eez-open/modular-psu/DIB/EEZ DIB v1.2 pin mappings.pdf

EEZ DIB (DIY Instrumentation Bus) pin mappings v1.2 (28.12.2020)

A B
1 | GND | | 2 | GND
3 | UART_RX | I | 4 | UART_TX | O
5 | +VAUX | I/O | 6 | NRESET | O
7 | +3V3 | O | 8 | NFAULT | I
9 | SPI3_IRQ | I #3 IRQ | 10 | SYNC | O
11 | SPI3_CSA | O | 12 | SSCL | O
13 | SPI3_CSB | O | 14 | SSDA | I/O
15 | GND | | 16 | GND
17 | SPI3_SCLK | O #3 SPI CLK | 18 | SPI3_MISO | I #3 MISO
19 | SPI2_IRQ | I #2 IRQ | 20 | SPI3_MOSI | O #3 MOSI
21 | SPI2_CSB | O | 22 | SPI2_CSA | O
23 | SPI2_SCLK | O #2 SPI CLK | 24 | SPI2_MISO | I #2 MISO
25 | SPI1_IRQ | I #1 IRQ | 26 | SPI2_MOSI | O #2 MOSI
27 | SPI1_CSB | O | 28 | SPI1_CSA | O
29 | GND | | 30 | SPI2_CSC | O
31 | SPI1_MISO | I #1 MISO | 32 | SPI1_SCLK | O #1 SPI CLK
33 | SPI1_MOSI | O #1 MOSI | 34 | SPI3_CSC | O
35 | +5V | I | 36 | +5V | I
37 | +12V | I | 38 | +12V | I
39 | GND | | 40 | GND

A B
1 | +3V3 | I | 2 | +VAUX | I
3 | NFAULT | I/O | 4 | NRESET | I
5 | SSCL | I | 6 | SYNC | I
7 | GND | | 8 | SSDA | I/O
9 | CSA | I | 10 | IRQ | O Module IRQ
11 | GND | | 12 | CSB | I
13 | SCLK | I Module SPI CLK | 14 | MISO | O Module MISO
15 | MOSI | I Module MOSI | 16 | GND
17 | A0 | I | 18 | A2 | I
19 | A1 | I | 20 | GND
21 | +12V | I | 22 | +12V | I
23 | +5V | I | 24 | +5V | I
25 | GND | | 26 | BOOT | I
27 | UART_RX** | O | 28 | UART_TX** | I

A B
1 | PE | | 2 | N.C. | O N.C.
3 | +12V | O | 4 | +12V | O
5 | +5V | O | 6 | +5V | O
7 | GND | | 8 | GND
9 | GND | | 10 | +VAUX | I/O
11 | PWR_SSTART | I | 12 | PWR_DIRECT | I
13 | SSCL | I | 14 | SSDA | I/O
15 | NFAULT | I/O | 16 | +3V3 | I

A B
1 | IN+ | I | 2 | IN+ | I
3 | IN+ | I | 4 | IN+ | I
5 | IN+ | I | 6 | OUT+ | O
7 | OUT+ | O | 8 | OUT+ | O
9 | OUT+ | O | 10 | OUT+ | O
11 | OUT- | O | 12 | OUT- | O
13 | OUT- | O | 14 | OUT- | O
15 | OUT- | O | 16 | IN- | I
17 | IN- | I | 18 | IN- | I
19 | IN- | I | 20 | IN- | I
MCU module (2 x 20-pin) | Status: Mandatory
Dir | Dir
Shared UART RX | Shared UART TX
Backup DC power | Master reset (active low)
DC power | Fault (active low)
| Sync output
#3 Chip select A | Shared I²C SCL

#3 Chip select B (#5 IRQ) | Shared I²C SDA

#2 Chip select B (#4 IRQ) | #2 Chip select A

#1 Chip select B | #1 Chip select A

| #2 Chip select C
| #3 Chip select C
DC power | DC power
DC power | DC power
Peripheral modules (2 x 14-pin) | Status: Mandatory
Dir | Dir
DC power | Backup DC power
Fault (active low) | Module reset (active low)
Shared I²C SCL | Sync input
| Shared I²C SDA
Module Chip select A
| Module Chip select B

I

2C Address 0 | I 2C Address 2
I

2C Address 1
DC power | DC power
DC power | DC power
| Module bootloader select
| Status: Optional*
Shared UART RX | Shared UART TX
AUX PS module (2 x 8-pin) | Status: Recommended
Dir | Dir
DC power | DC power
DC power | DC power
| Backup DC power
AC soft-start | AC power on
Shared I²C SCL | Shared I²C SDA
Fault (active low) | DC power
Power source module (2 x 10-pin) | Status: Optional
Dir | Dir
Power positive input | Power positive input
Power positive input | Power positive input
Power positive input | Power positive output
Power positive output | Power positive output
Power positive output | Power positive output
Power negative output | Power negative output
Power negative output | Power negative output
Power negative output | Power negative input
Power negative input | Power negative input
Power negative input | Power negative input

*) The first 26-pin of peripheral module connector is mandatory and last two pin are optional. New versions of DIB specification could introduce even more features but that will require also introduction of larger MCU connector or additional connector for the MCU
**) Connect module UART_RX to master MCU UART_TX and module UART_TX to master MCU UART_RX

EEZ DIB (DIY Instrumentation Bus) pin mappings v1.2 (28.12.2020)

A B
1 | | I | 2 | | I
3 | AIN- | O | 4 | AIN+ | O
5 | | I | 6 | | I
7 | ID0 | O ADIB module ID0 | 8 | ID2 | O ADIB module ID2
9 | ID1 | O ADIB module ID1 | 10 | | I

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
| ADIB (2 x 5-pin) | | Status: Optional
Dir | Dir
Guard- | AIN- guard | Guard+ | Power positive input
| Analog input- | | Analog Input+
Guard- | AIN- guard | Guard+ | Power positive output
| | ID_Gnd | Master ADIB Gnd
| ADIB module ID assignment
Module name
EEZ DIB SMX46 (https://www.envox.hr/eez/eez-bench-box-3/eez-dib-smx46-switch-matrix-module.html) | Switch matrix module
EEZ MUX14D (https://www.envox.hr/eez/eez-bench-box-3/dib-mux14d-multiplexer-module.html) | 2-wire dual 7:1 (14:1) Multiplexer
n/a
n/a
n/a
n/a
n/a
n/a
