eez-open/modular-psu/dcp405/Front panel/DCP405 front panel.pdf

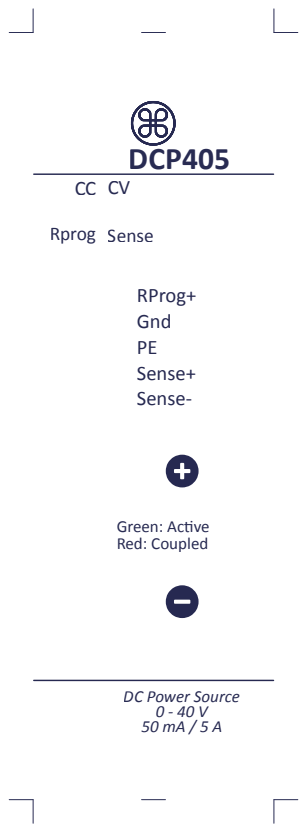
[picture p124: page 1]
RProg+ Gnd PE Sense+ Sense-; Rprog Sense; DC Power Source 0 - 40 V 50 mA / 5 A; DCP405

Green: Acve
Red: Coupled
