eez-open/modular-psu/dcp405/Front panel/DCP405B front panel.pdf

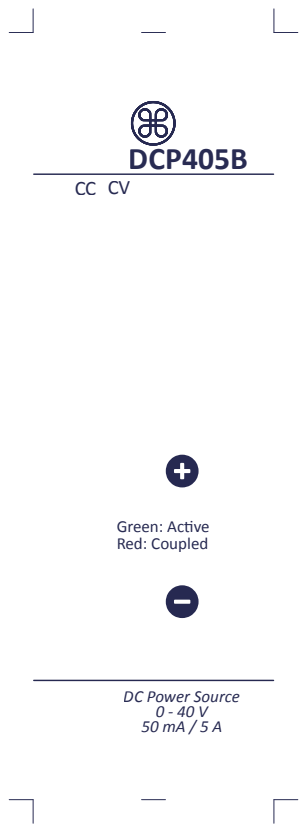
[picture p125: page 1]
DC Power Source 0 - 40 V 50 mA / 5 A; DCP405B

Green: Acve Red: Coupled
