eez-open/modular-psu/aux-ps/Images/AUX PS r3B7 3D preview.png

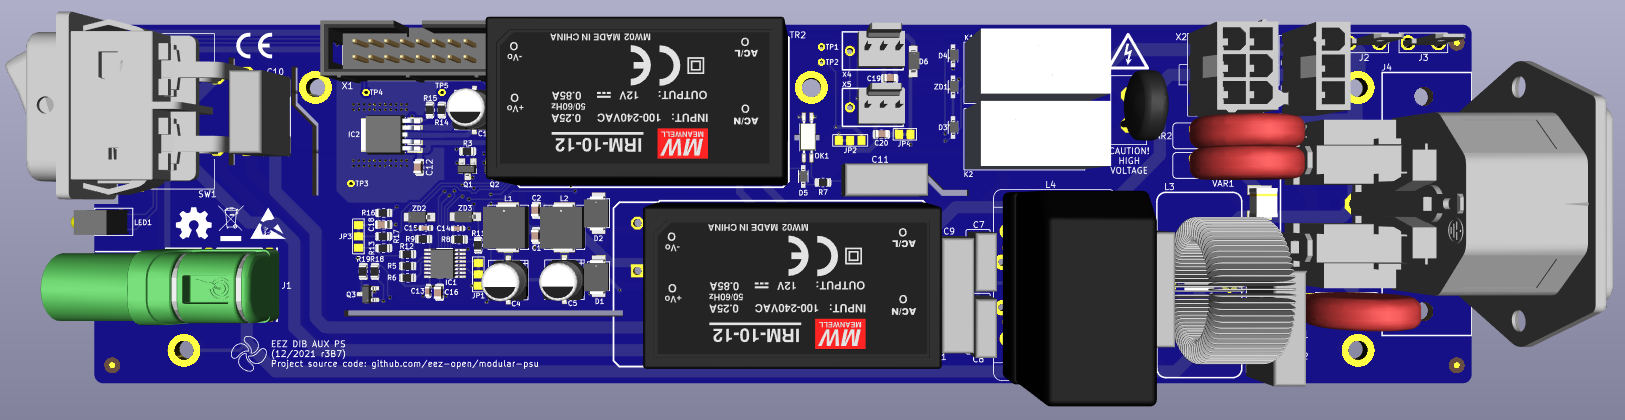
aux-ps/Images/AUX PS r3B7 3D preview.png
