eez-open/modular-psu/bp3c/EEZ DIB BP3C r2B3 Sheet2of2.png

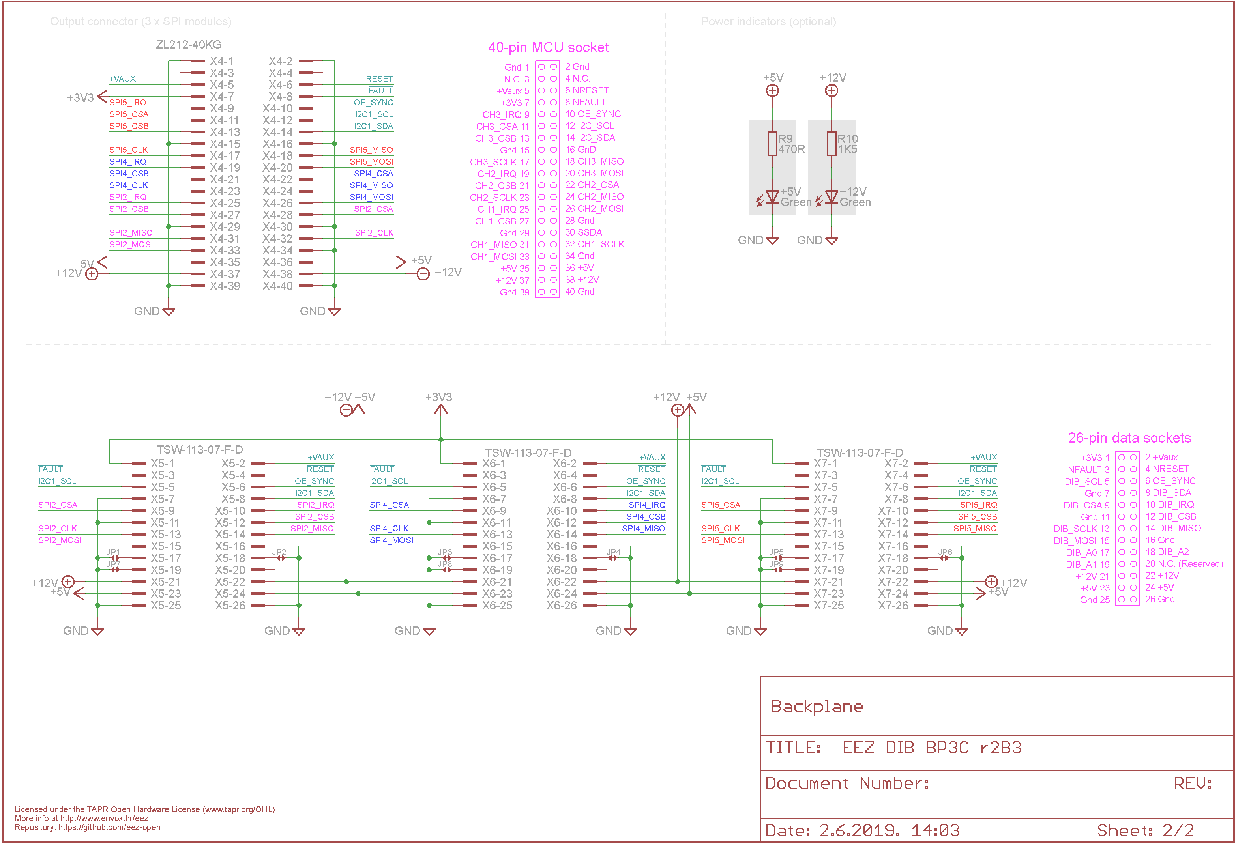
bp3c/EEZ DIB BP3C r2B3 Sheet2of2.png
