eez-open/modular-psu/bp3c/Images/BP3C r3B3 3D preview.png

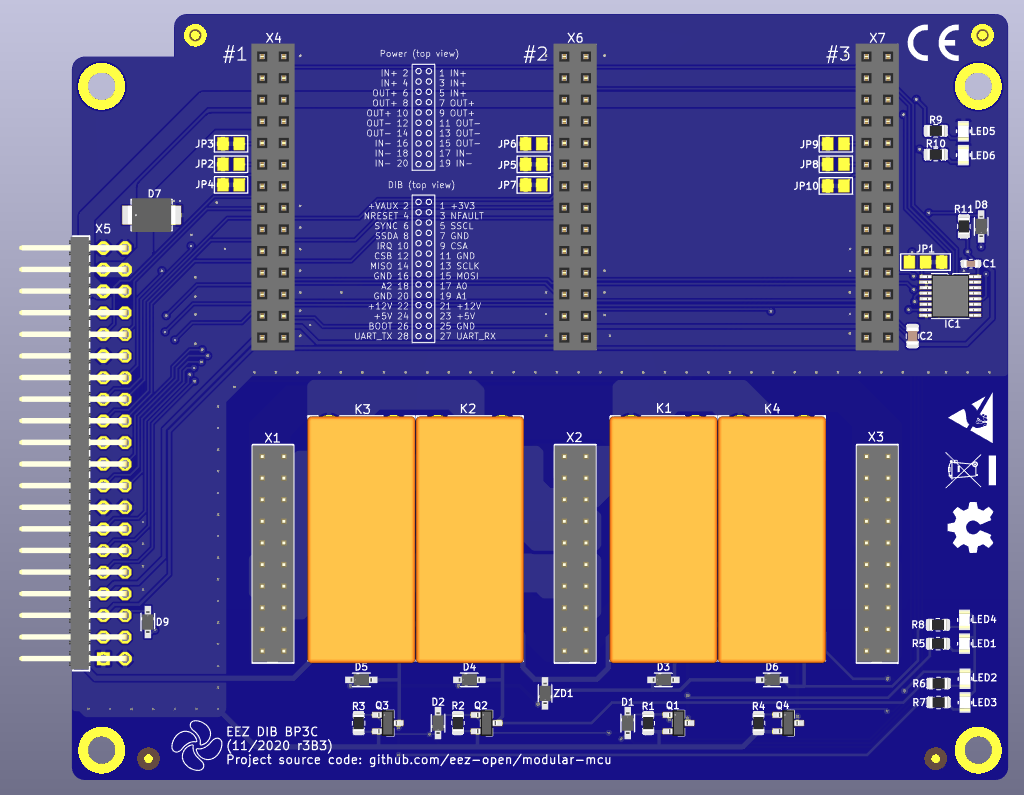
bp3c/Images/BP3C r3B3 3D preview.png
