eez-open/modular-psu/dcm220/Images/EEZ_DIB_DCM220_PCB_bottom.png

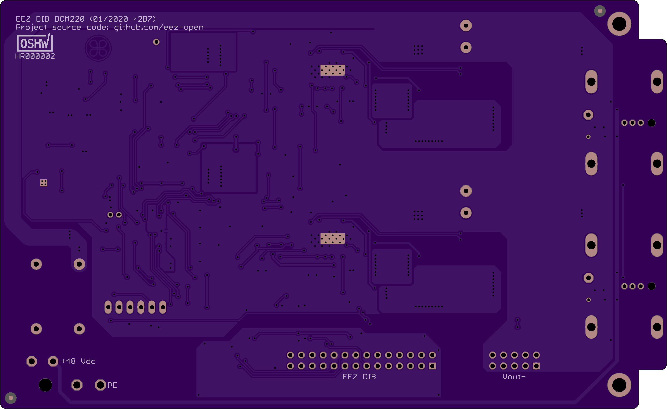
dcm220/Images/EEZ_DIB_DCM220_PCB_bottom.png
