eez-open/modular-psu/dcp405/EEZ DIB DCP405 r3B3 Sheet4of6.png

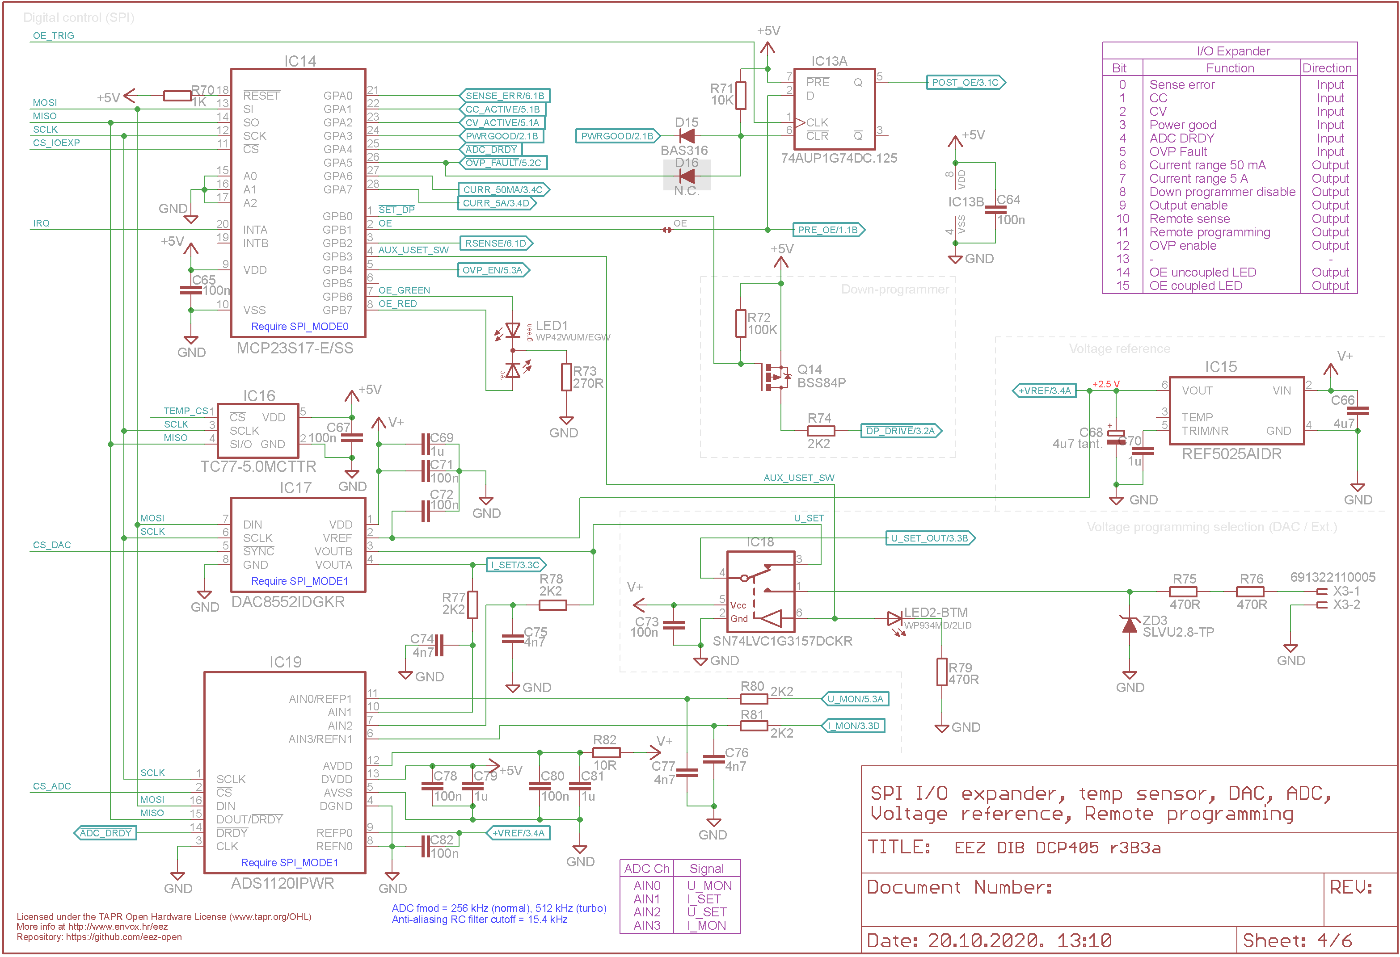
dcp405/EEZ DIB DCP405 r3B3 Sheet4of6.png
