eez-open/modular-psu/dcp405/Front panel/DCP405B front panel.png

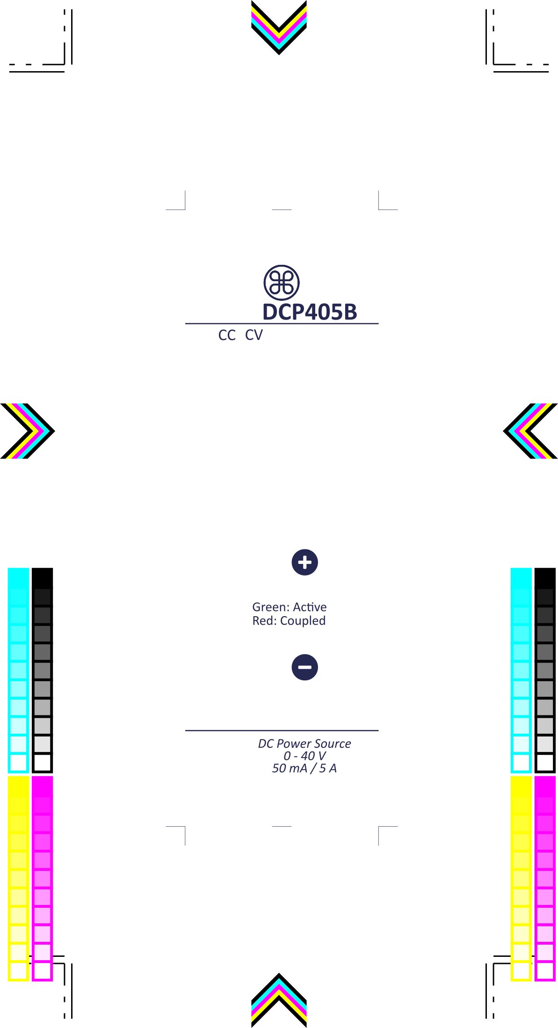
dcp405/Front panel/DCP405B front panel.png
