eez-open/modular-psu/dcp405/Images/EEZ_DIB_DCP405_PCB_bottom.png

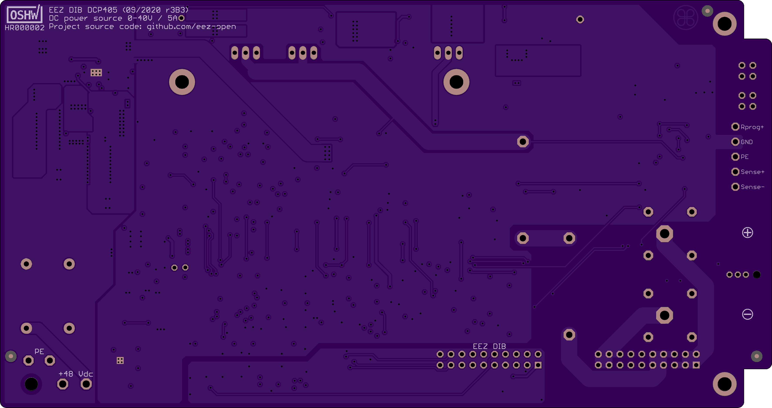
dcp405/Images/EEZ_DIB_DCP405_PCB_bottom.png
