eez-open/modular-psu/dcp405/Images/EEZ_DIB_DCP405_PCB_top.png

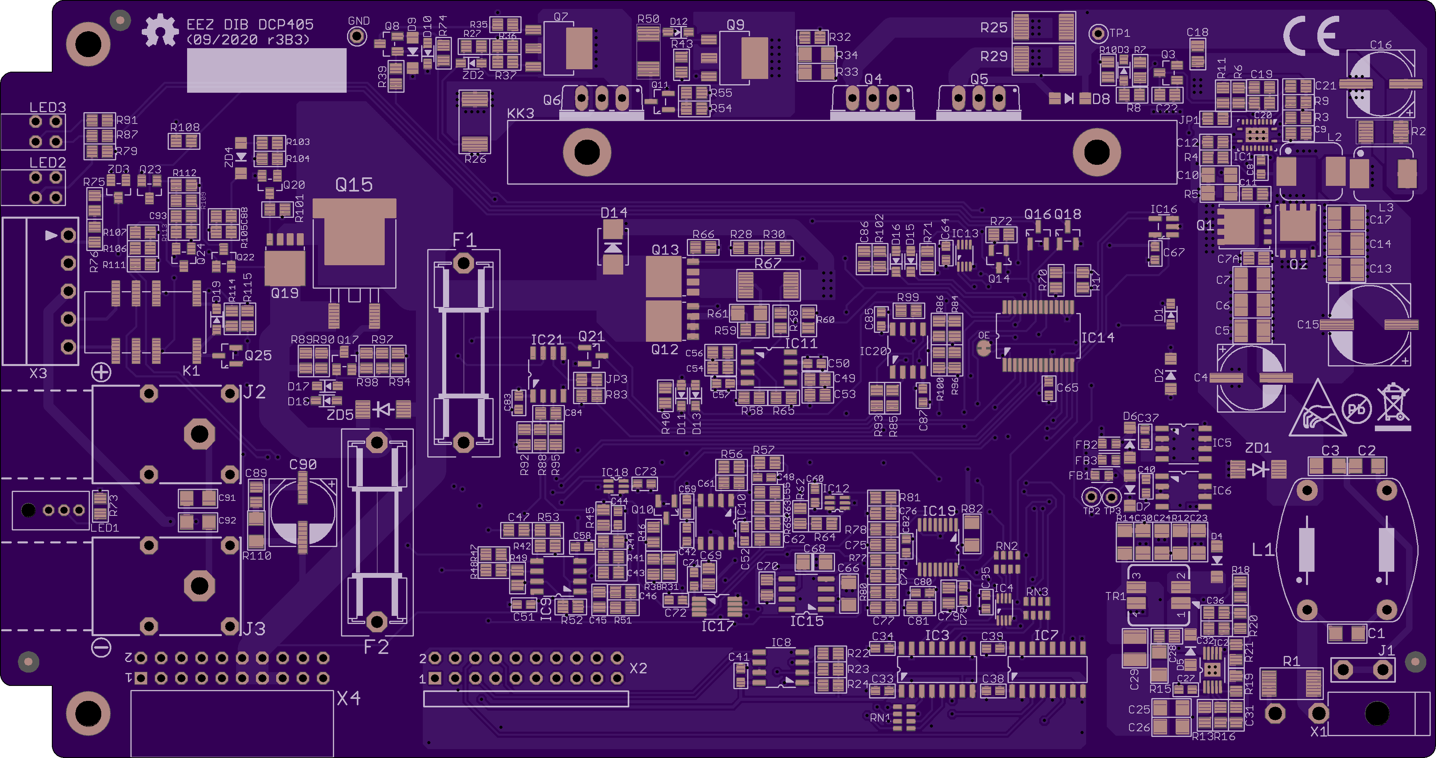
dcp405/Images/EEZ_DIB_DCP405_PCB_top.png
