eez-open/modular-psu/dcp405/Spice/EEZ DIB DCP405 r2B6.png

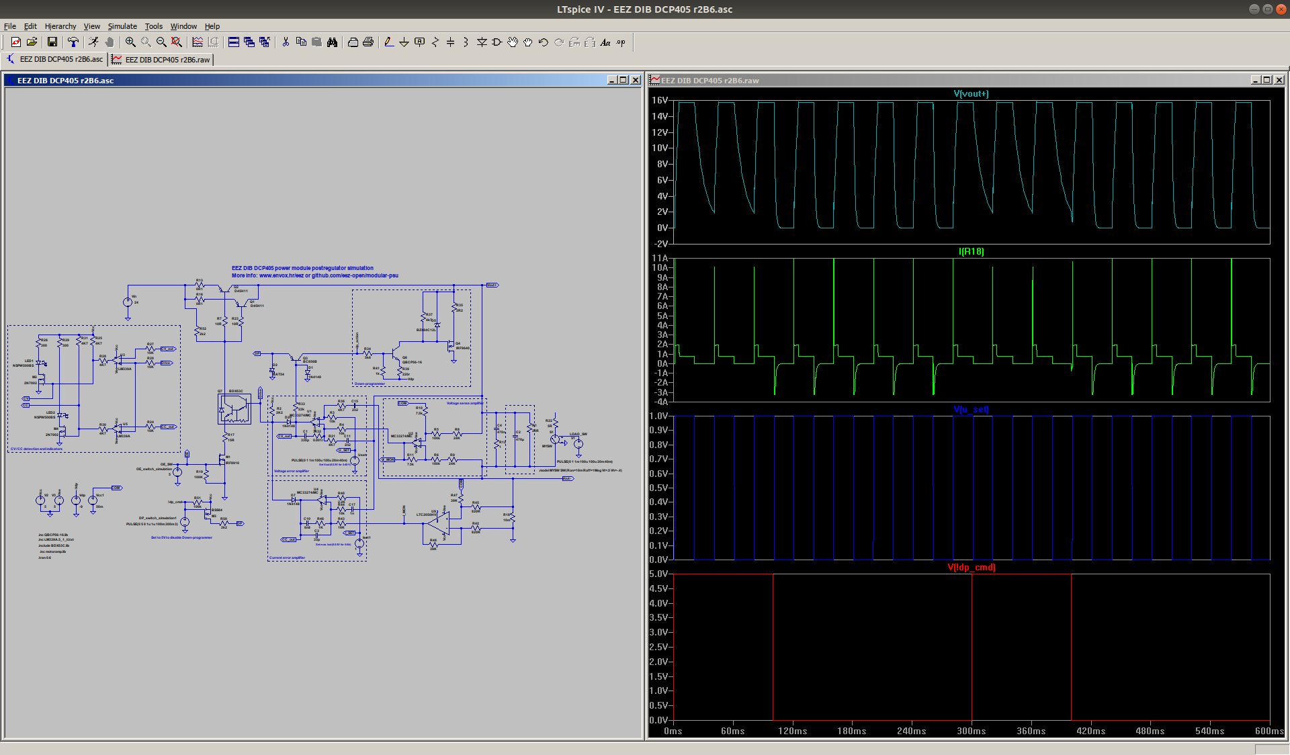
dcp405/Spice/EEZ DIB DCP405 r2B6.png
