eez-open/modular-psu/dcp505/EEZ DIB DCP505 r1B3 Sheet5of6.png

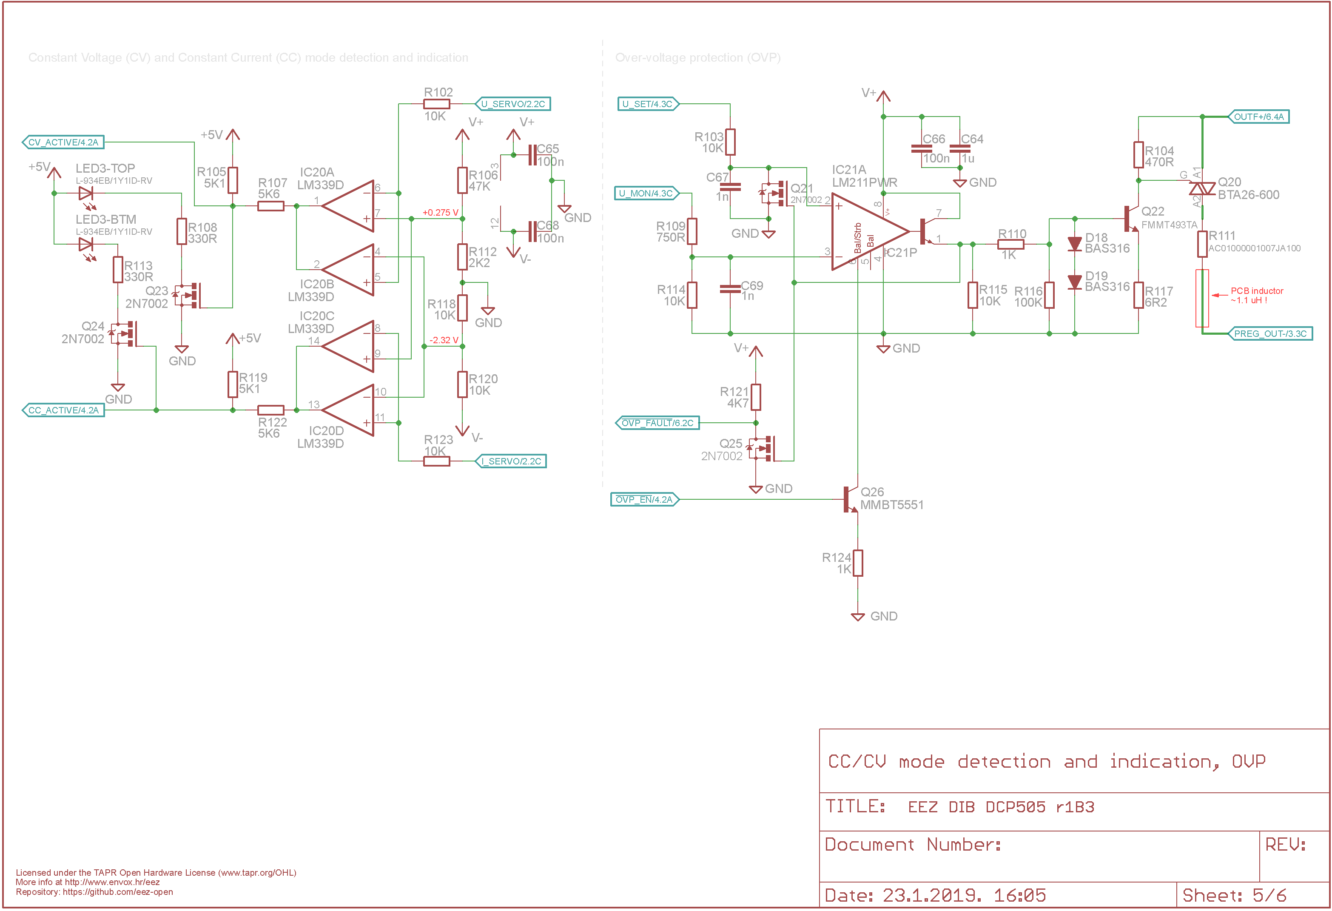
dcp505/EEZ DIB DCP505 r1B3 Sheet5of6.png
