eez-open/modular-psu/dcp505/Images/PCB inductor calculation.png

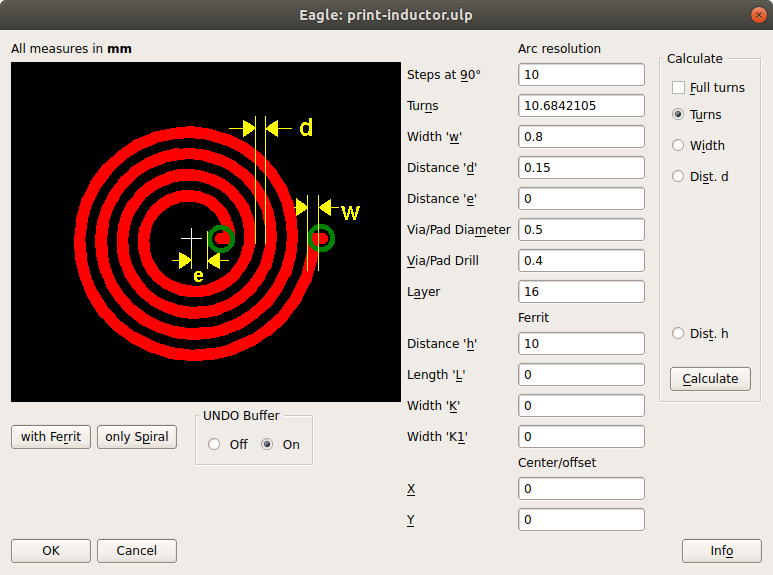
dcp505/Images/PCB inductor calculation.png
