eez-open/modular-psu/dcp505/Spice/OVP/OVP max current simulation.png

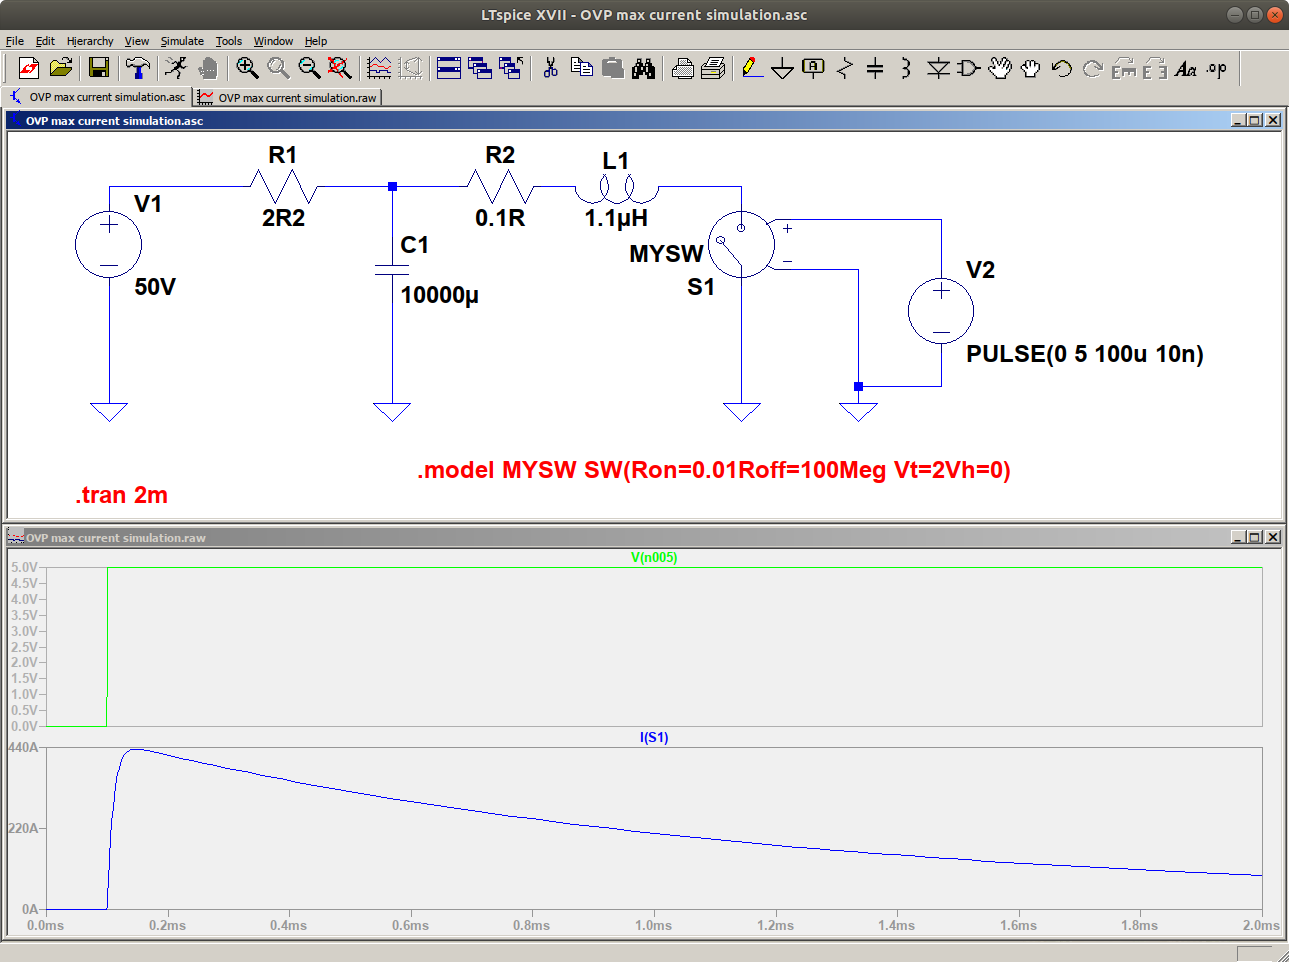
dcp505/Spice/OVP/OVP max current simulation.png
