eez-open/modular-psu/DIB/EEZ DIB v1.0 backplane dimensions.png

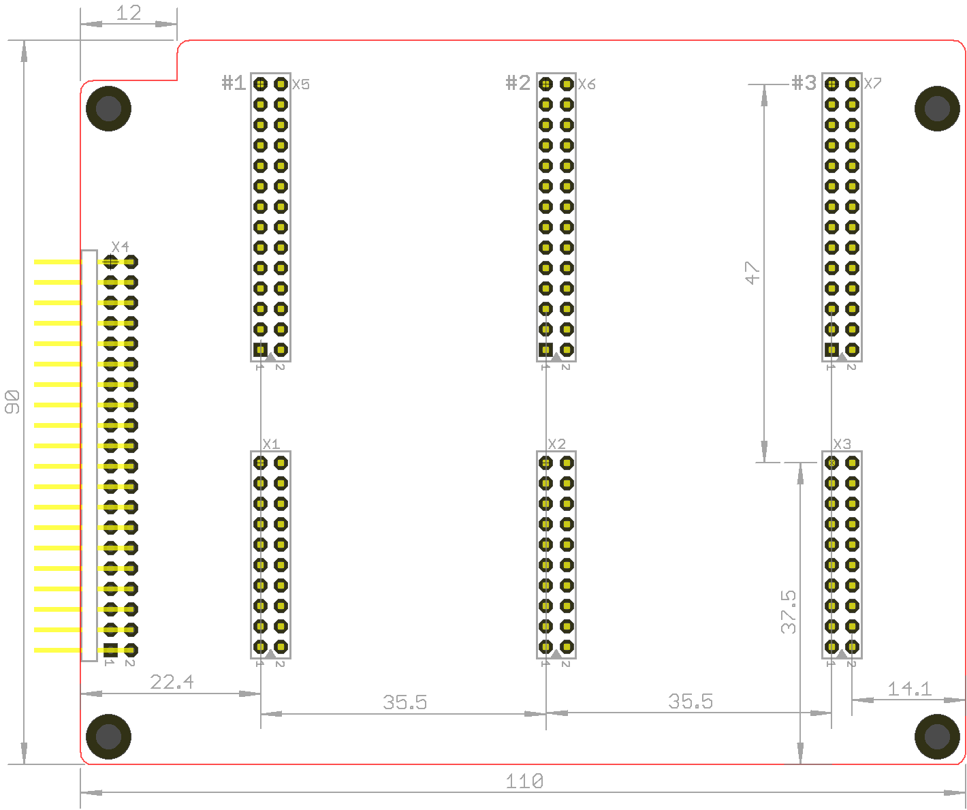
DIB/EEZ DIB v1.0 backplane dimensions.png
