eez-open/modular-psu/enclosure/BB3 chassis Mean Well support 2.0.png

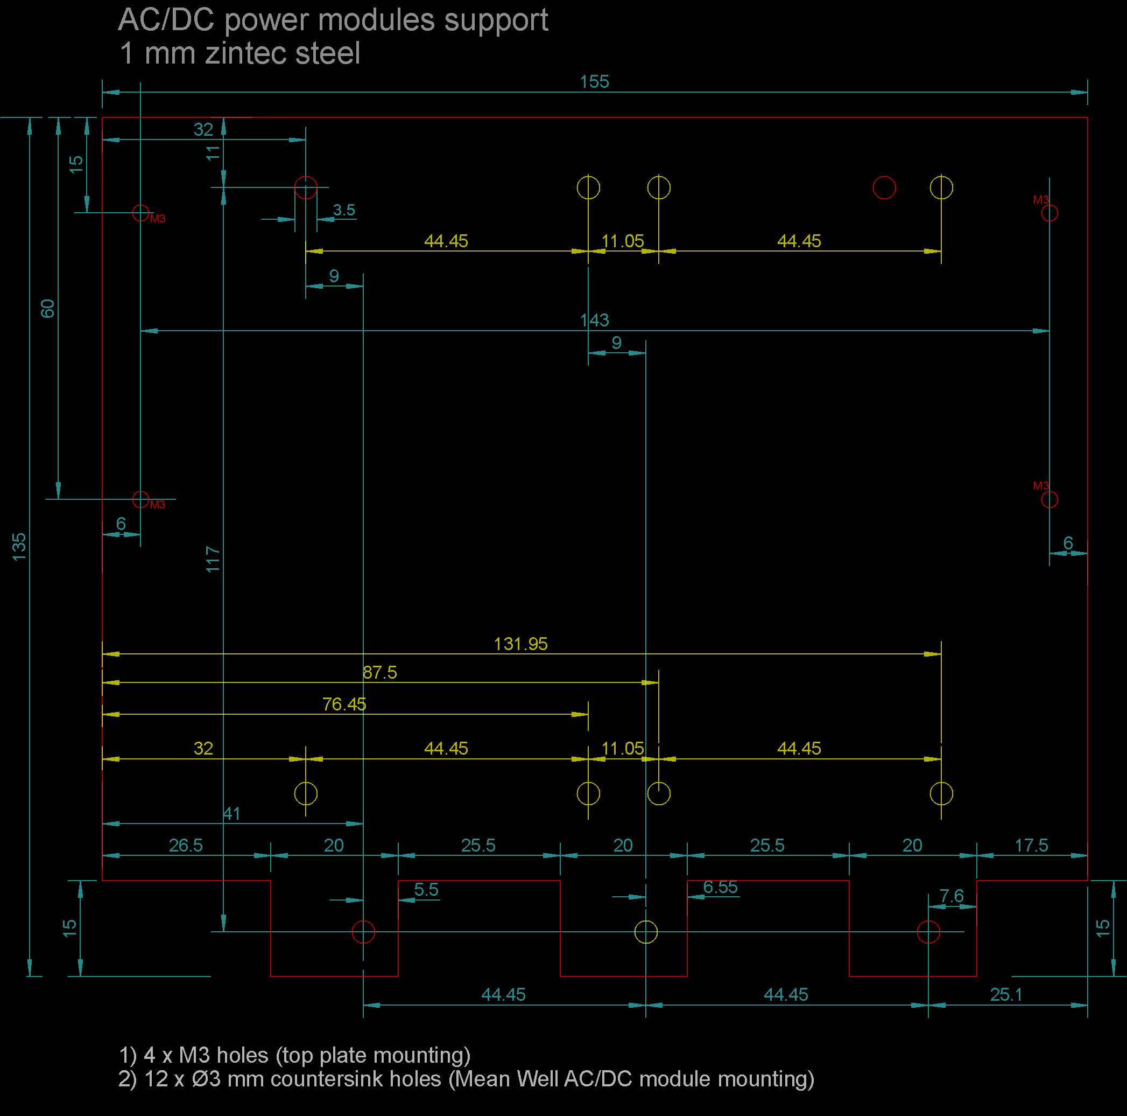
enclosure/BB3 chassis Mean Well support 2.0.png
