eez-open/modular-psu/enclosure/EEZ BB3 chassis bottom plate r2B1.png

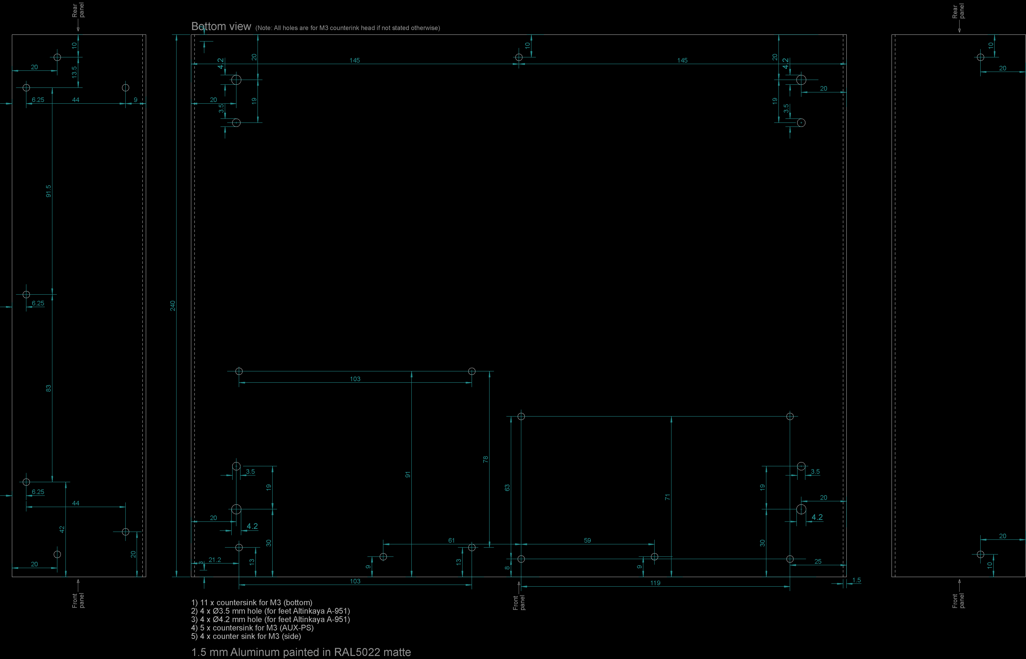
enclosure/EEZ BB3 chassis bottom plate r2B1.png
