eez-open/modular-psu/enclosure/EEZ BB3 chassis display support r2B1.png

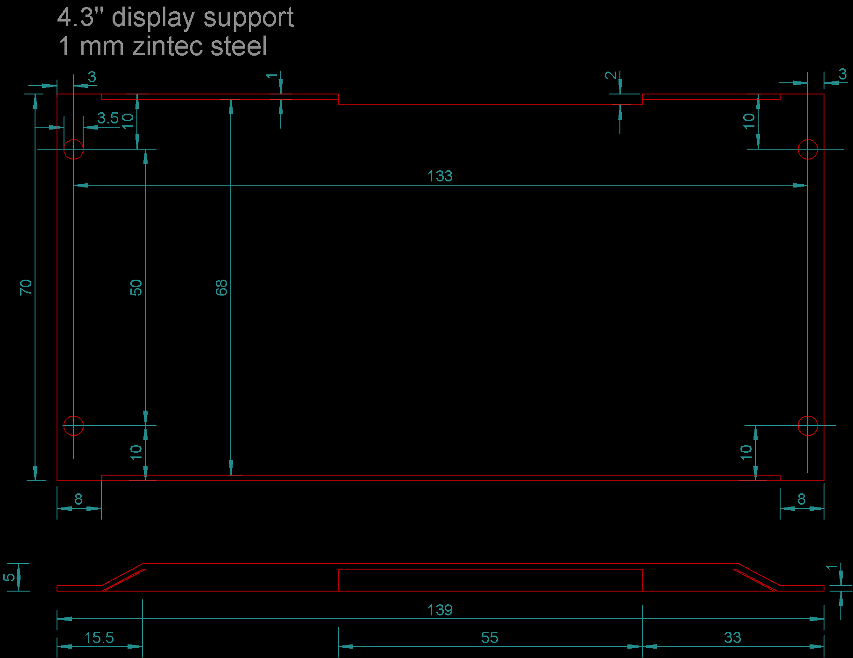
enclosure/EEZ BB3 chassis display support r2B1.png
