eez-open/modular-psu/enclosure/EEZ BB3 chassis front panel r2B1.png

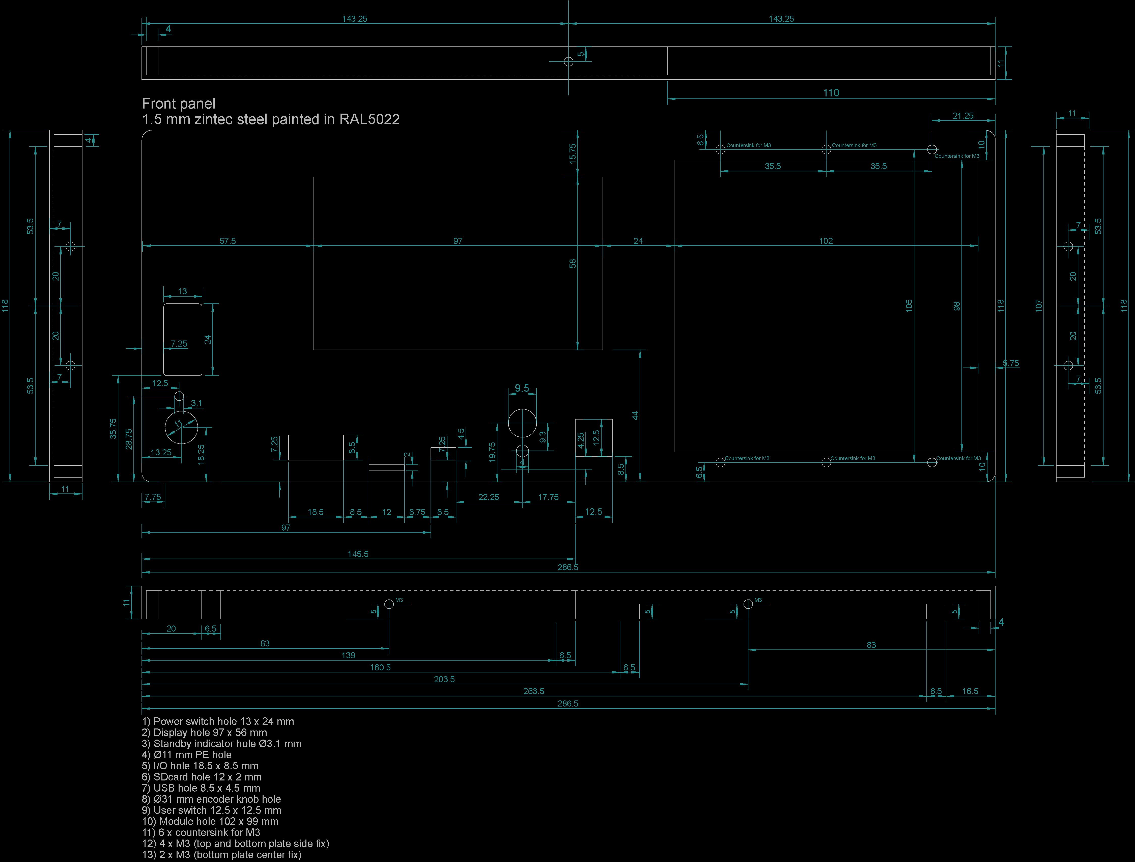
enclosure/EEZ BB3 chassis front panel r2B1.png
