eez-open/modular-psu/enclosure/EEZ BB3 chassis module panels.png

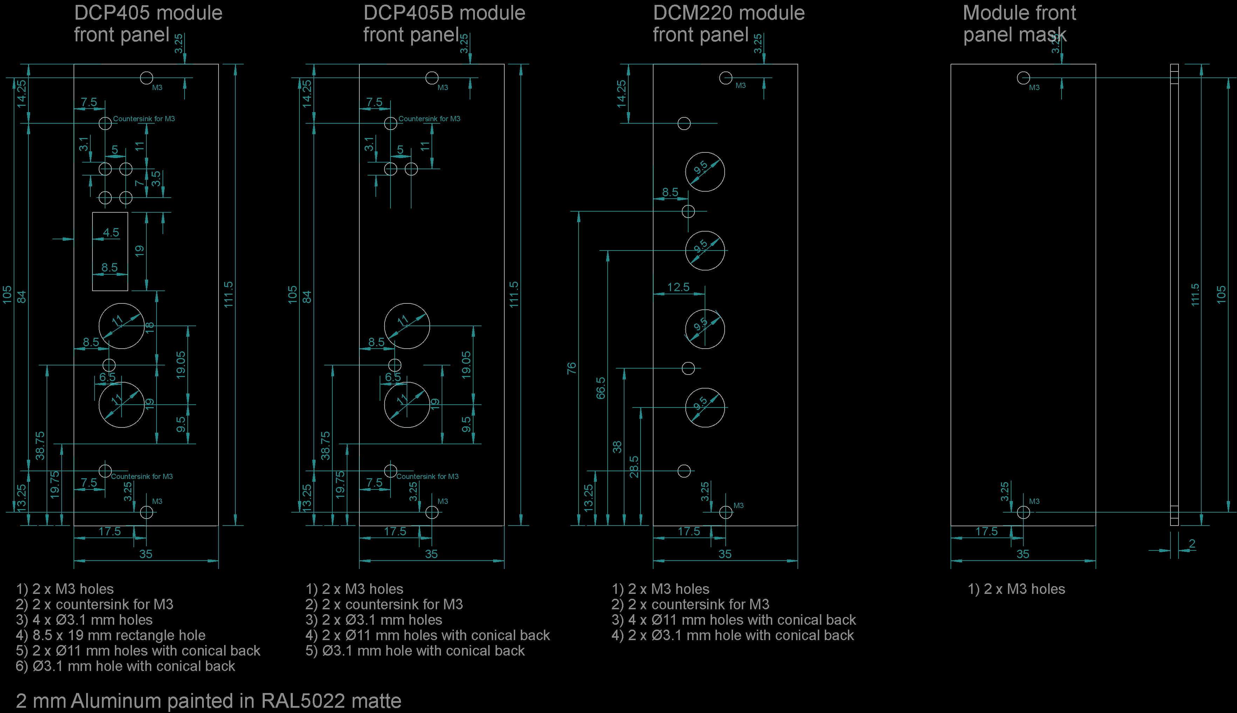
enclosure/EEZ BB3 chassis module panels.png
