eez-open/modular-psu/enclosure/EEZ BB3 module front panel template.png

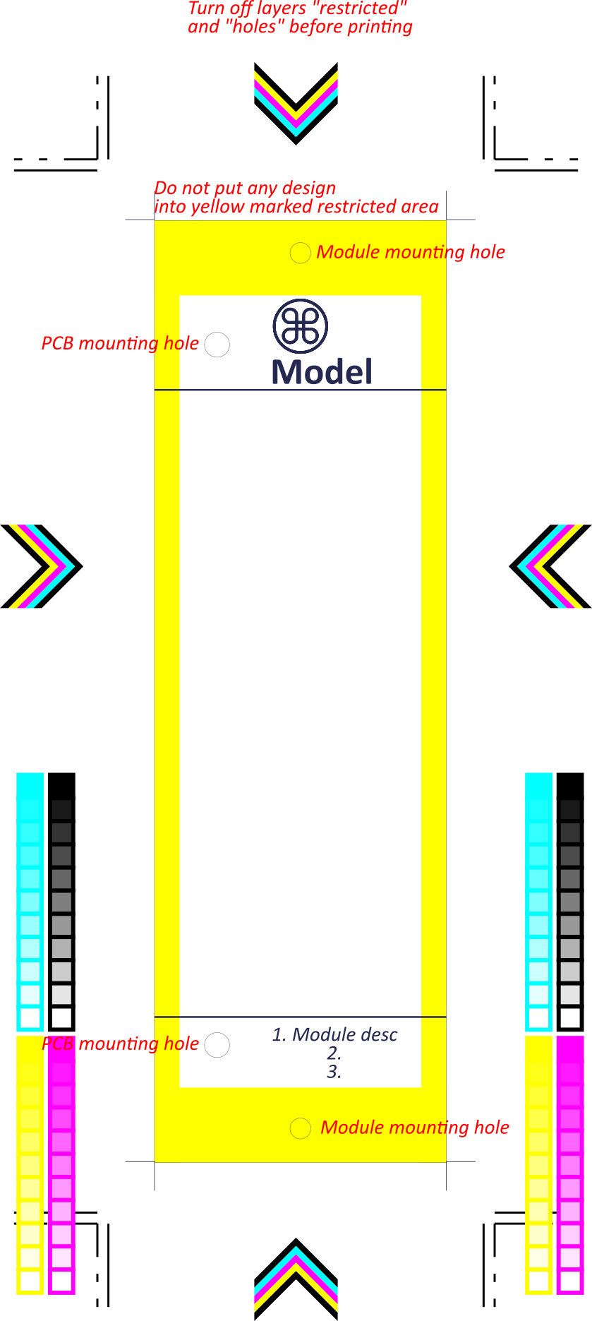
enclosure/EEZ BB3 module front panel template.png
