eez-open/modular-psu/mcu/EEZ DIB MCU r3B4 Sheet1of5.png

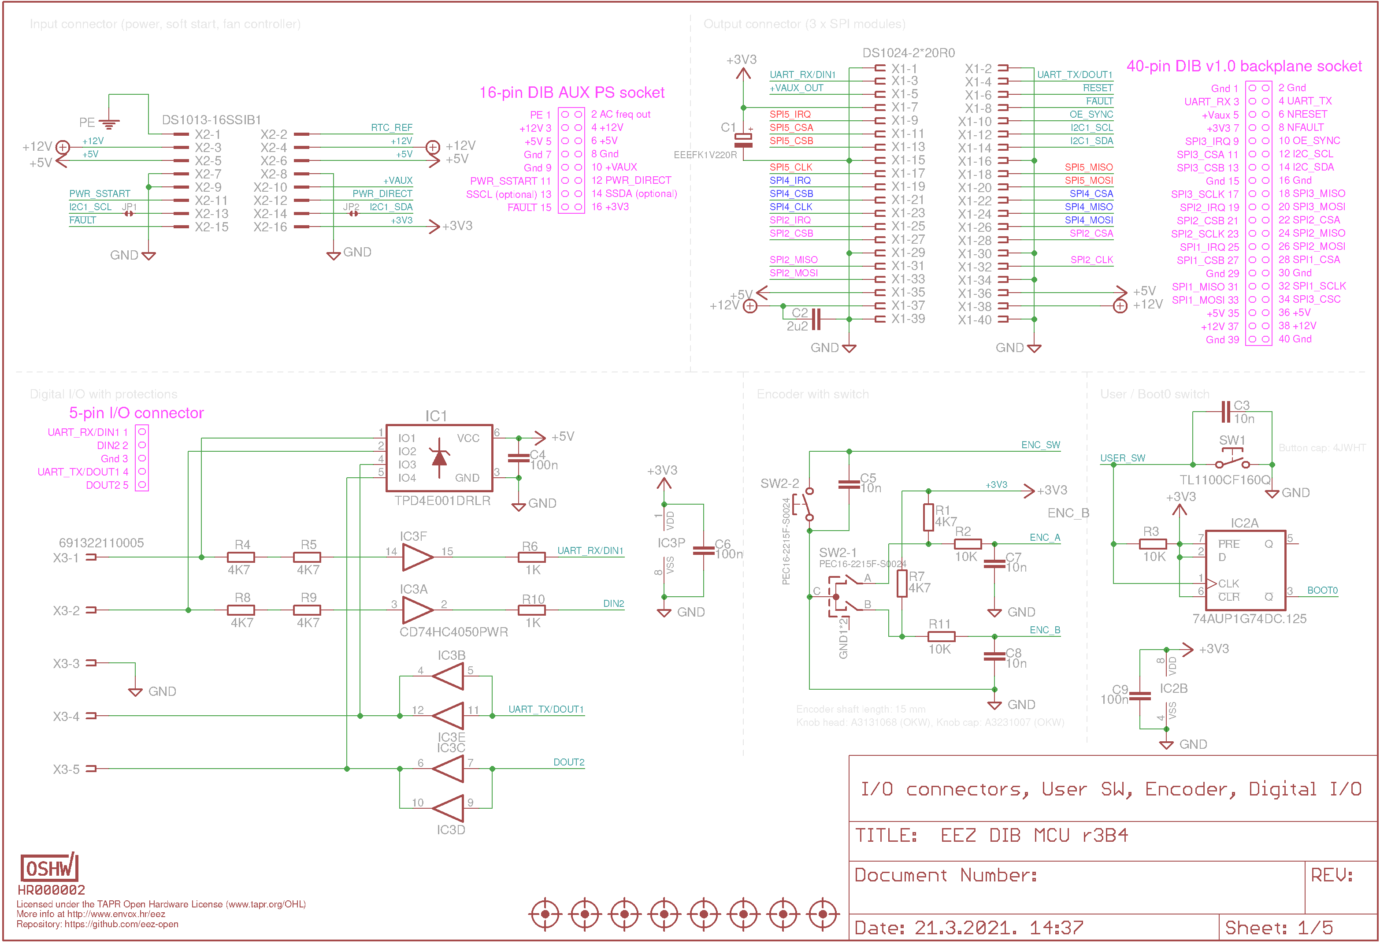
mcu/EEZ DIB MCU r3B4 Sheet1of5.png
