eez-open/modular-psu/mcu/EEZ DIB MCU r3B4 Sheet3of5.png

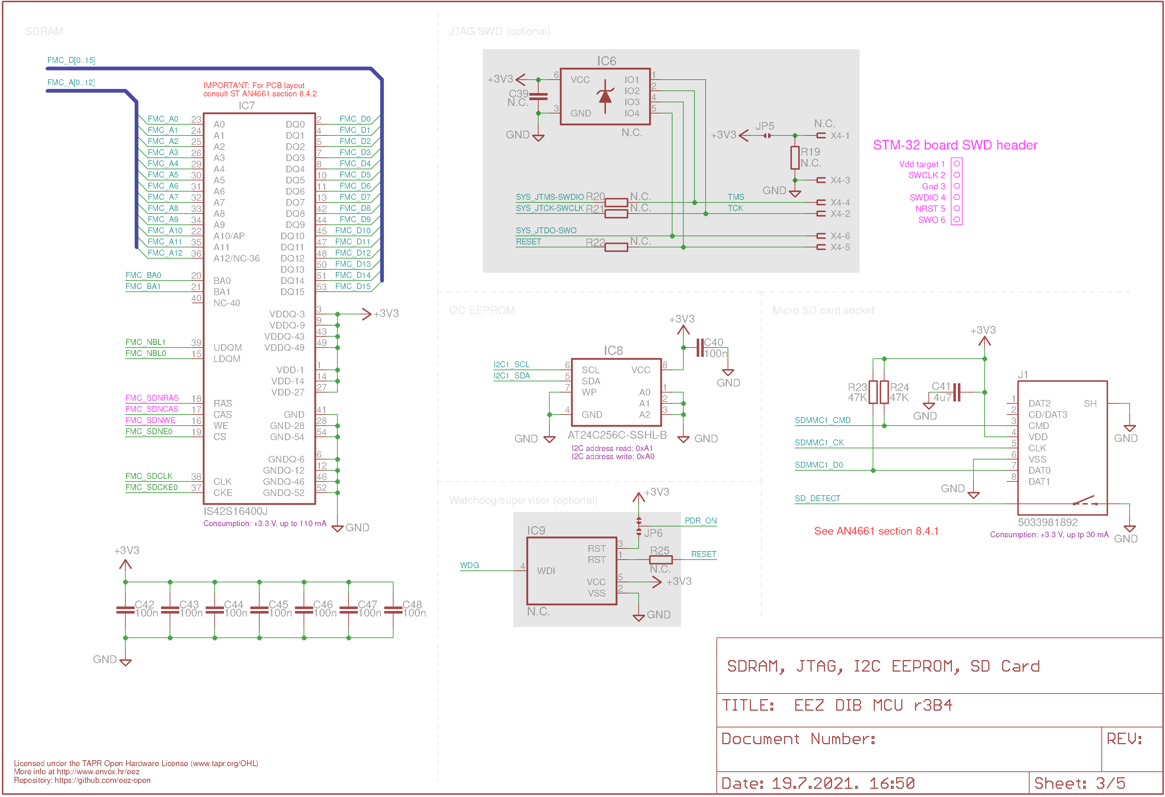
mcu/EEZ DIB MCU r3B4 Sheet3of5.png
