eez-open/modular-psu/mcu/Images/EEZ_DIB_MCU_PCB_bottom.png

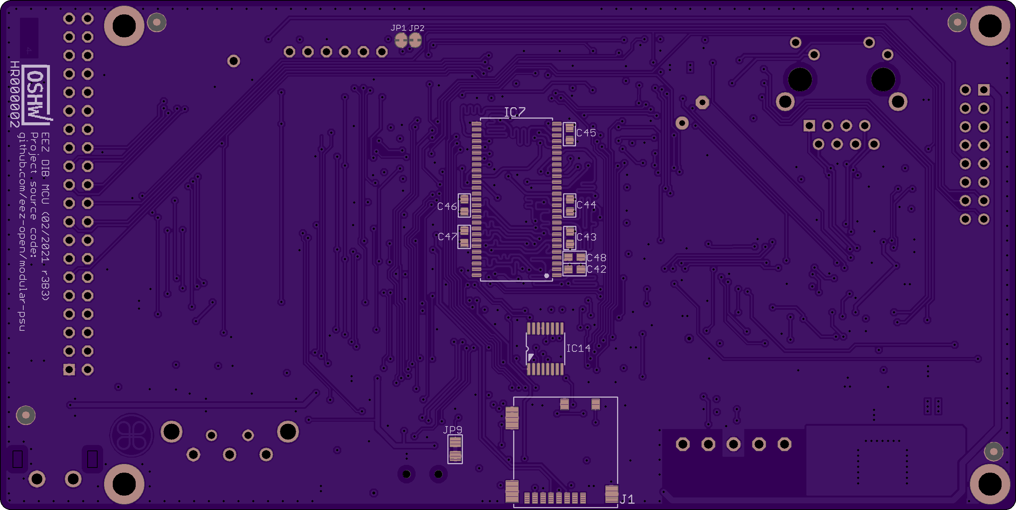
mcu/Images/EEZ_DIB_MCU_PCB_bottom.png
