eez-open/modular-psu/mcu/Images/EEZ_DIB_MCU_PCB_top.png

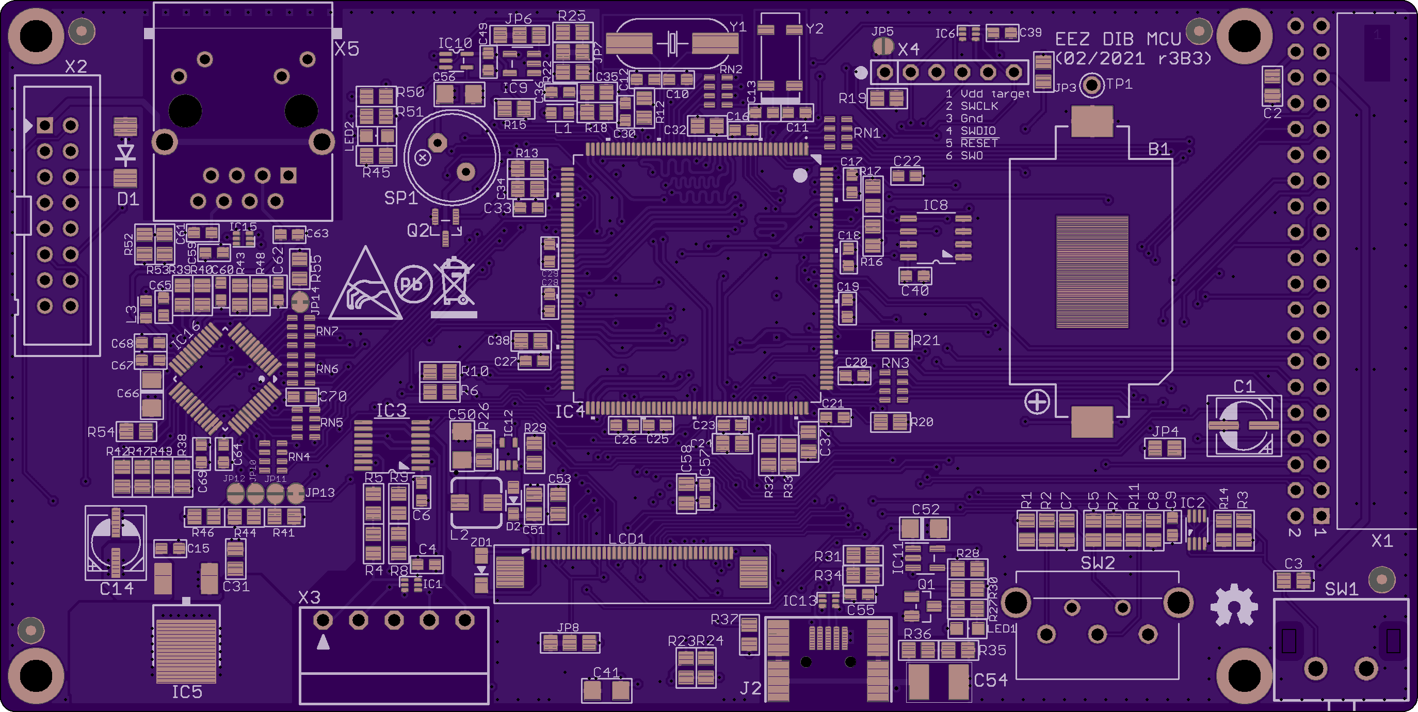
mcu/Images/EEZ_DIB_MCU_PCB_top.png
