eez-open/modular-psu/PRELIMINARY/DCP405 r4 (with MCU)/EEZ DIB DCP405 r4B2 Sheet1of6.png

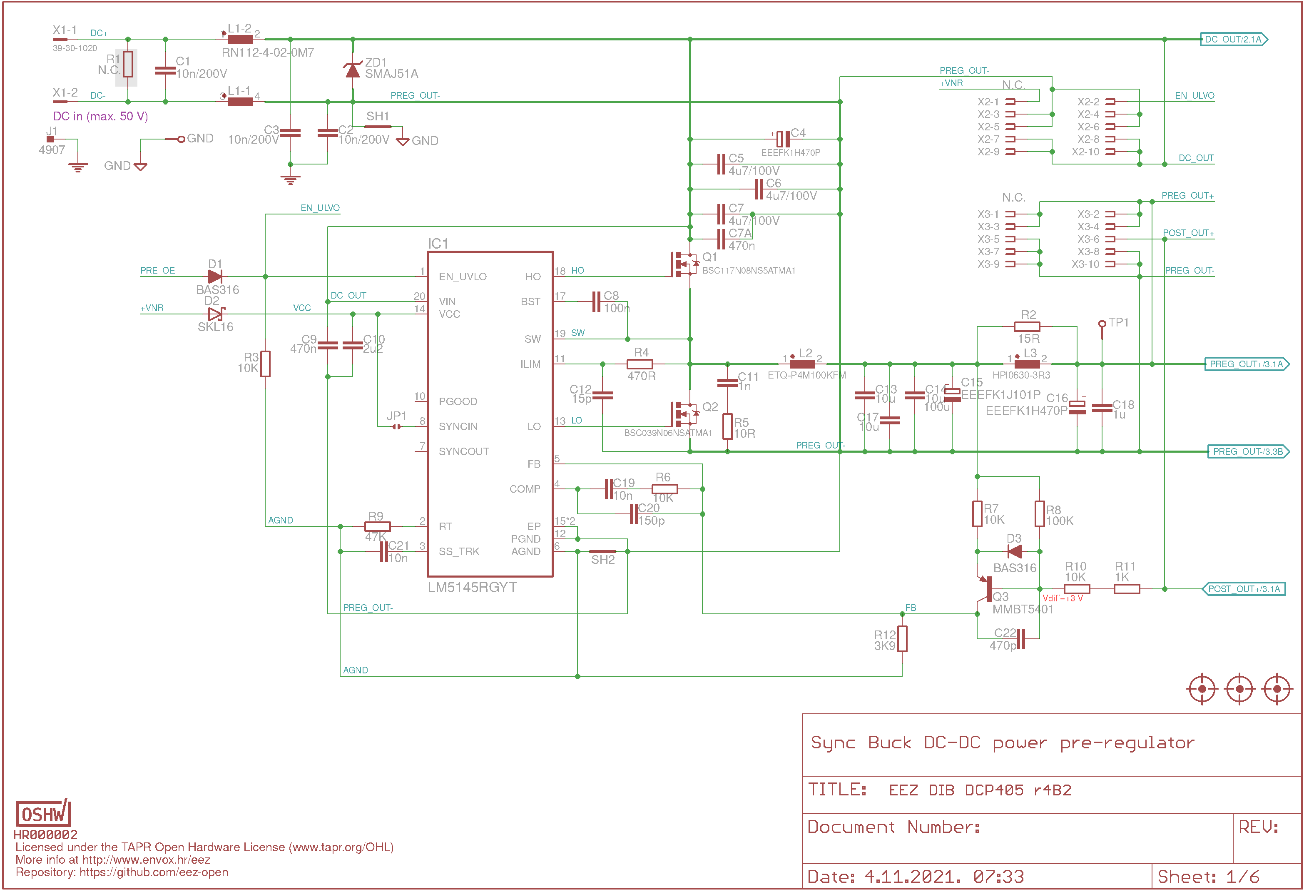
PRELIMINARY/DCP405 r4 (with MCU)/EEZ DIB DCP405 r4B2 Sheet1of6.png
