eez-open/modular-psu/PRELIMINARY/DCP405 r4 (with MCU)/Images/EEZ_DIB_DCP_bottom_layer.png

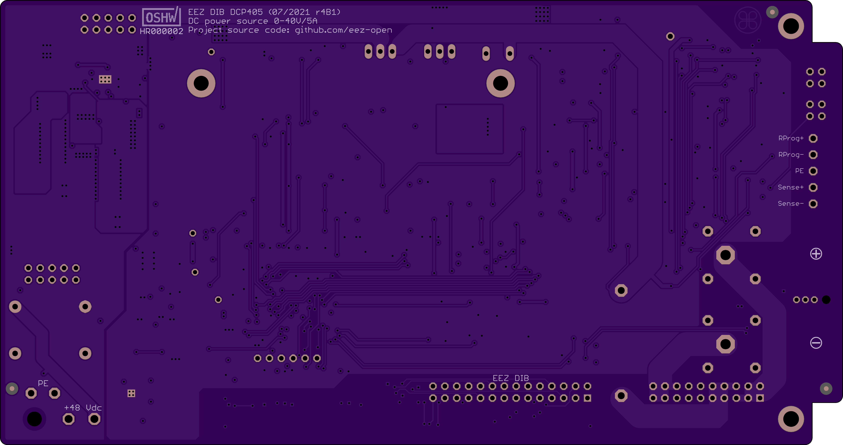
PRELIMINARY/DCP405 r4 (with MCU)/Images/EEZ_DIB_DCP_bottom_layer.png
