eez-open/modular-psu/mcu/BOM/EEZ DIB MCU r3B4 BOM.pdf

EEZ DIB MCU BOM (r3B4, 2021-09-25) Project source code at https://github.com/eez-open/modular-psu

| Farnell / Element14 | | Digi-Key | | Mouser
Qty | Part name | Package

Reference designator
Code | Part Number | MOQ | Part Number | MOQ | Part Number | MOQ
1 | 1 | DS1092-10-W6L | CR2032 cell battery holder | B1 | - | 732-12325-1-ND | 1,690 | 1 | 710-79527141 | 1,680 | 1
2 | 2 | EEEFK1V220R | Ø5 x 5.8 mm | C1, C14
3 | 2 | 18p | 0603, C0G | C10, C12 | 2896373 | 0,016 | 10 | 1276-1089-1-ND | 0,048 | 10 | 0,023 | 10
4 | 2 | 4p7 | 0603, C0G | 2627469 | 0,329 | 10 | 311-1740-1-ND | 0,054 | 10 | 0,072 | 10
5 | 6 | 2u2 | 0805 | C2, C31, C32, C37, C38, C53 1828829 | 0,198 | 5 | 1276-2954-1-ND | 0,085 | 10 | 0,078 | 10
6 | 5 | 1u | C24, C34, C35, C51, C58 | 2495193 | 885012207078 | 0,139 | 5 | 1276-1066-1-ND | 0,070 | 10 | 0,050 | 10
7 | 4 | 10n | 0805 | C3, C5, C7, C8 | 2896555 | 0,065 | 10 | 490-7194-1-ND | 0,017 | 10 | 0,036 | 10
8 | 41 | 100n | 0603 | 2522597 | 0,073 | 10 | 490-4774-1-ND | 0,090 | 100 | 0,085 | 100
9 | 3 | 4u7 | 1206 | C41, C50, C56 | 1907356 | 0,282 | 5 | 1276-2970-1-ND | 0,199 | 10 | 0,129 | 10
10 | 1 | 4u7/6.3V | 1206, Tant. | C52 | 2321209 | T491A475K006AT | 0,421 | 5 | 399-9717-1-ND | 0,259 | 10 | 0,184 | 10
11 | 1 | 4n7/1kV | 1812 | C54 | 2812609 | 885342211001 | 1,120 | 1 | 732-12143-1-ND | 0,660 | 10 | 0,497 | 1
12 | 1 | 10u | 1206, Tant. | C66 | 1457412 | T491A106K006AT | 0,259 | 5 | 399-3683-1-ND | 0,238 | 10 | 0,173 | 10
13 | 1 | SMBJ5.0A-TR | DO-214AA | D1 | 2353654 | SMBJ5.0ATR | 0,232 | 5 | 497-3144-1-ND | 0,263 | 10 | 511-SMBJ5.0A | 0,306 | 1
14 | 1 | RB751V40T1G | | D2 | 1459171 | RB751V40T1G | 0,143 | 5 | | 0,192 | 10 | | 0,146 | 10
15 | 2 | TPD4E001DRLR | SOT-5X3 (SOT-563) | IC1, IC13 | 1611469 | TPD4E001DRLR | 0,453 | 5 | 296-21887-1-ND | 0,590 | 1 | 0,536 | 1
16 | 1 | TPS2051BDBVR | SOT-23-5 | IC11 | 2296067 | TPS2051BDBVR | 1,080 | 1 | 296-21265-1-ND | 1,280 | 1 | 1,220 | 1
17 | 1 | TPS61169DCKR | SC-70-5 | IC12 | 2542731 | TPS61169DCKR | 0,661 | 1 | 296-40821-1-ND | 0,790 | 1 | 0,770 | 1
18 | 1 | TSC2007IPW | TSSOP-16 | IC14 | 2769429 | TSC2007IPWR | 1,700 | 1 | 296-27124-1-ND | 2,110 | 1 | 2,040 | 1
19 | 1 | DP83848CVV/NOPB | LQFP-48 | IC16 | 1685784 | 4,850 | 1 | 4,280 | 1 | 4,260 | 1

Unit price
€

Unit price
€

Unit price
€

VJ0603A180JXAC
W1BC
| 80-C0603C180J5G7 867
C11, C13 MC0603N4R7C500 CT | | 710-885012006049
| | 80-C0805C225M4R ECLR
0805, C48 must be 25 V or more | | 963-TMK212B7105K G-T
| | 710-885012207122
C4, C6, C9, C15, C16, C17, C0603C104K4RAC C18, C19, C20, C21, C22, 7081 C23, C25, C26, C27, C28, C29, C30, C33, C36, C40, C42, C43, C44, C45, C46, C47, C48, C55, C57, C60, C61, C62, C63, C64, C65, C67, C68, C69, C70, C71 | | 80-C0603C104M4R
| | 963-EMK316B7475M L-T
| | 80-T491A475K006A T
| | 791-1812B472K102C T
| | 80-T491A106K0067 280

GRM21BR71C225
KA12L

VJ0805Y103JXXP
W1BC

C3216X7R1E475K
160AC
SOD-323, low capacitance switching diode | RB751V40T1GO SCT-ND | 863-RB751V40T1G
| | 595-TPD4E001DRLR
| | 595-TPS2051BDBVR
| | 595-TPS61169DCKR
| | 595-TSC2007IPWR

DP83848CVV/
NOPB

DP83848CVV/
NOPB-ND

926-
DP83848CVV/
NOPB

# Qty Part name | RS Components | TME | Price calculation for 1 set

Unit price Code Part Number MOQ € | Unit price Code / Part Number MOQ € | THT SMD | | Line Cost €
1 | 1 | DS1092-10-W6L
2 | 2 | EEEFK1V220R
3 | 2 | 18p
4 | 2 | 4p7
5 | 6 | 2u2
6 | 5 | 1u
7 | 4 | 10n
8 | 41 | 100n
9 | 3 | 4u7
10 | 1 | 4u7/6.3V
11 | 1 | 4n7/1kV
12 | 1 | 10u
13 | 1 | SMBJ5.0A-TR
14 | 1 | RB751V40T1G
15 | 2 | TPD4E001DRLR
16 | 1 | TPS2051BDBVR
17 | 1 | TPS61169DCKR
18 | 1 | TSC2007IPW
19 | 1 | DP83848CVV/NOPB
184-2347 | 79527141 | 1,800 | 5 | DS1092-10-W6L | 0,296 | 10 | 1 | TME | 0,296 € | 1 | 0,296
| | | | EEEFK1V220R | 0,156 | 5 | 2 | TME | 0,156 € | 2 | 0,311
147-415 | 0,032 | 50 | CL10C180JB8NNNC | 0,015 100 | 2 | TME | 0,015 € | 2 | 0,030
298-9315 | 0,024 | 25 | CL10C4R7CB8NNNC | 0,024 100 | 2 | RS | 0,024 € | 2 | 0,048
766-1031 | 0,069 100 | CL21B225KOFNNNG | 0,071 100 | 6 | RS | 0,069 € | 6 | 0,414
378-665 | 0,038 | 25 | 0,014 100 | 5 | TME | 0,014 € | 5 | 0,072
464-6672 | 0,026 | 50 | CC0805KRX7R9103 | 0,027 100 | 4 | Digikey | 0,017 € | 4 | 0,068
264-4630 | 0,035 | 25 | CL10B104KA8NNNC | 0,098 100 | 41 | RS | 0,035 € | 41 | 1,435
691-1221 | 0,232 | 25 | 0,381 | 10 | 3 | Mouser | 0,129 € | 3 | 0,387
538-2335 | 0,337 | 10 | T491A475K006AT | 0,094 | 10 | 1 | TME | 0,094 € | 1 | 0,094
135-5684 | 0,706 | 20 | 1812B472K202CT | 0,237 | 10 | 1 | TME | 0,237 € | 1 | 0,237
136-2614 | F930J106MA | 0,182 | 25 | T491A106K006AT | 0,069 | 25 | 1 | TME | 0,069 € | 1 | 0,069
714-7210 | SMBJ5.0A-TR | 0,268 | 25 | SMBJ5.0A-TR | 0,114 | 5 | 1 | TME | 0,114 € | 1 | 0,114
690-0022 | RB751V40T1G | 0,137 | 25 | RB751V40T1G | 0,036 | 25 | 1 | TME | 0,036 € | 1 | 0,036
709-9066 | 0,552 | 5 | - | 2 | Farnell | 0,453 € | 3 | 1,359
662-2384 | TPS2051BDBVT | 1,284 | 5 | - | 1 | Farnell | 1,080 € | 1 | 1,080
- | - | 1 | Farnell | 0,661 € | 1 | 0,661
661-3545 | TSC2007IPW | 2,340 | 1 | - | 1 | 1 | Farnell | 1,700 € | 1 | 1,700
651-5738 | 4,310 | 1 | DP83848CVV/NOPB | 3,000 | 1 | 1 | TME | 3,000 € | 1 | 3,000

Best
Supplier

Lowest
unit price
€

Order
Qty

C0603C180J5G
ACTU

C0603C479C5G
ACTU

CL21B225KAFN
NNF

08052R104K8B
B

VJ0805Y105KXXTW1
BC

08055C103KAT
2A

C0603C104K4R ACTU

| GCM31CR71E475KA5 5L

T491A475K006A T

C1206C475K3R
ACTU

1812GC472KAT
2A

TPD4E001DRLR

DP83848CVV/
NOPB

# Reference designator Code Part Number MOQ Qty Part name Package € | Part Number Unit price MOQ € | Part Number Unit price MOQ Unit price €

74AUP1G74DC,12 5 | | 771-AUP1GDC125
| | 595-CD74HC4050PW R
| | 511-STM32F769IIT6
| | 511-LD1117ADT33-TR
| IS42S16400J-7TLI | 870-IS42S16400J-7TL
| AT24C256C-SSHL-B-ND | 556-AT24C256C-SSHL-B
| WM11190CT-ND | 538-503398-1892
20 | 1 | 74AUP1G74DC.125 | VSSOP-8 | IC2 | 2445023 | 0,369 | 1 | 1727-6029-1-ND | 0,430 | 1 | 0,419 | 1
21 | 1 | CD74HC4050PWR | TSSOP-16 | IC3 | 1753505 | CD74HC4050PW | 0,436 | 5 | 296-9215-1-ND | 0,400 | 1 | 0,376 | 1
22 | 1 | STM32F769IIT6 | LQFP-176 | IC4 | 2849930 | STM32F769IIT6 | 15,100 | 1 | 497-16649-ND | 14,800 | 1 | 14,510 | 1
23 | 1 | LD1117ADT33TR | TO-252 (DPAK) | IC5 | 2849768 | LD1117ADT33TR | 0,419 | 1 | 497-3455-1-ND | 0,420 | 1 | 0,408 | 1
24 | 1 | IS42S16400J | TSOP-II | IC7 | 2901167 | IS42S16400J-6TLI | 2,710 | 1 | 2,050 | 1 | 1,410 | 1
25 | 1 | AT24C256C-SSHL-B | SOIC-8 | IC8 | 1972001 | 0,685 | 1 | 0,540 | 1 | 0,541 | 1
26 | 1 | 503398-1892 | Micro SD, push-push, 8-pin | J1 | 2358234 | 503398-1892 | 1,980 | 1 | | 2,160 | 1 | | 1,960 | 1
27 | 1 | 67803-8020 | USB mini AB, OTG, 5-pin | J2 | 1355761 | 67803-8020 | 1,470 | 1 | WM17148CT-ND | 1,790 | 1 | 538-67803-8020 | 1,790 | 1
28 | 2 | BLM18AG102SH1D | | | 1669708 | MMZ1608Y102B | 0,072 | 10 | 490-7809-1-ND | 0,052 | 50 | | 0,063 | 10
29 | 1 | DLG-0403-4R7 | 0403 power inductor | L2 | 1827980 | SDR0403-4R7ML | 0,406 | 5 | 0,424 | 10 | 0,272 | 10
30 | 1 | 505110-4091 | LCD1 | 2500025 | 505110-4091 | - | WM11292CT-ND | 1,250 | 1 | 1,150 | 1
31 | 1 | 2N27002 | SOT-23 | Q2 | 1713823 | 2N7002-7-F | 0,118 | 5 | 0,150 | 1 | 0,128 | 1
32 | 9 | 4K7 | 0805 | 2861530 | CRGCQ0805F4K7 | 0,009 | 10 | 0,090 | 1 | 0,026 | 10
33 | 3 | 1K5 | 0805 | R16, R17, R38 | 2861908 | CRGCQ0805J1K5 | 0,007 | 10 | 541-4161-1-ND | 0,041 | 10 | 0,085 | 10
34 | 1 | 47R | 0805 | R18 | 2861899 | CRGCQ0805J47R | 0,007 | 10 | P47.0CCT-ND | 0,069 | 10 | 0,028 | 10
35 | 7 | 10K | 0805 | 9237755 | 0,022 | 10 | 0,039 | 10 | 0,014 | 10
36 | 2 | 47K | 0805 | R23, R24 | 2447664 | 0,010 | 10 | RHM47KKCT-ND | 0,074 | 10 | 0,026 | 10
37 | 2 | 10R | 0805 | 2447556 | 0,007 | 10 | 0,064 | 10 | 0,047 | 10
38 | 2 | 22R | 0805 | R32, R33 | 2447609 | 0,008 | 10 | 0,036 | 10 | 0,053 | 10
39 | 2 | 470K | 0805 | R35, R36 | 2447661 | 0,007 | 10 | A126370CT-ND | 0,008 | 10 | 0,053 | 10
40 | 4 | 49R9 | 0805 | R39, R40, R43, R48 | 2447669 | 0,009 | 10 | 0,039 | 10 | 0,026 | 10

AT24C256C-SSHL-B

0603 ferrite bead; 60R; L1, L3 100MHz | | 81-BLM18AG102SH 1D
| SDR0403-4R7MLCT-ND | 652-SDR0403-4R7ML
SMD; FFC/FPC 40-pin lower side entry | | 538-505110-4091
| 2N7002LT1GOS CT-ND | 863-2N7002LT1G
R1, R4, R5, R7, R8, R9, R12, R15, R31 | 311-4.70KCRCT-ND | 603-RC0805FR-074K7L
| | 279-CRGCQ0805F1K 5
| | 279-CRGCQ0805F47 R
| ND | 603-RC0805FR-0710KL
MCWR08X4702FT L | | 603-RC0805FR-0747KL
| 311-10.0CRCT-ND | 71-CRCW080510R0 FKEAC
MCWR08X22R0FT L | 311-22.0CRCT-ND | 71-CRCW080522R0 FKEAC
| | 71-CRCW0805470K FKEA
MCWR08X49R9FT L | 311-49.9CRCT-ND | 603-RC0805FR-0749R9L

R2, R3, R11, R13, R28, R34, R37

RC0805FR-0710KL | 311-10.0KCRCT-
R26, R29 | MCWR08X10R0FT
| L

MCWR08X4703FT
L

# Qty Part name

20 | 1 | 74AUP1G74DC.125
21 | 1 | CD74HC4050PWR
22 | 1 | STM32F769IIT6
23 | 1 | LD1117ADT33TR
24 | 1 | IS42S16400J
25 | 1 | AT24C256C-SSHL-B
26 | 1 | 503398-1892
27 | 1 | 67803-8020
28 | 2 | BLM18AG102SH1D
29 | 1 | DLG-0403-4R7
30 | 1 | 505110-4091
31 | 1 | 2N27002
32 | 9 | 4K7
33 | 3 | 1K5
34 | 1 | 47R
35 | 7 | 10K
36 | 2 | 47K
37 | 2 | 10R
38 | 2 | 22R
39 | 2 | 470K
40 | 4 | 49R9
Code Part Number MOQ € | Code / Part Number Unit price MOQ € | THT SMD | Line Cost € Unit price
| 74AUP1G74DC, 125

Best
Supplier

Lowest
unit price
€

Order
Qty
813-9254 | 0,408 | 20 | 74AUP1G74DC.125 | 0,323 | 3 | 1 | TME | 0,323 € | 1 | 0,323
662-7131 | 0,309 | 10 | - | 1 | RS | 0,309 € | 1 | 0,309
- | STM32F769IIT6 | 13,010 400 | 1 | TME | 13,010 € | 1 | 13,010
686-9123 | 0,499 | 10 | LD1117ADT33 | 0,521 | 3 | 1 | Mouser | 0,408 € | 1 | 0,408
811-5125 | 2,565 | 2 | IS42S16400J-7TL | 2,050 | 1 | 1 | Mouser | 1,410 € | 1 | 1,410
738-0041 | 0,488 | 5 | AT24C256C-SSHL-B | 0,470 | 3 | 1 | TME | 0,470 € | 1 | 0,470
880-1277 | 503398-1892 | 2,600 | 1 | MX-503398-1892 | 0,860 | 2 | 1 | TME | 0,860 € | 1 | 0,860
720-6618 | 67803-8020 | 1,540 | 5 | MX-67803-8020 | 0,590 | 1 | 1 | TME | 0,590 € | 1 | 0,590
839-0803 | 0,043 100 | BLM18AG102SH1D | 0,016 | 50 | 2 | TME | 0,016 € | 2 | 0,031
- | DLG-0403-4R7 | 0,129 | 10 | 1 | TME | 0,129 € | 1 | 0,129
- | - | 1 | Mouser | 1,150 € | 1 | 1,150
545-0012 | 2N7002LT1G | 0,126 | 50 | 2N7002LT1G | 0,025 | 25 | 1 | TME | 0,025 € | 1 | 0,025
223-0528 | CRG0805F4K7 | 0,010 | 50 | SMD0805-4K7-1% | 0,022 100 | 9 | Farnell | 0,009 € | 9 | 0,077
223-0449 | CRG0805F1K5 | 0,036 | 50 | SMD0805-1K5-1% | 0,022 100 | 3 | Farnell | 0,007 € | 3 | 0,020
223-0253 | CRG0805F47R | 0,016 | 50 | SMD0805-47R-1% | 0,022 100 | 1 | Farnell | 0,007 € | 1 | 0,007
125-1189 | CRG0805F10K | 0,002 100 | RC0805FR-0710K | 0,022 100 | 7 | RS | 0,002 € | 2 | 0,004
679-1434 | 0,046 | 50 | SMD0805-47K-1% | 0,022 100 | 2 | Farnell | 0,010 € | 2 | 0,019
223-0152 | CRG0805F10R | 0,019 | 50 | 0805S8F100JT5E | 0,015 100 | 2 | Farnell | 0,007 € | 2 | 0,013
223-0203 | CRG0805F22R | 0,006 | 50 | 0805S8F220JT5E | 0,016 100 | 2 | RS | 0,006 € | 2 | 0,012
223-0786 | CRG0805F470K | 0,026 | 50 | 0805S8J0474T5E | 0,012 100 | 2 | Farnell | 0,007 € | 2 | 0,014
679-1462 | 0,036 | 50 | RC0805FR-0749R9 | 0,035 100 | 4 | Farnell | 0,009 € | 2 | 0,019

CD74HC4050P
WR

LD1117ADT33T
R

IS42S16400J-7TLI

AT24C256C-SSHL-B

BLM18AG102S
H1D

CRCW080547K
0FKEA

CRCW080549R
9FKEA

# Reference designator Code Part Number MOQ Qty Part name Package € | Part Number Unit price MOQ € | Part Number Unit price MOQ Unit price €

| ND | 603-RC0805FR-072K2L
R50, R51 | RMCF0805FT22 0RCT-ND | 603-RC0805FR-13220RL
| 311-4.87KCRCT-ND | 652-CR0805FX-4871ELF
| RC0805FR-071KL | 603-RC0805FR-071KL
| CAY16-330J4LFCT-ND | 652-CAY16-330J4LF
THT; buzzer Ø9 or Ø12 mm | | 539-PB09N23P-03Q
41 | 6 | 2K2 | 0805 | 9237534 | 0,037 | 10 | 0,039 | 10 | 0,026 | 10
42 | 2 | 220R | 0805 | 1099795 | WCR0805-220RFI | 0,019 | 10 | 0,020 | 10 | 0,020 | 10
43 | 1 | 4K87 | 0805 | R54 | 1469925 | 0,016 | 10 | 0,039 | 10 | 0,037 | 10
44 | 2 | 1K | 0805 | R6, R10 | 1099800 | WCR0805-1K0FI | 0,019 | 10 | 0,039 | 10 | 0,015 | 10
45 | 7 | DR1206-33R-4/8 | 1206; resistor array | 1770128 | CAY16-330J4LF | 0,069 | 10 | 0,090 | 1 | 0,085 | 1
46 | 1 | LD-BZEN 0903 | SP1 | - | 458-1370-ND | 2,110 | 1 | 1,820 | 1
47 | 1 | TL1100CF160Q | SW1 | 2830627 | TL1100CF160Q | 0,474 | 1 | EG1822-ND | 0,380 | 1 | 612-TL1100C | 0,442 | 1
48 | 1 | PEC16-2215F-S0024 | SW2 | - | 1,340 | 1 | 1,220 | 1
49 | 1 | DS1024-2*20R0 | X1 | 1805895 | 4,920 | 1 | SAM11958-ND | 3,060 | 1 | 3,050 | 1
50 | 1 | DS1013-16SSIB1 | X2 | 2843530 | 0,220 | 1 | ED10523-ND | 0,350 | 1 | 0,540 | 1
51 | 1 | 691322110005 | X3 | 2493680 | CTB932HD/5 | 0,373 | 10 | 732-2772-ND | 1,010 | 1 | 1,000 | 1
52 | 1 | X5 | - | -
53 | 1 | 25 MHz | SMD; HC-49/US; XTAL | Y1 | 2832034 | LFXTAL033342 | 0,227 | 1 | 1923-1536-1-ND | 0,360 | 1 | 0,298 | 1
54 | 1 | XTAL016178-85SMX | SMD; 8.7mm x 3.7mm; XTAL | Y2 | 1652572 | 0,440 | 1 | 1923-1021-1-ND | 0,520 | 1 | 0,393 | 1
55 | 1 | BZX384-B24.115 | SOD-323 | ZD1 | 2844814 | MM3Z24VST1G | 0,130 | 5 | 1727-3645-1-ND | 0,210 | 10 | 0,141 | 10

Not installed / optional

1 | N.C. | 0805 | C1

2 N.C. 0603 C40, C59

| | TPD4E001DRLR
1 MMBT5551 SOT-23 Q1 1459109 MMBT5551LT1G 0,154 5 | 0,180 1 MMBT5551LT1G OSCT-ND | 0,170 1 863-MMBT5551LT1G
| ND | 603-RC0805FR-0710KL
2 22R 0805 R20, R21 1099795 WCR0805-220RFI 0,019 10 | RMCF0805FT22 0,020 10 R0CT-ND | RC0805FR-0,026 10 07220RL
2 | TPD4E001DRLR | SOT-6 | 1611469 | TPD4E001DRLR | 0,453 | 5 | 296-21887-1-ND | 0,590 | 1 | 0,536 | 1
2 | 10K | 0805 | R14, R19 | 9237755 | 0,022 | 10 | 0,039 | 10 | 0,014 | 10
1 | 330R | 0805 | R25
1 | 47K | 0805 | R28 | 2447664 | 0,010 | 10 | RHM47KKCT-ND | 0,074 | 10 | 0,026 | 10
3 | 2K2 | 0805 | R37, R40, R41 | 9237534 | 0,037 | 10 | 0,039 | 10 | 0,026 | 10

R42, R47, R49, R52, R53,
R55
RC0805FR-072K2L | 311-2.20KCRCT-

CRCW08054K87F
KEA

RN1, RN2, RN3, RN4, RN5,
RN6, RN7

THT; tactile switch, without
cap
THT; encoder with switch | PEC16-2215F-S0024-ND | 652-PEC16-2215FS0024
| | 200-SSW12002TDRA
THT; 16-pin IDC socket; male MC-254-16-00-ST-DIP | | 710-61201621621
| | 710-691322110005
LMJTAB881243M-L or THT; RJ45 socket with LMJ30288115CNL magnetics and LEDs; shielded | | Non-Stocked, Call for Quote
| | 815-ABLS-25.0M-F-T
XTAL016178-85SMX | | 449-LFXTAL016178R EEL

THT; 40-pin socket; female; angled 90°

SSW-120-02-T-D-RA

THT; Pluggable Terminal
Blocks; 3.5mm; 5-pin

771-BZX384-
B24115
IC6, IC13 | 595-
RC0805FR-0710KL | 311-10.0KCRCT-

MCWR08X4702FT
L

603-RC0805FR-0747KL

RC0805FR-072K2L | 311-2.20KCRCT-
| ND

603-RC0805FR-072K2L

# Qty Part name

41 | 6 | 2K2
42 | 2 | 220R
43 | 1 | 4K87
44 | 2 | 1K
45 | 7 | DR1206-33R-4/8
46 | 1 | LD-BZEN 0903
47 | 1 | TL1100CF160Q
48 | 1 | PEC16-2215F-S0024
49 | 1 | DS1024-2*20R0
50 | 1 | DS1013-16SSIB1
51 | 1 | 691322110005

52 1

53 | 1 | 25 MHz
54 | 1 | XTAL016178-85SMX
55 | 1 | BZX384-B24.115

Not installed / optional

1 | N.C.
2 | N.C.
2 | TPD4E001DRLR
1 | MMBT5551
2 | 10K
2 | 22R
1 | 330R
1 | 47K
3 | 2K2

LMJTAB881243M-L or
LMJ30288115CNL
Code Part Number MOQ € | Code / Part Number Unit price MOQ € | THT SMD | Line Cost € Unit price

Best
Supplier

Lowest
unit price
€

Order
Qty
679-1207 | 0,039 | 50 | SMD0805-2K2-1% | 0,022 100 | 6 | TME | 0,022 € | 2 | 0,045
223-0332 | CRG0805F220R | 0,018 | 50 | 0805S8F2200T5E | 0,022 100 | 2 | RS | 0,018 € | 2 | 0,036
- | RC0805FR-074K87 | 0,035 100 | 1 | Farnell | 0,016 € | 1 | 0,016
223-0427 | CRG0805F1K0 | 0,017 | 50 | SMD0805-1K-1% | 0,022 100 | 2 | Mouser | 0,015 € | 2 | 0,030
522-5670 | CAY16-330J4LF | 0,004 | 50 | DR1206-33R-4/8 | 0,009 100 | 7 | RS | 0,004 € | 7 | 0,028
- | LD-BZEN-0903 | 0,498 | 1 | 1 | TME | 0,498 € | 1 | 0,498
- | - | 1 | Digikey | 0,380 € | 1 | 0,380
- | - | 1 | Mouser | 1,220 € | 1 | 1,220
154-8342 | 4,320 | 1 | DS1024-2*20R0 | 0,680 | 1 | 1 | TME | 0,680 € | 1 | 0,680
771-8357 | 61201621621 | 0,540 | 1 | DS1013-16SSIB1 | 0,130 | 5 | 1 | TME | 0,130 € | 1 | 0,130
824-6642 | 691322110005 | 0,960 | 1 | - | 1 | Farnell | 0,373 € | 1 | 0,373
- | LMJTAB881243M-L | 1,890 | 1 | 1 | TME | 1,890 € | 1 | 1,890
478-9628 | LFXTAL010595 | 0,764 | 1 | 25.00M-SMDHC49R | 0,443 | 2 | 1 | Farnell | 0,227 € | 1 | 0,227
148-4350 | LFXTAL016178 | 0,252 | 20 | 32.768K-85SMXR | 0,569 | 2 | 1 | RS | 0,252 € | 1 | 0,252
822-2217 | BZT52C24S-7-F | 0,067 | 50 | BZX384-B24.115 | 0,035 | 20 | 1 | TME | 0,035 € | 1 | 0,035
7 | 143 | 36,15 €
| | | | 1 | Farnell | 0,000 € | 1 | 0,000
| | | | 2 | Farnell | 0,000 € | 2 | 0,000
709-9066 | 0,552 | 5 | - | 2 | Farnell | 0,453 € | 3 | 1,359
545-0400 | 0,146 | 10 | MMBT5551 | 0,024 | 25 | 1 | TME | 0,024 € | 1 | 0,024
125-1189 | CRG0805F10K | 0,002 100 | RC0805FR-0710K | 0,022 100 | 2 | RS | 0,002 € | 2 | 0,004
223-0332 | CRG0805F220R | 0,024 | 50 | SMD0805-220R-1% | 0,022 100 | 2 | Farnell | 0,019 € | 2 | 0,038
| | | | | 1 | Farnell | 0,000 € | 3 | 0,000
679-1434 | 0,046 | 50 | SMD0805-47K-1% | 0,022 100 | 1 | Farnell | 0,010 € | 1 | 0,010
679-1207 | 0,039 | 50 | SMD0805-2K2-1% | 0,022 100 | 3 | TME | 0,022 € | 2 | 0,045

CRCW08052K2
0FKEA

SSW-120-02-F-D-RA

TPD4E001DRLR

MMBT5551LT1
G

CRCW080547K
0FKEA

CRCW08052K2
0FKEA

# Reference designator Code Part Number MOQ Qty Part name Package € | Part Number Unit price MOQ € | Part Number Unit price MOQ Unit price €

1 220R 0805 R41 1099795 WCR0805-220RFI 0,019 10 | RMCF0805FT22 0,020 10 0RCT-ND | 603-RC0805FR-0,020 10 13220RL
| | 859-LTST-C170YKT
1 LTST-C170GKT 0805 LED; Green VBUS 2322081 150080VS75000 0,171 5 | 160-1179-1-ND 0,201 10 | 859-LTST-0,136 10 C170GKT
1 | LTST-C170YKT | 0805 LED; Yellow | SPEED | 2062217 | 0,180 | 5 | 160-1175-1-ND | 0,229 | 10 | 0,153 | 10
1 | N.C. | X4

Related parts and accessories

1 | 4JWHT | SW2 button cap; red | - | - | 612-4J-WH | 0,126 | 1
1 | A1031648 | | - | - | -
1 | A1101007 | SW1 knob pointer; grey | - | - | -

1

1 | 1792972 | FMC 1,5/ 5-ST-3,5 | 3,360 | 1 | 277-6248-ND | 5,060 | 1 | 651-1952296 | 4,900 | 1
1 | Micro SD card | 4 GB or 8 GB without adapter | - | 8,560 | 1 | 619-32328 | 6,980 | 1
1 | CR2032 | - | - | -

Custom made components

1 | ALLPCB.com (Qty of 5) | -

All prices are net prices (without VAT)

All resistors are 1% 0805 and all capacitors are X7R 0805 if not otherwise specified.

SML-LX0805YC-TR

SW1 knob with pointer;
Ø31x16mm; grey

ER-TFT043-8-3023,
resistive touchscreen

Buydisplay.com:
https://www.buydisplay.com/default/low-cost-4-3-inch-480x272-tft-lcd-display-w-optl-capacitive-touch-screen

15EDGKN-3.5-05P-14-
1000AH

Pluggable terminal block;
3.5mm; push-in, 5-pin

SQF-MSDM1-
4G-21C-ND

Battery; lithium; 3V;
Ø20x3.2mm

PCB 4-layer 139 x 70
mm

Please note that BOM does not contain ordering number for parts on reels or that which includes re-reeling fee (e.g. Farnell). Take also into account that total cost is higher because min. quantity (MOQ) for many parts is larger then what is needed for single unit.

# Qty Part name

1 | LTST-C170YKT
1 LTST-C170GKT | 692-0900 LTST-C170GKT 0,211 50 | LTST-C170GKT 0,055 10 | 1 | 0,055
| | | 1 | 0,000

Related parts and accessories

1 | N.C.
1 | 4JWHT
1 | A1031648
1 | A1101007

1 ER-TFT043-8-3023, resistive touchscreen

| 15EDGKN-3.5-05P-14-1000AH

1 Micro SD card

1

1 CR2032

Custom made components

1

15EDGKN-3.5-05P-14-
1000AH

PCB 4-layer 139 x 70
mm
Code Part Number MOQ € | Code / Part Number Unit price MOQ € | THT SMD | RS TME Farnell | 0,018 € 0,055 € 0,000 € | 2 1 1 | Line Cost € Unit price
1 220R | 223-0332 CRG0805F220R 0,018 50 | SMD0805-220R-1% 0,022 100 | 1 | | 0,036

Best
Supplier

Lowest
unit price
€

Order
Qty
692-0925 | LTST-C170YKT | 0,206 | 50 | LTST-C170YKT | 0,055 | 10 | 1 | TME | 0,055 € | 1 | 0,055
- | - | | | Mouser | 0,126 € | 1 | 0,126
- | A1031648 | 1,963 | 1 | TME | 1,963 € | 1 | 1,963
- | A1101007 | 0,520 | 1 | TME | 0,520 € | 1 | 0,520
| | | | | 13,700 € | 1 | 13,700
176-1456 | 1952296 | 5,056 | 1 | 1,245 | 1 | TME | 1,245 € | 1 | 1,245
124-1042 | MS-C6-8G | 12,350 | 1 | M400-0080R11 | 3,810 | 1 | TME | 3,810 € | 1 | 3,810
186-3376 | 97384022 | 0,680 | 1 | BAT-CR2032/EG-B1 | 0,680 | 1 | RS | 0,680 € | 1 | 0,680

22,04 €

ALLPCB | 12,800 € | 1 | 12,800
| | | 12,80 €
Total | 70,99 €

Buydispla
y.com
