eez-open/modular-psu/dcp405/BOM/EEZ DIB DCP405 r3B3 BOM.pdf

EEZ DIB DCP405 BOM (r3B3, 2021-04-11) Project source code at https://github.com/eez-open/modular-psu
Farnell / Element14 Unit price Qty Part name Package Reference designator Code Part Number MOQ € | Digi-Key Part Number MOQ € | Mouser Part Number MOQ € | RS Components Code Part Number MOQ €
| | 603-C1206KRX7RAB B103 | CC1206KRX7R ABB103
| | 80-C1206C225M5R ECLR | UMK316B7225K LHT
| | 710-885012007040 | GRM2195C1H1 02JA01D
MC0805N150J101 CT | | 710-885012007077 | C0805C150J5G ACTU
| | 810-C3216X7R1HK1 60AC | UMK316BBJ106 KL-T
| | 667-EEE-FK1J101P
| | 603-CC805MKX7R7B B105 | C0805C105K4R ACTU
C19, C21, C31, C36, C49, VJ0805Y103JXXP C54, C88, C93 W1BC | | 710-885012207122 | 08055C103KAT 2A
| | 710-885012007058 | C0805C151J5G ACTU
MC0805N471J500 CT | | 710-885012007038 | 0805CG471J9B B
| | 963-EMK316B7475M L-T | C1206C475K3R ACTU
C0805C331J5GAC TU | | 80-C0805C331J5G | 0805N331J500C T
| | 603-CC121KKX7R8B B226 | CL32A226KAJN NNE
MC0805N330J500 CT | | C0805C330K5G ACTU | C0805C330J5G ACTU
| | 667-EEE-FK1H470P
C0805C101JAGAC TU | | 80-C0805C101K5G | CC0805JRNP09 BN101
| | 810-CGA6M3X7S2A4 75K
C55, C74, C75, C76, C77, GRM2165C1H472J C84, C86 A01D | | 810-C2012C0G1H47 2J-1 | C2012C0G1H47 2J060AA
| | 80-C0805C682K5R | GRM2195C1H6 82JA01D
| | 80-T491A475K006 | T491A475K006A T
| | 603-CC805KKX7R9B B474 | 0805CG471J9B B
C8, C27, C33, C34, C35, C0603C104K4RAC C37, C38, C39, C40, C41, 7081 C42, C44, C48, C50, C51, C52, C57, C58, C59, C60, C64, C65, C67, C71, C72, C73, C78, C80, C82, C83, C85, C87 | | 80-C0603C104M4R | VJ0603Y104KXJ AT
1 | 5 10n/200V | 1206 | C1, C2, C3, C91, C92 | 2812560 | 885342207005 | 0,078 | 5 | 311-4491-1-ND | 0,150 | 10 | 0,129 10 | 669-8647 | 0,128 25
2 | 3 2u2 | 1206, 50V | C10, C25, C26 | 1276-2723-1-ND | 0,132 | 10 | 0,106 10 | 184-3509 | 0,151 10
3 | 1 1n | 0805 | C11 | 2896470 | 0,044 10 | 732-7858-1-ND | 0,055 | 10 | 0,052 10 | 723-6408 | 0,031 100
4 | 1 15p | C0G, 0805 | C12 | 1759270 | 0,068 10 | 1276-1163-1-ND | 0,052 | 10 | 0,057 10 | 264-4242 | 0,014 25
5 | 3 10u | 1210, 50V | C13, C14, C17 | 2672214 | 0,684 | 5 | 1276-6736-1-ND | 0,184 | 10 | 0,597 10 | 103-4163 | 0,236 20
6 | 1 EEEFK1J101P | Ø10mm, low ESR | C15 | 9696040 | EEEFK1J101P | 1,020 | 1 | PCE3819CT-ND | 0,780 | 1 | 0,690 | 1 | 708-3623 EEEFK1J101P | 0,676 | 5
7 | 7 1u | 0805 | 2896566 | 0,084 | 5 | 587-1283-1-ND | 0,090 | 10 | 0,062 10 | 451-5770 | 0,028 25
8 | 8 10n | 0805 | 2896555 | 0,065 10 | 490-7194-1-ND | 0,017 | 10 | 0,036 10 | 464-6672 | 0,026 50
9 | 1 150p | C0G, 0805 | C20 | 2497017 | 0805N151J500CT | 0,038 10 | 1276-1828-1-ND | 0,049 | 10 | 0,051 10 | 147-780 | 0,047 10
10 | 1 470p | 0805 | C22 | 1759217 | 0,061 10 | 732-7837-1-ND | 0,059 | 10 | 0,056 10 | 378-700 | 0,040 25
11 | 4 4u7 | 1206 | C23, C24, C30, C66 | 1907356 | 0,240 | 5 | 1276-2970-1-ND | 0,199 | 10 | 0,129 10 | 691-1221 | 0,232 25
12 | 1 330p | C0G, 0805 | C28 | 1414686 | 0,054 10 | 1276-1189-1-ND | 0,049 | 10 | 0,036 10 | 176-3198 | 0,037 200
13 | 1 22u | 1210, 25V | C29 | 2320935 | 1,490 | 1 | 1276-3373-1-ND | 0,369 | 10 | 0,777 10 | 766-1182 | 0,343 10
14 | 3 33p | C0G, 0805 | C32, C45, C61 | 1759197 | 0,042 10 | 1276-1105-1-ND | 0,048 | 10 | 0,036 10 | 264-4264 | 0,069 25
15 | 2 EEEFK1H470P | Ø8mm, low ESR | C4, C16 | 9695931 | EEEFK1H470P | 0,419 | 1 | PCE3815CT-ND | 0,590 | 1 | 0,524 | 1 | 537-0590 EEEFK1H470P | 0,510 | 5
16 | 2 100p | C0G, 0805 | C43, C47 | 2896861 | 0,023 10 | 399-15000-1-ND | 0,019 | 10 | 0,032 10 | 461-3997 | 0,030 50
17 | 3 4u7/100V | 1210 | C5, C6, C7 | 2211140 | 0,967 50 | 587-5034-1-ND | 0,813 | 10 | 0,629 100 | -
18 | 7 4n7 | C0G, 0805 | 1828942 | 0,184 10 | 732-12255-1-ND | 0,162 | 10 | 0,072 10 | 741-4529 | 0,056 100
19 | 1 6n8 | 0805 | C62 | 1759244 | 0,033 10 | 1276-1799-1-ND | 0,052 | 10 | 0,029 10 | 624-2531 | 0,196 50
20 | 1 4u7 tant. | 1206 | C68 | 2321209 | T491A475K006AT | 0,372 | 1 | 399-9717-1-ND | 0,270 | 10 | 0,265 10 | 538-2335 | 0,290 10
21 | 3 470n | 0805 | 2627486 | 0,187 10 | 1276-6482-1-ND | 0,082 | 10 | 0,107 10 | 378-700 | 0,040 25
22 | 32 100n | 0603 | 2522597 | 0,011 10 | 490-4774-1-ND | 0,029 100 | 0,007 100 | 393-6952 | 0,069 25

VJ0805A102JXAC
W1BC

GRT31CR61H106
KE01L

C18, C53, C56, C69, C70,
C79, C81

VJ0805Y105KXXT
W1BC

C3216X7R1E475K
160AC

MC1210X226K250
CT

CGA6M3X7S2A47
5K200AB

MC0805B682K500
CT
C7A, C9, C89 | MC0805F474Z500 CT

Qty Part name | TME | | Price calculation for 1 set
Code / Part Number MOQ € | THT SMD | Lowest Best Order unit price Supplier Qty € | Line Cost €

1 5 10n/200V

2 3 2u2

3 1 1n

4 1 15p

5 3 10u

6 1 EEEFK1J101P

7 7 1u

8 8 10n

9 1 150p

10 1 470p

11 4 4u7

12 1 330p

13 1 22u

14 3 33p

15 2 EEEFK1H470P

16 2 100p

17 3 4u7/100V

18 7 4n7

19 1 6n8

20 1 4u7 tant.

21 3 470n

22 32 100n

0,019 100 | 5 | TME | 0,019 € | 5 | 0,095
CL31B225KBHNNNE | 0,029 50 | 3 | TME | 0,029 € | 3 | 0,086
CL21C102JBCNNNC | 0,026 100 | 1 | TME | 0,026 € | 1 | 0,026
CL21C150JBANNNC | 0,021 100 | 1 | RS | 0,014 € | 1 | 0,014
CL31A106KBHNNNE | 0,546 10 | 3 | Digikey | 0,184 € | 3 | 0,552
EEEFK1J101P | 0,321 | 5 | 1 | TME | 0,321 € | 1 | 0,321
CL21B105KOFNNNE | 0,010 100 | 7 | TME | 0,010 € | 7 | 0,073
CC0805KRX7R9103 | 0,027 100 | 8 | Digikey | 0,017 € | 8 | 0,136
0,025 100 | 1 | TME | 0,025 € | 1 | 0,025
0,024 100 | 1 | TME | 0,024 € | 1 | 0,024
0,381 10 | 4 | Mouser | 0,129 € | 4 | 0,516
CL21C331JBANNNC | 0,029 100 | 1 | TME | 0,029 € | 1 | 0,029
CL32A226KAJNNNE | 0,158 10 | 1 | TME | 0,158 € | 1 | 0,158
CL21C330JBANNNC | 0,015 100 | 3 | TME | 0,015 € | 3 | 0,045
EEEFK1H470P | 0,183 | 5 | 2 | TME | 0,183 € | 2 | 0,366
CL21C101JBANNNC | 0,026 100 | 2 | Digikey | 0,019 € | 2 | 0,038
- | | | 3 | Mouser | 0,629 € | 3 | 1,887
0,021 100 | 7 | TME | 0,021 € | 7 | 0,147
CL21B682KBANNNC | 0,327 100 | 1 | Mouser | 0,029 € | 1 | 0,029
T491A475K006AT | 0,099 10 | 1 | TME | 0,099 € | 1 | 0,099
CL21B474KBFNNNE | 0,027 100 | 3 | TME | 0,027 € | 3 | 0,080
CL10B104KA8NNNC | 0,098 100 | 32 | Mouser | 0,007 € 32 | 0,224

VJ1206Y103KXCTW1
BC

CC0805JRNPO9BN15
1
CC0805JRNPO9BN47
1
GCM31CR71E475KA5
5L

GRM2165C1H472JA0
1D

Qty Part name Package Reference designator Code Part Number MOQ € | Part Number MOQ € | Part Number MOQ € | Code Part Number MOQ Unit price €
| | 661-HHXC630A330M HA0G

D1, D3, D10, D11, D12, D13, D15, D17, D18, D19

| SK56A-LTPMSCT-ND
| RB160MM-60CT-ND | 755-RB160MM-60TR
| | 841-PMEG4010EGW X | PMEG4010EGW X

THT; 20x5mm fuse holder
| | 81-BLM18AG102SH 1D | BLM18AG102S H1D
| | 595-LM5145RGYT
| LTC2050HVCS8 #PBF-ND | 584-LTC2050HVCS8 #PBF | LTC2050HVCS8 #PBF
SN74LVC1G3157D CKR | | 595-SN74LVC1G315 7DCK | SN74LVC1G315 7DCKR
| | 771-AUP1GDC125 | 74AUP1G74DC, 125
| MCP23S17-E/ SS-ND | 579-MCP23S17-E/SS | MCP23S17-E/ SS
| | 595-REF5025AIDR
| TC77-5.0MCTTRCT-ND | 579-TC77-5.0MCTTR | TC77-5.0MCTTR
| | 595-DAC8552IDGKR
| | 595-ADS1120IPWR
| | R
23 | 1 HHXC630A330MHA0 | Ø8mm, low ESR | C90 | - | | | | - | | | 0,891 | 1 | -
24 | 10 BAS316 | SOD-323 | 8734275 | BAS316,115 | 0,193 | 5 | 1727-7370-1-ND | 0,120 | 1 | 771-BAS316-T/R | 0,179 | 1 | 397-2914 BAS316,115 | 0,122 50
25 | 1 SK55 | SMB | D14 | 3127440 | SBRT5A50SA-13 | 0,355 | 1 | 0,420 | 1 | 833-SK56A-LTP | 0,489 | 1 | 743-5961 SK56B R4 | 0,443 10
26 | 3 SKL16 | SOD-123 | D2, D4, D5 | 2673070 | RB160MM-60TR | 0,282 | 5 | 0,264 | 10 | 0,233 10 | 124-6774 RB160MM-60TR | 0,230 40
27 | 3 SKL14 | SOD-123 | D6, D7, D9 | 2760412 | PMEG4010EGWX | 0,204 | 5 | 1727-7335-1-ND | 0,243 | 10 | 0,188 10 | 153-0632 | 0,078 100
28 | 2 ZH32 | F1, F2 | - | - | - | -
29 | 3 BLM18AG102SH1D | 0603 | FB1, FB2, FB3 | 1515671 | 0,053 10 | 490-7809-1-ND | 0,081 | 10 | 0,063 10 | 839-0803 | 0,043 100
30 | 1 LM5145RGYT | VQFN-20 | IC1 | 3008669 | LM5145RGYT | 6,410 | 1 | 296-47121-1-ND | 2,910 | 1 | 2,890 | 1 | -
31 | 1 LTC2050HVCS8#PBF | SOIC-8 | IC11 | - | | | | | 2,760 | 1 | 2,710 | 1 | 822-6746 | | 2,155 | 2
32 | 2 SN74LVC1G3157DCKR SC-70 | IC12, IC18 | 1470911 | 0,274 | 5 | 296-14909-1-ND | 0,330 | 1 | 0,323 | 1 | 628-2769 | 0,237 10
33 | 1 74AUP1G74DC.125 | VSSOP-8 | IC13 | 2445023 | 0,369 | 1 | 1727-6029-1-ND | 0,430 | 1 | 0,419 | 1 | 813-9254 | 0,408 20
34 | 1 MCP23S17-E/SS | SSOP-28 | IC14 | 1467675 | MCP23S17-E/SS | 1,160 | 1 | | 1,210 | 1 | 1,180 | 1 | 669-6452 | | 1,188 | 5
35 | 1 REF5025AIDR | SOIC-8 | IC15 | 1439622 | REF5025AIDG4 | 3,440 | 1 | 296-39165-1-ND | 2,660 | 1 | 2,540 | 1 | 404-304 | REF5025AID | 3,030 | 1
36 | 1 TC77-5.0MCTTR | SOT23-5 | IC16 | - | | | | | 0,890 | 1 | 0,882 | 1 | 768-1549 | | 0,514 | 5
37 | 1 DAC8552IDGKR | VSSOP-8 | IC17 | - | | | | 296-46082-1-ND | 6,430 | 1 | 6,150 | 1 | -
38 | 1 ADS1120IPWR | TSSOP-16 | IC19 | - | | | | 296-37280-1-ND | 6,030 | 1 | 5,760 | 1 | -
39 | 1 | MSOP-10 | IC2 | 1710820 | TPS54060DGQ . | 3,030 | 1 | 296-37148-1-ND | 2,630 | 1 | 2,570 | 1 | 698-9079 TPS54060DGQ | 2,680 | 1
40 | 1 LM293D | SOIC-8 | IC20 | 2382616 | LM293DT | 0,289 | 5 | 296-12848-1-ND | 0,340 | 1 | 511-LM293DT | 0,255 10 | 661-2592 LM293ADR | 0,273 10
41 | 1 MAX9141ESA | SOIC-8 | IC21 | 2515004 | MAX9141ESA+ | 1,230 | 1 | 1,090 | 1 | 0,934 | 1 | 799-8282 MAX9141ESA+ | 1,360 | 5
42 | 2 SI8641BB-B-IS1 | SOIC-16 | IC3, IC7 | 2423291 | SI8641BB-B-IS1 | 2,140 | 1 | 336-2566-ND | 2,230 | 1 | 2,060 | 1 | 823-2126 Si8641BB-B-IS1 | 2,190 | 5
43 | 1 SN74LVC1G139DCUR | VSSOP-8 | IC4 | 2147991 | | 0,561 | 1 | 296-18203-1-ND | 0,510 | 1 | 0,489 | 1 | -
44 | 1 MC78L05 | SOIC-8 | IC5 | 2534293 | MC78L05ABDR2G | 0,324 | 1 | 0,420 | 1 | 0,306 | 1 | 516-6149 MC78L05ACDG | 0,150 | 1
45 | 1 MC79L05 | SOIC-8 | IC6 | 2534292 | MC79L05ACDR2G | 0,310 | 1 | | 0,350 | 1 | 0,358 | 1 | 688-9313 | | 0,110 | 1
46 | 1 M24C32-WMN6P | SOIC-8 | IC8 | 1224413 | M24C32-WMN6P | 0,212 | 5 | 497-8644-1-ND | 0,210 | 1 | 0,210 | 1 | 686-2453 | 0,180 25
47 | 2 TL072D | SOIC-8 | IC9, IC10 | 1467663 | TL072CDT | 0,358 | 5 | 296-1282-1-ND | 0,420 | 1 | 595-TL072CDR | 0,369 | 1 | 714-1082 TL072CD | 0,071 20
48 | 1 4907 | J1 | - | 36-4907-ND | 0,260 | 1 | 534-4907 | 0,257 | 1 | -
49 | 1 | J2 | 1854508 | FCR7350R | 6,170 | 1 | - | - | 144-1450 | 4,640 | 1

BLM18AG102SN1
D

74AUP1G74DC,12
5
TPS54060DGQ | TPS54060ADGQ
MAX9141ESA+-ND | 700-MAX9141ESA
| | 634-SI8641BB-B-IS1
| | 595-SN74LVC1G139 DCUR
| MC78L05ACDR2 GOSCT-ND | 863-MC78L05ACDR2 G
| MC79L05ABDG OS-ND | 863-MC79L05ACDR2 G | MC79L05ACDR 2G
| | 511-M24C32-RMN6TP | M24C32-WMN6P

SN74LVC1G139D
CUR

THT, PCB terminal; 4.8mm
FCR7350R or BSM-420-
R
THT, binding post 4 mm; red | SWEB 8094 Au / RT

Qty Part name

23 1 HHXC630A330MHA0

24 10 BAS316

25 1 SK55

26 3 SKL16

27 3 SKL14

28 2 ZH32
29 3 BLM18AG102SH1D

30 1 LM5145RGYT

31 1 LTC2050HVCS8#PBF

32 2 SN74LVC1G3157DCKR

33 1 74AUP1G74DC.125

34 1 MCP23S17-E/SS

35 1 REF5025AIDR

36 1 TC77-5.0MCTTR

37 1 DAC8552IDGKR

38 1 ADS1120IPWR

39 1

40 1 LM293D
41 1 MAX9141ESA

42 2 SI8641BB-B-IS1

43 1 SN74LVC1G139DCUR

44 1 MC78L05

45 1 MC79L05

46 1 M24C32-WMN6P

47 2 TL072D
48 1 4907
49 1

TPS54060DGQ

FCR7350R or BSM-420-
R
Code / Part Number MOQ € | THT SMD | unit price Supplier Qty € | Line Cost € Unit price
- | | | 1 | Mouser | 0,891 € | 1 | 0,891
BAS316,115 | 0,026 25 | 10 | TME | 0,026 € 10 | 0,265
SK55-DIO | 0,119 | 5 | 1 | TME | 0,119 € | 1 | 0,119
SKL16-DIO | 0,105 | 5 | 3 | TME | 0,105 € | 3 | 0,315
SKL14-DIO | 0,053 10 | 3 | TME | 0,053 € | 3 | 0,158
ZH32 | 0,228 | 5 | 2 | TME | 0,228 € | 2 | 0,456
BLM18AG102SH1D | 0,016 50 | 3 | TME | 0,016 € | 3 | 0,047
- | | | 1 | Mouser | 2,890 € | 1 | 2,890
- | | | 1 | RS | 2,155 € | 1 | 2,155
| 0,107 | 5 | 2 | TME | 0,107 € | 2 | 0,213
74AUP1G74DC.125 | 0,323 | 3 | 1 | TME | 0,323 € | 1 | 0,323
MCP23S17-E/SS | 1,230 | 1 | 1 | Farnell | 1,160 € | 1 | 1,160
- | | | 1 | Mouser | 2,540 € | 1 | 2,540
TC77-5.0MCTTR | 0,970 | 1 | 1 | RS | 0,514 € | 1 | 0,514
- | | | 1 | Mouser | 6,150 € | 1 | 6,150
- | | | 1 | Mouser | 5,760 € | 1 | 5,760
- | | | 1 | Mouser | 2,570 € | 1 | 2,570
LM293D-ST | 0,143 | 5 | 1 | TME | 0,143 € | 1 | 0,143
- | | | 1 | Mouser | 0,934 € | 1 | 0,934
- | | | 2 | Mouser | 2,060 € | 2 | 4,120
- | | | 1 | Mouser | 0,489 € | 1 | 0,489
MC78L05ACDG | 0,228 | 3 | 1 | RS | 0,150 € | 1 | 0,150
MC79L05ACDG | 0,232 | 3 | 1 | RS | 0,110 € | 1 | 0,110
M24C32-WMN6P | 0,165 | 3 | 1 | TME | 0,165 € | 1 | 0,165
TL072CD-ST | 0,240 | 3 | 2 | RS | 0,071 € | 2 | 0,142
61-1537-11/0031 | 0,049 10 | 1 | TME | 0,049 € | 1 | 0,049
BSM-420-R | 1,426 | 1 | 1 | TME | 1,426 € | 1 | 1,426

SN74LVC1G3157DCK
R

Qty Part name Package Reference designator Code Part Number MOQ € | Part Number MOQ € | Part Number MOQ € | Code Part Number MOQ Unit price €
FCR7350B or BSM-420-THT, binding post 4 mm; black B | | | SWEB 8094 Au / SW
| | 817-FTR-C1GA005GB05
THT; RN112 | | 631-RN112-4-02-0M7
| | 667-ETQ-P4M100KFM
IHLP2020CZER3R 3M11 | 445-180834-1-ND | 810-VLS6045AF-3R3N
| | 604-WP42WUM/ EGW
THT, dual (red/red) 3 mm LED | | 604-WP934MD2LID
| | 604-WP934MDLYLID
BSC117N08NS5AT MA1 | BSC117N08NS5 ATMA1CT-ND | 726-BSC117N08NS5 ATMA
| T2N7002AKLMC T-ND | 757-T2N7002AKLM
BSS205NH6327XTSA1 BSS205NH6327XT SA1 | BSS205NH6327 XTSA1CT-ND | BSS205NH6327 XTSA1 | BSS205NH6327 XTSA1
| | 771-PSMN0R925YLC 115 | PSMN0R9-25YLC,115
BSS84PH6327XTS A2 | BSS84PH6433X TMA1CT-ND | 726-BSS84PH6327X TSA2
| | 771-BT139B-600E118
| FMMT493CT-ND
| | 771-PSMN013-60YLX
BSC039N06NSAT MA1 | BSC039N06NSA TMA1CT-ND | 726-BSC039N06NSA TMA1 | BSC039N06NSA TMA1
| OSCT-ND | 863-MMBT5551LT1G | MMBT5551LT1 G
| MMBT5401-FDICT-ND | 621-MMBT5401-F
50 | 1 | J3 | 1854507 | FCR7350B | 5,750 | 1 | - | - | 144-1451 | 4,640 | 1
51 | 1 FTR-C1GA005G-B05 | Miniature relay, non-latching | K1 | - | - | 2,440 | 1 | 195-8095 FTR-C1GA005G | 3,740 | 1
52 | 1 RN112-4-02-0M7 | | L1 | | | | | 817-2100-ND | 1,560 | 1 | 1,400 | 1 | -
53 | 1 ETQ-P4M100KFM | Power inductor | L2 | 2965285 | ETQP4M100KFM | 1,000 | 1 | P124167CT-ND | 1,070 | 1 | 1,010 | 1 | -
54 | 1 HPI0630-3R3 | Power inductor | L3 | 1741325 | | 1,940 | 5 | | 0,510 | 1 | 0,510 | 1 | -
55 | 1 WP42WUM/EGW | | LED1 | - | | | | 754-1718-ND | 0,930 | 1 | 0,926 | 1 | -
56 | 1 WP934MD/2LID | | LED2 | - | | | | 754-2000-ND | 0,920 | 1 | 1,030 | 1 | -
57 | 1 WP934MD/LYLID | | LED3 | - | | | | 754-2008-ND | 0,990 | 1 | 0,795 | 1 | -
58 | 1 BSC117N08NS5ATMA1 PG-TDSON-8 | Q1 | 2725815 | 1,130 | 1 | 1,040 | 1 | 1,150 | 1 | -
59 | 5 2N7002 | SOT-23 | Q10, Q16, Q18, Q21, Q25 | 1713825 | 2N7002K-7 | 0,148 | 5 | 0,126 | 10 | 0,113 10 | 671-0312 2N7002 | 1,250 20
60 | 1 | SOT-23 | Q11 | 2480648 | 0,257 | 5 | 0,274 | 10 | 0,236 10 | 892-2374 | 0,108 100
61 | 2 PSMN0R9-25YLC | SOT-669 | Q12, Q13 | 1895396 | | 1,300 | 5 | 1727-5292-1-ND | 1,270 | 1 | 1,320 | 1 | 798-2895 | | 1,537 | 3
62 | 1 BSS84P | SOT-23 | Q14 | 1056526 | 0,224 | 5 | 0,314 | 10 | 0,196 10 | -
63 | 1 BT139B-600E | D2PAK | Q15 | 2902357 | BT139B-600,118 | 1,040 | 1 | 1740-1053-1-ND | 0,820 | 1 | 0,855 | 1 | 509-522 | BT139B-600,118 | 0,908 | 1
64 | 1 FMMT493TA | SOT-23 | Q17 | 2061448 | FMMT493ATA | 0,348 | 5 | 0,420 | 1 | 522-FMMT493TA | 0,376 | 1 | 274-885 | FMMT493TA | 0,302 10
65 | 1 PSMN013-60YL | SOT-669 | Q19 | 2617064 | PSMN013-60YLX | 0,706 | 1 | 1727-2589-1-ND | 0,600 | 1 | 0,576 | 1 | -
66 | 1 BSC039N06NSATMA1 | PG-TDSON-8 | Q2 | 2480737 | 1,750 | 1 | 1,450 | 1 | 1,430 | 1 | 906-4292 | 1,326 10
67 | 3 MMBT5551 | SOT-23 | 1459109 | MMBT5551LT1G | 0,154 | 5 | 0,180 | 1 | 0,170 | 1 | 545-0400 | 0,146 10
68 | 3 MMBT5401 | SOT-23 | Q3, Q8, Q22 | 2533333 | MMBT5401LT3G | 0,181 | 5 | 0,154 | 10 | 0,135 10 | 739-0546 MMBT5401 | 0,157 10
69 | 2 D45H11FP | Q4, Q5 | - | 497-12486-5-ND | 1,110 | 1 | 511-D45H11FP | 1,090 | 1 | -
70 | 1 FQPF11P06 | Q6 | - | 0,920 | 1 | 512-FQPF11P06 | 0,873 | 1 | 807-5885 FQPF11P06 | 0,715 10
71 | 1 BCP56 | SOT-223 | Q7 | 2628083 | BCP56TX | 0,263 | 5 | 0,350 | 1 | 0,297 | 1 | 773-7633 BCP56-16T3G | 0,138 10
72 | 1 NZT605 | SOT-223 | Q9 | 2825127 | NZT605 | 0,334 | 5 | NZT605CT-ND | 0,380 | 1 | 512-NZT605 | 0,341 | 1 | 806-1268 NZT605 | 0,284 25
73 | 1 11K | 0805 | R10 | 2447559 | 0,008 10 | A126334CT-ND | 0,045 | 10 | 0,014 10 | 679-0831 | 0,038 50
74 | 2 750R | 0805 | 2447719 | 0,010 10 | A126385CT-ND | 0,046 | 10 | 0,052 10 | 215-2298 RN73C2A750RB | 0,666 | 5
75 | 1 3K3 | 0805 | R107 | 2447651 | 0,008 10 | A129755CT-ND | 0,048 | 10 | 0,014 10 | 223-0499 CRG0805F3K3 | 0,027 50
76 | 1 3K9 | 0805 | R11 | 2447654 | 0,008 10 | A126369CT-ND | 0,045 | 10 | 0,140 10 | 679-1377 | 0,004 50

THT, dual (green/red) 3 mm LED

THT, dual (yellow/red) 3 mm LED

PSMN0R9-
25YLC,115
Q20, Q23, Q24 | MMBT5551LT1G

THT, TO-220FP
THT, TO-220FP | FQPF11P06FS-ND
| BCP5616QTADI CT-ND | 621-BCP5616QTA

MCWR08X1102FT
L
| 652-CR0805FX-1102ELF | CRCW080511K 0FKEA
R106, R111 MCWR08X7500FT L | | 71-CRCW0805750R FKEB
| | 652-CR0805FX-3301ELF
MCWR08X3901FT L | | 279-CRGP0805F3K9 | CRCW08053K9 0FKEA

MCWR08X3301FT
L

Qty Part name

50 1

51 1 FTR-C1GA005G-B05

52 1 RN112-4-02-0M7

53 1 ETQ-P4M100KFM

54 1 HPI0630-3R3

55 1 WP42WUM/EGW

56 1 WP934MD/2LID

57 1 WP934MD/LYLID

58 1 BSC117N08NS5ATMA1

59 5 2N7002

60 1

61 2 PSMN0R9-25YLC

62 1 BSS84P

63 1 BT139B-600E

64 1 FMMT493TA
65 1 PSMN013-60YL

66 1 BSC039N06NSATMA1

67 3 MMBT5551

68 3 MMBT5401

69 2 D45H11FP
70 1 FQPF11P06

71 1 BCP56

72 1 NZT605
73 1 11K

74 2 750R

75 1 3K3

76 1 3K9

BSS205NH6327XTSA1

Code / Part Number MOQ € | THT SMD | unit price Supplier Qty € | Line Cost € Unit price

FCR7350B or BSM-420-B

BSM-420-B | 1,860 | 1 | 1 | TME | 1,860 € | 1 | 1,860
FTR-C1GA005G-B05 | 1,370 | 1 | 1 | TME | 1,370 € | 1 | 1,370
- | | | 1 | Mouser | 1,400 € | 1 | 1,400
| | | 1 | Farnell | 1,000 € | 1 | 1,000
HPI0630-3R3 | 0,335 | 1 | 1 | TME | 0,335 € | 1 | 0,335
L-42WUM/1EGWT | 0,501 | 1 | 1 | TME | 0,501 € | 1 | 0,501
- | | | 1 | Digikey | 0,920 € | 1 | 0,920
- | | | 1 | Mouser | 0,795 € | 1 | 0,795
| 0,728 | 5 | 1 | TME | 0,728 € | 1 | 0,728
2N7002LT1G | 0,019 25 | 5 | TME | 0,019 € | 5 | 0,096
0,097 10 | 1 | TME | 0,097 € | 1 | 0,097
PSMN0R9-25YLC.115 | 0,709 | 2 | 2 | TME | 0,709 € | 2 | 1,418
BSS84P | 0,060 10 | 1 | TME | 0,060 € | 1 | 0,060
BT139B-600E.118 | 0,700 | 1 | 1 | TME | 0,700 € | 1 | 0,700
FMMT493TA | 0,125 10 | 1 | TME | 0,125 € | 1 | 0,125
- | | | 1 | Mouser | 0,576 € | 1 | 0,576
BSC039N06NS | 0,740 | 5 | 1 | TME | 0,740 € | 1 | 0,740
MMBT5551 | 0,024 25 | 3 | TME | 0,024 € | 3 | 0,073
MMBT5401 | 0,024 25 | 3 | TME | 0,024 € | 3 | 0,071
- | | | 2 | Mouser | 1,090 € | 2 | 2,180
- | | | 1 | RS | 0,715 € | 1 | 0,715
BCP56-16T1G | 0,153 | 5 | 1 | RS | 0,138 € | 1 | 0,138
NZT605 | 0,222 | 5 | 1 | TME | 0,222 € | 1 | 0,222
0805S8F1102T5E | 0,015 100 | 1 | Farnell | 0,008 € | 1 | 0,008
0805S8F7500T5E | 0,015 100 | 2 | Farnell | 0,010 € | 2 | 0,019
0805S8F3301T5E | 0,015 100 | 1 | Farnell | 0,008 € | 1 | 0,008
SMD0805-3K9-1% | 0,015 100 | 1 | RS | 0,004 € | 1 | 0,004

BSC117N08NS5ATMA
1

BSS205NH6327XTSA
1

Qty Part name Package Reference designator Code Part Number MOQ € | Part Number MOQ € | Part Number MOQ € | Code Part Number MOQ Unit price €
| ND | 603-RC0805FR-072K2L | CRCW08052K2 0FKEA
| 311-86.6KCRCT-ND | 603-RT0805FRE0786 K6L
| | 652-CR0805FX-3303ELF | CRCW0805330 KFKEA
| | 603-RC2010FK-0715RL | RK73HW2HTTE 15R0F
| 311-8.20KCRCT-ND | 652-CR0805FX-8201ELF
MCLRP12JTWSR1 00 | | 71-RCWE2512R100 FKEA | CRA2512-FZ-R100ELF
| CRM2512-JW-2R2ELFCT-ND
R27, R28, R30, R35, R84, R86, R96, R100, R102 | 311-4.70KCRCT-ND | 603-RC0805FR-074K7L
| ND | 603-RC0805FR-0710KL
R36, R43, R69, R70, R89, R90, R94, R101 | RC0805FR-071KL | 603-RC0805FR-071KL
| RMCF0805FT22 0RCT-ND | 603-RC0805FR-13220RL
MCWR08X2202FT L | RMCF0805FT22 K0CT-ND | 71-CRCW080522K0 FKEAC | CRCW080522K 0FKEA
| 311-470CRCT-ND | 71-CRCW0805470R FKEB
MCTC0525B7501T 5E | | 279-CPF0805B7K5E1
| | 667-ERJ-PB6B1243V | CPF0805B124K E1
R5, R12, R14, R15, R33, RC1206FR-R34, R82 0710RL | 311-10.0CRCT-ND | 603-RC1206FR-0710RL | CR1206-FX-10R0ELF
| | 279-CPF0805B39KE1 | CPF-A-0805B39KE1
R59, R68 MCWF08R8200BT L | | 603-RT0805BRD0782 0RL | CPF-A-0805B820RE1
| RNCP1206FTD1 R00 | 756-GWCR1206-1R0FT5 | CRL1206-FW-1R00ELF
GMR100HTBFA10 L0 | | 755-GMR100HTBFA1 0L0
| RMCF0805FT27 0RCT-ND | 652-CR0805FX-2700ELF
MCWR08X1003FT L | RMCF0805FT10 0KCT-ND | 71-CRCW0805100K FKEAC
| | 652-CR0805FX-3300ELF
MCWR08X4702FT L | | 603-RC0805FR-0747KL | CRCW080547K 0FKEA
77 | 11 2K2 | 0805 | 9237534 | 0,037 10 | 0,039 | 10 | 0,026 10 | 679-1207 | 0,039 50
78 | 2 86K6 | 0805 | R18, R20 | 2303750RL ERJ6ENF8662V | 0,058 10 | 0,036 | 10 | 0,056 10 | -
79 | 1 330K | 0805 | R19 | 2447637 | 0,010 10 | A126361CT-ND | 0,046 | 10 | 0,013 10 | 679-1272 | 0,038 50
80 | 2 15R/0.75W | 2010 | R2, R50 | 2862025 | CRGCQ2010J15R | 0,076 10 | A129910CT-ND | 0,196 | 10 | 0,166 10 | 123-4428 | 0,061 50
81 | 2 8K2 | 0805 | R21, R63 | 2447732 | 0,008 10 | 0,040 | 10 | 0,014 10 | 223-0556 CRG0805F8K2 | 0,021 10
82 | 2 0R1/2-3W | 2512 | R25, R29 | 2828391 | 0,240 10 | 696-1680-1-ND | 0,465 | 10 | 0,418 10 | 693-4394 | 0,644 | 5
83 | 1 2R2/2-3W | 2512 | R26 | 1265193 | 35202R2JT | 0,143 10 | 0,342 | 10 | 279-35222R2JT | 0,296 10 | 871-1023 35222R2JT | 0,449 10
84 | 9 4K7 | 0805 | 2861530 | CRGCQ0805F4K7 | 0,012 10 | 0,040 | 10 | 0,027 10 | 223-0528 CRG0805F4K7 | 0,023 50
85 | 21 10K | 0805 | 9237755 | 0,022 10 | 0,039 | 10 | 0,014 10 | 125-1189 CRG0805F10K | 0,002 100
86 | 8 1K | 0805 | 1099800 | WCR0805-1K0FI | 0,019 10 | 0,039 | 10 | 0,015 10 | 223-0427 CRG0805F1K0 | 0,017 50
87 | 3 220R | 0805 | R37, R38, R54 | 1099795 | WCR0805-220RFI | 0,019 10 | 0,020 | 10 | 0,020 10 | 223-0332 CRG0805F220R | 0,018 50
88 | 5 22K | 0805 | R39, R46, R62, R103, R104 2447607 | 0,010 10 | 0,024 | 10 | 0,018 100 | 679-1109 | 0,034 50
89 | 6 470R | 0805 | 1099798 | WCR0805-470RFI | 0,019 10 | 0,039 | 10 | 0,041 10 | 223-0376 CRG0805F470R | 0,021 50
90 | 2 7K5 0.1% | 0805 | R42, R49 | 1575887 | 0,203 10 | YAG1974CT-ND | 0,265 | 10 | 0,249 10 | -
91 | 2 124K 0.1% | 0805 | R47, R48 | 2670132 | WF08U1243BTL | 0,025 10 | P124KDACT-ND | 0,269 | 10 | 0,160 10 | 123-1601 | 0,223 10
92 | 7 10R | 1206 | 9236643 | 0,050 10 | 0,071 | 10 | 0,034 10 | 740-9085 | 0,036 50
93 | 2 39K 0.1% | 0805 | R58, R65 | 2337828 | 0,276 10 | P20774CT-ND | 0,268 | 10 | 0,122 10 | 866-7418 | 0,343 10
94 | 2 820R 0.1% | 0805 | 2338010 | 0,276 10 | YAG1979CT-ND | 0,262 | 10 | 0,196 10 | 866-7484 | 0,265 10
95 | 2 1R | 1206 | R61, R110 | 2447479 | 0,017 10 | 0,093 | 10 | 0,022 25 | 794-4180 | 0,054 10
96 | 1 0R010 | 2512, low TCR | R67 | 2808330 | 1,130 | 5 | 511-1686-1-ND | 1,350 | 1 | 1,080 | 1 | -
97 | 1 270R | 0805 | R73 | 2073716 | MCMR08X271 JTL | 0,009 10 | 0,025 | 10 | 0,013 10 | 223-0348 CRG0805F270R | 0,025 50
98 | 5 100K | 0805 | R8, R55, R72, R97, R115 | 2447551 | 0,010 10 | 0,024 | 10 | 0,040 10 | 223-0691 CRG0805F100K | 0,028 50
99 | 5 330R | 0805 | R87, R88, R91, R105, R113 2695037 | MCWR08X331 JTL | 0,009 10 | A129743CT-ND | 0,045 | 10 | 0,013 10 | 223-0354 CRG0805F330R | 0,040 50
100 | 5 47K | 0805 | R9, R13, R60, R66, R112 | 2447664 | 0,009 10 | RHM47KKCT-ND | 0,036 | 10 | 0,014 10 | 679-1434 | 0,036 50
101 | 1 6R2 | 0805 | R98 | 2447714 | 0,012 10 | 0,070 | 10 | 0,020 10 | -

R16, R32, R40, R45, R56,
R57, R74, R77, R78, R80,
R81
RC0805FR-072K2L | 311-2.20KCRCT-

MCWR08X3303FT
L

MCWR08X8201FT
L

R3, R6, R7, R17, R22, R23, R24, R31, R41, R44, R52,
R53, R71, R83, R85, R92,
R93, R95, R99, R108, R109
RC0805FR-0710KL | 311-10.0KCRCT-

R4, R64, R75, R76, R79,
R114

MCWF08R3902BT
L

MCWR12W1R00F
TL

MCWR08W6R20F
TL

311-6.20CRCT-ND

603-RC0805FR-076R2L

Qty Part name

77 11 2K2

78 2 86K6

79 1 330K

80 2 15R/0.75W

81 2 8K2

82 2 0R1/2-3W

83 1 2R2/2-3W

84 9 4K7

85 21 10K

86 8 1K

87 3 220R

88 5 22K

89 6 470R

90 2 7K5 0.1%

91 2 124K 0.1%

92 7 10R

93 2 39K 0.1%

94 2 820R 0.1%

95 2 1R

96 1 0R010

97 1 270R

98 5 100K

99 5 330R

100 5 47K

101 1 6R2

Code / Part Number MOQ € | THT SMD | unit price Supplier Qty € | Line Cost € Unit price
0805S8F2201T5E | 0,022 100 | 11 | TME | 0,022 € 11 | 0,246
| 0,025 100 | 2 | TME | 0,025 € | 2 | 0,050
0805S8F3303T5E | 0,015 100 | 1 | Farnell | 0,010 € | 1 | 0,010
201007J0150T4E | 0,025 100 | 2 | TME | 0,025 € | 2 | 0,049
0805S8J0822T5E | 0,013 100 | 2 | Farnell | 0,008 € | 2 | 0,016
LRP12FTDRR100 | 0,155 10 | 2 | TME | 0,155 € | 2 | 0,310
WF25P2R2JTL | 0,043 50 | 1 | TME | 0,043 € | 1 | 0,043
0805S8F4701T5E | 0,023 100 | 9 | Farnell | 0,012 € | 9 | 0,105
RC0805FR-0710K | 0,022 100 | 21 | RS | 0,002 € 21 | 0,042
RC0805FR-071K | 0,022 100 | 8 | Mouser | 0,015 € | 8 | 0,120
0805S8F2200T5E | 0,022 100 | 3 | RS | 0,018 € | 3 | 0,054
0805S8J0223T5E | 0,013 100 | 5 | Farnell | 0,010 € | 5 | 0,049
RC0805FR-07470R | 0,022 100 | 6 | Farnell | 0,019 € | 6 | 0,113
AR05BTCW7501 | 0,105 10 | 2 | TME | 0,105 € | 2 | 0,210
ERA6AEB1243V | 0,090 10 | 2 | Farnell | 0,025 € | 2 | 0,050
1206S4J0100T5E | 0,012 100 | 7 | TME | 0,012 € | 7 | 0,087
AR05BTCW3902 | 0,105 10 | 2 | TME | 0,105 € | 2 | 0,211
AR05BTCW8200 | 0,105 10 | 2 | TME | 0,105 € | 2 | 0,211
CQ06S4J010JT5E | 0,012 100 | 2 | TME | 0,012 € | 2 | 0,023
- | | 1 | Mouser | 1,080 € | 1 | 1,080
0805S8F2700T5E | 0,023 100 | 1 | Farnell | 0,009 € | 1 | 0,009
0805S8F1003T5E | 0,015 100 | 5 | Farnell | 0,010 € | 5 | 0,049
0805S8F3300T5E | 0,015 100 | 5 | Farnell | 0,009 € | 5 | 0,047
RC0805FR-0747K | 0,022 100 | 5 | Farnell | 0,009 € | 5 | 0,047
RC0805JR-076R2 | 0,034 100 | 1 | Farnell | 0,012 € | 1 | 0,012

CRCW080586K6FKTA
BC

Qty Part name Package Reference designator Code Part Number MOQ € | Part Number MOQ € | Part Number MOQ € | Code Part Number MOQ Unit price €
| CAY16-330J4LFCT-ND | 652-CAY16-330J4LF
| SRF0703-821MCT-ND | 652-SRF0703-821M

THT, Minifit Jr. 2-pin, right angle

| | 649-77317-104-20LF
THT; Pluggable Terminal Blocks; 3.5mm; 5-pin | | 710-691322110005
| | 200-SSW11002TDRA | SSW-110-02-T-D-RA
| SMAJ51ALFCT-ND
| MM3Z9V1T1GO SCT-ND | 863-MM3Z9V1T1G
| SLVU2.8-TPMSCT-ND | 833-SLVU2.8-TP
102 | 3 DR1206-33R-4/8 | 1206 resistor array | RN1, RN2, RN3 | 1770128 | CAY16-330J4LF | 0,069 10 | 0,090 | 1 | 0,085 | 1 | 522-5670 CAY16-330J4LF | 0,004 50
103 | 1 SRF0703-821M | 0703 | TR1 | 1852832 | SRF0703-821M | 0,827 | 1 | 0,900 | 1 | 0,681 | 1 | -
104 | 1 39-30-1020 | X1 | 9963367 | 39-30-1020 | 0,408 10 | WM1351-ND | 0,510 | 1 | 538-39-30-1020 | 0,498 | 1 | 510-9837 39-30-1020 | 0,352 | 5
105 | 1 77317-104-20LF | X2 | - | S2111EC-10-ND | 0,820 | 1 | 1,220 | 1 | -
106 | 1 691322110005 | X3 | 2493680 | CTB932HD/5 | 0,373 10 | 732-2772-ND | 1,010 | 1 | 1,000 | 1 | 824-6642 691322110005 | 0,960 | 1
107 | 1 DS1024-2*10R0 | X4 | 1668376 | 2,640 | 1 | SAM10030-ND | 1,770 | 1 | 1,750 | 1 | 180-0986 | 2,100 | 1
108 | 2 SMAJ51A | SMA | ZD1, ZD5 | 2677667 | SMAJ51A | 0,144 | 5 | 0,370 | 1 | 652-SMAJ51A | 0,463 | 1 | 171-4238 SMAJ51A | 0,320 25
109 | 1 MM3Z9V1T1G | SOD-323 | ZD2 | 2463517 | MM3Z9V1T1G | 0,124 | 5 | 0,120 | 1 | 0,108 10 | 802-4653 MM3Z9V1T1G | 0,039 200
110 | 1 SLVU2.8-TP | TVS, SOT-23 | ZD3 | 2749173 | SLVU2.8HTG | 0,929 | 5 | 0,690 | 1 | 0,664 | 1 | 793-1942 SLVU2.8HTG | 1,000 | 5
111 | 1 MMSZ5230BT1G | SOD-123 | ZD4 | 1431272 | MMSZ5230BT1G | 0,177 10 | 0,148 | 10 | 0,170 10 | 545-3033 | 0,173 20

Not installed
1 N.C. | 0805 | C46
1 N.C. | SOD-323 | D16
1 N.C. | SOD-123 | D8
1 N.C. | 2512 | R1 | 2081875 | ASC2512-4K7FT4 | 0,195 10 | A130729CT-ND | 0,331 | 10 | 0,180 10 | 224-0424 35204K7JT | 1,370 10
1 N.C. | 0805 | R51

Related parts and accessories
2 PMB-1 | PCB bracket; polyamide | KK1, KK2 | - | - | - | -
1 SK96/84/SA | Heatsink 84 x 55 x 28 mm | KK3 | - | - | - | -
2 B3X5/BN661
2 M3X5/D7985 | - | | | | - | | | - | | | -
5 M3X8/D7985B | - | | | | - | | | - | | | -
3 B3/BN789 | - | | | | - | | | - | | | -

2 179020.5

1 LRS-150F-48 | 2815982 | LRS-150F-48 | 21,150 | 1 | 1866-3328-ND | 23,460 | 1 | 709-LRS150F-48 | 23,330 | 1 | 106-5854 LRS-150F-48 | 21,730 | 1
1 TBC-07 | - | | | | 1866-4907-ND | 0,260 | 1 | 709-TBC-07 | 0,292 | 1 | -
1 | 1792972 | FMC 1,5/ 5-ST-3,5 | 3,360 | 1 | 277-6248-ND | 5,060 | 1 | 651-1952296 | 4,900 | 1 | 176-1456 1952296 | 5,056 | 1

Custom made components
1 PCB | 4-layer 180 x 95 mm, 1 oz. Cu thickness (MOQ: 5, incl. S&H)
| All prices are net prices (without VAT)

THT, 20-pin 0.1" header right angled

THT, 20-pin 0.1" receptacle right angled

SSW-110-02-G-D-RA

MMSZ5230BT1G
OSCT-ND

863-
MMSZ5230BT1G

MMSZ5230BT1
G

279-
CRGP2512F4K7

Screw; M3x5; countersunk;
Phillips; A2 stainless steel Screw; M3x5; cheese head;
Phillips for PCB brackets
Screw; M3x8; cheese head;
black; Phillips for heatsink and TO-220 parts
Washer; externally serrated; M3; D=6mm; h=0.4mm
20 x 5 mm, 5A fuse; quick
blow
Mean Well 48 Vdc power
module
Terminal cover for Mean Well power module
15EDGKN-3.5-05P-14-
1000AH

Pluggable terminal block;
3.5mm; push-in, 5-pin

Qty Part name

102 3 DR1206-33R-4/8

103 1 SRF0703-821M

104 1 39-30-1020

105 1 77317-104-20LF

106 1 691322110005

107 1 DS1024-2*10R0

108 2 SMAJ51A

109 1 MM3Z9V1T1G

110 1 SLVU2.8-TP

111 1 MMSZ5230BT1G

Not installed
1 N.C.
1 N.C.
1 N.C.
1 N.C.

1 N.C.

Related parts and accessories 2 PMB-1
1 SK96/84/SA
2 B3X5/BN661

2 M3X5/D7985

5 M3X8/D7985B

3 B3/BN789

2 179020.5

1 LRS-150F-48

1 TBC-07

1

Custom made components
1 PCB

15EDGKN-3.5-05P-14-
1000AH
Code / Part Number MOQ € | THT SMD | unit price Supplier Qty € | Line Cost € Unit price
DR1206-33R-4/8 | 0,009 100 | 3 | RS | 0,004 € | 3 | 0,012
- | | | 1 | Mouser | 0,681 € | 1 | 0,681
MX-39-30-1020 | 0,339 | 5 | 1 | TME | 0,339 € | 1 | 0,339
ZL212-20KG | 0,140 | 5 | 1 | TME | 0,140 € | 1 | 0,140
- | | | 1 | Farnell | 0,373 € | 1 | 0,373
ZL263-20DG | 0,335 | 2 | 1 | TME | 0,335 € | 1 | 0,335
SMAJ51A-LF | 0,201 | 3 | 2 | Farnell | 0,144 € | 2 | 0,288
MM3Z9V1T1G | 0,020 25 | 1 | TME | 0,020 € | 1 | 0,020
- | | | 1 | Mouser | 0,664 € | 1 | 0,664
MMSZ5230BT1G | 0,033 25 | 1 | TME | 0,033 € | 1 | 0,033
16 | 275 | 61,41 €
| 1 | Farnell | 0,000 € | 1 | 0,000
| 1 | Farnell | 0,000 € | 1 | 0,000
| | Farnell | 0,000 € | 1 | 0,000
0,113 10 | 1 | TME | 0,113 € | 1 | 0,113
| | Farnell | 0,000 € | 1 | 0,000
PMB-1 | 0,072 10 | TME | 0,072 € | 2 | 0,145
SK96/84SA | 2,360 | 1 | TME | 2,360 € | 1 | 2,360
B3X5/BN661 | 0,015 100 | TME | 0,015 € | 2 | 0,029
M3X5/D7985 | 0,012 100 | TME | 0,012 € | 2 | 0,024
M3X8/D7985B | 0,018 100 | TME | 0,018 € | 5 | 0,089
B3/BN789 | 0,010 100 | TME | 0,010 € | 3 | 0,030
179020.5 | 0,143 | 5 | TME | 0,143 € | 2 | 0,286
LRS-150F-48 | 15,650 | 1 | TME | 15,650 € | 1 | 15,650
TBC-07 | 0,260 | 1 | Digikey | 0,260 € | 1 | 0,260
| 1,245 | 1 | TME | 1,245 € | 1 | 1,245
| | | | | | 20,12 €
JLCPCB | 10,942 € | 1 | 10,942
| | | 10,94 €
| | Total | 92,47 €

CRCW25124K70FKTH
BC

15EDGKN-3.5-05P-14-
1000AH

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

€

€

€

All resistors are 1% 0805 and all capacitors are X7R 0805 if not otherwise specified.

Please note that BOM does not contain ordering number for parts on reels or that which includes re-reeling fee (e.g. Farnell). Take also into account that total cost is higher because min. quantity (MOQ) for many parts is larger then what is needed for single unit.
