eez-open/modular-psu/dcm220/BOM/EEZ DIB DCM220 r2B8 BOM.pdf

EEZ DIB DCM220 BOM (r2B8, 2020-04-12) Project source code at https://github.com/eez-open/modular-psu
Farnell / Element14 # Unit price Qty Part name Package Reference designator Code Part Number MOQ € | Digi-Key Unit price Part Number MOQ € | Mouser Unit price Part Number MOQ €
| | 603-C1206KRX7RAB B103
C0805C331J5GAC TU | | 80-C0805C331J5G
| | 963-LMK316ABJ226 ML-T
C15, C19, C23, C34, C35, VJ0805Y103JXXP C66, C86 W1BC | | 710-885012207122
| | C0805C330K5G ACTU
VJ0805A102JXAC W1BC | | 710-885012007040
| | 603-CC805MKX7R7B B105
C39, C41, C42, C43, C44, GRM2165C1H472J C67, C87 A01D | | 810-C2012C0G1H47 2J-1
| | 963-EMK316B7475M L-T
Ø8mm, low ESR | | 667-EEE-FK1H470P
| | 80-C0805C101K5G
GRT31CR61H106 KE01L | | 810-C3216X7R1HK1 60AC
| | 963-EMK212B7224K G-T
MC1210X226K250 CT | | 603-CC121KKX7R8B B226
| | 80-C1206C225M5R ECLR
EEEFK1V470P EEEFK1V470P | | 667-EEE-FK1V470P
| | UVZ1E102MPD1 CM
MC0805N471J500 CT | | 710-885012007038
1 | 7 10n/200V | 1206 | 2812560 | 885342207005 | 0,078 | 5 | 311-4491-1-ND | 0,150 | 10 | 0,129 10
2 | 1 330p | C0G, 0805 | C11 | 1414686 | 0,054 10 | 1276-1189-1-ND | 0,049 | 10 | 0,036 10
3 | 3 22u | 1206, 10V | C12, C55, C75 | 2112754 | 0,616 | 5 | 1276-1287-1-ND | 0,265 | 10 | 0,155 10
4 | 7 10n | 0805 | 2896555 | 0,065 10 | 490-7194-1-ND | 0,017 | 10 | 0,036 10
5 | 1 33p | C0G, 0603 | C16 | 1759197 | 0,042 10 | 1276-1105-1-ND | 0,048 | 10 | 0,036 10
6 | 1 1n | 0805 | C36 | 2896470 | 0,044 10 | 732-7858-1-ND | 0,055 | 10 | 0,052 10
7 | 5 1u | 0805 | C38, C53, C57, C73, C77 | 2896566 | 0,084 | 5 | 587-1283-1-ND | 0,090 | 10 | 0,062 10
8 | 7 4n7 | C0G, 0805 | 1828942 | 0,184 10 | 732-12255-1-ND | 0,162 | 10 | 0,072 10
9 | 6 4u7 | 1206 | C4, C5, C14, C29, C49, C70 1907356 | 0,240 | 5 | 1276-2970-1-ND | 0,199 | 10 | 0,129 10
10 | 2 EEEFK1H470 | C46, C68 | 9695931 | EEEFK1H470P | 0,419 | 1 | PCE3815CT-ND | 0,590 | 1 | 0,524 | 1
11 | 2 100p | C0G, 0805 | C48, C69 | 2896861 | 0,023 10 | 399-15000-1-ND | 0,019 | 10 | 0,032 10
12 | 4 10u | 1210, 50V | C50, C52, C71, C72 | 2672214 | 0,684 | 5 | 1276-6736-1-ND | 0,184 | 10 | 0,597 10
13 | 2 220n | 0805 | C54, C74 | 2320828 | 0,087 | 5 | 1276-6477-1-ND | 0,520 | 10 | 0,059 10
14 | 6 22u | 1210, 25V | C59, C60, C79, C80 | 2320935 | 1,490 | 1 | 1276-3373-1-ND | 0,369 | 10 | 0,777 10
15 | 3 2u2 | 1206, 50V | C6, C9, C21 | 2991428 | 0,181 | 5 | 1276-2723-1-ND | 0,132 | 10 | 0,106 10
16 | 2 | ECAPSMD8.3MM/HA0 | C61, C81 | 9695850 | 0,368 | 1 | PCE3842CT-ND | 0,460 | 1 | 0,445 | 1
17 | 2 | C62, C82 | 9451226 | 0,388 | 1 | 93-1305-ND | 0,500 | 1 | 0,376 | 1
18 | 2 470p | 0805 | C64, C84 | 1759217 | 0,061 10 | 732-7837-1-ND | 0,059 | 10 | 0,056 10
19 | 2 33n | 0805 | C65, C85 | 2627479 | 0,046 10 | 1276-1796-1-ND | 0,057 | 10 | 0,036 10

C1, C2, C3, C56, C63, C76, C83

MC1206X226M100
CT

MC0805N330J500
CT

VJ0805Y105KXXT
W1BC

C3216X7R1E475K
160AC

C0805C101JAGAC
TU

MC0805B224J250
CT

C1206C225K5REC
TU
UVZ1E102MPD | THT; Ø10mm: RM5 | MCGPR25V108M1 0X21

MC0805B333K250
CT

710-
885012207069

# Qty Part name | RS Components | TME | Price calculation for 1 set

Unit price Code Part Number MOQ € | Unit price Code / Part Number MOQ € | THT SMD | | Line Cost €
| VJ1206Y103KXCTW1 BC
| 0805N331J500C T

1 7 10n/200V

2 1 330p

3 3 22u

4 7 10n

5 1 33p

6 1 1n

7 5 1u

8 7 4n7

9 6 4u7

10 2 EEEFK1H470

11 2 100p

12 4 10u

13 2 220n

14 6 22u

15 3 2u2

16 2

17 2

18 2 470p

19 2 33n

EEEFK1V470P

| | UVZ1E102MPD
| 0805CG471J9B B | CC0805JRNPO9BN47 1

UVZ1E102MPD

669-8647 | 0,128 25 | 0,019 100 | 7 | TME | 0,019 € | 7 | 0,133
176-3198 | 0,037 200 | CL21C331JBANNNC | 0,029 100 | 1 | TME | 0,029 € | 1 | 0,029
172-1532 | 0,095 50 | CL31A226MOCLNNC | 0,083 100 | 3 | TME | 0,083 € | 3 | 0,250
464-6672 | 0,026 50 | CC0805KRX7R9103 | 0,027 100 | 7 | Digikey | 0,017 € | 7 | 0,119
264-4264 | 0,069 25 | CL21C330JBANNNC | 0,015 100 | 1 | TME | 0,015 € | 1 | 0,015
723-6408 | 0,031 100 | CL21C102JBCNNNC | 0,026 100 | 1 | TME | 0,026 € | 1 | 0,026
451-5770 | 0,028 25 | CL21B105KOFNNNE | 0,010 100 | 5 | TME | 0,010 € | 5 | 0,052
741-4529 | 0,056 100 | 0,021 100 | 7 | TME | 0,021 € | 7 | 0,147
691-1221 | 0,232 25 | 0,381 10 | 6 | Mouser | 0,129 € | 6 | 0,774
537-0590 EEEFK1H470P | 0,510 | 5 | EEEFK1H470P | 0,183 | 5 | 2 | TME | 0,183 € | 2 | 0,366
461-3997 | 0,030 50 | CL21C101JBANNNC | 0,026 100 | 2 | Digikey | 0,019 € | 2 | 0,038
103-4163 | 0,236 20 | CL31A106KBHNNNE | 0,546 10 | 4 | Digikey | 0,184 € | 4 | 0,736
103-4126 | 0,039 50 | CL21B224KAFNNNE | 0,022 100 | 2 | TME | 0,022 € | 2 | 0,044
766-1182 | 0,343 10 | CL32A226KAJNNNE | 0,158 10 | 6 | TME | 0,158 € | 6 | 0,948
184-3509 | 0,151 10 | CL31B225KBHNNNE | 0,029 50 | 3 | TME | 0,029 € | 3 | 0,086
537-0657 EEEFK1V470P | 0,422 | 1 | EEEFK1V470P | 0,130 | 5 | 2 | TME | 0,130 € | 2 | 0,260
845-4685 UVZ1E102MPD | 0,353 25 | 0,250 | 2 | TME | 0,250 € | 2 | 0,500
378-700 | 0,040 25 | 0,024 100 | 2 | TME | 0,024 € | 2 | 0,048
135-6639 | 0,021 100 | CC0805KRX7R9333 | 0,016 100 | 2 | TME | 0,016 € | 2 | 0,032

Best
Supplier

Lowest
unit price
€

Order
Qty

CC1206KRX7R
ABB103

LMK316ABJ226
KL

08055C103KAT
2A
C0805C330J5G
ACTU
GRM2195C1H1
02JA01D
C0805C105K4R
ACTU
C2012C0G1H47 2J060AA | GRM2165C1H472JA0 1D
| GCM31CR71E475KA5 5L

C1206C475K3R
ACTU

CC0805JRNP09
BN101
UMK316BBJ106
KL-T

UMK212B7224K
G-T

CL32A226KAJN
NNE

UMK316B7225K
LHT

08051C333KAT
2A

# Qty Part name Package Reference designator Code Part Number MOQ € | Part Number Unit price MOQ € | Part Number Unit price MOQ Unit price €

C7, C8, C10, C17, C18, C20, C0603C104K4RAC C24, C26, C27, C28, C30, 7081 C31, C37, C40, C45, C47, C51 | | 80-C0603C104M4R
| RB160MM-60CT-ND | 755-RB160MM-60TR
| | 81-BLM18AG102SH 1D
| SI8662AB-B-IS1-ND | 634-SI8662AB-B-IS1
| MC33272ADR2G OSCT-ND | 863-MC33272ADR2G
| LT3763EFE#PBF -ND | 584-LT3763EFE#PBF
| MC33274ADR2G OSCT-ND | 863-MC33274ADR2G
| | TPS54060DGQR
| SI8641AB-B-IS1-ND | 634-SI8641AB-B-IS1
| | 511-M24C32-WMN6P
LP2985-33DBVR LP2985A-33DBVTE4 . | | 595-LP2985-33DBVR
| | HC2G04GW125
STM32F373C8T6 STM32F373C8T6 | | 511-STM32F373C8T 6
| | 771-TL431BIDBZR21 5

THT, PCB terminal; 4.8mm

20 | 17 100n | 0603 | 2522597 | 0,011 10 | 490-4774-1-ND | 0,029 100 | 0,007 100
21 | 8 SKL16 | SOD-123 | 2673070 | RB160MM-60TR | 0,282 | 5 | 0,264 | 10 | 0,233 10
22 | 1 BLM18AG102SH1D | 0603 | FB1 | 1669708 | MMZ1608Y102B | 0,072 10 | 490-7809-1-ND | 0,052 | 50 | 0,063 10
23 | 1 Si8662AB-B-IS1 | SOIC-16 | IC1 | 2423351 | SI8662AB-B-IS1 | 1,850 | 1 | | 1,920 | 1 | 1,760 | 1
24 | 1 MC33272ADR2G | SOIC-8 | IC10 | 2531389 | MC33272ADR2G | 0,854 | 1 | | 0,910 | 1 | 0,865 | 1
25 | 2 LT3763EFE#PBF | TSSOP-28 | IC11, IC13 | - | | | | | 4,950 | 1 | 4,830 | 1
26 | 1 MC33274ADR2G | SOIC-14 | IC12 | 2531387 | MC33274ADR2G | 1,010 | 1 | | 1,190 | 1 | 1,020 | 1
27 | 1 | MSOP-10 | IC2 | 1710820 | TPS54060DGQ . | 3,030 | 1 | 296-37148-1-ND | 2,630 | 1 | 2,490 | 1
28 | 1 Si8641AB-B-IS1 | SOIC-16 | IC3 | 2423288 | Si8641AB-B-IS1 | 1,460 | 1 | | 1,530 | 1 | 1,410 | 1
29 | 1 M24C32-WMN6P | SOIC-8 | IC4 | 1224413 | M24C32-WMN6P | 0,212 | 5 | - | | | 0,210 | 1
30 | 1 | SOT-23-5 | IC5 | 1053660 | | 0,610 | 1 | 296-18476-1-ND | 0,540 | 1 | 0,507 | 1
31 | 1 | IC6 | 2777732 | 0,283 | 5 | 1727-6045-1-ND | 0,274 | 10 | 0,248 10
32 | 1 | LQFP-48 | IC8 | 2333274 | | 4,420 | 1 | 497-13306-ND | 3,940 | 1 | 3,840 | 1
33 | 1 TL431BIDBZR | SOT-23 | IC9 | 2095470 | TL431BCDBZR | 0,310 | 5 | 296-18866-1-ND | 0,305 | 10 | 0,342 10
34 | 1 4907 | J1 | - | 36-4907-ND | 0,260 | 1 | 534-4907 | 0,257 | 1
35 | 2 571-0500 | J2, J4 | 1101127 | 571-0500-01 | 1,720 | 5 | - | 164-6219 | 2,040 | 1
36 | 2 571-0100 | J3, J5 | 1101128 | 571-0100-01 | 1,740 | 5 | - | 164-6218 | 1,840 | 1
37 | 1 RN112-4-02-0M7 | | L1 | - | | | | 817-2100-ND | 1,560 | 1 | 1,400 | 1
38 | 2 125CDMCCDS-330MC | Power inductor | L2, L4 | 2211631 | 7443551331 | 3,930 | 1 | 308-2568-1-ND | 1,510 | 1 | 1,590 | 1
39 | 2 HPI0630-3R3 | Power inductor | L3, L5 | 1741325 | | 1,940 | 5 | | 0,510 | 1 | 0,510 | 1
40 | 2 WP42WUM/EGW | | LED1, LED2 | - | | | | 754-1718-ND | 0,930 | 1 | 0,926 | 1
41 | 2 NTCS0805E3103JMT | NTC 0805 | NTC1, NTC2 | 2103177 | 0,399 10 | BC2292CT-ND | 0,490 | 1 | 0,353 10
42 | 2 | SOT-223 | Q1, Q6 | 2803380 | 0,378 | 5 | 0,372 | 10 | 0,333 10

D1, D2, D3, D4, D6, D8, D9, D11

TPS54060DGQ | 595-
74HC2G04GW,125 | 74HC2G04GW,125 | 771-

THT, Ø4 mm terminal; red
THT, Ø4 mm terminal; black
| | 631-RN112-4-02-0M7
| | 851-125CDMCCDS33 0MC
| 445-180834-1-ND | 810-VLS6045AF-3R3N
THT, dual (green/red) 3 mm LED | | 604-WP42WUM/ EGW
| | 594-2381-615-53103
BSP716NH6327XTSA1 BSP716NH6327XT SA1 | BSP716NH6327 XTSA1CT-ND | 726-BSP716NH6327 XTSA

THT, Current-compensated
Choke

IHLP2020CZER3R
3M11

NTCS0805E3103J
MT

# Qty Part name

20 17 100n

21 8 SKL16

22 1 BLM18AG102SH1D

23 1 Si8662AB-B-IS1

24 1 MC33272ADR2G

25 2 LT3763EFE#PBF

26 1 MC33274ADR2G

27 1

28 1 Si8641AB-B-IS1

29 1 M24C32-WMN6P

30 1

31 1

32 1

33 1 TL431BIDBZR

34 1 4907
35 2 571-0500
36 2 571-0100
37 1 RN112-4-02-0M7

38 2 125CDMCCDS-330MC

39 2 HPI0630-3R3

40 2 WP42WUM/EGW

41 2 NTCS0805E3103JMT

42 2

TPS54060DGQ

LP2985-33DBVR

74HC2G04GW,125

STM32F373C8T6

BSP716NH6327XTSA1

Code Part Number MOQ € | Code / Part Number Unit price MOQ € | THT SMD | Line Cost € Unit price
| VJ0603Y104KXJ AT

Best
Supplier

Lowest
unit price
€

Order
Qty
393-6952 | 0,069 25 | CL10B104KA8NNNC | 0,098 100 | 17 | Mouser | 0,007 € 17 | 0,119
124-6774 RB160MM-60TR | 0,230 40 | SKL16-DIO | 0,105 | 5 | 8 | TME | 0,105 € | 8 | 0,840
839-0803 | 0,043 100 | BLM18AG102SH1D | 0,016 50 | 1 | TME | 0,016 € | 1 | 0,016
823-2062 Si8662AB-B-IS1 | 1,870 | 5 | - | | | 1 | Mouser | 1,760 € | 1 | 1,760
773-7778 | 0,865 | 1 | MC33272ADR2G | 0,570 | 1 | 1 | TME | 0,570 € | 1 | 0,570
- | | | | | | 2 | Mouser | 4,830 € | 2 | 9,660
773-7787 | 1,010 | 2 | MC33274ADR2G | 0,740 | 1 | 1 | TME | 0,740 € | 1 | 0,740
698-9079 TPS54060DGQ | 2,680 | 1 | - | | | 1 | Mouser | 2,490 € | 1 | 2,490
823-2000 Si8641AB-B-IS1 | 1,496 | 5 | - | | | 1 | Mouser | 1,410 € | 1 | 1,410
686-2453 | 0,180 25 | M24C32-WMN6P | 0,165 | 3 | 1 | TME | 0,165 € | 1 | 0,165
660-6733 LP2985-33DBVT | 0,737 | 1 | LP2985-33DBVR | 0,362 | 1 | 1 | TME | 0,362 € | 1 | 0,362
153-2919 | 0,235 50 | 74HC2G04GW.125 | 0,138 | 5 | 1 | TME | 0,138 € | 1 | 0,138
795-9164 | 2,060 | 1 | - | | | 1 | RS | 2,060 € | 1 | 2,060
797-4826 | 0,259 | 2 | TL431BIDBZR | 0,237 | 3 | 1 | TME | 0,237 € | 1 | 0,237
- | 61-1537-11/0031 | 0,049 10 | 1 | TME | 0,049 € | 1 | 0,049
103-6511 571-0500 | 1,216 | 5 | 571-0500 | 0,620 | 3 | 2 | TME | 0,620 € | 2 | 1,240
103-6527 571-0100 | 1,334 | 5 | 571-0100 | 0,620 | 3 | 2 | TME | 0,620 € | 2 | 1,240
- | | | - | | | 1 | Mouser | 1,400 € | 1 | 1,400
- | | | - | | | 2 | Digikey | 1,510 € | 2 | 3,020
- | | | HPI0630-3R3 | 0,335 | 1 | 2 | TME | 0,335 € | 2 | 0,670
- | | | L-42WUM/1EGWT | 0,501 | 1 | 2 | TME | 0,501 € | 2 | 1,002
179-3950 | 0,250 250 | NTCS0805E3103JMT | 0,113 15 | 2 | TME | 0,113 € | 2 | 0,226
- | | | | 0,201 | 3 | 2 | TME | 0,201 € | 2 | 0,402

BLM18AG102S
H1D

MC33272ADR2
G

MC33274ADR2
G

M24C32-
WMN6P

74HC2G04GW,1
25
STM32F373C8T
6

TL431BIDBZR,2
15

NTCS0805E310
3JMT
BSP716NH6327XTSA
1

# Qty Part name Package Reference designator Code Part Number MOQ € | Part Number Unit price MOQ € | Part Number Unit price MOQ Unit price €

| NTD5867NLT4G OSCT-ND | 863-NTD5867NLT4G
BSS205NH6327XTSA1 BSS205NH6327XT SA1 | BSS205NH6327 XTSA1CT-ND | BSS205NH6327 XTSA1
| BSS84PH6433X TMA1CT-ND | 726-BSS84PH6327X TSA2
R10, R11, R12, R13, R14, RC0805FR-0710KL R15, R16, R17, R18, R20, TX_PU | 311-10.0KCRCT-ND | 603-RC0805FR-0710KL
| 311-10.0CRCT-ND | 71-CRCW080510R0 FKEAC

R21, R22, R41, R48, R65, MCWR08X3301FT R72 L

| RMCF0805FT12 0RCT-ND | 71-CRCW0805120R FKEAC
R3, R43, R44, R67, R68, MCWR08X4702FT R76, R77 L | | 603-RC0805FR-0747KL
| | RCG080520K0F KEA
R31, R33, R47, R55, R57, MCWR08X1202FT R71 L | | 71-CRCW080512K0 FKEA
| | 279-RLP73V3AR012 FTDF
| | 603-RC0805FR-0730KL
| RMCF0805FT10 0KCT-ND | 71-CRCW0805100K FKEAC
MCWR08X3601FT L | RMCF0805FT3K 60CT-ND | 603-RT0805FRE073K 6L
| 311-11.8KCRCT-ND | 603-RC0805FR-0711K8L
| | 71-CRCW080515K0 FKEBC
| ND | 603-RC0805FR-072K2L
R7, R9, R29, R40, R42, R53, R64, R66 | 311-86.6KCRCT-ND | 603-RT0805FRE0786 K6L
| | 652-CR0805FX-3303ELF
| CAY16-330J4LFCT-ND | 652-CAY16-330J4LF
43 | 4 NTD5867NLT4G | DPAK | Q2, Q3, Q7, Q8 | 1879964 | NTD5867NLT4G | 0,493 10 | 0,458 | 10 | 0,430 10
44 | 2 | SOT-23 | Q4, Q9 | 2480648 | 0,257 | 5 | 0,274 | 10 | 0,236 10
45 | 2 BSS84P | SOT-23 | Q5, Q10 | 1056526 | 0,224 | 5 | 0,314 | 10 | 0,196 10
46 | 11 10K | 0805 | 9237755 | 0,022 10 | 0,039 | 10 | 0,014 10
47 | 9 10R | 0805 | 2447556 | 0,007 10 | 0,064 | 10 | 0,047 10
48 | 6 3K3 | 0805 | 2447651 | 0,010 10 | A129755CT-ND | 0,045 | 10
49 | 3 120R | 0805 | R23, R49, R73 | 2447561 | 0,009 10 | 0,020 | 10 | 0,037 10
50 | 7 47K | 0805 | 2447664 | 0,009 10 | RHM47KKCT-ND | 0,036 | 10 | 0,014 10
51 | 4 20K | 0805 | R30, R32, R54, R56 | 2447603 | 0,009 10 | A126349CT-ND | 0,047 | 10 | 0,034 50
52 | 6 12K | 0805 | 2447563 | 0,010 10 | A126337CT-ND | 0,047 | 10 | 0,058 10
53 | 2 R012/2W | 2512 | R34, R58 | 2483605 | TLM3AER012JTE | 0,161 10 | YAG2164CT-ND | 0,491 | 10 | 0,347 10
54 | 2 30K | 0805 | R39, R63 | 2303701 | ERJ6ENF3002V | 0,058 10 | P30.0KCCT-ND | 0,085 | 10 | 0,014 10
55 | 2 100K | 0805 | R45, R69 | 2447551 | 0,010 10 | 0,024 | 10 | 0,040 10
56 | 2 3K6 | 0805 | R46, R70 | 2447652 | 0,010 10 | 0,010 100 | 0,017 100
57 | 2 11K8 | 0805 | R50, R74 | 2138981 | 0,040 10 | 0,037 | 10 | 0,010 100
58 | 2 15K | 0805 | R51, R75 | 1099808 | WCR0805-15KFI | 0,019 10 | A126341CT-ND | 0,041 | 10 | 0,013 10
59 | 7 2K2 | 0805 | 9237534 | 0,037 10 | 0,039 | 10 | 0,026 10
60 | 8 86K6 | 0805 | 2303750RL ERJ6ENF8662V | 0,058 10 | 0,036 | 10 | 0,056 10
61 | 1 330K | 0805 | R8 | 2447637 | 0,010 10 | A126361CT-ND | 0,046 | 10 | 0,013 10
62 | 1 DR1206-33R-4/8 | 1206 resistor array | RN1 | 1770128 | CAY16-330J4LF | 0,069 10 | 0,090 | 1 | 0,085 | 1

BSS84PH6327XTS
A2

R2, R4, R5, R28, R35, R36, R52, R59, R60

MCWR08X10R0FT
L

MCWR08X1200FT
L

MCWR08X2002FT
L

MCWR08X1003FT
L

CRCW080511K8F
KEA.

R6, R24, R25, R26, R27,
R38, R62
RC0805FR-072K2L | 311-2.20KCRCT-

MCWR08X3303FT
L

# Qty Part name

43 4 NTD5867NLT4G

44 2

45 2 BSS84P

46 11 10K

47 9 10R

48 6 3K3

49 3 120R

50 7 47K

51 4 20K

52 6 12K

53 2 R012/2W

54 2 30K

55 2 100K

56 2 3K6

57 2 11K8

58 2 15K

59 7 2K2

60 8 86K6

61 1 330K

62 1 DR1206-33R-4/8

BSS205NH6327XTSA1

Code Part Number MOQ € | Code / Part Number Unit price MOQ € | THT SMD | Line Cost € Unit price

Best
Supplier

Lowest
unit price
€

Order
Qty
719-2901 NTD5867NLT4G | 0,524 | 5 | NTD5867NLT4G | 0,310 | 3 | 4 | TME | 0,310 € | 4 | 1,240
892-2374 | 0,108 100 | 0,097 10 | 2 | TME | 0,097 € | 2 | 0,194
- | BSS84P | 0,060 10 | 2 | TME | 0,060 € | 2 | 0,120
125-1189 CRG0805F10K | 0,002 100 | 0805S8F1002T5E | 0,014 100 | 11 | RS | 0,002 € 11 | 0,022
223-0152 CRG0805F10R | 0,019 50 | 0805S8F100JT5E | 0,015 100 | 9 | Farnell | 0,007 € | 9 | 0,059
223-0499 CRG0805F3K3 | 0,027 50 | 805S8F3301T5E | 0,015 100 | 6 | Farnell | 0,010 € | 6 | 0,058
223-0304 CRG0805F120R | 0,035 50 | 0805S8F1200T5E | 0,022 100 | 3 | Farnell | 0,009 € | 3 | 0,028
679-1434 | 0,036 50 | RC0805FR-0747K | 0,022 100 | 7 | Farnell | 0,009 € | 7 | 0,066
679-1077 | 0,038 50 | RC0805FR-0720K | 0,035 100 | 4 | Farnell | 0,009 € | 4 | 0,038
223-0578 CRG0805F12K | 0,020 50 | SMD0805-12K-1% | 0,014 100 | 6 | Farnell | 0,010 € | 6 | 0,059
869-5467 | 0,204 10 | LRP12FTWRR012 | 0,145 10 | 2 | TME | 0,145 € | 2 | 0,290
- | SMD0805-30K-1% | 0,022 100 | 2 | Mouser | 0,014 € | 2 | 0,028
223-0691 CRG0805F100K | 0,028 50 | 0805S8F1003T5E | 0,015 100 | 2 | Farnell | 0,010 € | 2 | 0,019
865-4425 ERJU06F3601V | 0,039 50 | 0805S8F3601T5E | 0,007 100 | 2 | TME | 0,007 € | 2 | 0,014
679-0847 | 0,036 50 | 0805S8F1182T5E | 0,014 100 | 2 | Mouser | 0,010 € | 2 | 0,020
223-0584 CRG0805F15K | 0,023 50 | SMD0805-15K | 0,013 100 | 2 | Mouser | 0,013 € | 2 | 0,026
679-1207 | 0,039 50 | 0805S8F2201T5E | 0,022 100 | 7 | TME | 0,022 € | 7 | 0,156
- | 0,025 100 | 8 | TME | 0,025 € | 8 | 0,200
679-1272 | 0,038 50 | SMD0805-330K-1% | 0,015 100 | 1 | Farnell | 0,010 € | 1 | 0,010
522-5670 CAY16-330J4LF | 0,004 50 | DR1206-33R-4/8 | 0,009 100 | 1 | RS | 0,004 € | 1 | 0,004

BSS205NH6327
XTSA1

BSS205NH6327XTSA
1

CRCW080547K
0FKEA
CRCW080520K
0FKEA

TLM3AER012FT
E

CRCW080511K
8FKEA

CRCW08052K2
0FKEA
CRCW080586K6FKTA
BC

CRCW0805330
KFKEA

# Qty Part name Package Reference designator Code Part Number MOQ € | Part Number Unit price MOQ € | Part Number Unit price MOQ Unit price €

| SRF0703-821MCT-ND | 652-SRF0703-821M

THT, Minifit Jr. 2-pin, right angle

| | 649-77317-104-28LF
THT, 10-pin 0.1" receptacle right angled | | 710-613010243121
| ND
MM3Z9V1T1G | MM3Z9V1T1GO SCT-ND | 863-MM3Z9V1T1G
63 | 1 SRF0703-821M | 0703 | TR1 | 1852832 | SRF0703-821M | 0,827 | 1 | 0,900 | 1 | 0,681 | 1
64 | 1 39-30-1020 | X1 | 9732080 | 39-28-1023 | 0,367 | 1 | WM3800-ND | 0,530 | 1 | 538-39-28-1023 | 0,530 | 1
65 | 1 77317-104-28LF | X2 | - | | | | S2111EC-14-ND | 1,030 | 1 | | 1,540 | 1
66 | 1 DS1024-2*5R0 | X4 | 1841243 | 613010243121 | 0,910 | 1 | S9202-ND | 0,720 | 1 | | 0,950 | 1
67 | 3 SMAJ51A | SMA | 2677667 | SMAJ51A | 0,144 | 5 | 0,370 | 1 | 652-SMAJ51A | 0,463 | 1
68 | 2 | SOD-323 | ZD2, ZD4 | 2463517 | MM3Z9V1T1G | 0,124 | 5 | 0,120 | 1 | 0,108 10

Not installed
1 N.C. | 1206 | C13
3 N.C. 0805 C22, C58, C78
| | 80-C0603C104M4R
2 4p7 C0G, 0603 C32, C33 2627469 MC0603N4R7C500 0,329 10 CT | 311-1740-1-ND 0,054 10 | 710-0,072 10 885012006049
1 100n | 0603 | C25 | 2522597 | 0,011 10 | 490-4774-1-ND | 0,029 100 | 0,007 100
2 N.C. | SOD-123 | D5, D10
2 N.C. | SMA | D7, D12
1 | | IC7

1 2mm jumper THT JP1
| 279-CRGP2512F4K7

1 N.C. 0805 R19

1 N.C. | 2512 | R1 | 2081875 | ASC2512-4K7FT4 | 0,195 10 | A130729CT-ND | 0,331 | 10 | 0,180 10
2 N.C. | 1206 | R37, R61
1 DR1206-33R-4/8 | 1206 resistor array | RN2 | 1770128 | CAY16-330J4LF | 0,069 10 | 0,090 | 1 | 0,085 | 1
1 | THT | X3
1 LF XTAL026392 | XTAL; 7.5x5.1x1.4mm | Y1 | 1276696 | LFXTAL026392 | 1,250 | 1 | 1923-1009-ND | 0,850 | 1 | 0,972 | 1

Related parts and accessories
2 PMB-1 | PCB bracket; polyamide | KK1, KK2 | - | - | -
1 LRS-150F-48 | 2815982 | LRS-150F-48 | 21,150 | 1 | 1866-3328-ND | 23,460 | 1 | 709-LRS150F-48 | 23,330 | 1
1 TBC-07 | - | | | | 1866-4907-ND | 0,260 | 1 | 709-TBC-07 | 0,292 | 1

Custom made components

THT, 28-pin 0.1" header right angled

ZD1, ZD3, ZD5 | SMAJ51ALFCT-

C0603C104K4RAC
7081

TPD4E001DRLR

CAY16-
330J4LFCT-ND

652-CAY16-
330J4LF
22-23-2061

449-
LFXTAL026392B
ULK

Mean Well 48 Vdc power
module
Terminal cover for Mean Well power module

# Qty Part name

63 1 SRF0703-821M

64 1 39-30-1020

65 1 77317-104-28LF

66 1 DS1024-2*5R0

67 3 SMAJ51A

68 2

Not installed
1 N.C.
3 N.C.
1 100n

2 4p7

2 N.C.
2 N.C.
1

1 2mm jumper
| CRCW25124K70FKTH BC

1 N.C.

1 N.C.

2 N.C.
1 DR1206-33R-4/8

1

1 LF XTAL026392

Related parts and accessories 2 PMB-1
1 LRS-150F-48

1 TBC-07

Custom made components

MM3Z9V1T1G

TPD4E001DRLR

22-23-2061

Code Part Number MOQ € | Code / Part Number Unit price MOQ € | THT SMD | Line Cost € Unit price

Best
Supplier

Lowest
unit price
€

Order
Qty
- | - | 1 | Mouser | 0,681 € | 1 | 0,681
484-1883 39-28-102 | 0,354 | 5 | MX-39-30-1020 | 0,339 | 5 | 1 | TME | 0,339 € | 1 | 0,339
- | | | - | | | 1 | Digikey | 1,030 € | 1 | 1,030
826-7194 613010243121 | 0,950 | 1 | ZL263-10DG | 0,301 | 2 | 1 | TME | 0,301 € | 1 | 0,301
171-4238 SMAJ51A | 0,320 25 | SMAJ51A-LF | 0,201 | 3 | 3 | Farnell | 0,144 € | 3 | 0,432
802-4653 MM3Z9V1T1G | 0,039 200 | MM3Z9V1T1G | 0,020 25 | 2 | TME | 0,020 € | 2 | 0,041
13 | 198 | 39,90 €
| | | | 3 | Farnell | 0,000 € | 3 | 0,000
393-6952 | 0,069 25 | CL10B104KA8NNNC | 0,098 100 | 1 | Mouser | 0,007 € | 1 | 0,007
298-9315 | 0,024 25 | CL10C4R7CB8NNNC | 0,024 100 | 2 | RS | 0,024 € | 2 | 0,048
| | | 1 | Farnell | 0,000 € | 1 | 0,000
1 | Farnell | 0,000 € | 1 | 0,000
224-0424 35204K7JT | 1,370 10 | 0,113 10 | 1 | TME | 0,113 € | 1 | 0,113
522-5670 CAY16-330J4LF | 0,004 50 | DR1206-33R-4/8 | 0,009 100 | 1 | RS | 0,004 € | 1 | 0,004
1 | Farnell | 0,000 € | 1 | 0,000
148-4357 LFXTAL026392 | 0,960 10 | 16.00M-12SM | 0,950 | 1 | 1 | Digikey | 0,850 € | 1 | 0,850
- | PMB-1 | 0,072 10 | TME | 0,072 € | 2 | 0,145
106-5854 LRS-150F-48 | 21,730 | 1 | LRS-150F-48 | 15,650 | 1 | TME | 15,650 € | 1 | 15,650
- | | | TBC-07 | 0,260 | 1 | Digikey | 0,260 € | 1 | 0,260
| | | | | | | | | 16,05 €

VJ0603Y104KXJ
AT
C0603C479C5G
ACTU

Qty | Part name | Package | Reference designator | Code | Part Number | MOQ | Part Number | MOQ | Part Number | MOQ Unit price
€

Unit price
€

Unit price
€
1 PCB | -

All prices are net prices (without VAT)

All resistors are 1% 0805 and all capacitors are X7R 0805 if not otherwise specified.

2-layer 145 x 95 mm, 1 oz. Cu thickness

Please note that BOM does not contain ordering number for parts on reels or that which includes re-reeling fee (e.g. Farnell). Take also into account that total cost is higher because min. quantity (MOQ) for many parts is larger then what is needed for single unit.

# Qty Part name

1 PCB

Code Part Number MOQ € | Code / Part Number Unit price MOQ € | THT SMD | Line Cost € Unit price

Best
Supplier

Lowest
unit price
€

Order
Qty
ALLPCB | 7,387 € | 1 | 7,387
| | | 7,39 €
| | Total | 63,34 €
