eez-open/modular-psu/aux-ps/BOM/EEZ DIB AUX PS r2B2 BOM.ods

 |  |  |  |  | Farnell / Element14 |  |  |  | Digi-Key |  |  | Mouser |  |  | RS Components |  |  |  | TME |  |  |  |  | Price calculation for 1 set
# | Qty | Part name | Package | Reference designator | Code | Part Number | Unit price € | MOQ | Part Number | Unit price € | MOQ | Part Number | Unit price € | MOQ | Code | Part Number | Unit price € | MOQ | Code / Part Number | Unit price € | MOQ | THT | SMD | Best Supplier | Lowest unit price € | Order Qty | Line Cost €
1 | 1 | DB107S | SMD; DBS | B1 | 1861409 | DB107S | 0,518 | 5 | 1655-1822-1-ND | 0,410 | 1 | 750-DB107S-G | 0,434 | 1 | 917-8966 | DB107S | 0,108 | 100 | DB107S | 0,130 | 5 |  | 1 | RS | 0,108 € | 1 | 0,108
2 | 2 | 47n/400V (X2) | THT; 13x5mm; RM10 | C1, C2 | 2728564 | B32921C3473K000 | 0,452 | 1 | 399-11478-ND | 0,319 | 10 | 871-B32921C3473K | 0,264 | 10 | 882-9483 | B32921C3473M000 | 0,272 | 25 | MKP-X2-47NR10/310 | 0,077 | 10 | 2 |  | TME | 0,077 € | 2 | 0,154
3 | 1 | 2n2/1kV | 1210 or 1206 | C13 | 1855965 | MC1210B222K102CT | 0,496 | 5 | 490-12018-1-ND | 0,502 | 10 | 710-885342208019 | 0,121 | 10 | 723-6492 | GRM31BR73A222KW01L | 0,246 | 25 | 1206B222K102CT | 0,030 | 50 |  | 1 | TME | 0,030 € | 1 | 0,030
4 | 2 | UCY2G6R8MPD | ECAP5G_10.5MM | C14, C15 | 1831309 | 400BXC6R8MEFC10X16 | 0,868 | 1 | 493-13319-1-ND | 0,730 | 1 | 647-UCY2G6R8MPD | 0,629 | 1 | 739-4551 | UCA2G6R8MPD | 1,008 | 1 | UCY2G6R8MPD | 0,240 | 5 | 2 |  | TME | 0,240 € | 2 | 0,480
5 | 3 | 3n3 | C-EUC0805 | C16, C19, C23 | 1856458 | MCSH21B332K250CT | 0,039 | 5 | 732-8036-1-ND | 0,033 | 10 | 710-885012207063 | 0,072 | 10 | 237-7009 | GRM216R71H332KA01D | 0,060 | 50 | VJ0805Y333KXACW1BC | 0,023 | 100 |  | 3 | TME | 0,023 € | 3 | 0,069
6 | 1 | 470u/16V | THT; Ø8; RM3.5 | C17 | 2346502 | 16PK470MEFC8X11.5 | 0,206 | 5 | 493-1286-ND | 0,215 | 10 | 647-UVZ1C471MPD1TD | 0,194 | 10 | 845-4666 | UVZ1C471MPD | 0,215 | 25 | UVZ1C471MPD | 0,140 | 5 | 1 |  | TME | 0,140 € | 1 | 0,140
7 | 2 | 4u7 | 1206 | C18, C25 | 1907356 | C3216X7R1E475K160AC | 0,240 | 5 | 1276-2970-1-ND | 0,199 | 10 | 963-EMK316B7475ML-T | 0,129 | 10 | 691-1221 | C1206C475K3RACTU | 0,232 | 25 | GCM31CR71E475KA55L | 0,381 | 10 |  | 2 | Mouser | 0,129 € | 2 | 0,258
8 | 1 | UVZ1C471MPD | ECAPPANASONIC_H | C20 | 9695850 | EEEFK1V470P | 0,344 | 1 | PCE3842CT-ND | 0,312 | 10 | 667-EEE-FK1V470P | 0,238 | 10 | 537-0657 | EEEFK1V470P | 0,394 | 5 | EEEFK1V470P | 0,130 | 5 |  | 1 | TME | 0,130 € | 1 | 0,130
9 | 1 | CY1Y-470P | C-EUCY | C21 | 2860164 | VY1471K31Y5UQ6TV0 | 0,220 | 1 | BC2372-ND | 0,206 | 10 | 72-VY1471M31Y5UQ63V0 | 0,186 | 10 | 736-8858 | VY1471K31Y5UQ6TV0 | 0,100 | 10 | CY1Y-470P | 0,099 | 10 | 1 |  | TME | 0,099 € | 1 | 0,099
10 | 1 | 1500u/16 | THT; Ø12.5; RM5 | C24 | 2465622 | 860010275018 | 0,489 | 1 | 732-8920-1-ND | 0,420 | 1 | 647-UHD1C152MHD | 0,456 | 10 | 852-5011 | UPM1C152MHD1TO | 0,690 | 1 | UPW1C152MHD | 0,219 | 25 | 1 |  | TME | 0,219 € | 1 | 0,219
11 | 2 | 33n | 0805 | C27, C29 | 1414688 | C0805C333K5RACTU | 0,051 | 10 | 1276-1796-1-ND | 0,068 | 10 | 77-VJ0805Y333JXAPBC | 0,020 | 50 | 652-0982 | VJ0805Y333KXAAT | 0,066 | 25 | CL21B333KBANNNC | 0,035 | 100 |  | 2 | Mouser | 0,020 € | 2 | 0,040
12 | 1 | 18p | 0603, C0G | C28 | 2896373 | VJ0603A180JXACW1BC | 0,016 | 10 | 1276-1089-1-ND | 0,048 | 10 | 80-C0603C180J5G7867 | 0,023 | 10 | 147-415 | C0603C180J5GACTU | 0,032 | 50 | CL10C180JB8NNNC | 0,015 | 100 |  | 1 | TME | 0,015 € | 1 | 0,015
13 | 3 | 1u | 0805 | C3, C4, C5 | 2896566 | VJ0805Y105KXXTW1BC | 0,084 | 5 | 587-1283-1-ND | 0,090 | 10 | 603-CC805MKX7R7BB105 | 0,062 | 10 | 451-5770 | C0805C105K4RACTU | 0,028 | 25 | CL21B105KOFNNNE | 0,010 | 100 |  | 3 | TME | 0,010 € | 3 | 0,031
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
