eez-open/modular-psu/dcp505/Images/EEZ_DIB_DCP505_PCB_parts.png

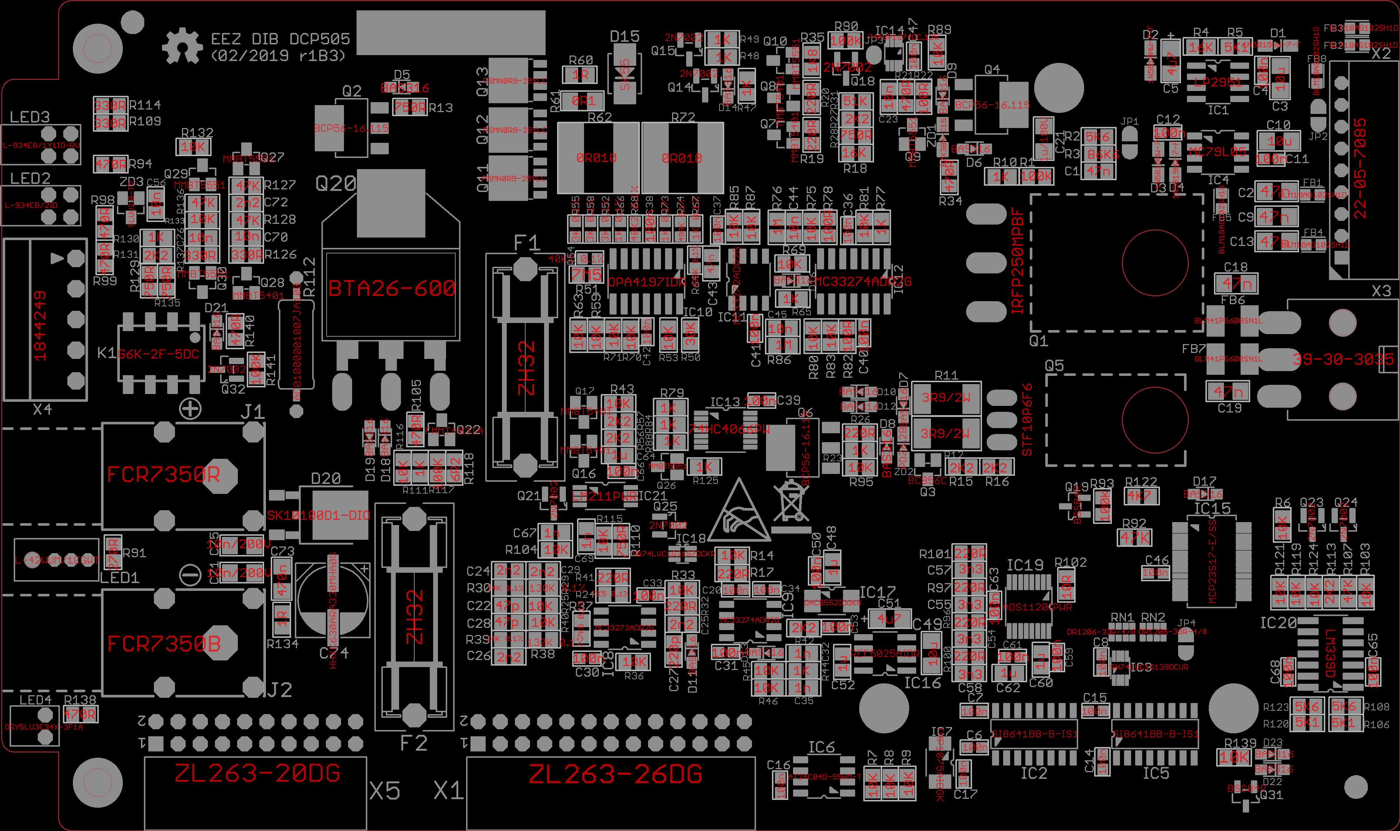
dcp505/Images/EEZ_DIB_DCP505_PCB_parts.png
