eez-open/modular-psu/mcu/Images/EEZ_DIB_MCU_parts.png

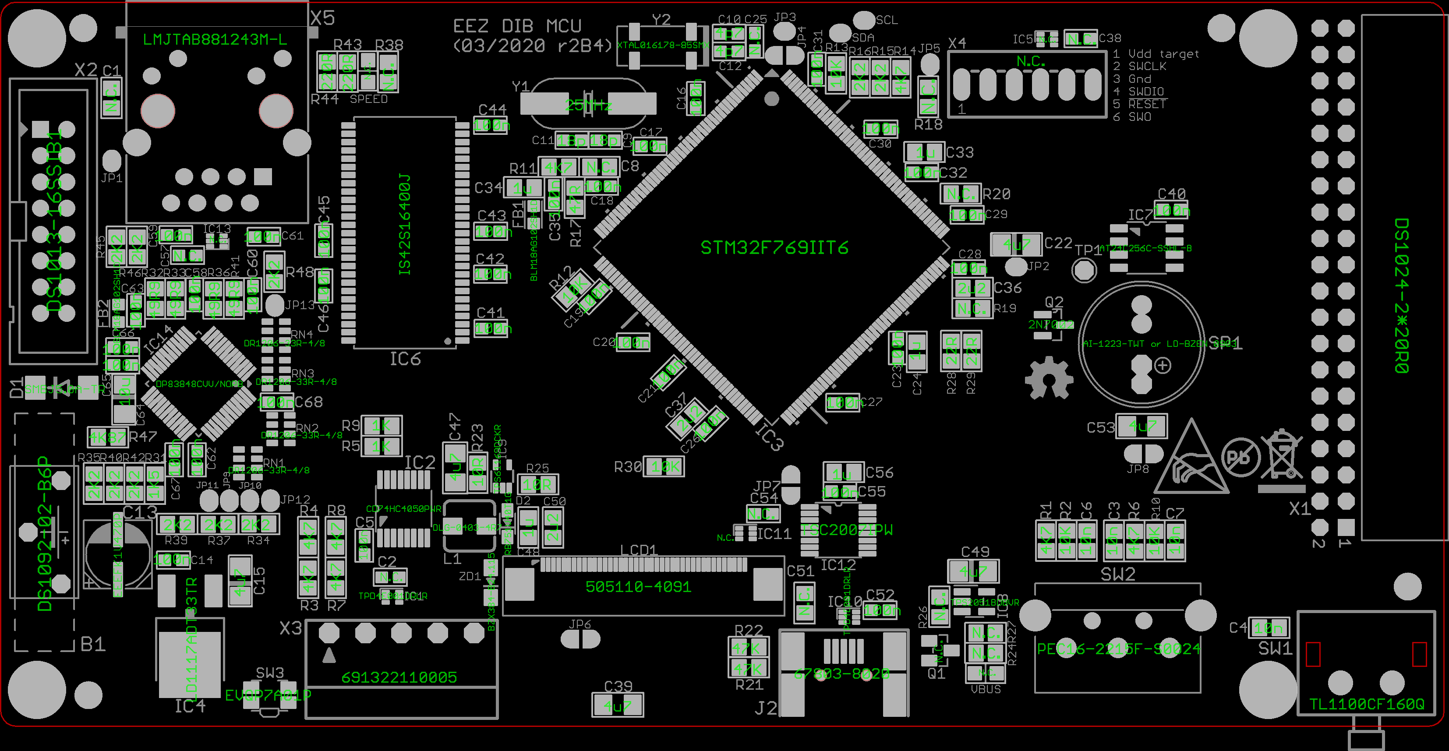
mcu/Images/EEZ_DIB_MCU_parts.png
