eez-open/modular-psu/mcu/Images/EEZ_DIB_MCU_parts_top.png

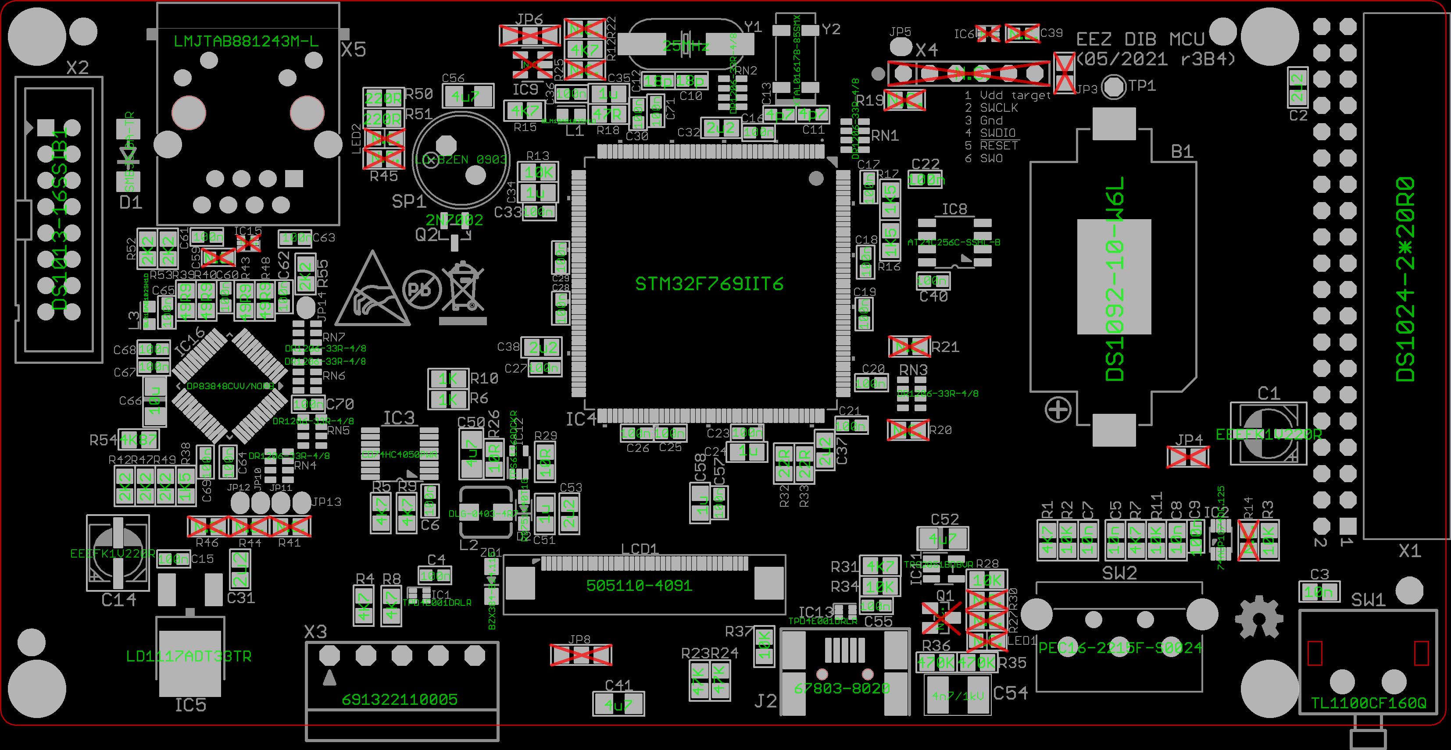
mcu/Images/EEZ_DIB_MCU_parts_top.png
