eez-open/modular-psu/docs/user manual/EEZ BB3 user manual - last page.odt

For more info visit: www.envox.eu

File repository: https://github.com/eez-open

Version: 1.09

Date: 2022-11-29

EEZ BB3 user manual - last page
