eez-open/modular-psu/docs/user manual/EEZ BB3 user manual - start page.odt

| Ver. 1.09 – 11/2022 www.envox.eu – github.com/eez-open

EEZ BB3 user manual - start page
