eez-open/modular-psu/docs/user manual/German/EEZ BB3 Benutzerhandbuch - last page.odt

Für weitere Informationen besuchen Sie: www.envox.hr/eez

Projektarchiv: https://github.com/eez-open

Version: 1.04

Datum: 2021-02-11

EEZ BB3 Benutzerhandbuch - last page
