eez-open/modular-psu/docs/user manual/German/EEZ BB3 Benutzerhandbuch - start page.odt

| Ver. 1.04 – 02/2021 www.envox.hr – github.com/eez-open

EEZ BB3 Benutzerhandbuch - start page
