eez-open/modular-psu/enclosure/EU pallet box stacking for assembled units.png

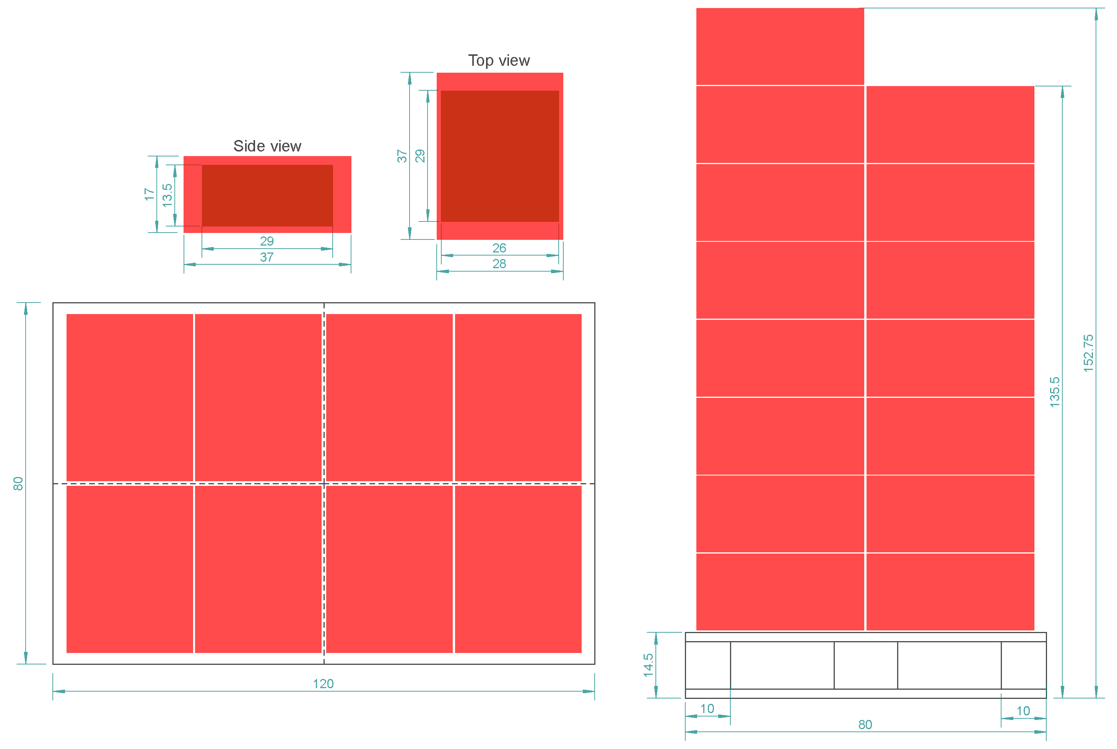
enclosure/EU pallet box stacking for assembled units.png
