eez-open/modular-psu/dcp505/Spice/Auto-ranging/EEZ 3-level current auto-ranging results.png

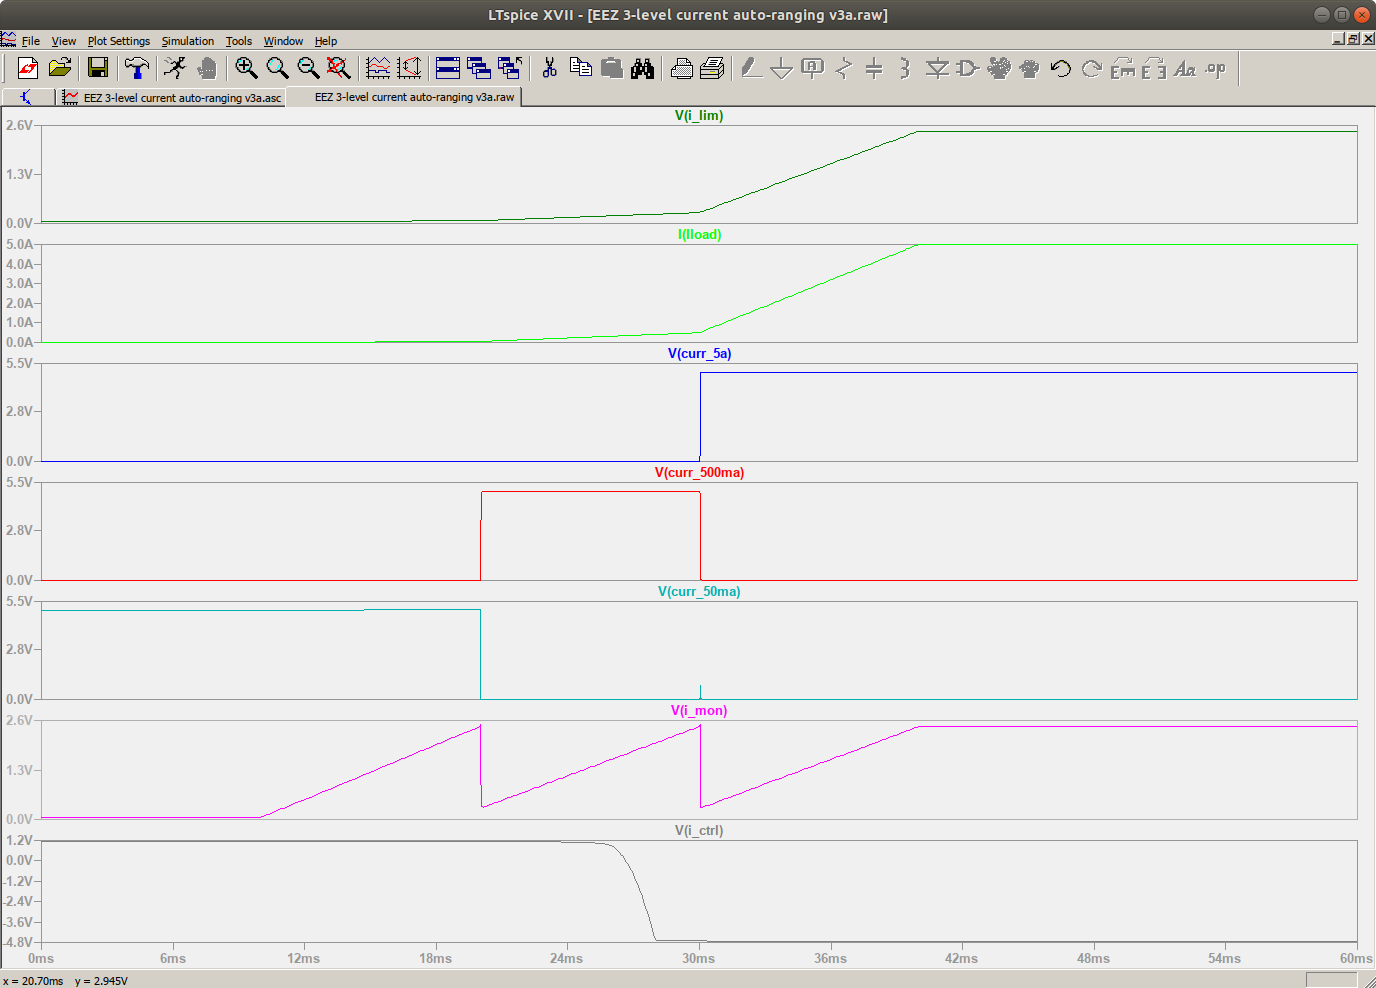
dcp505/Spice/Auto-ranging/EEZ 3-level current auto-ranging results.png
