eez-open/modular-psu/dcp405/EEZ DIB DCP405 r3B3.pdf

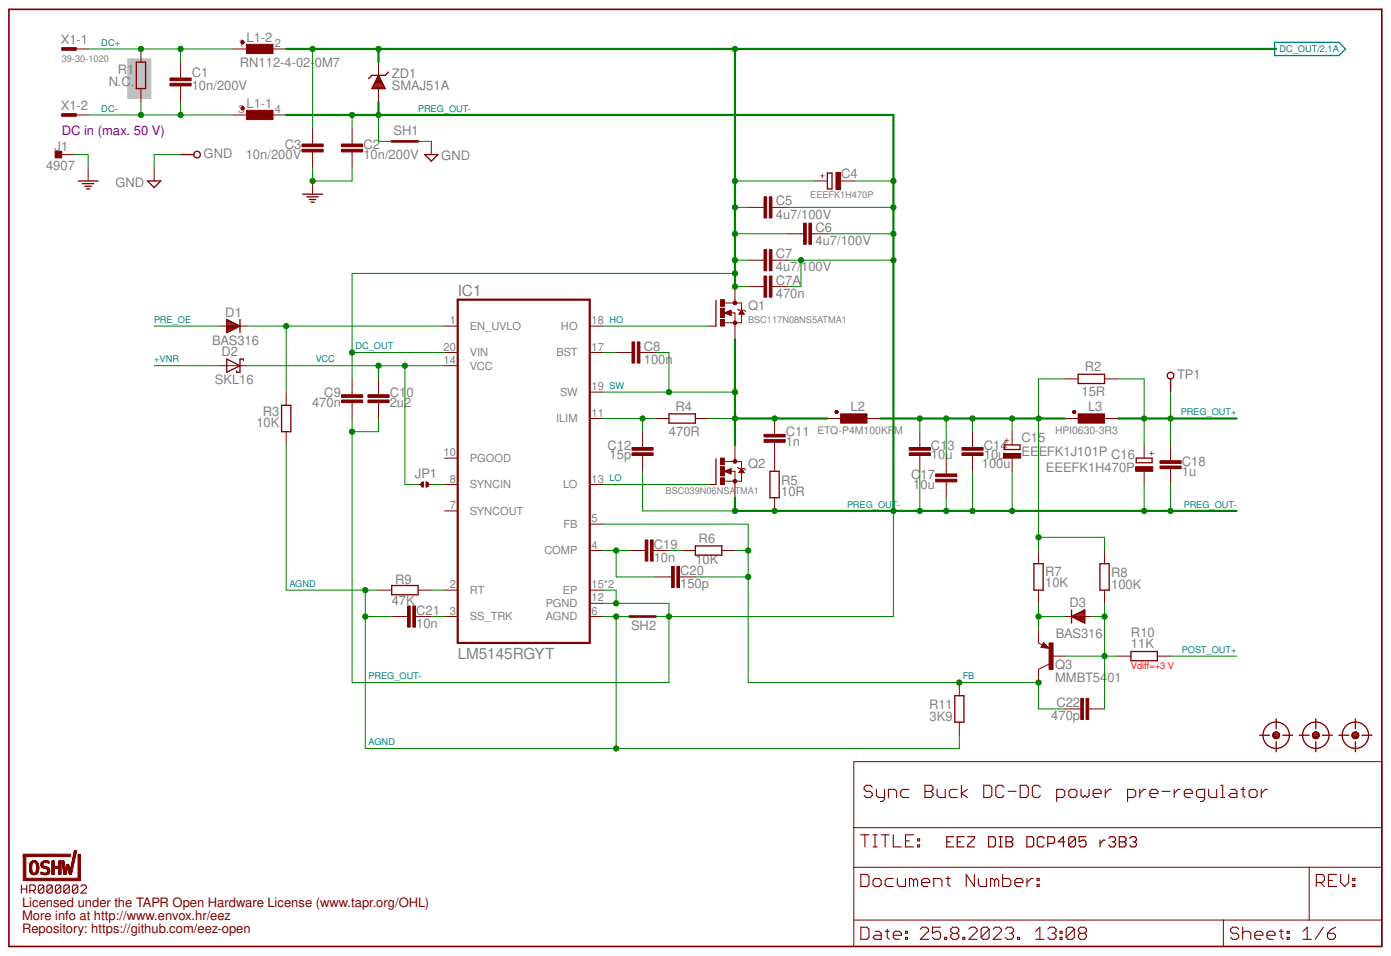
[picture p518: page 1]

Licensed under the TAPR Open Hardware License (www.tapr.org/OHL)
Repository: https://github.com/eez-open More info at http://www.envox.hr/eez

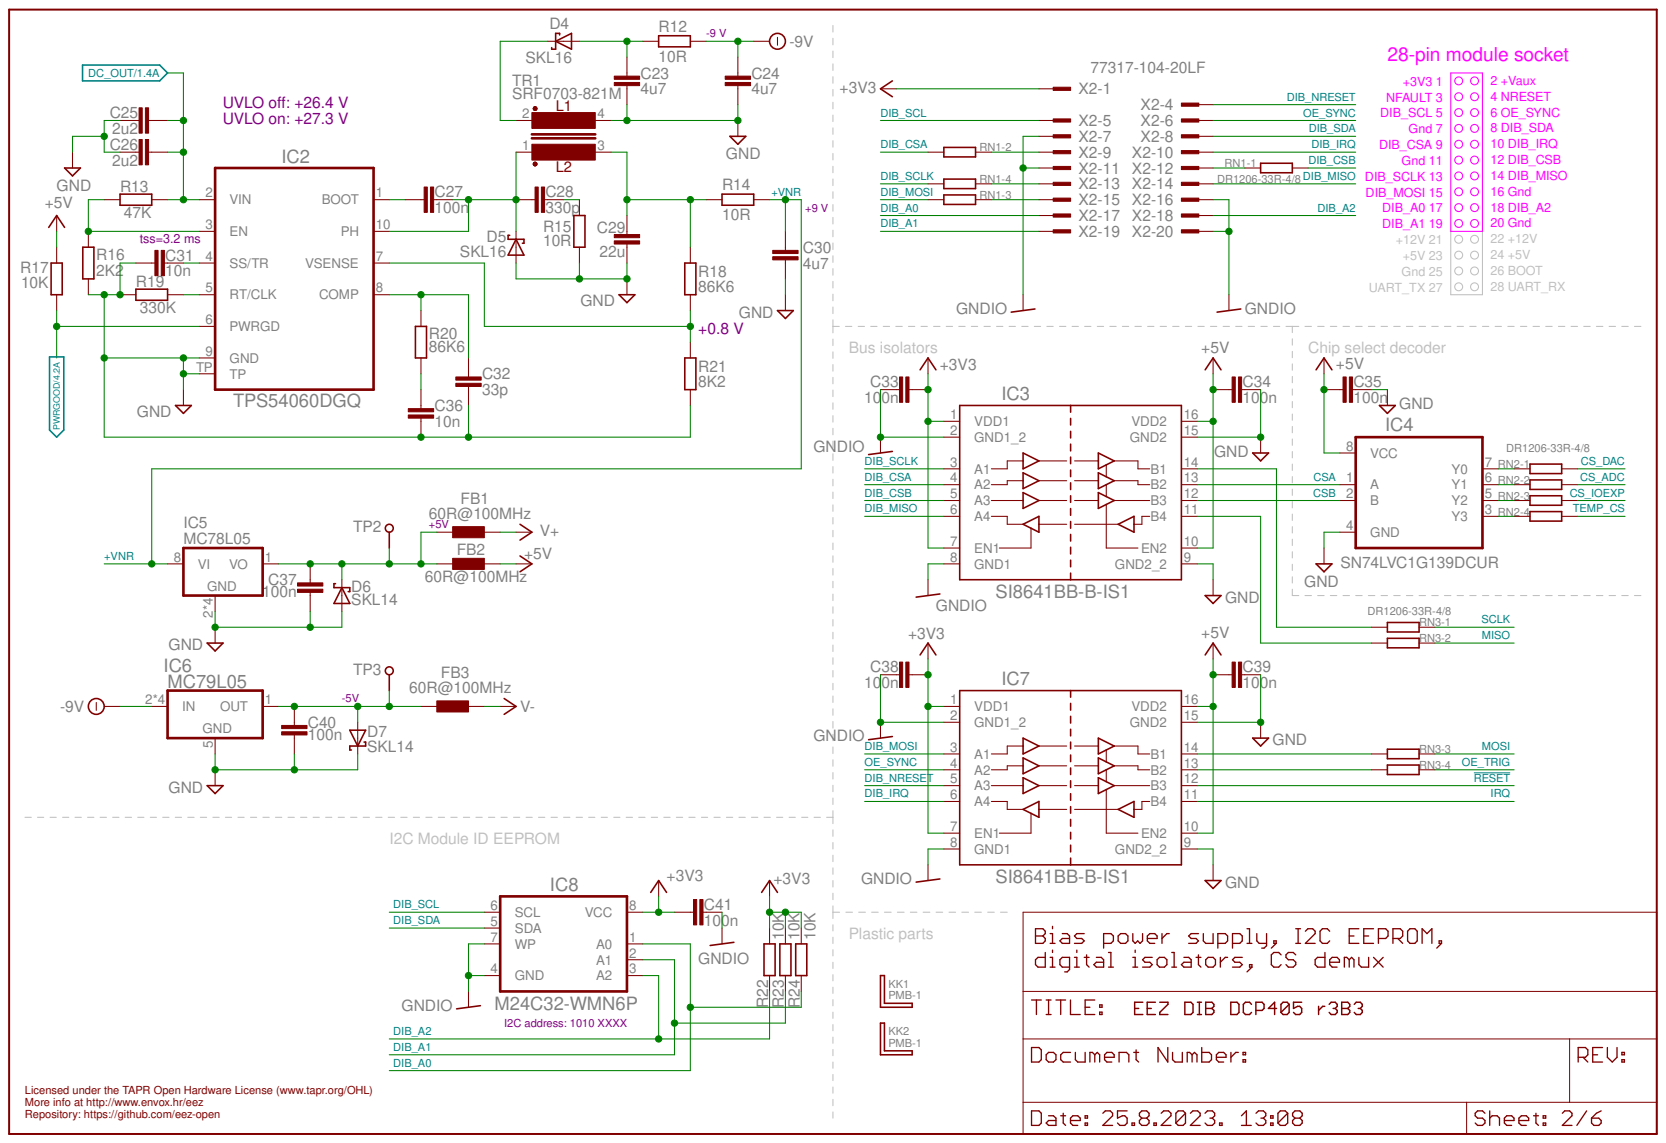
[picture p519: page 2]

TP

CSB

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

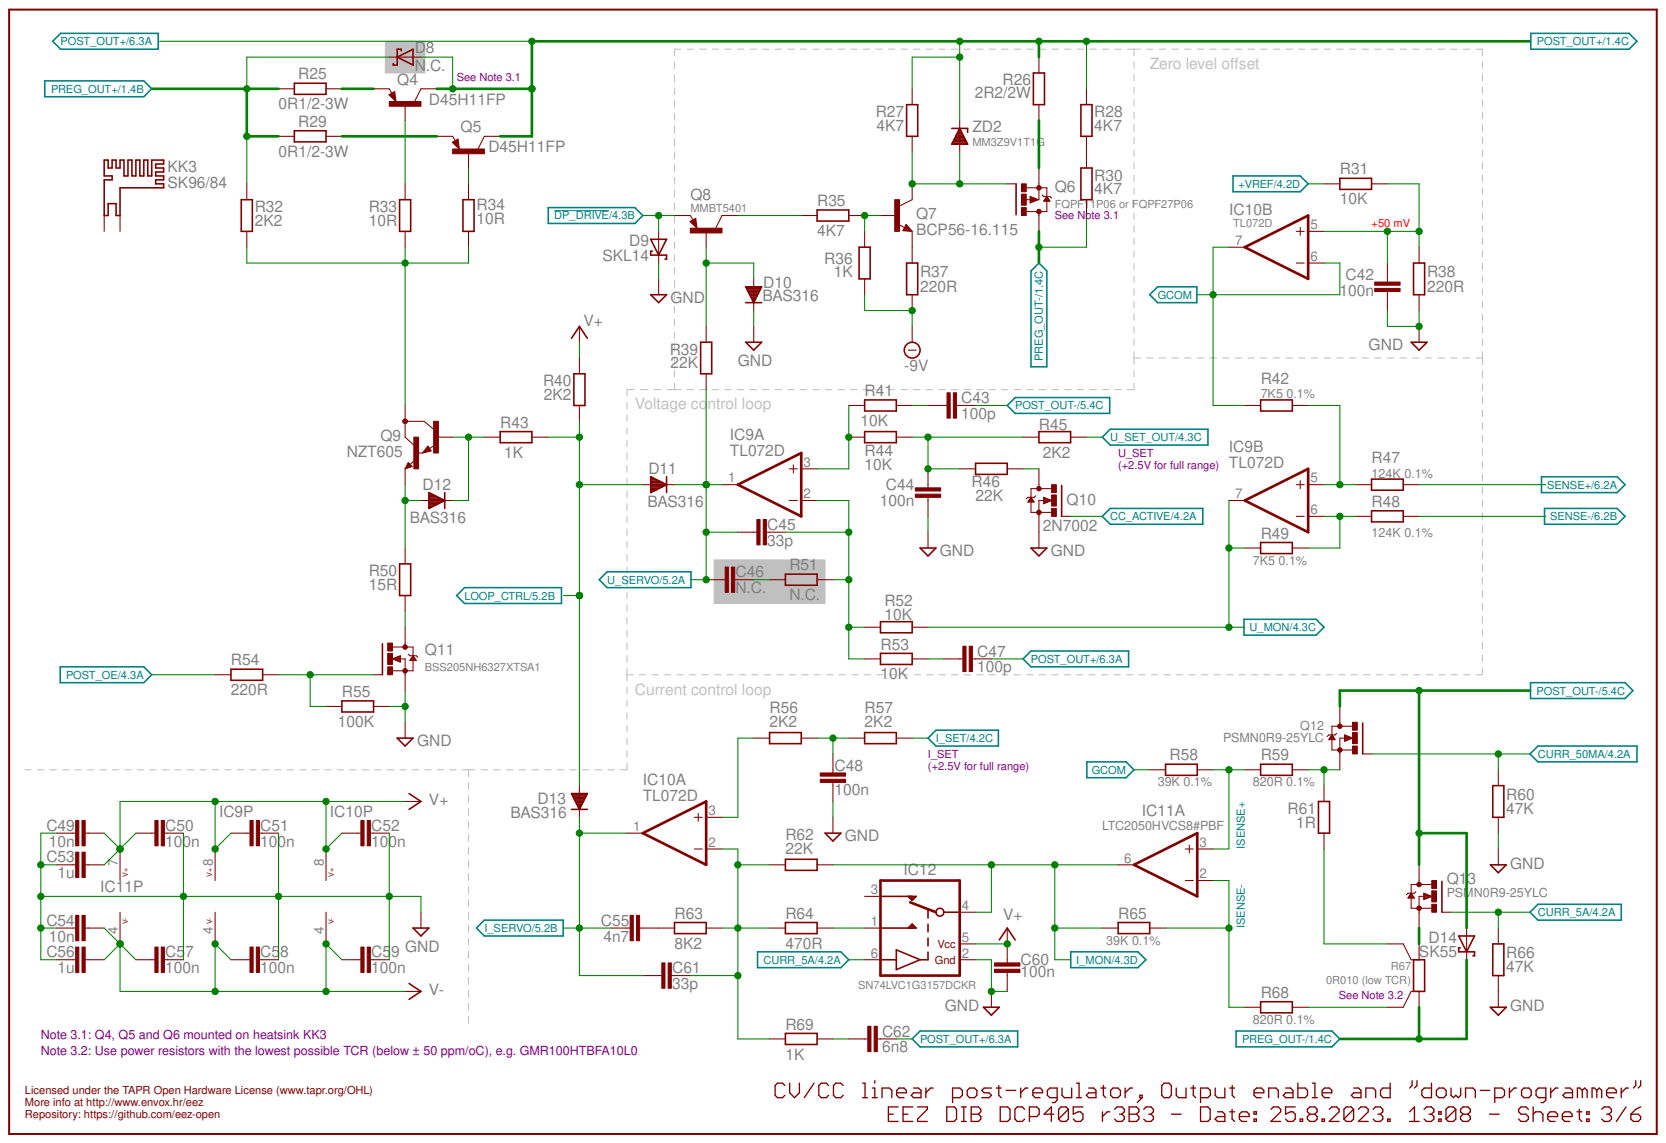
[picture p520: page 3]

Note 3.1: Q4, Q5 and Q6 mounted on heatsink KK3

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

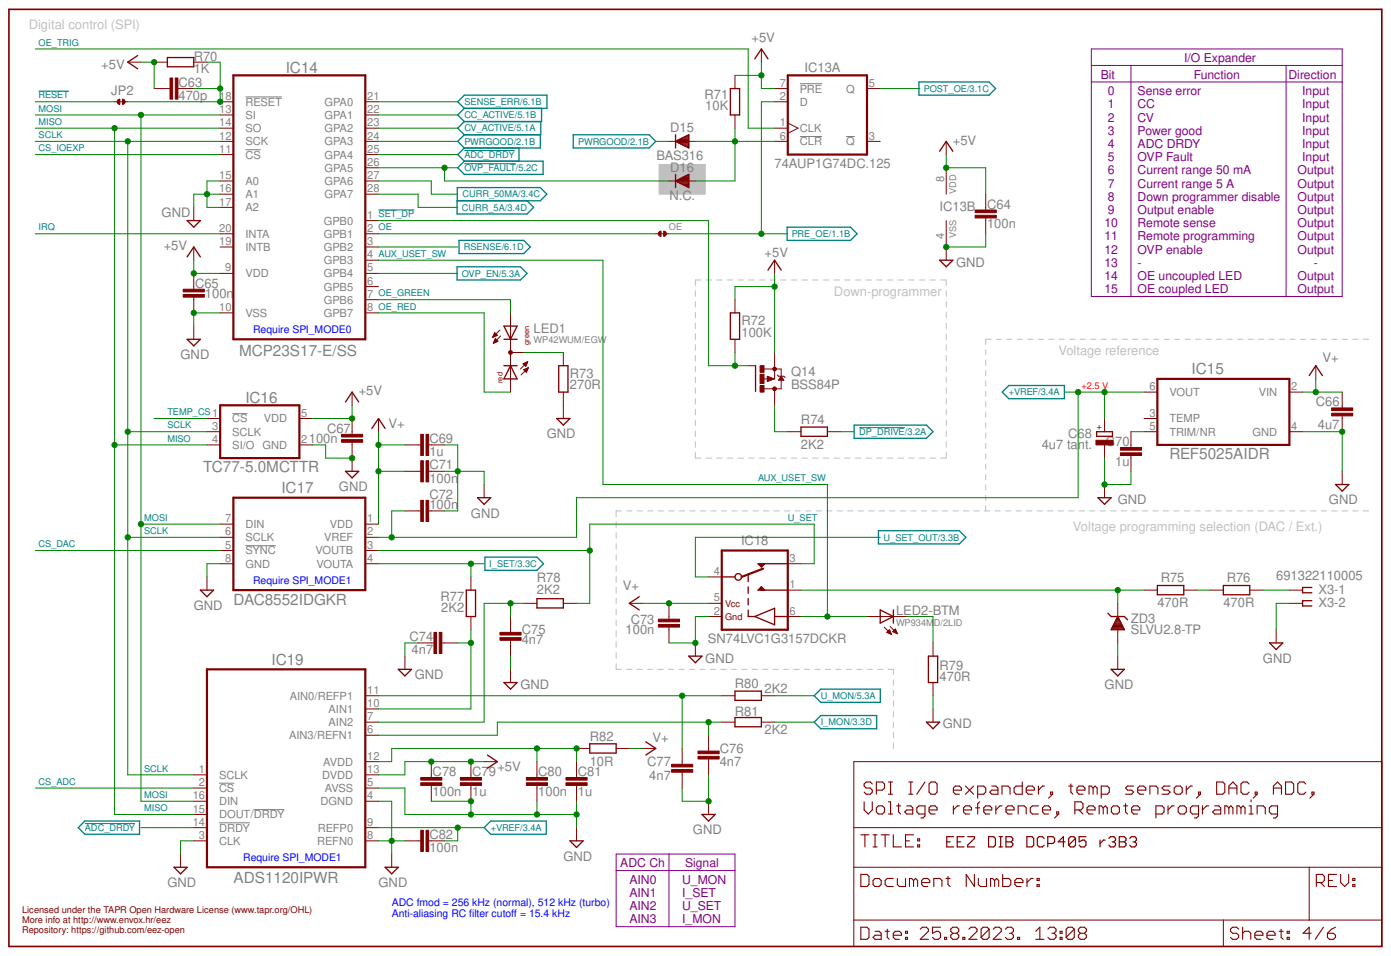
[picture p521: page 4]

Voltage programming selection (DAC / Ext.)

ADC Ch | Signal
AIN0 AIN1 AIN2 AIN3 | U_MON I_SET U_SET I_MON

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

ADC fmod = 256 kHz (normal), 512 kHz (turbo) Anti-aliasing RC filter cutoff = 15.4 kHz

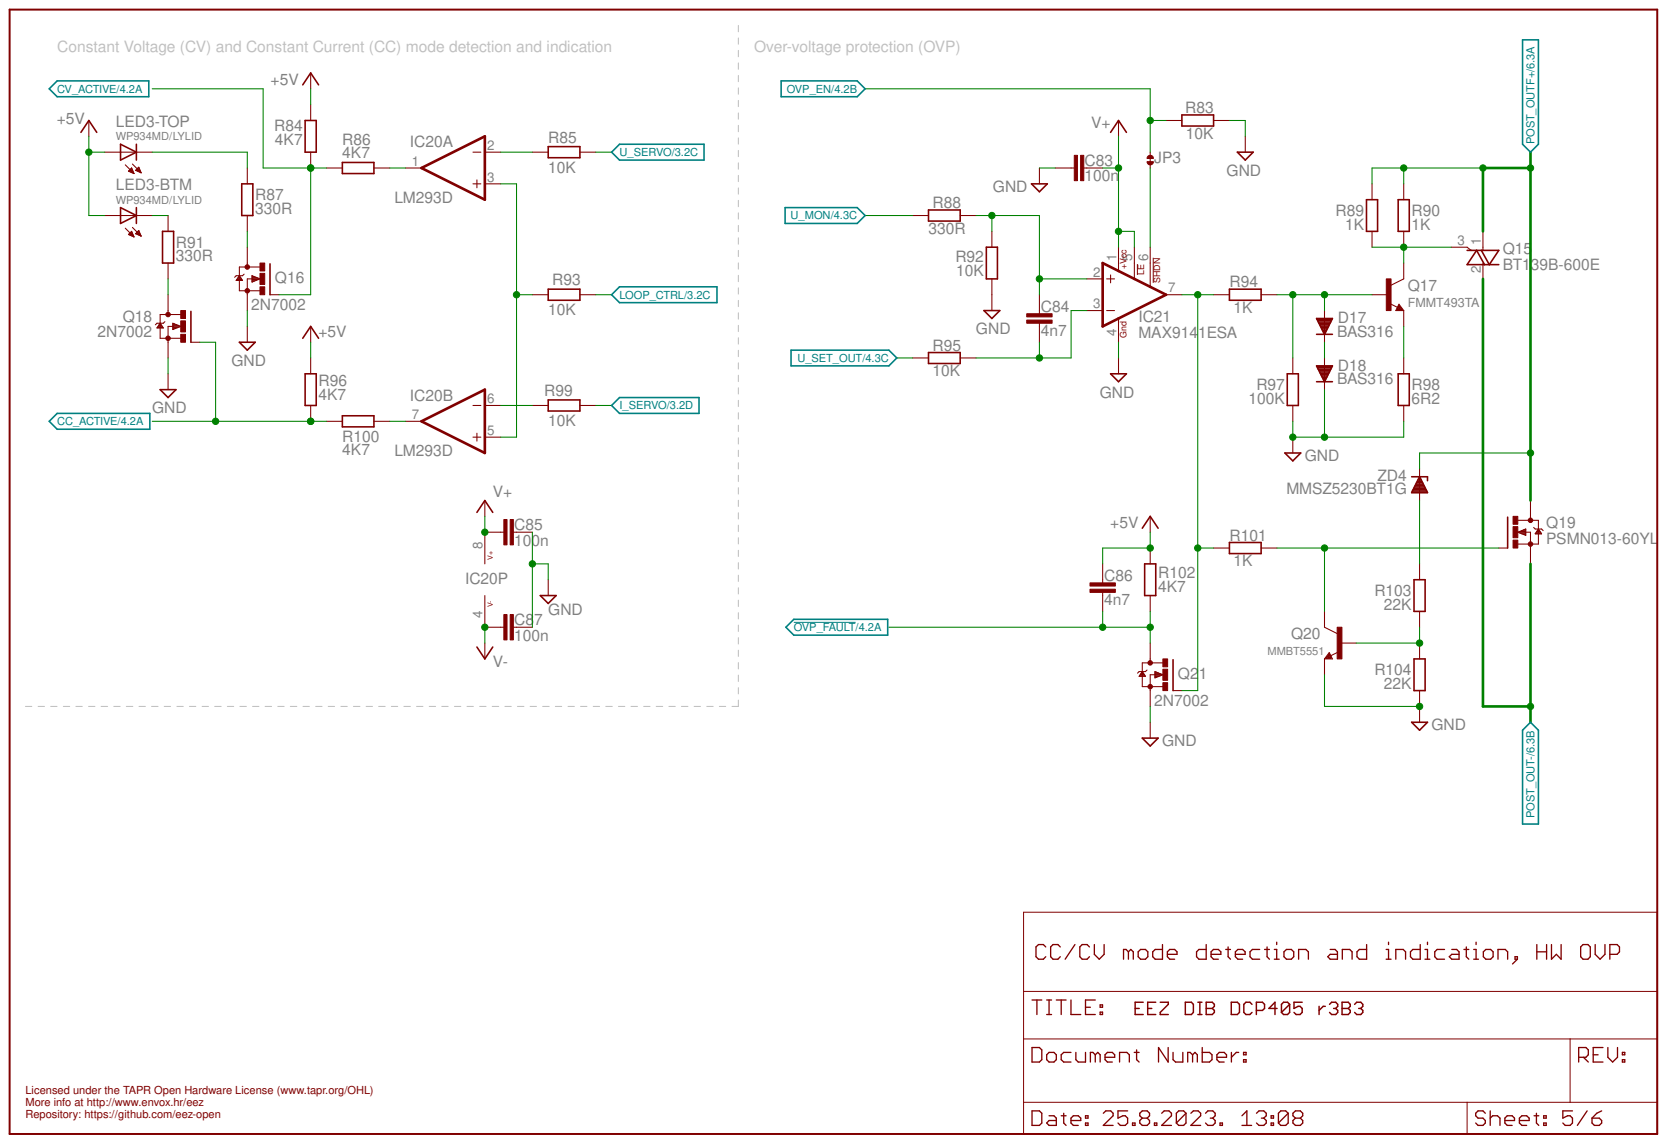
[picture p522: page 5]
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

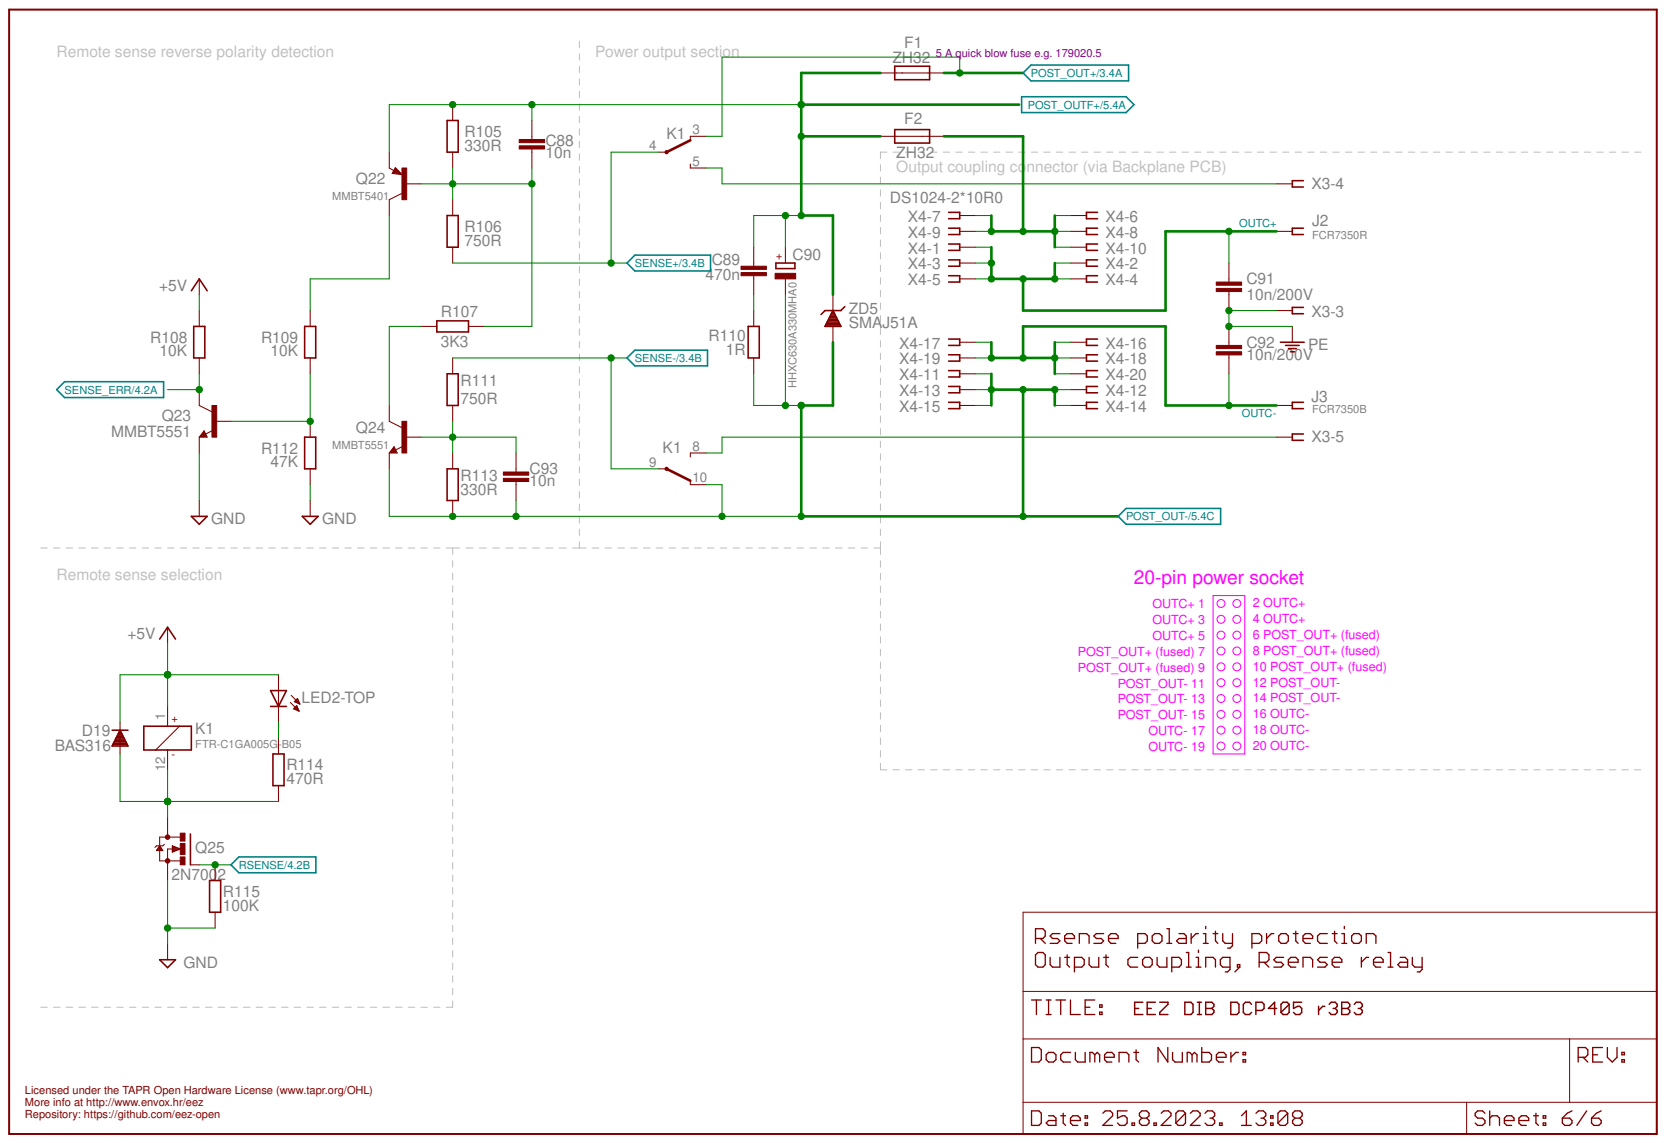
[picture p523: page 6]

Remote sense reverse polarity detection

Output coupling connector (via Backplane PCB)

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
