eez-open/modular-psu/mcu/EEZ DIB MCU r3B4.pdf

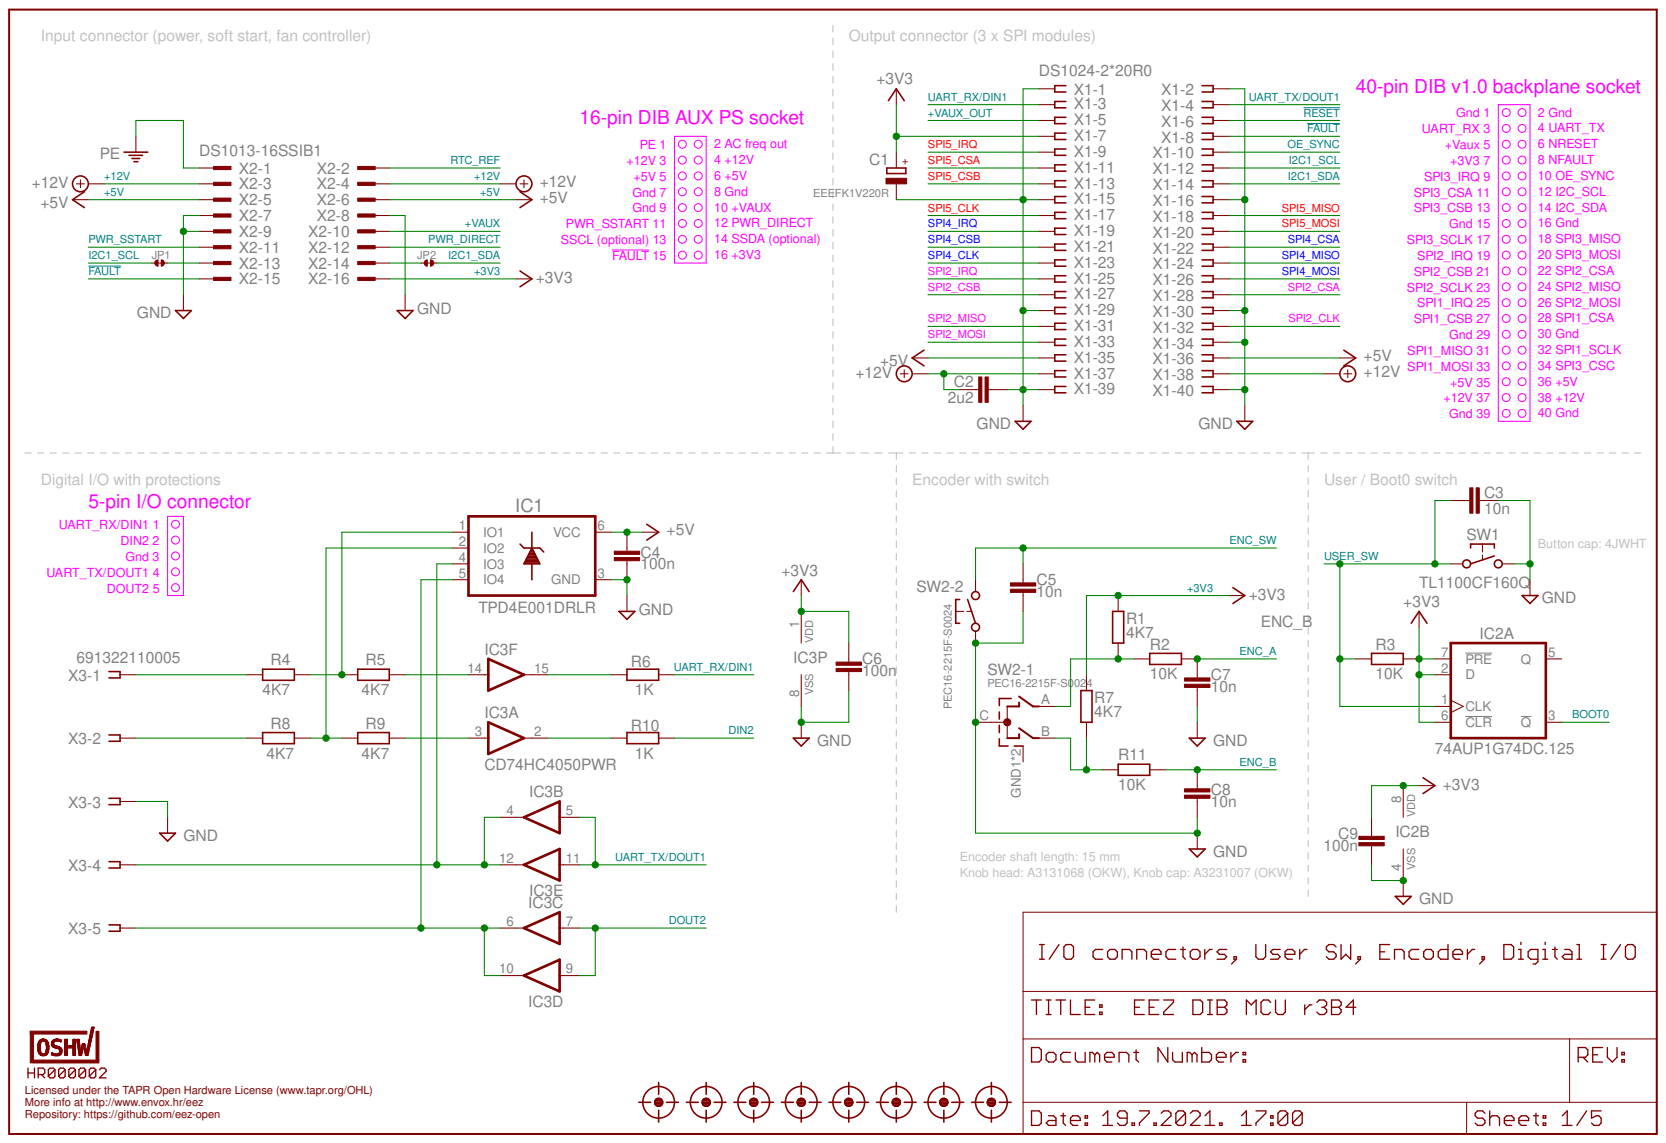
[picture p524: page 1]

2 AC freq out Gnd 7

Encoder shaft length: 15 mm
Knob head: A3131068 (OKW), Knob cap: A3231007 (OKW)

Licensed under the TAPR Open Hardware License (www.tapr.org/OHL) Repository: https://github.com/eez-open More info at http://www.envox.hr/eez

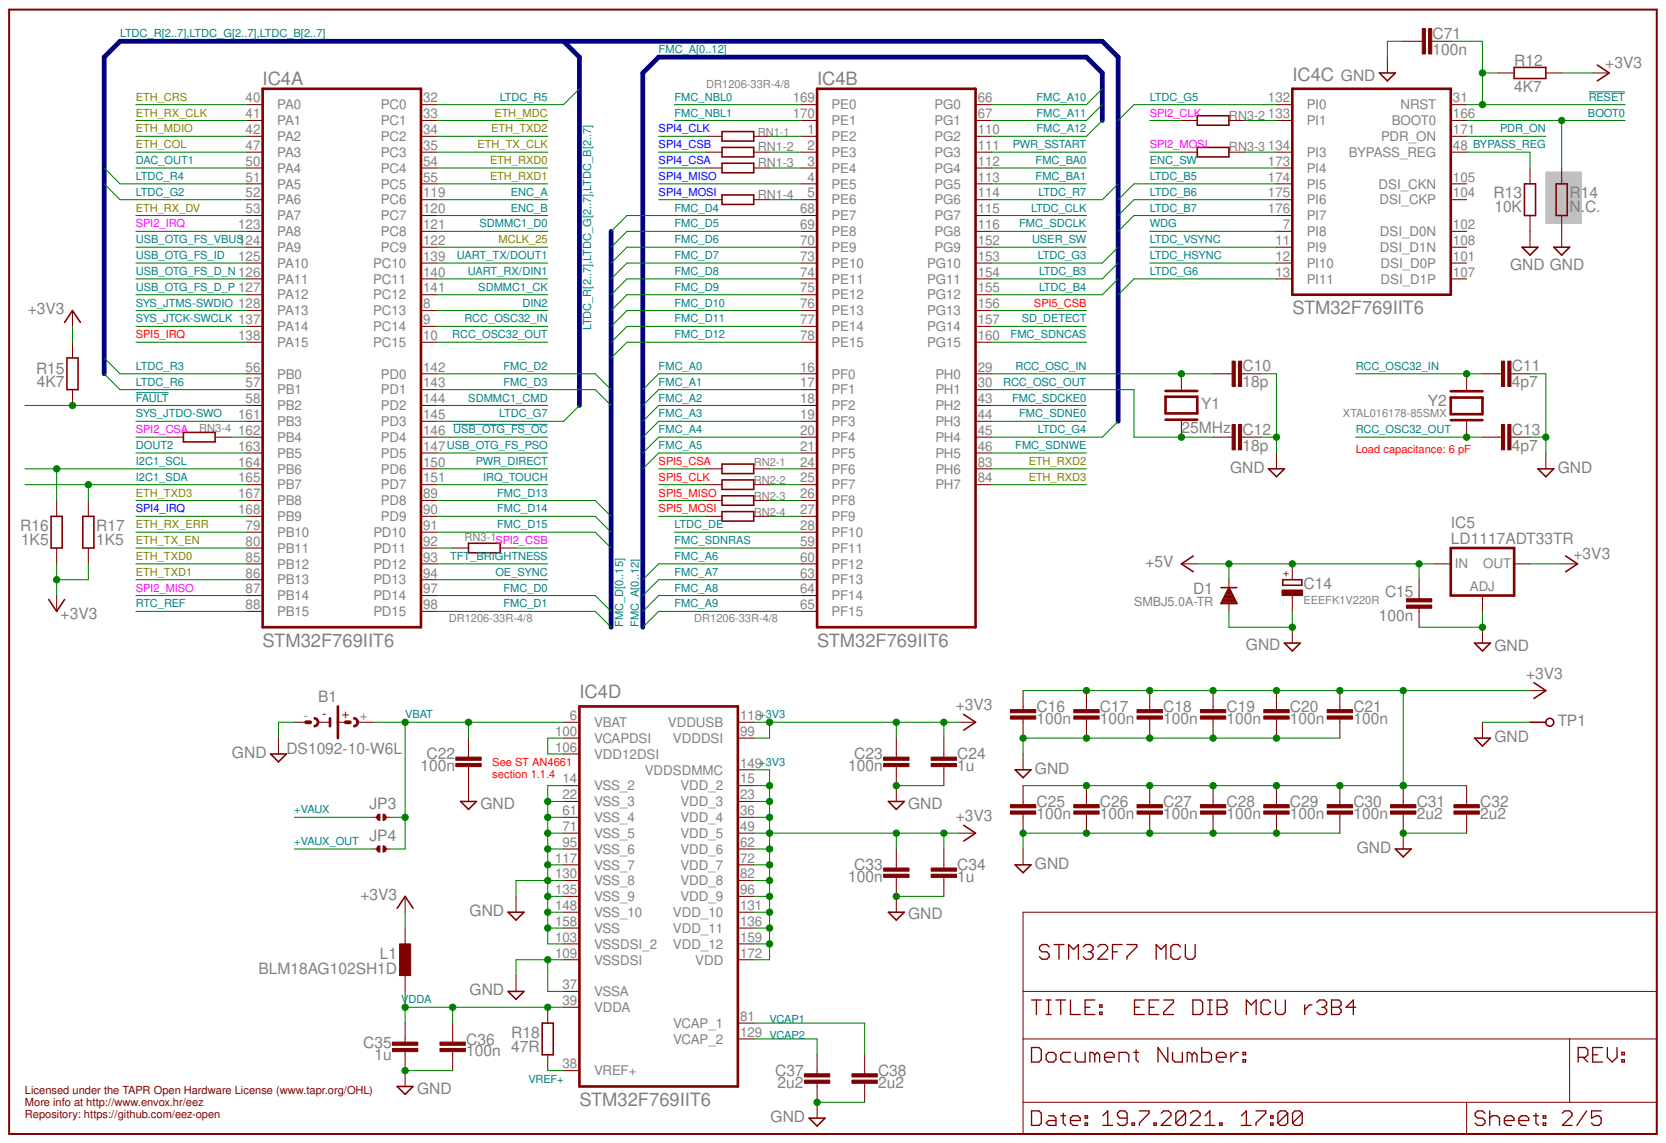
[picture p525: page 2]

RCC_OSC_OUT
FMC_SDCKE0 FMC_SDNE0

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

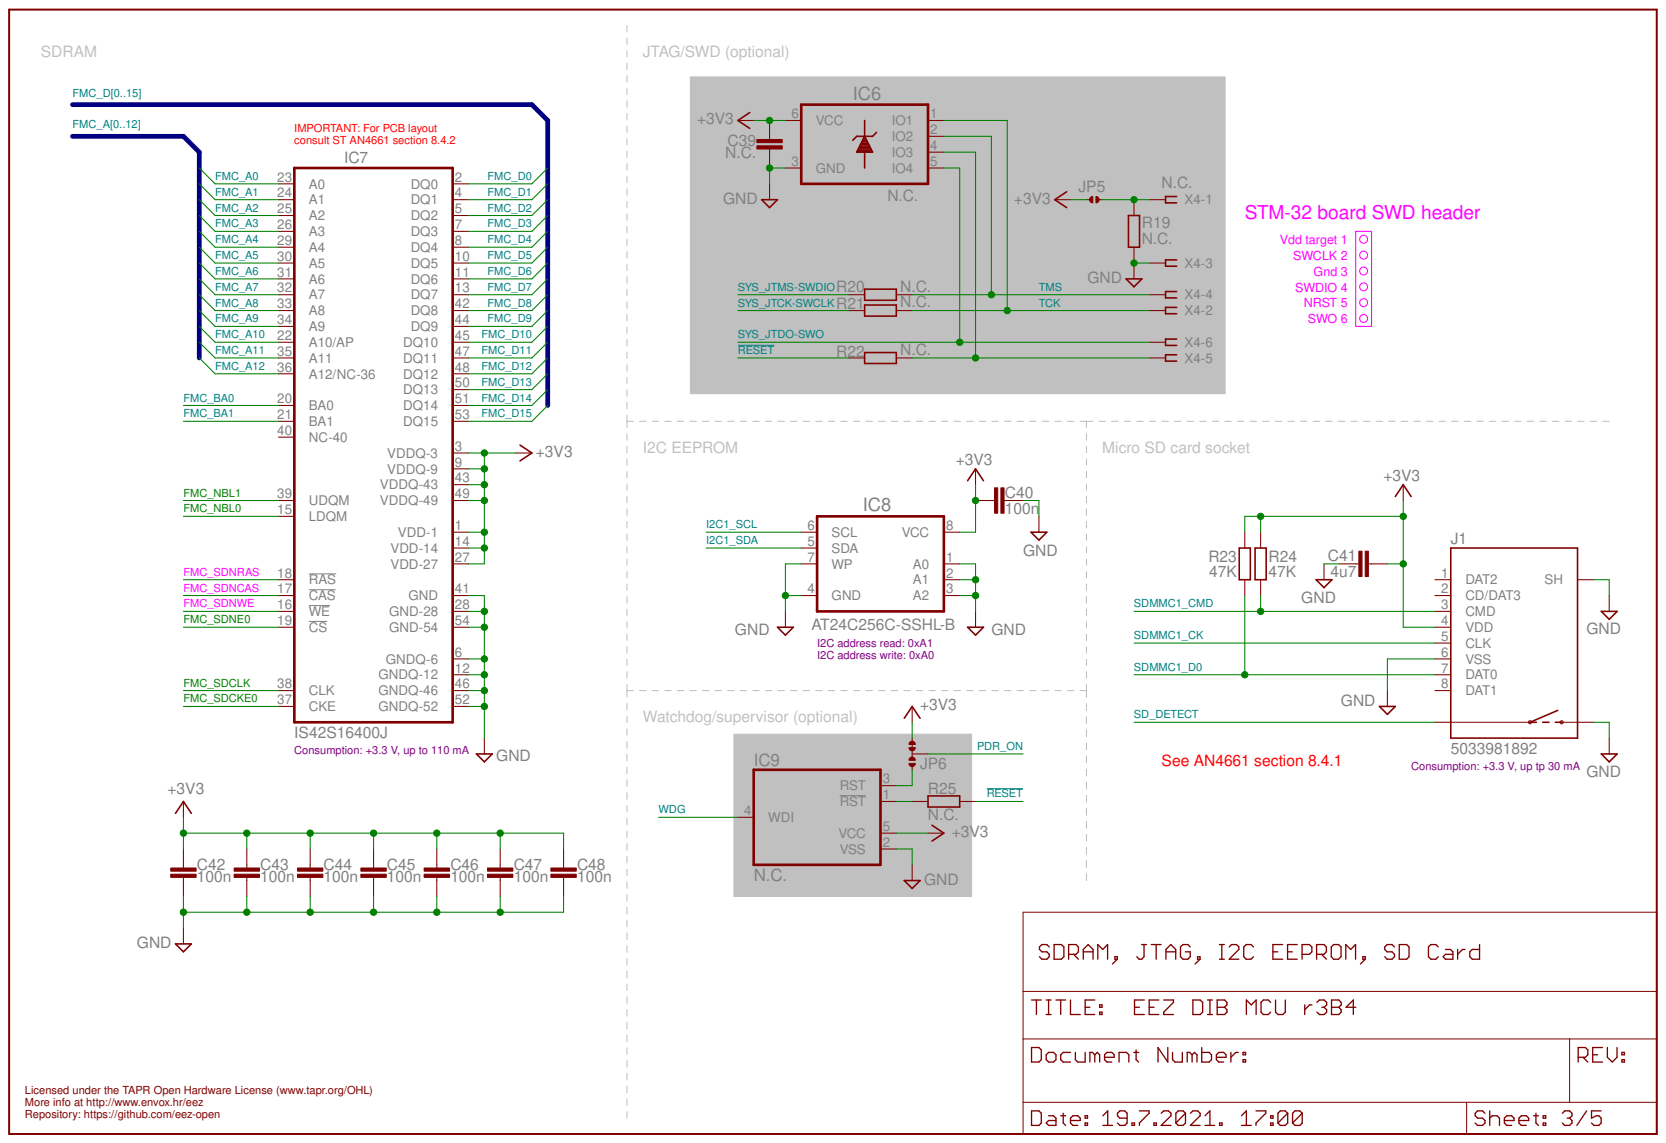
[picture p526: page 3]

IMPORTANT: For PCB layout consult ST AN4661 section 8.4.2

SWDIO 4 SWCLK 2 Vdd target 1 STM-32 board SWD header Gnd 3 NRST 5 SWO 6

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

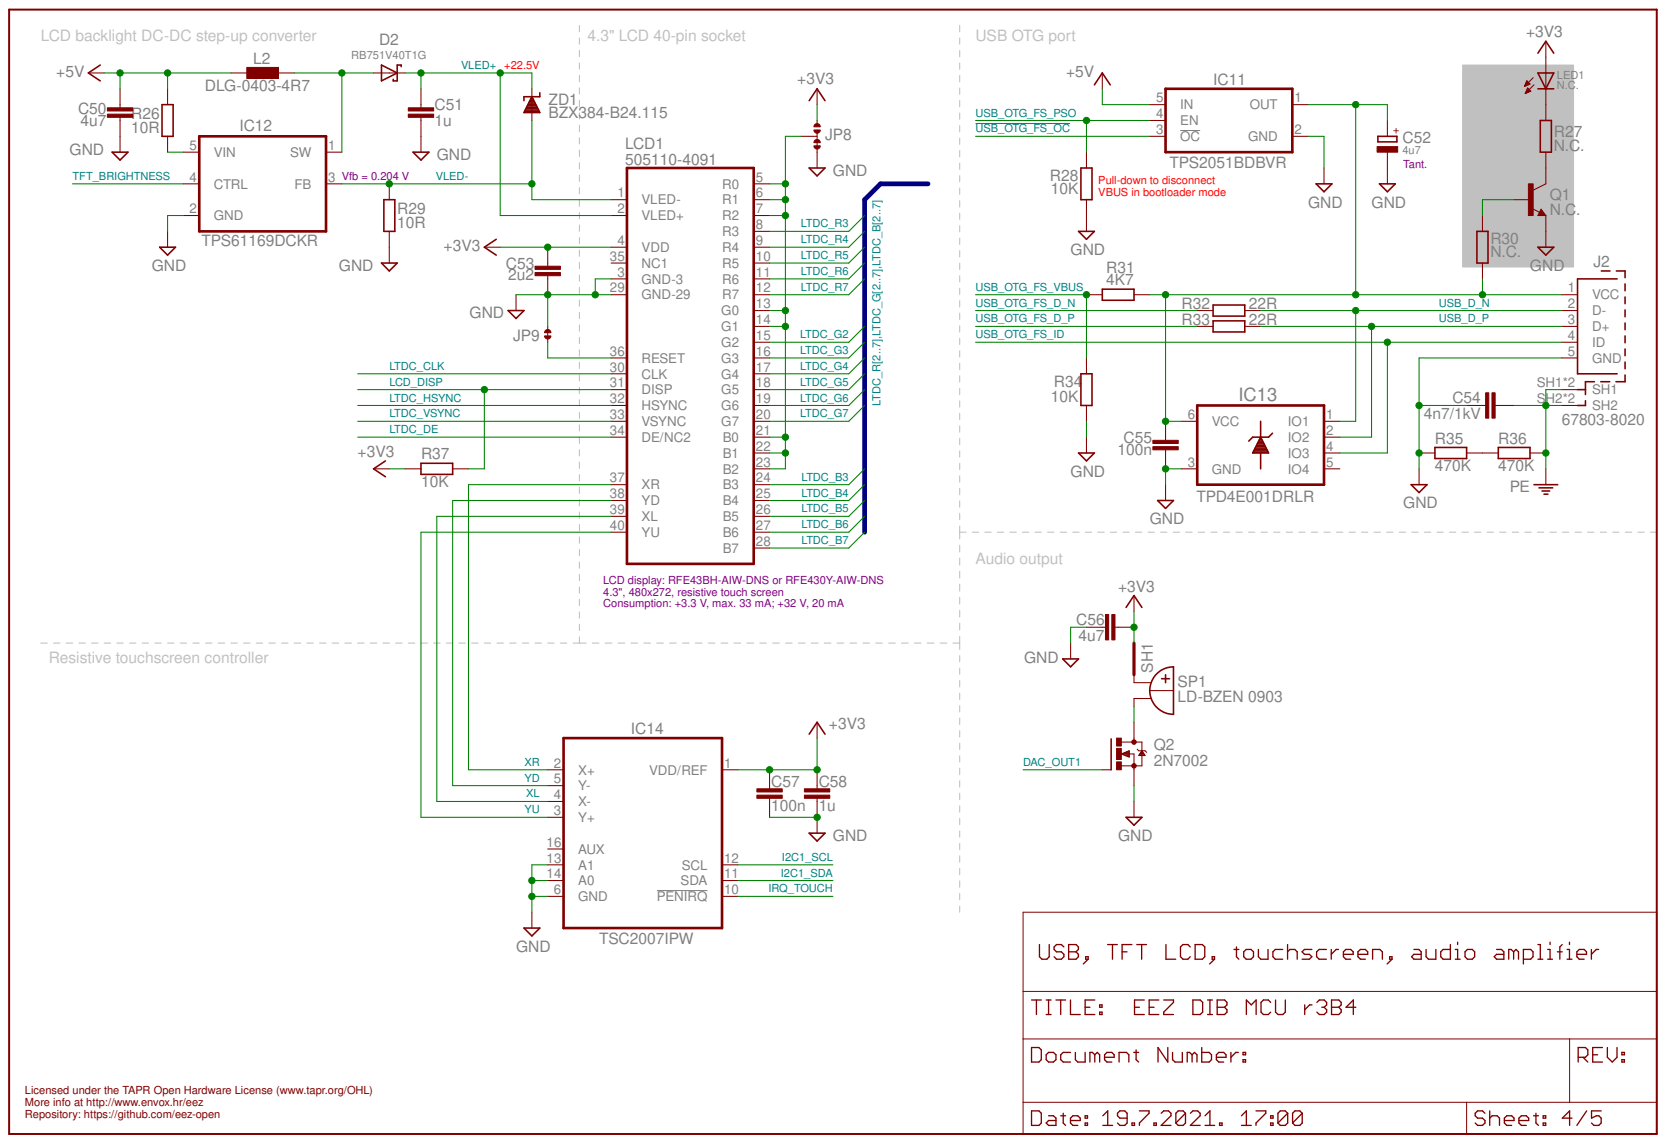
[picture p527: page 4]

Pull-down to disconnect VBUS in bootloader mode

LCD display: RFE43BH-AIW-DNS or RFE430Y-AIW-DNS
4.3", 480x272, resistive touch screen
Consumption: +3.3 V, max. 33 mA; +32 V, 20 mA

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

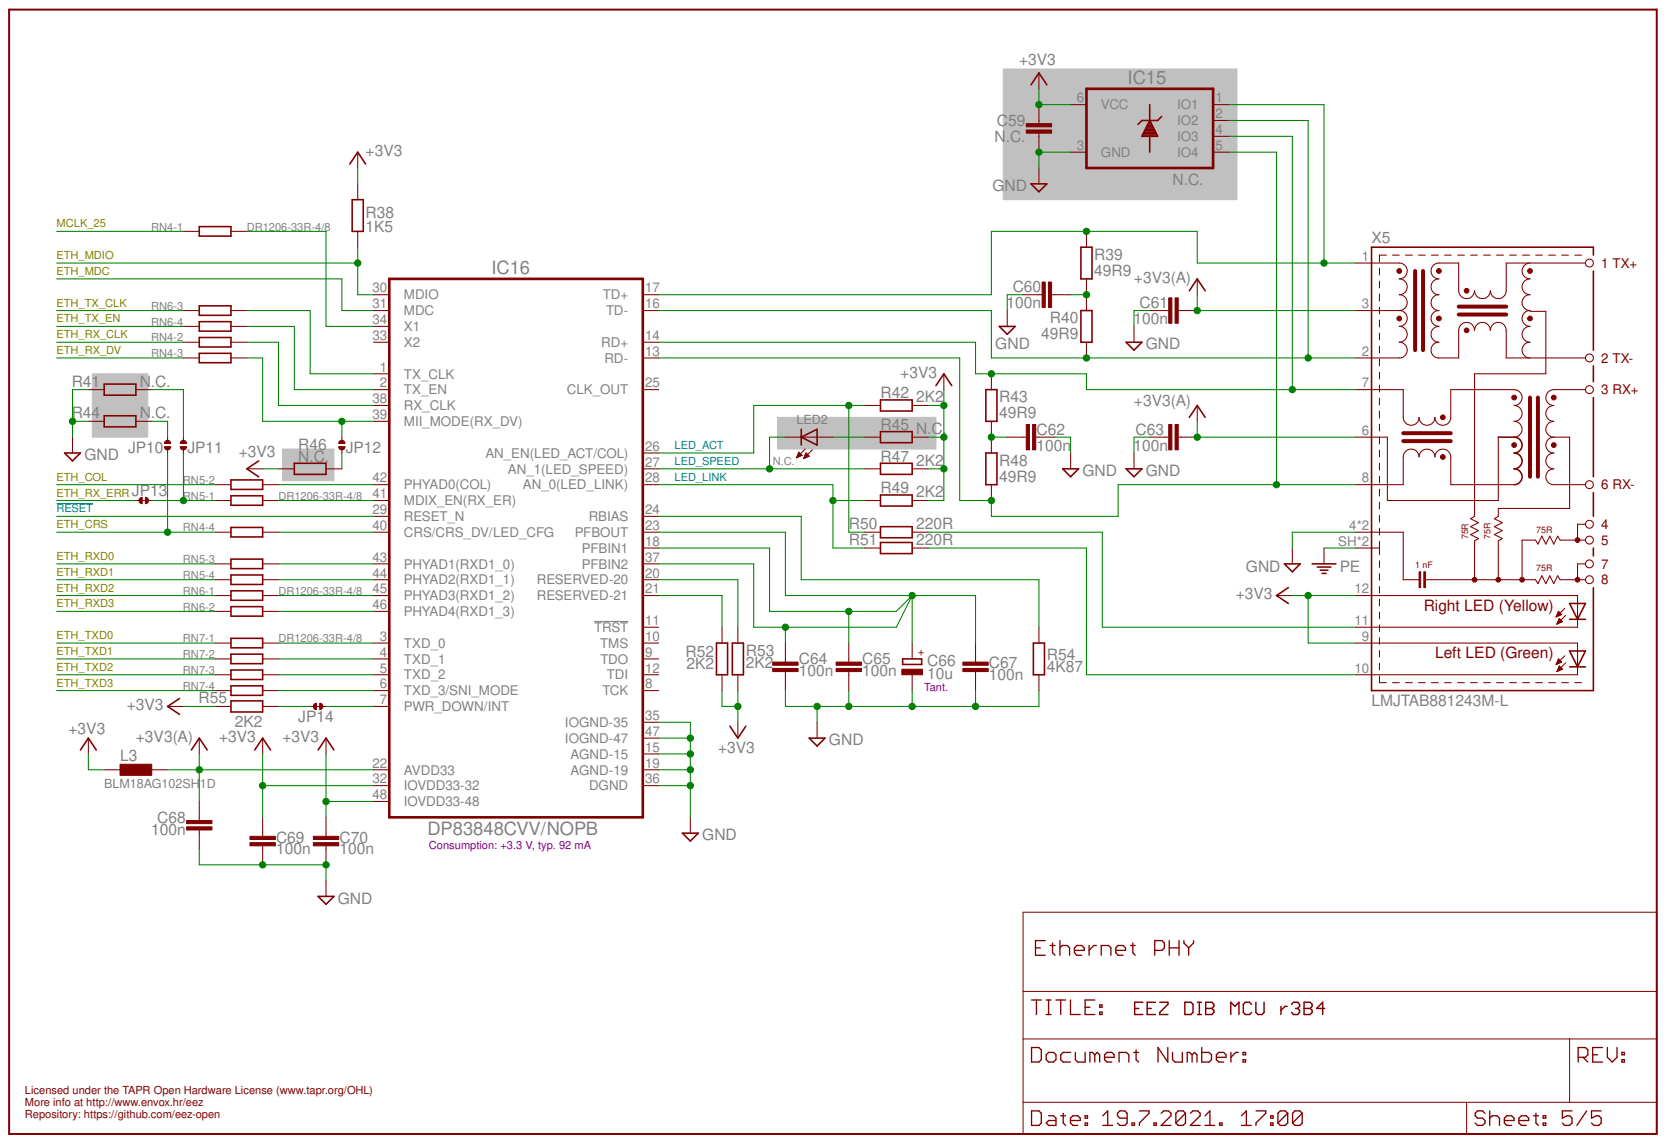
[picture p528: page 5]

LED_SPEED | R47

32
48

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
