eez-open/modular-psu/mcu/EEZ DIB MCU r2B4.pdf

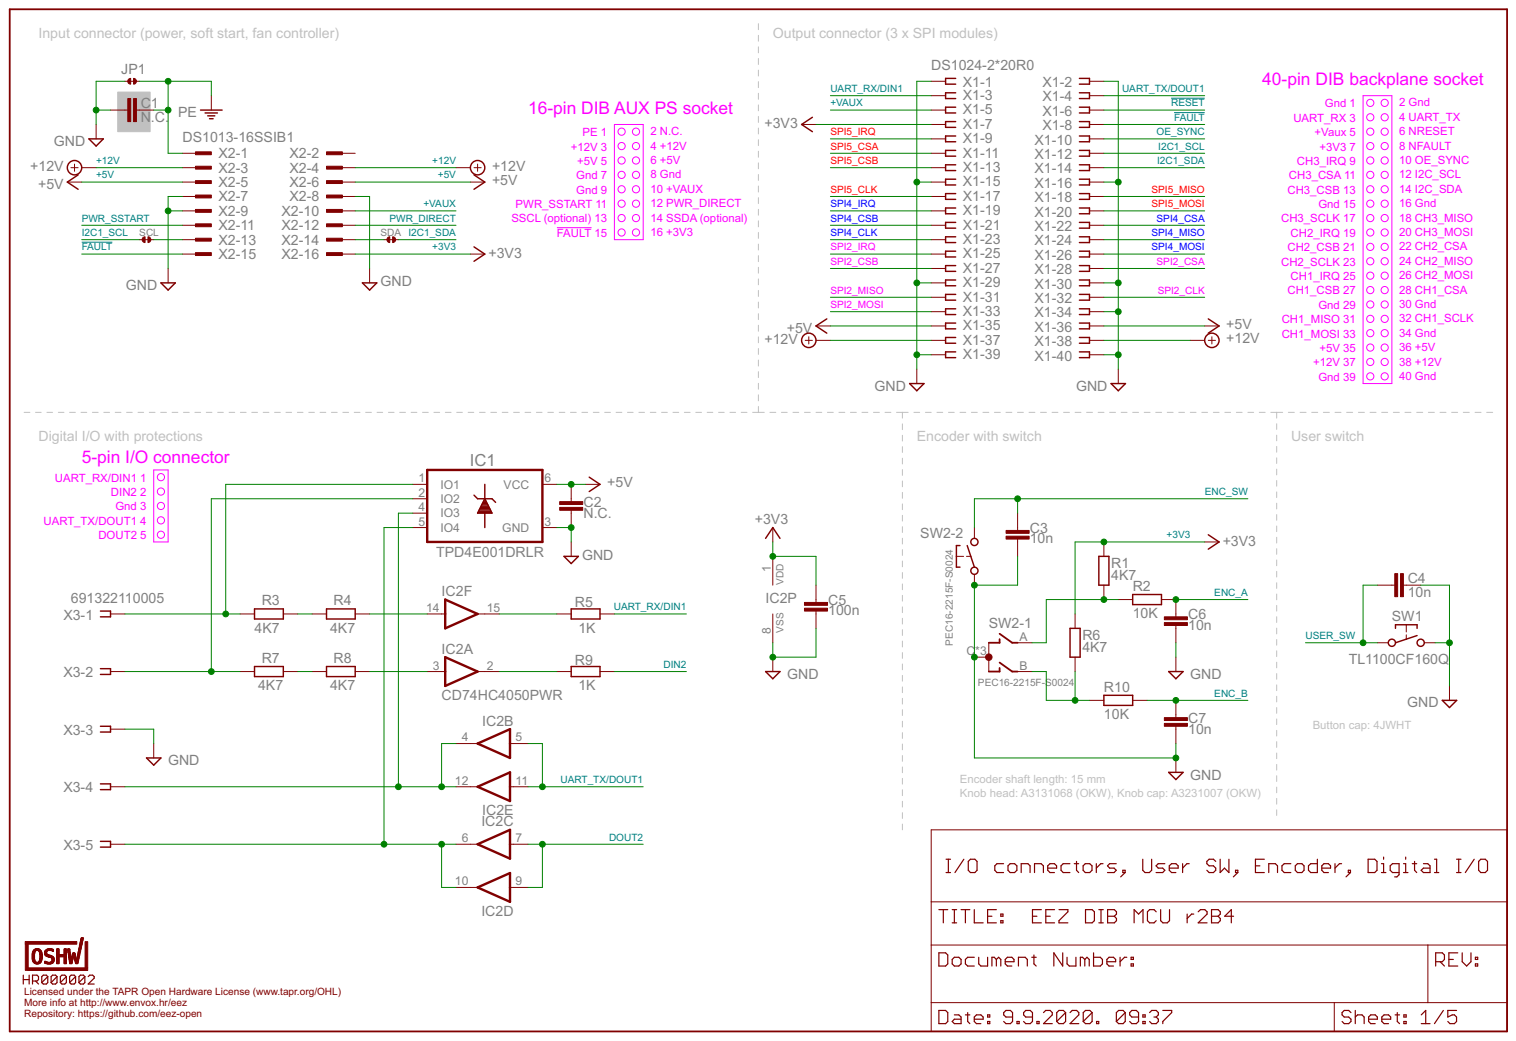
[picture p529: page 1]

Encoder shaft length: 15 mm
Knob head: A3131068 (OKW), Knob cap: A3231007 (OKW)

Licensed under the TAPR Open Hardware License (www.tapr.org/OHL) Repository: https://github.com/eez-open More info at http://www.envox.hr/eez

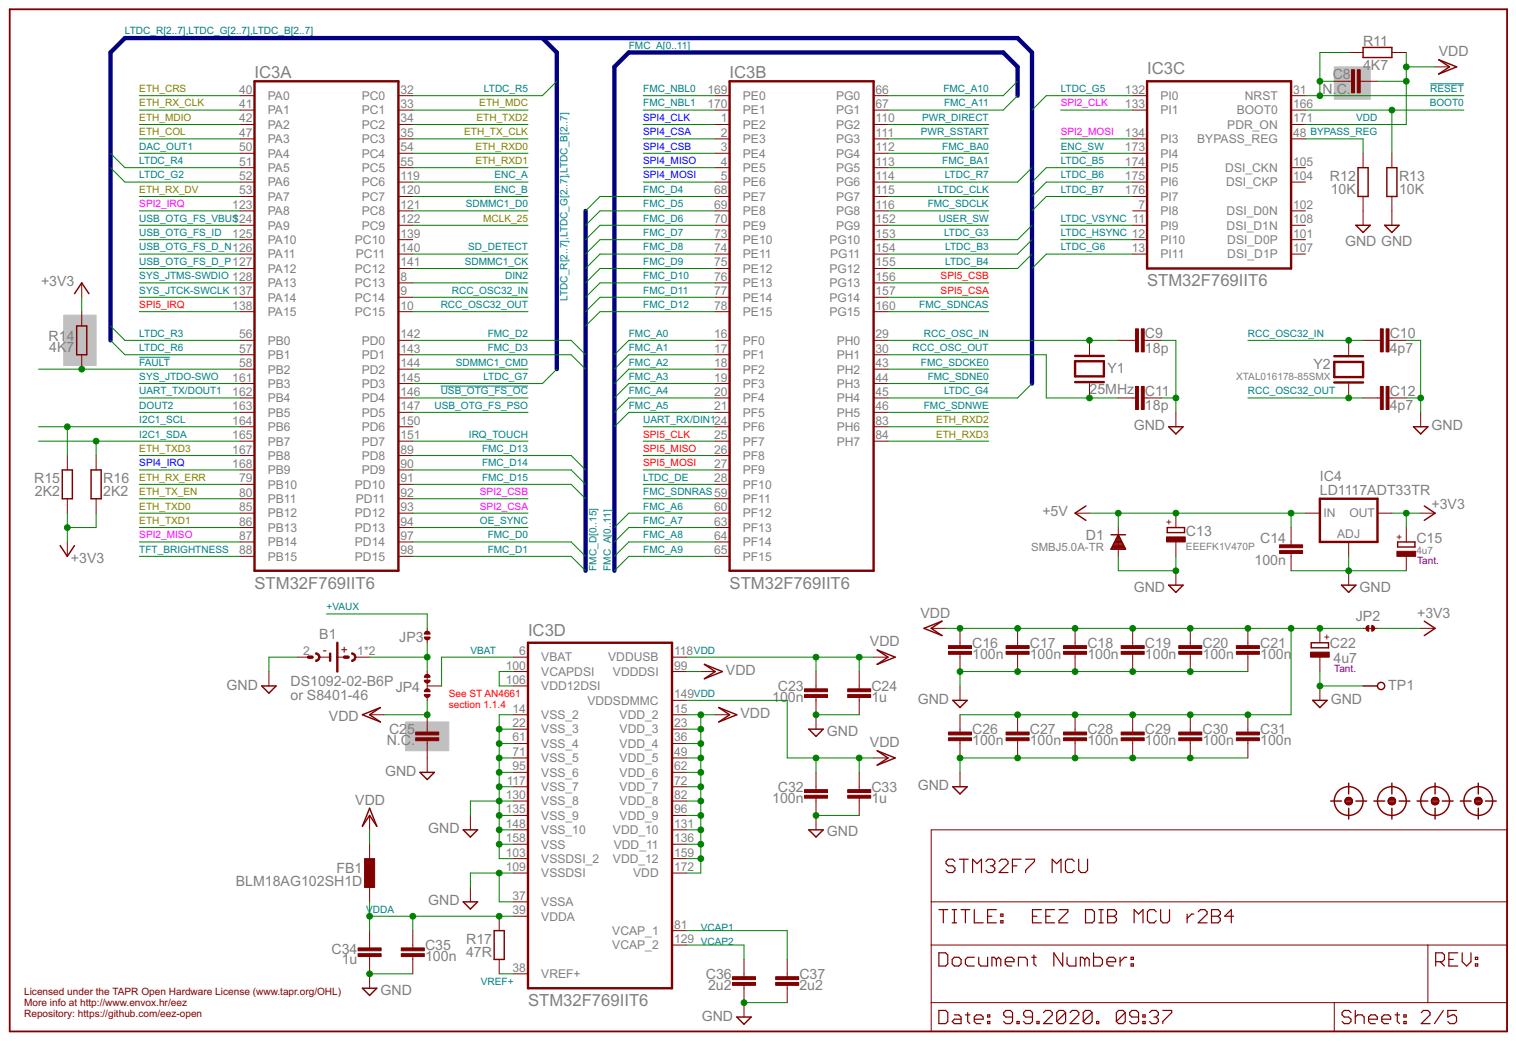
[picture p530: page 2]

RCC_OSC_OUT
FMC_SDCKE0 FMC_SDNE0

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

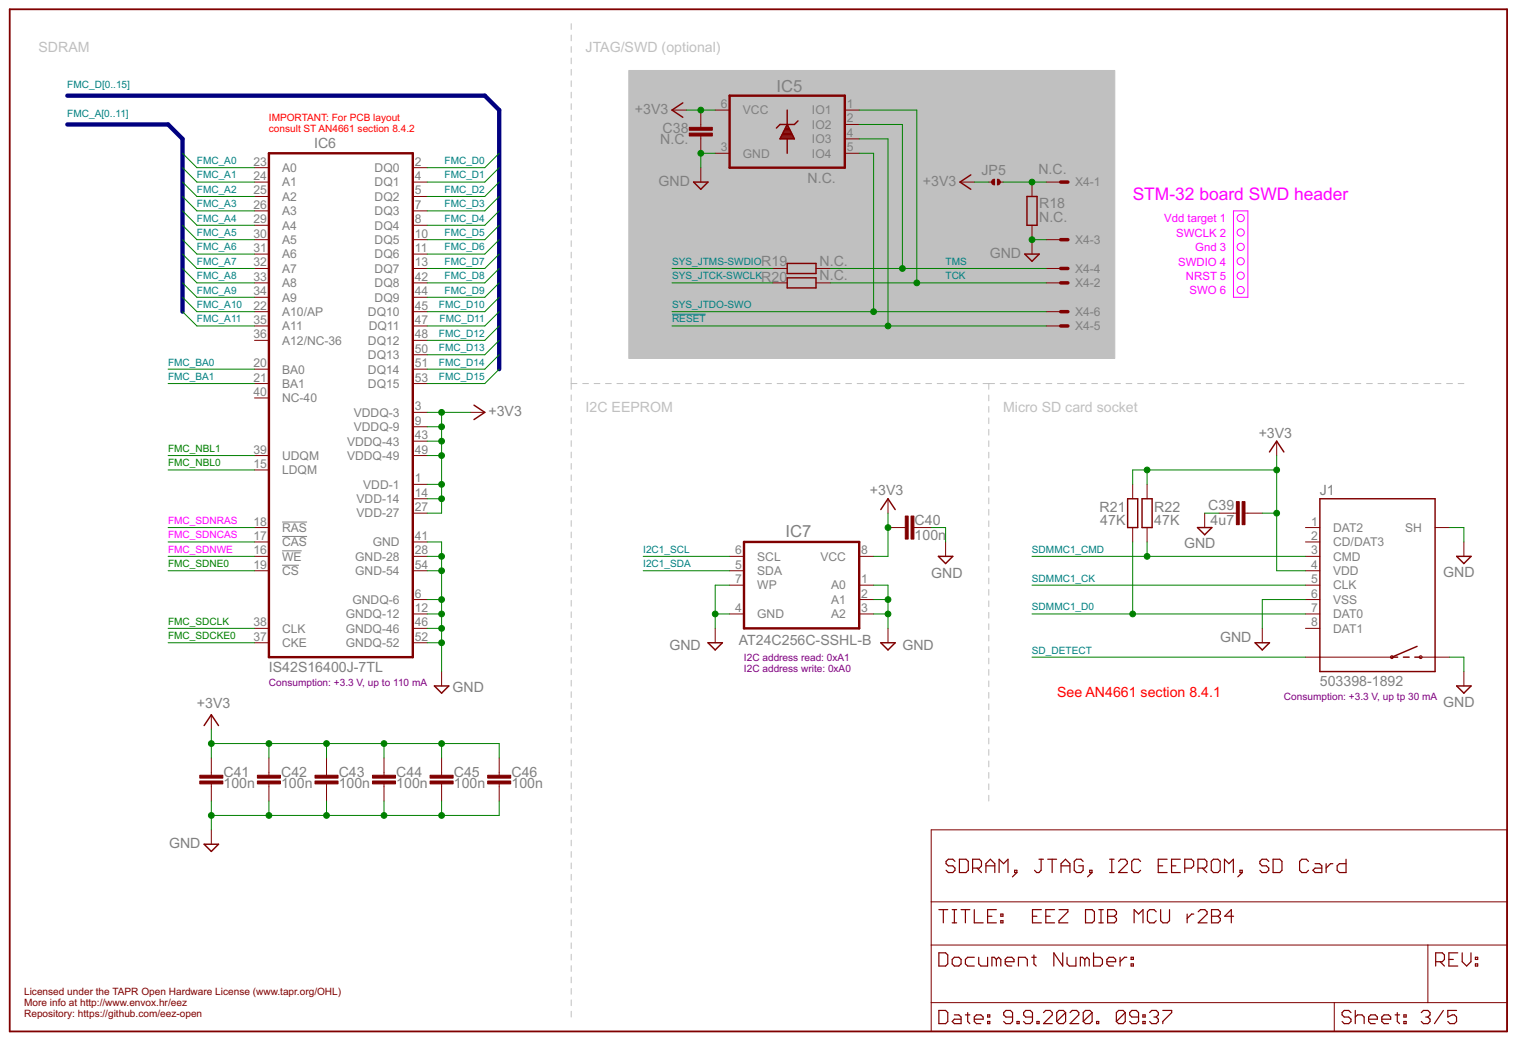
[picture p531: page 3]

IMPORTANT: For PCB layout consult ST AN4661 section 8.4.2
FMC_D15 FMC_D14 FMC_D13 FMC_D12 FMC_D10 FMC_D9 FMC_D8 FMC_D7 FMC_D6 FMC_D5 FMC_D4 FMC_D3 FMC_D2 FMC_D1 FMC_D0

SWDIO 4 SWCLK 2 Vdd target 1 STM-32 board SWD header Gnd 3 NRST 5 SWO 6

CLK
Consumption: +3.3 V, up tp 30 mA Consumption: +3.3 V, up to 110 mA

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

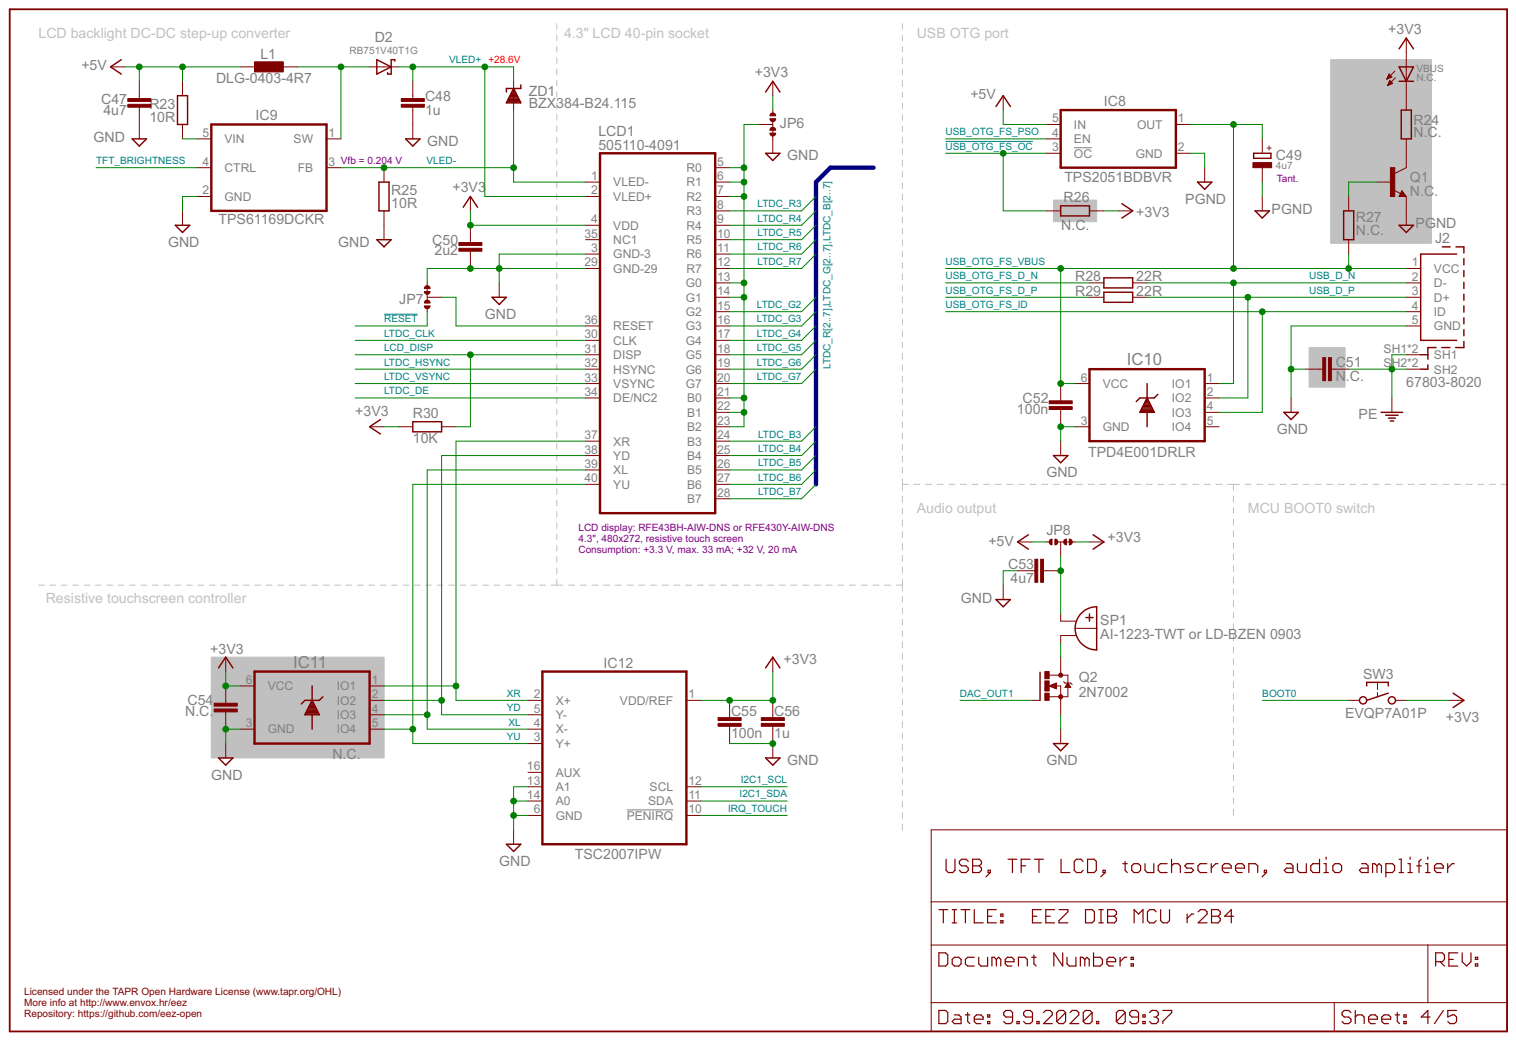
[picture p532: page 4]

LCD display: RFE43BH-AIW-DNS or RFE430Y-AIW-DNS
4.3", 480x272, resistive touch screen
Consumption: +3.3 V, max. 33 mA; +32 V, 20 mA

AI-1223-TWT or LD-BZEN 0903

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

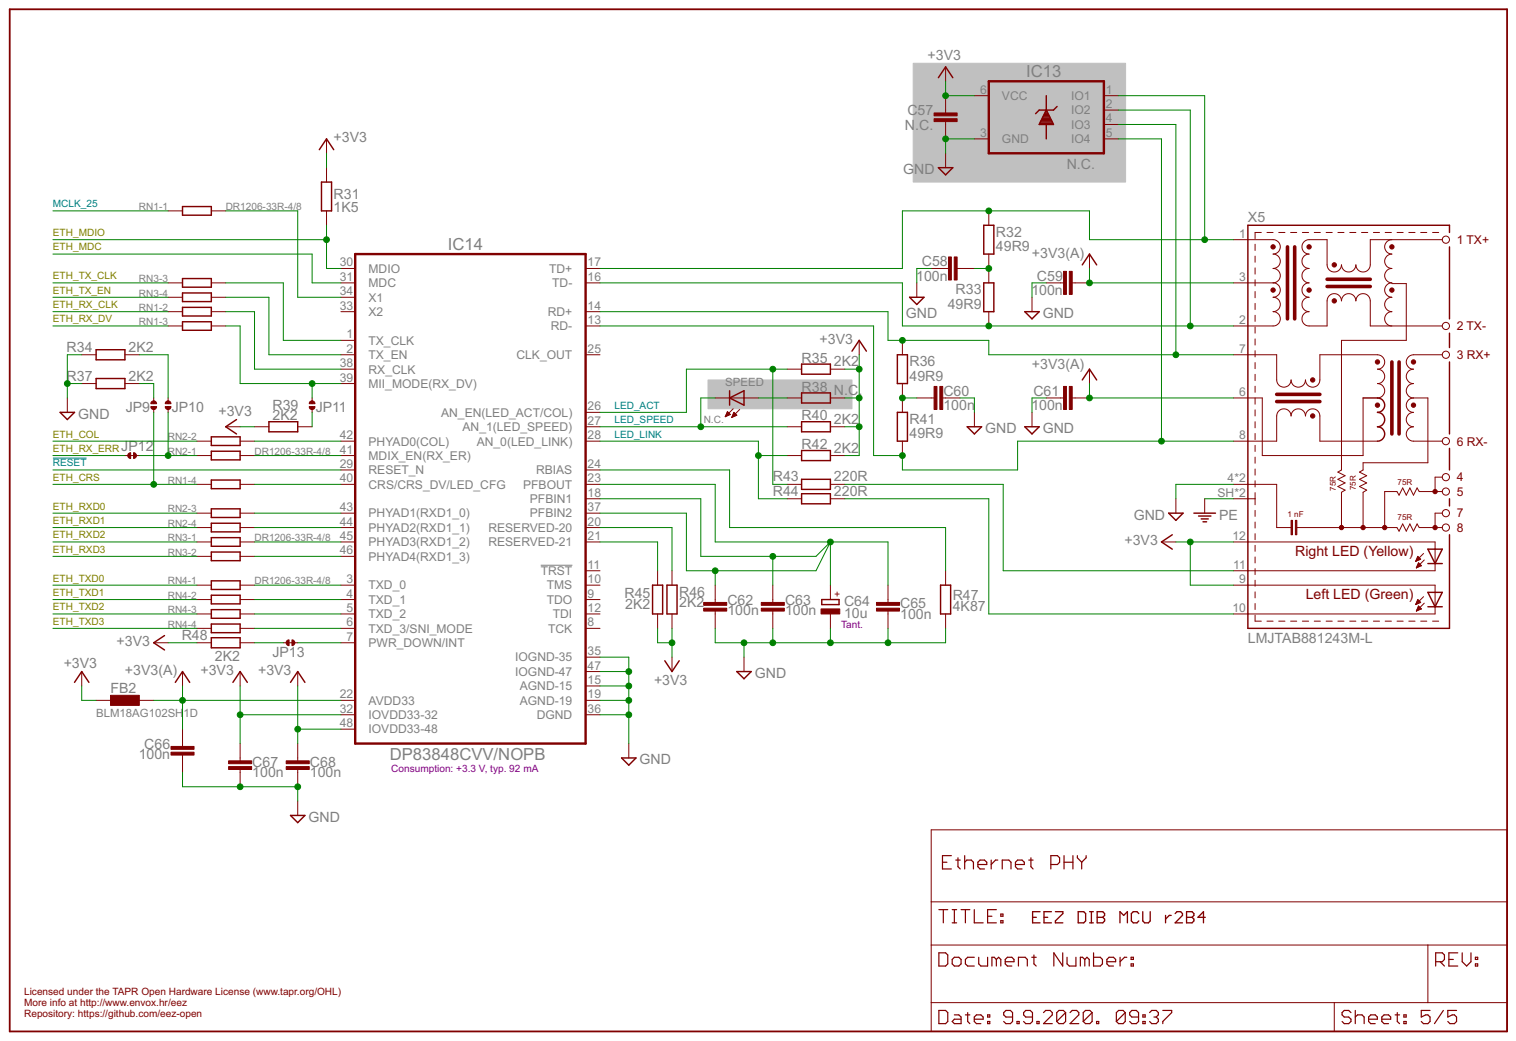
[picture p533: page 5]

LED_SPEED | R40 2K2

32
48

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
