eez-open/modular-psu/dcm220/EEZ DIB DCM220 r2B8.pdf

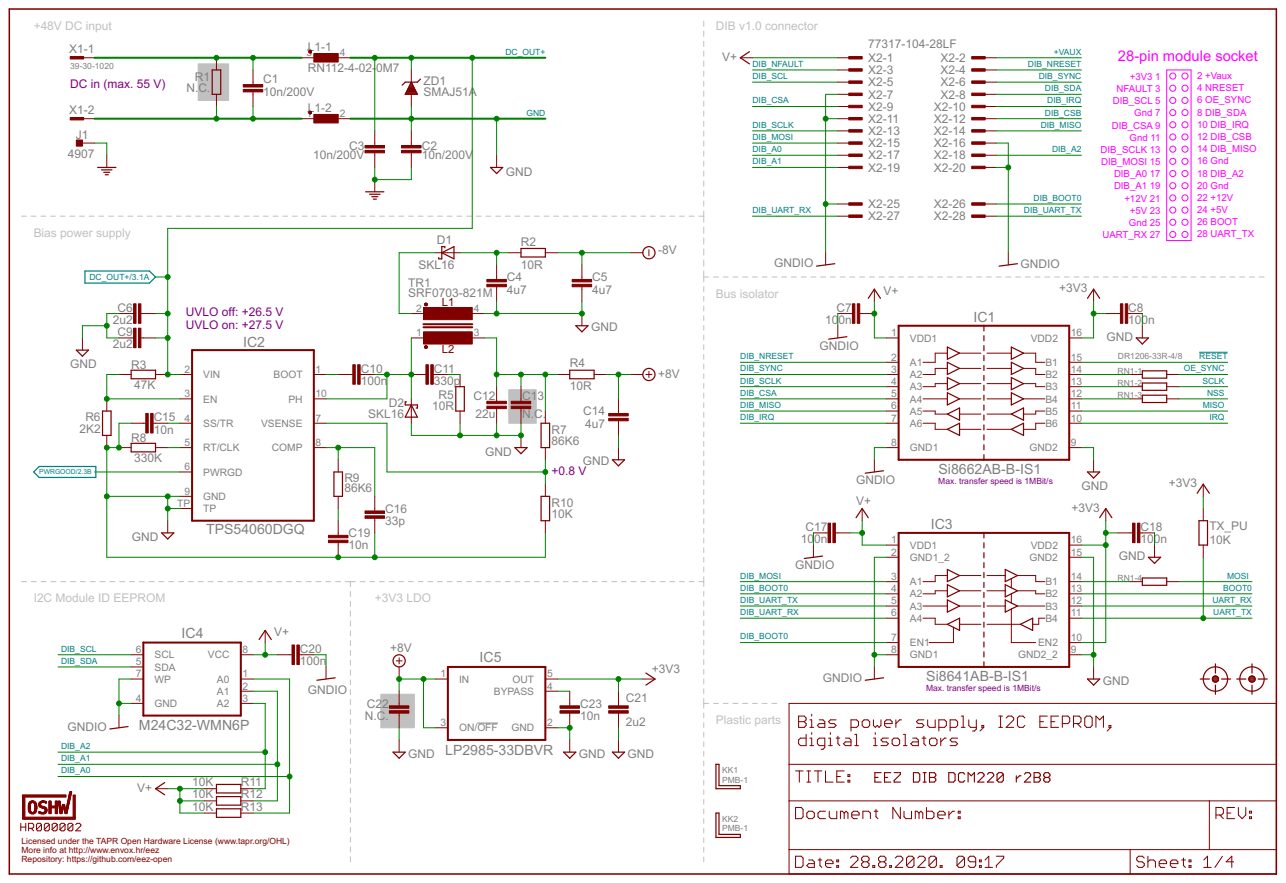
[picture p534: page 1]

Max. transfer speed is 1MBit/s

Licensed under the TAPR Open Hardware License (www.tapr.org/OHL) Repository: https://github.com/eez-open More info at http://www.envox.hr/eez

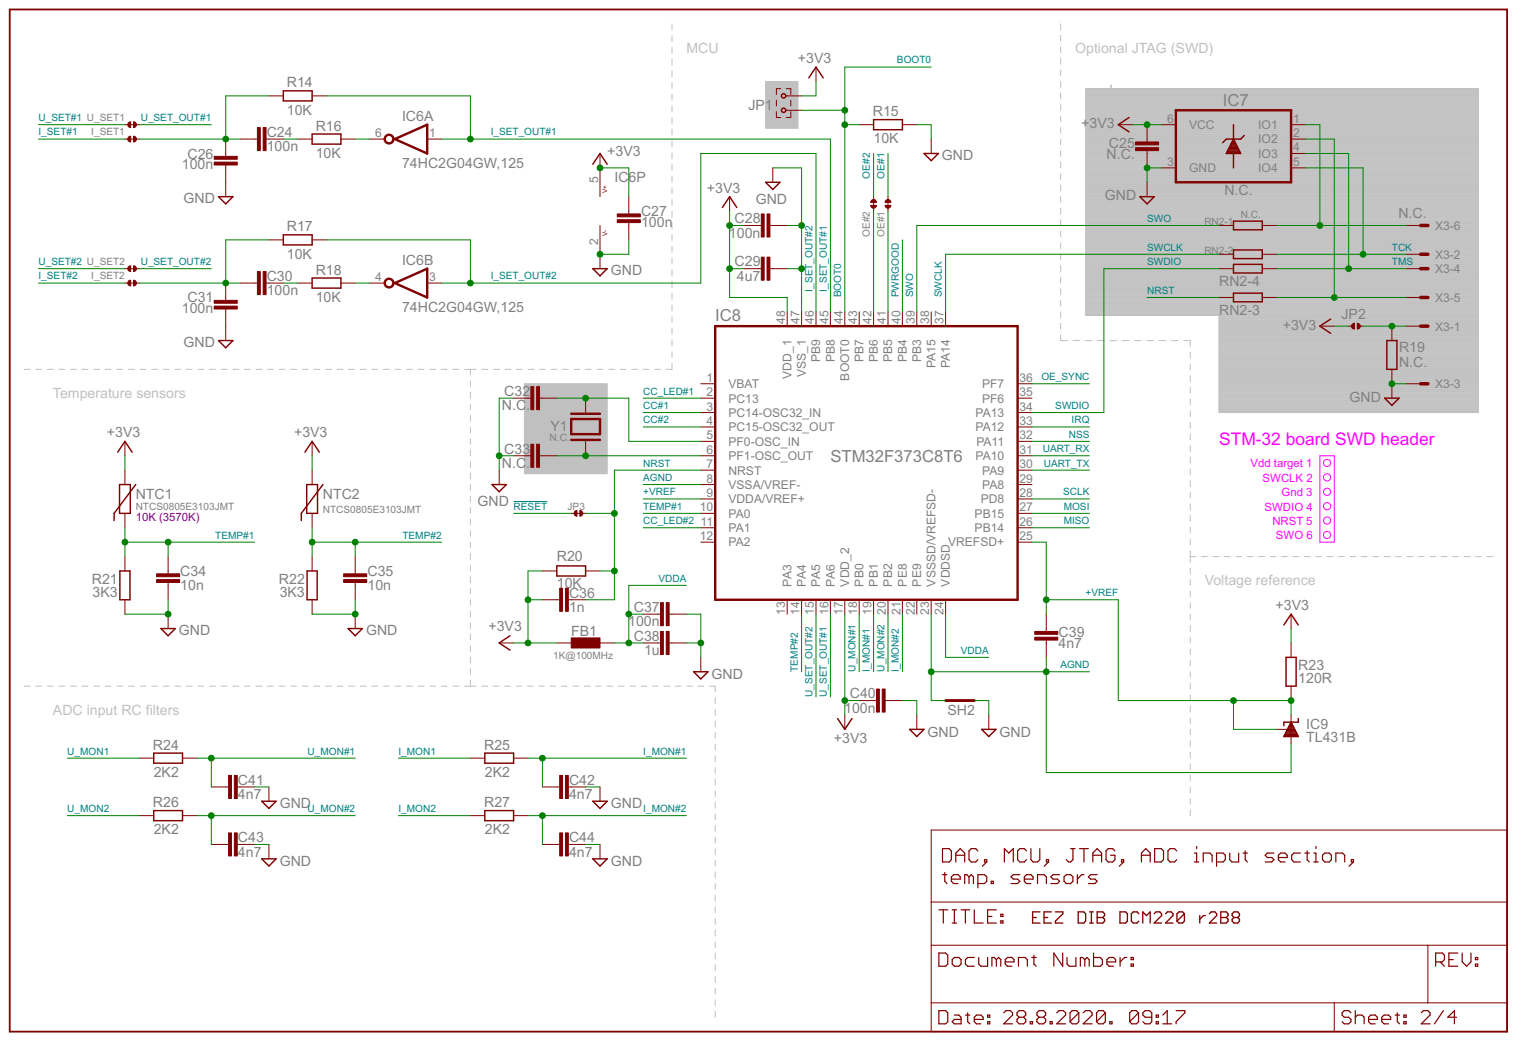
[picture p535: page 2]

C25 | IO2 | 5 VCC 2
N.C. | | | N.C.

IO3 | 4 GND

IO4
N.C.

GND

SWO N.C.

SWDIO | TMS

NRST

SWDIO 4 SWCLK 2 Vdd target 1 STM-32 board SWD header Gnd 3 NRST 5 SWO 6

ADC input RC filters

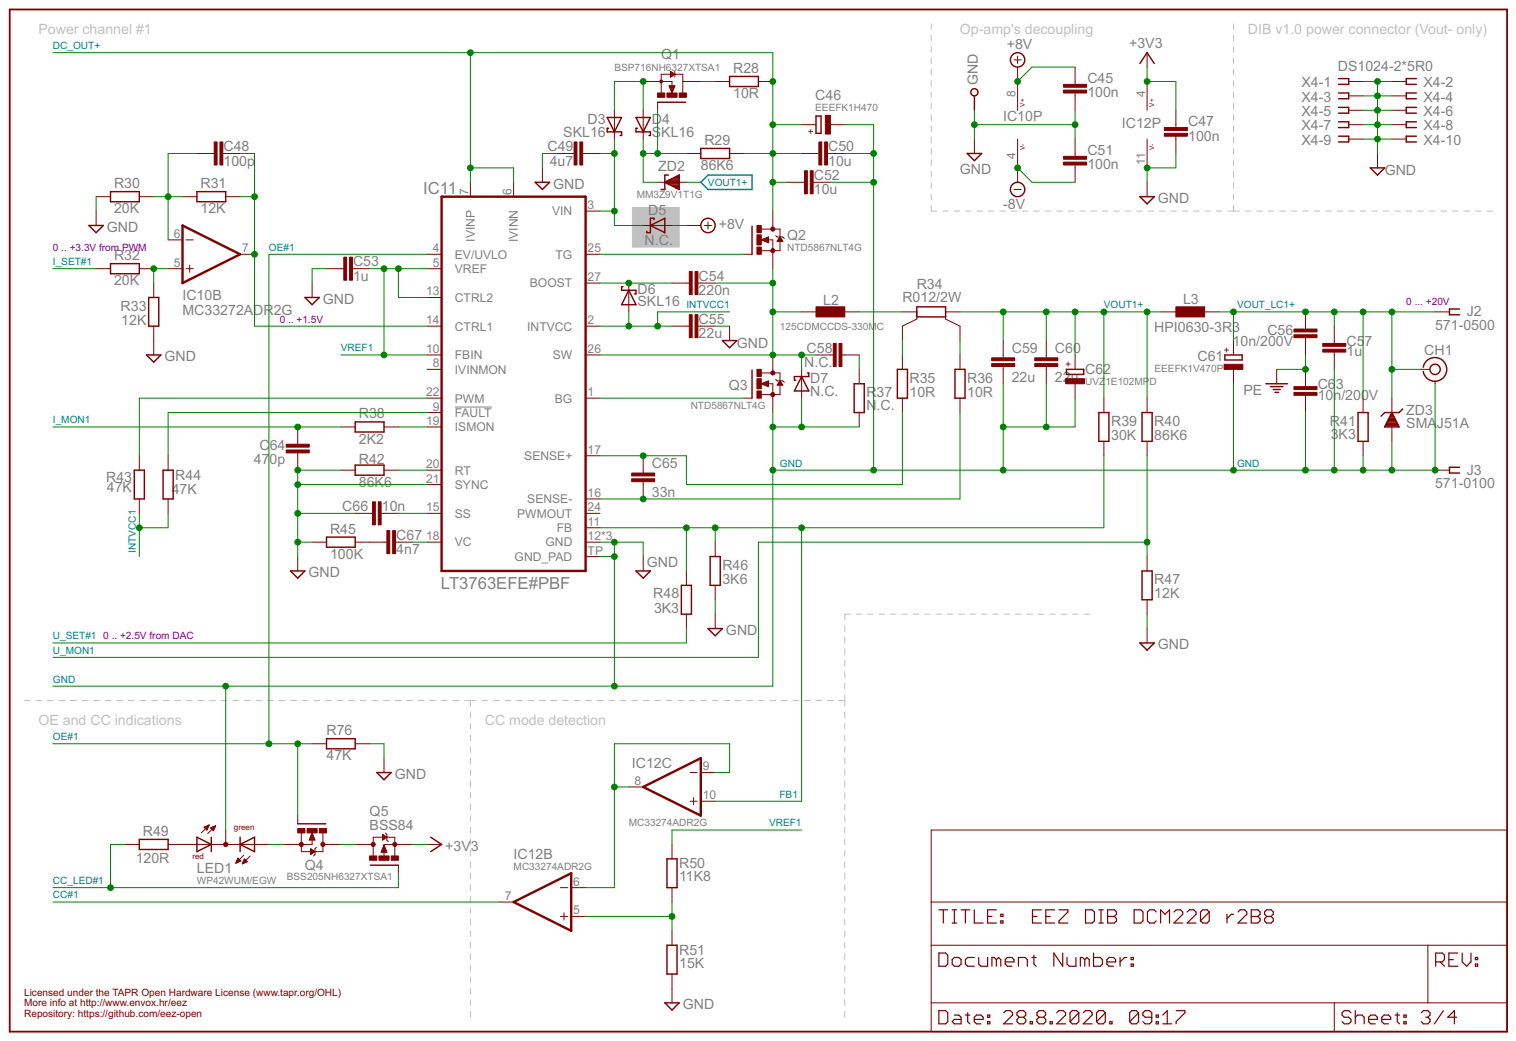
[picture p536: page 3]

OE and CC indications

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

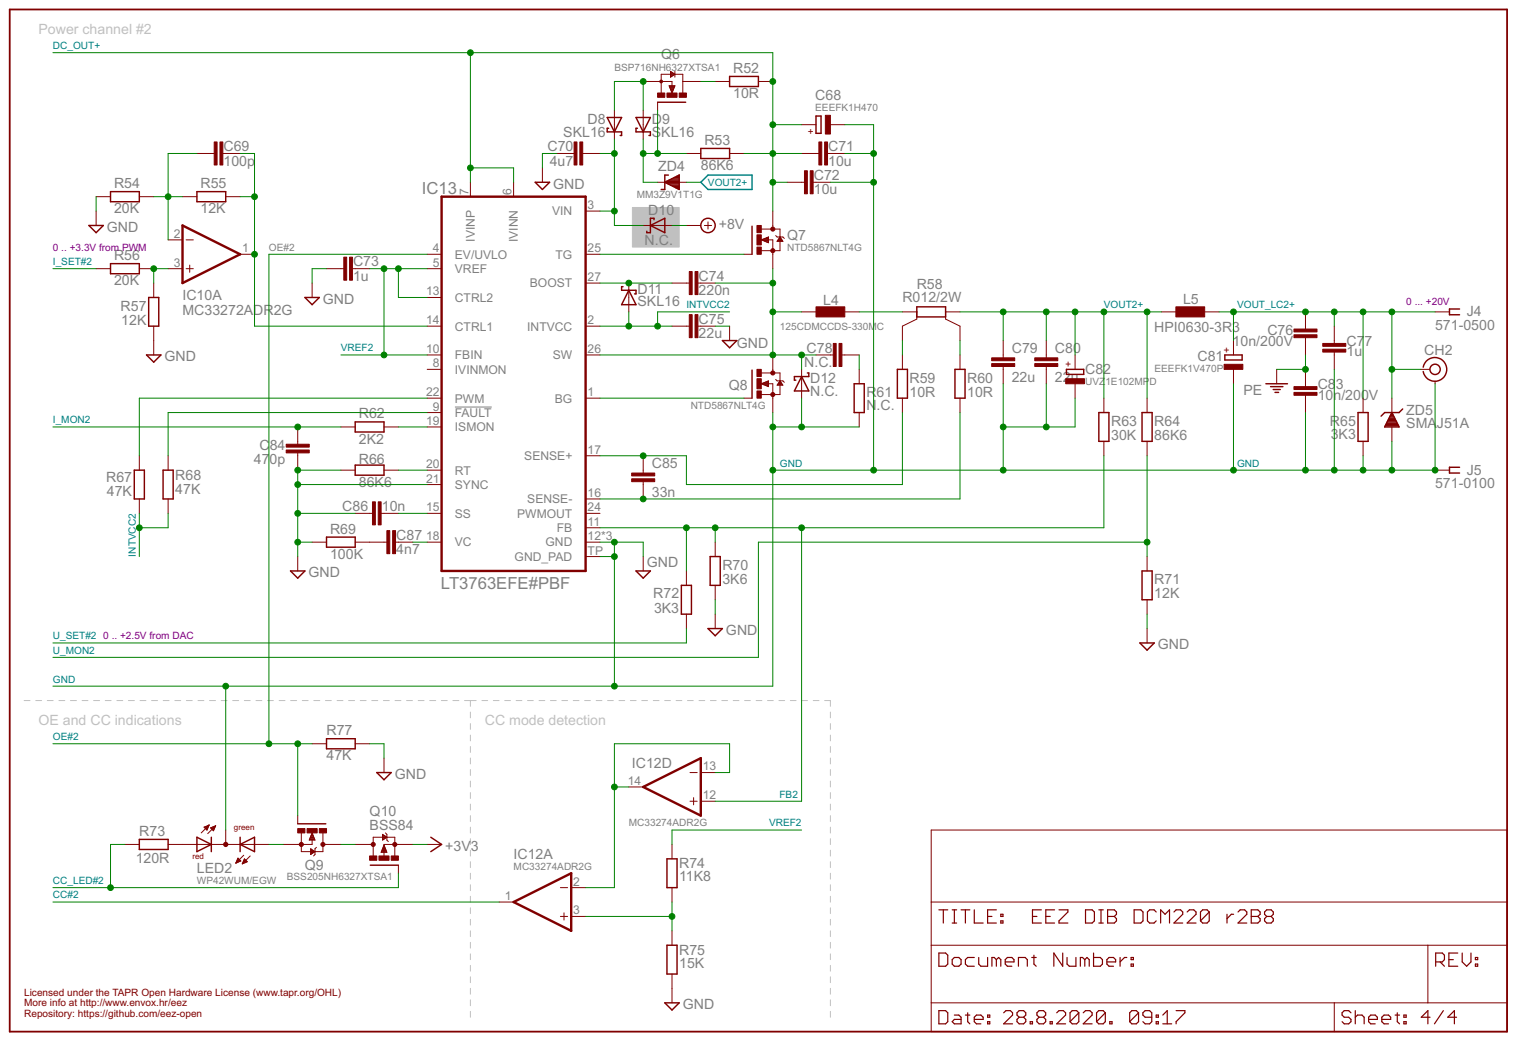
[picture p537: page 4]
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
