eez-open/modular-psu/dcp405/EEZ DIB DCP405 r2B11.pdf

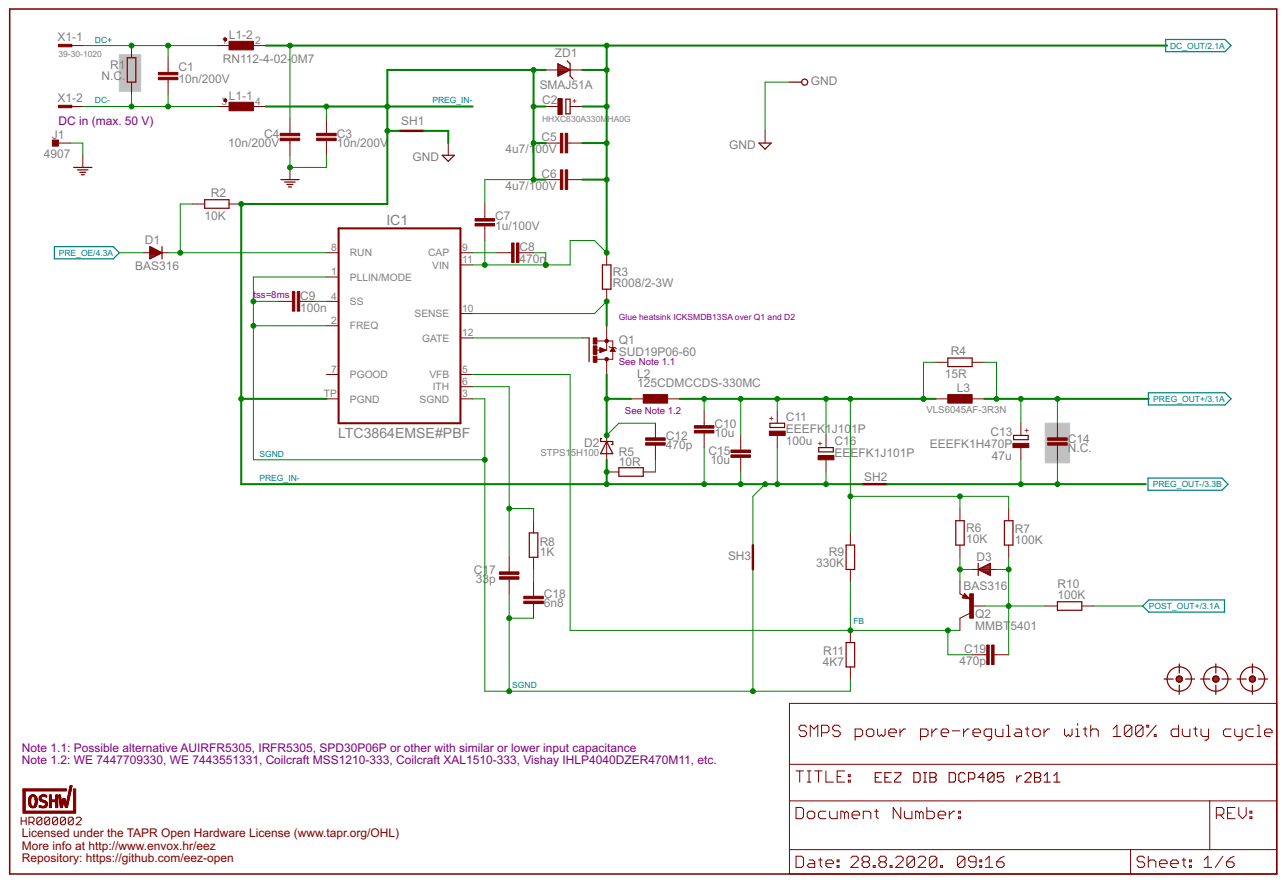
[picture p538: page 1]

Note 1.1: Possible alternative AUIRFR5305, IRFR5305, SPD30P06P or other with similar or lower input capacitance Note 1.2: WE 7447709330, WE 7443551331, Coilcraft MSS1210-333, Coilcraft XAL1510-333, Vishay IHLP4040DZER470M11, etc.

Licensed under the TAPR Open Hardware License (www.tapr.org/OHL)
Repository: https://github.com/eez-open More info at http://www.envox.hr/eez

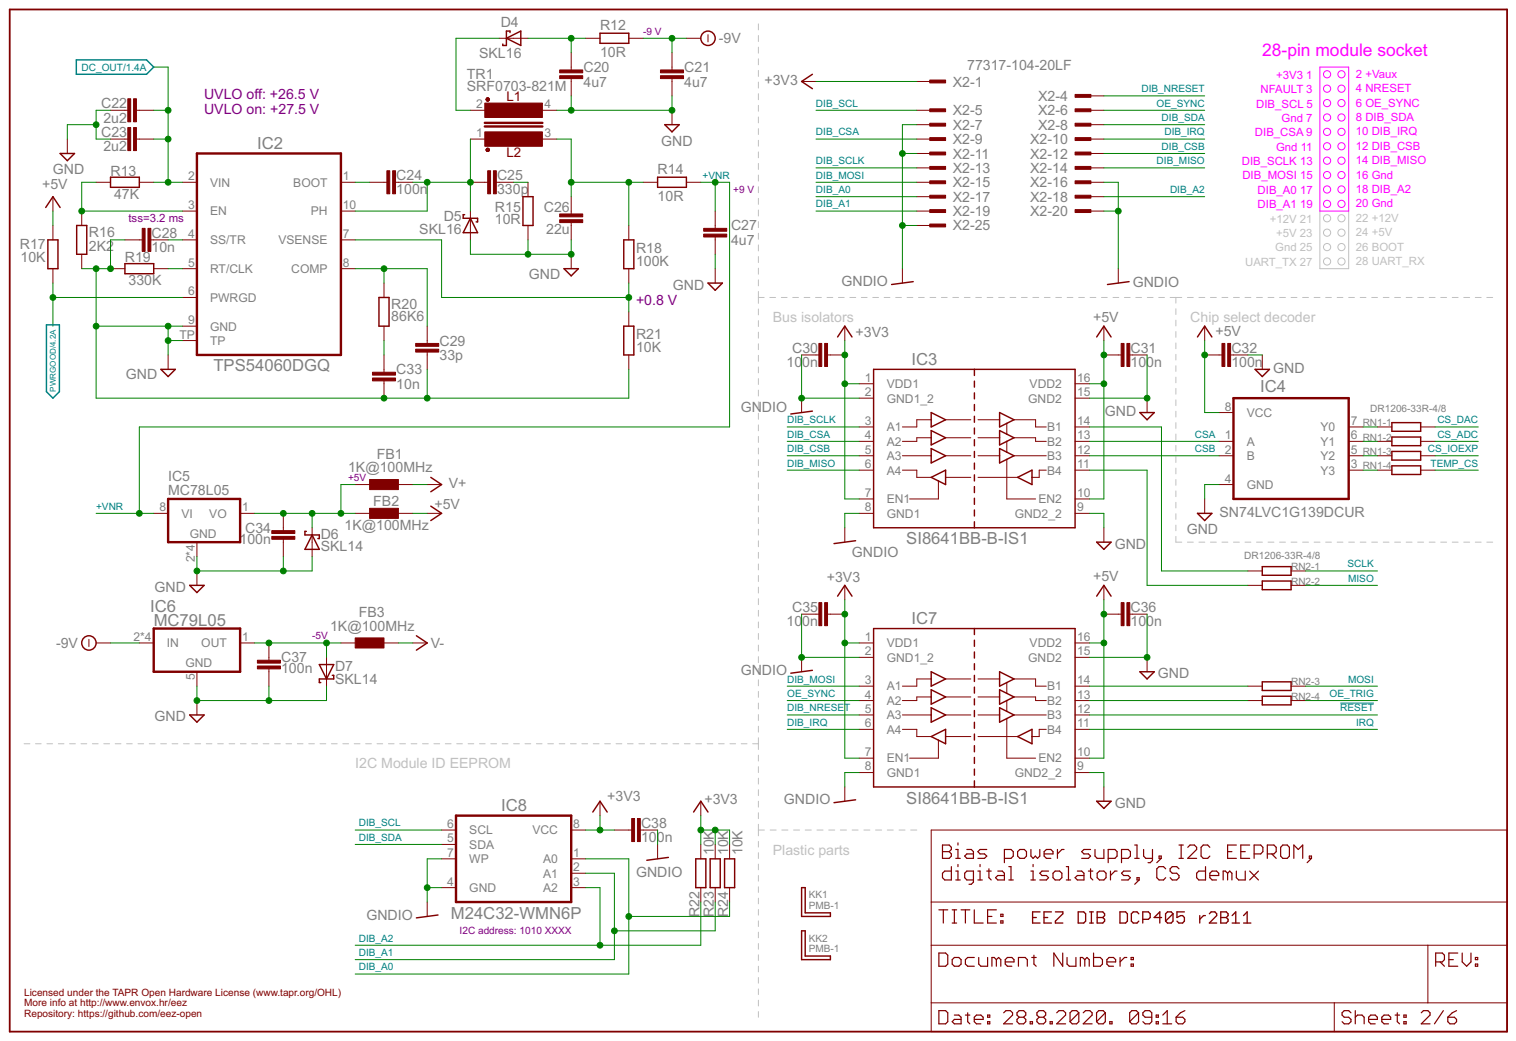
[picture p539: page 2]

TP

CSB

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

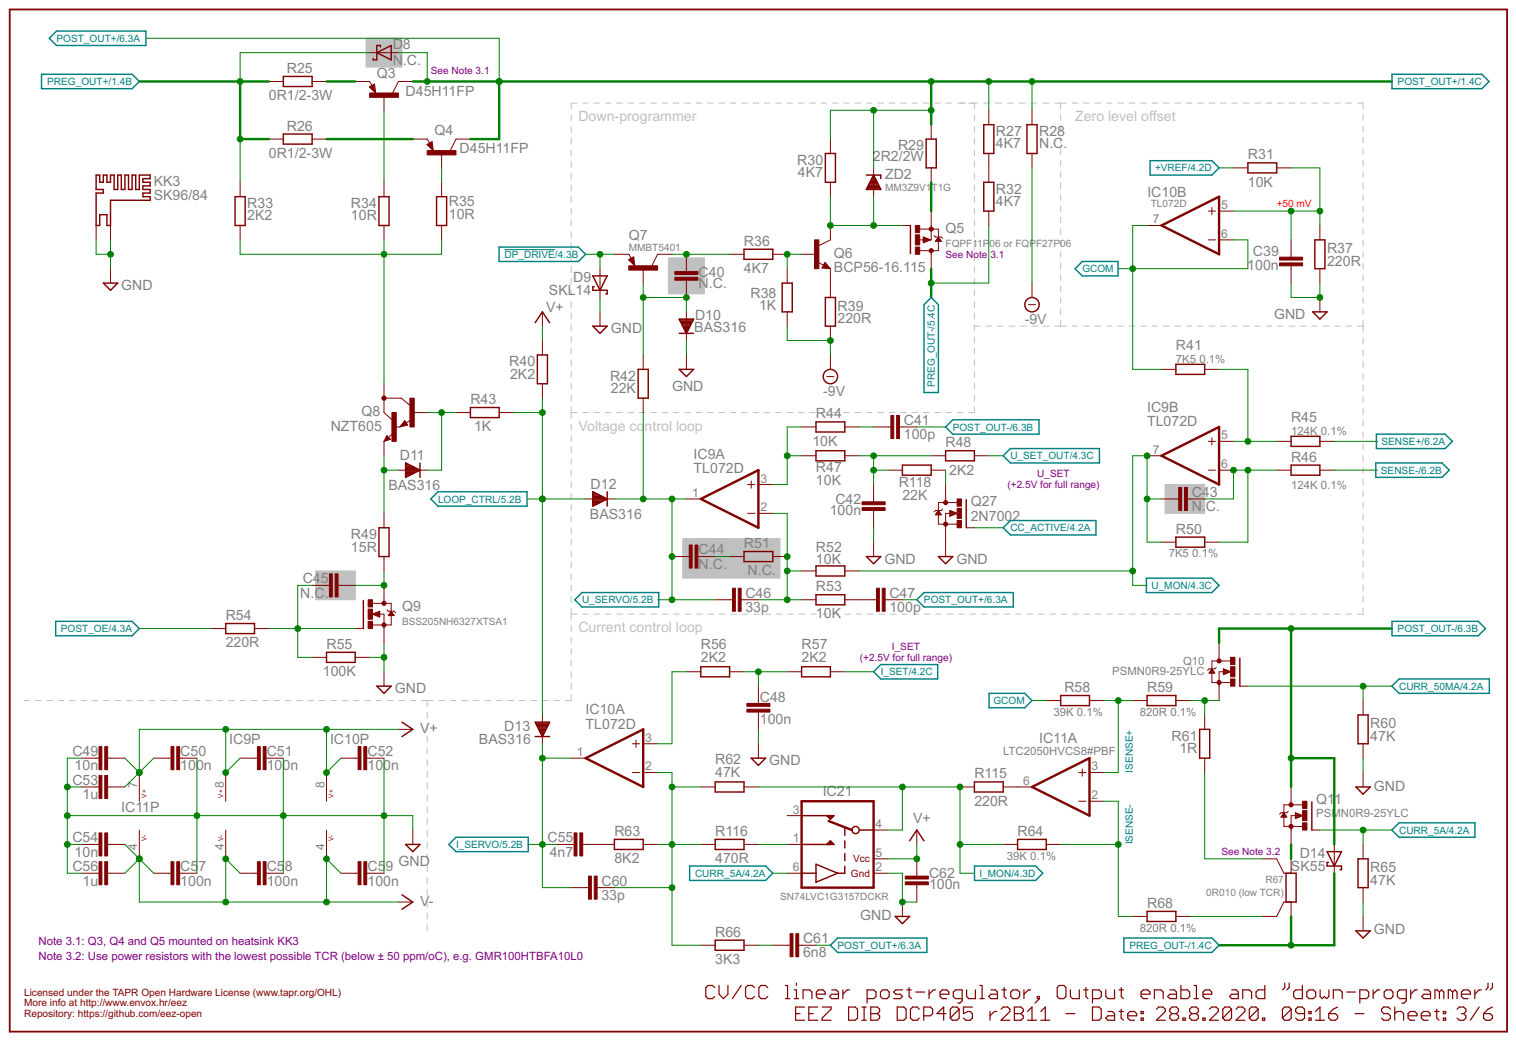
[picture p540: page 3]

Note 3.1: Q3, Q4 and Q5 mounted on heatsink KK3
Note 3.2: Use power resistors with the lowest possible TCR (below ± 50 ppm/oC), e.g. GMR100HTBFA10L0

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

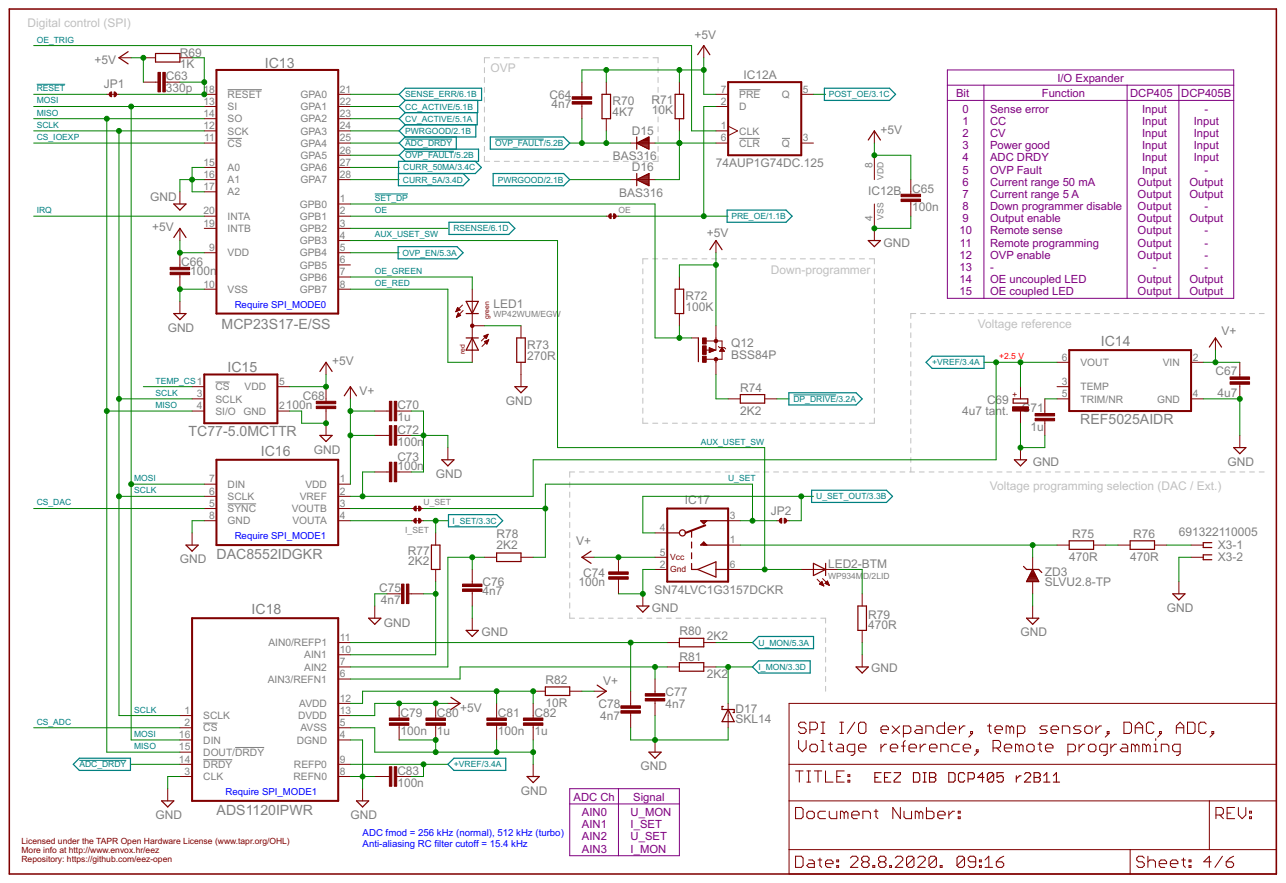
[picture p541: page 4]

Voltage programming selection (DAC / Ext.)

ADC Ch | Signal
AIN0 AIN1 AIN2 AIN3 | U_MON I_SET U_SET I_MON

ADC fmod = 256 kHz (normal), 512 kHz (turbo) Anti-aliasing RC filter cutoff = 15.4 kHz

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

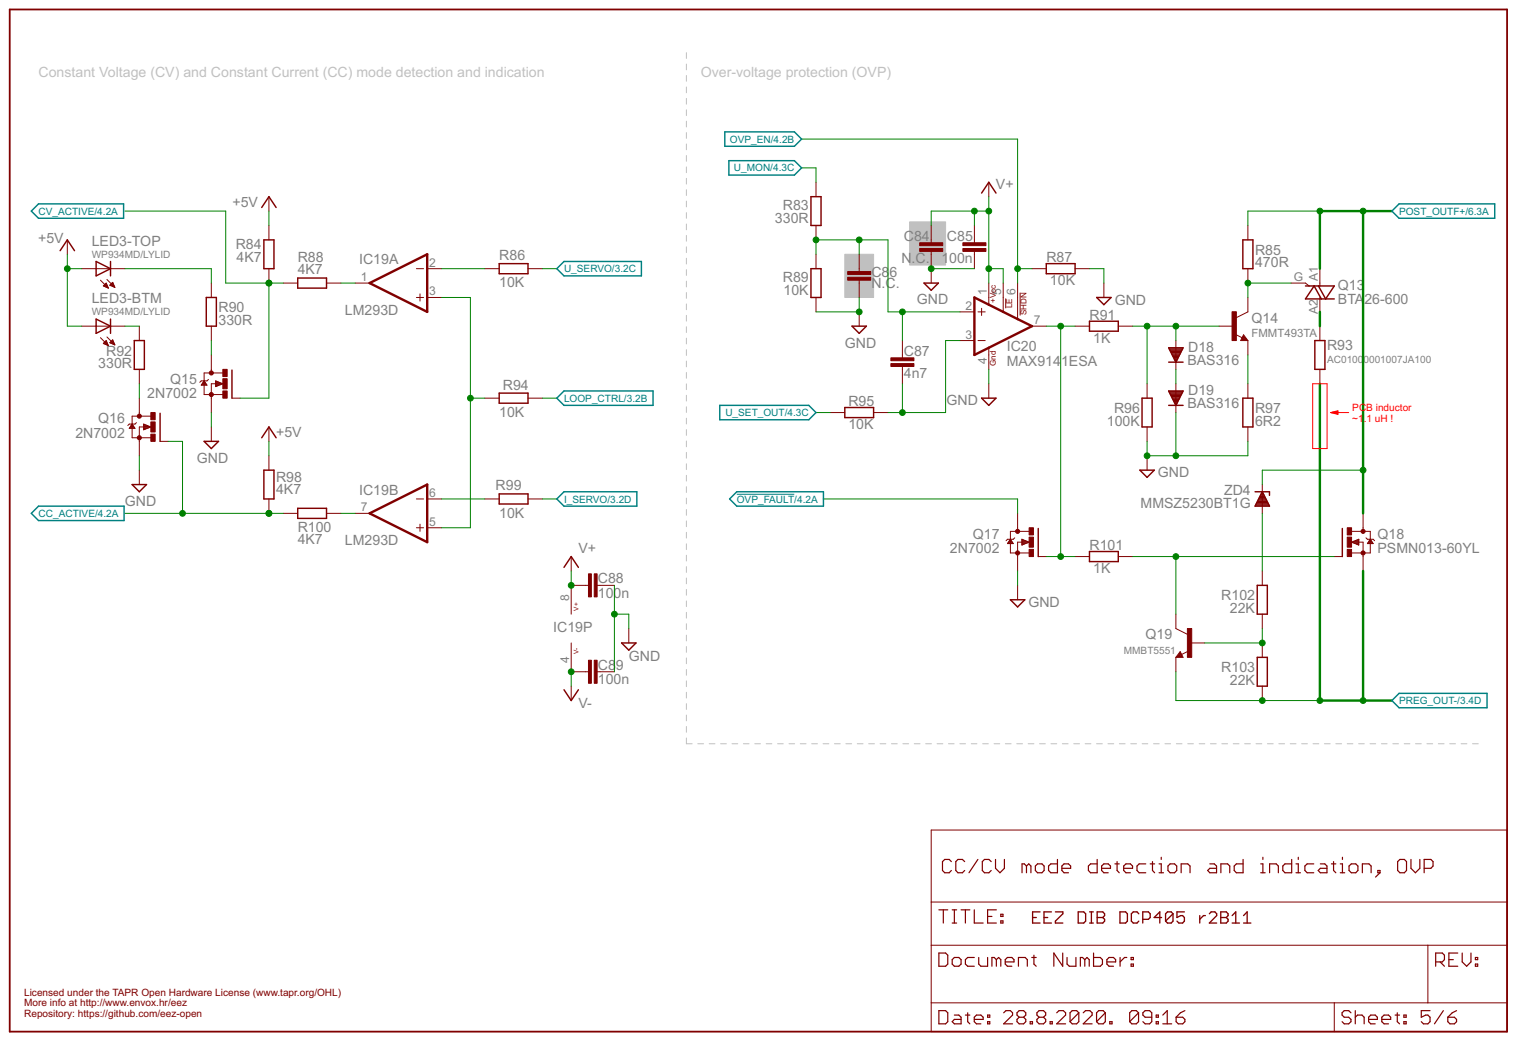
[picture p542: page 5]
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

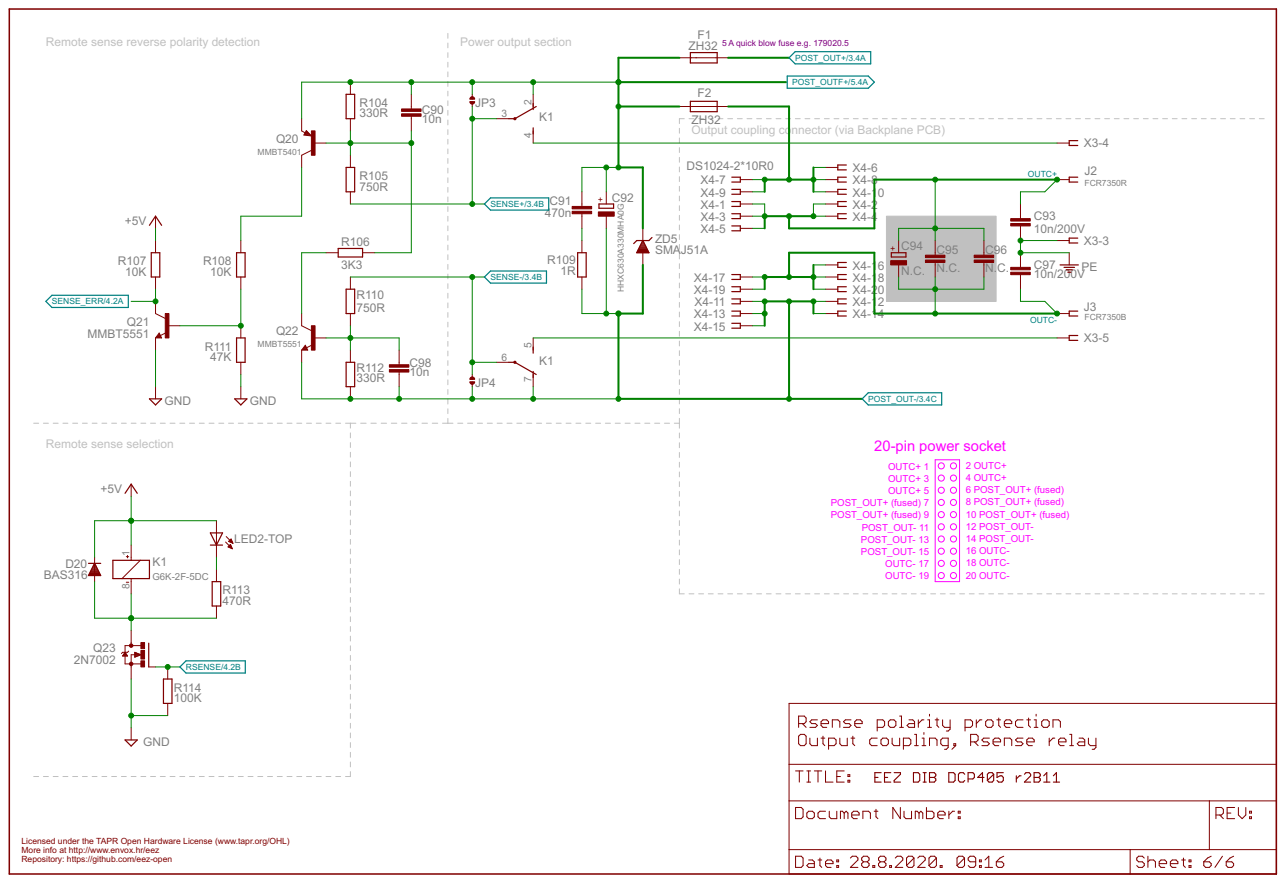
[picture p543: page 6]

Remote sense reverse polarity detection

Output coupling connector (via Backplane PCB)

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
