eez-open/modular-psu/aux-ps/EEZ DIB AUX PS r3B3.pdf

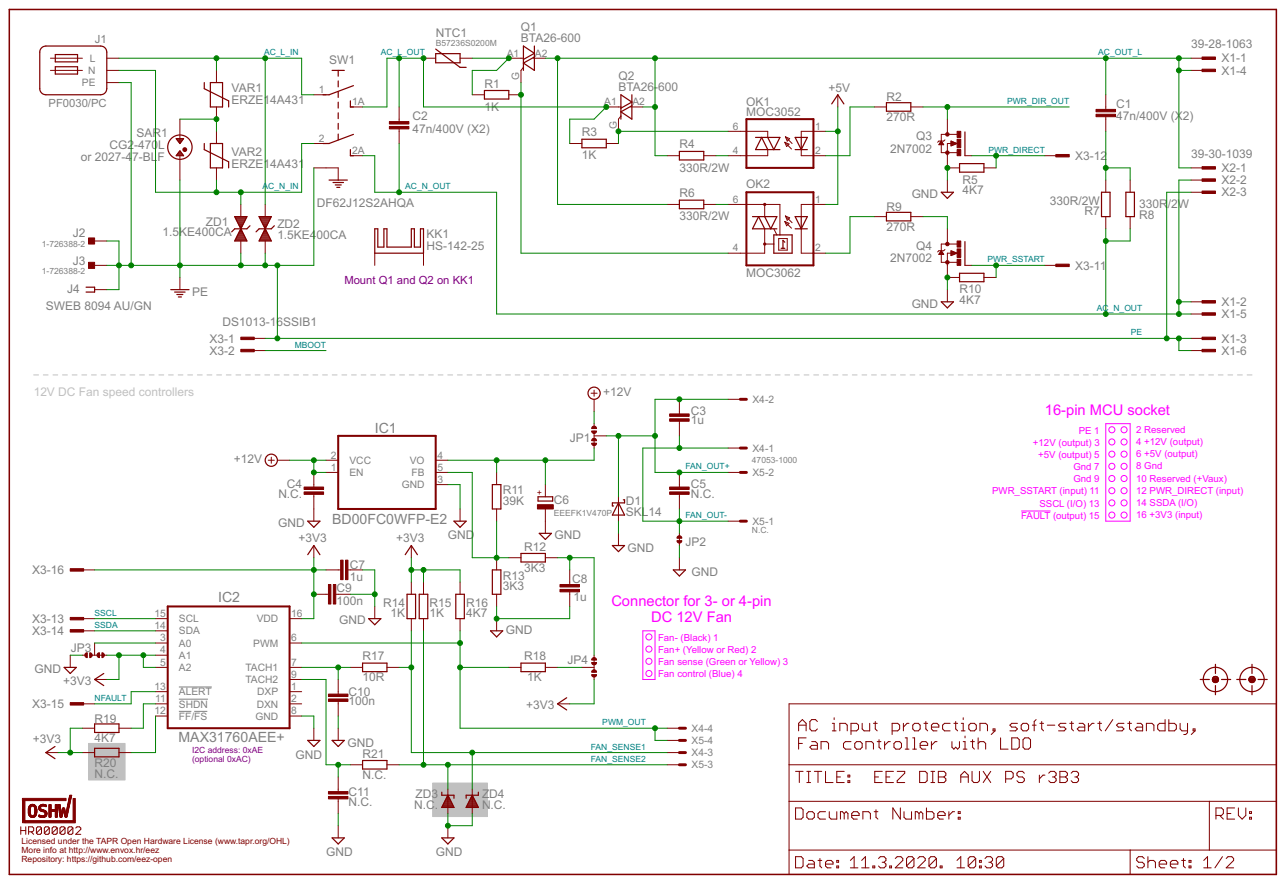
[picture p544: page 1]

12V DC Fan speed controllers

Fan+ (Yellow or Red) 2 Fan- (Black) 1 Connector for 3- or 4-pin
DC 12V Fan

Fan sense (Green or Yellow) 3 Fan control (Blue) 4

Licensed under the TAPR Open Hardware License (www.tapr.org/OHL) Repository: https://github.com/eez-open More info at http://www.envox.hr/eez

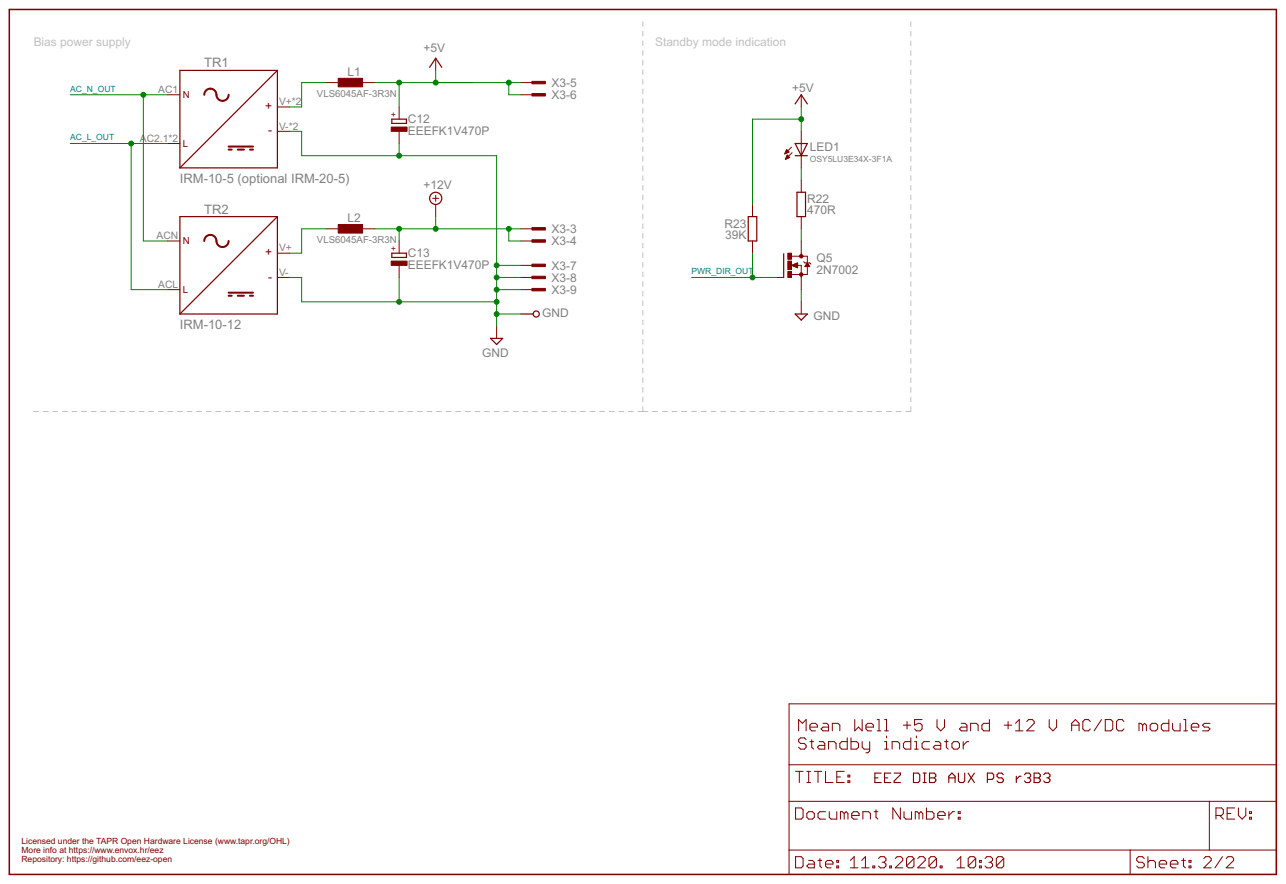
[picture p545: page 2]

Licensed under the TAPR Open Hardware License (www.tapr.org/OHL) Repository: https://github.com/eez-open More info at https://www.envox.hr/eez
