eez-open/modular-psu/enclosure/Front panel silkscreen.pdf

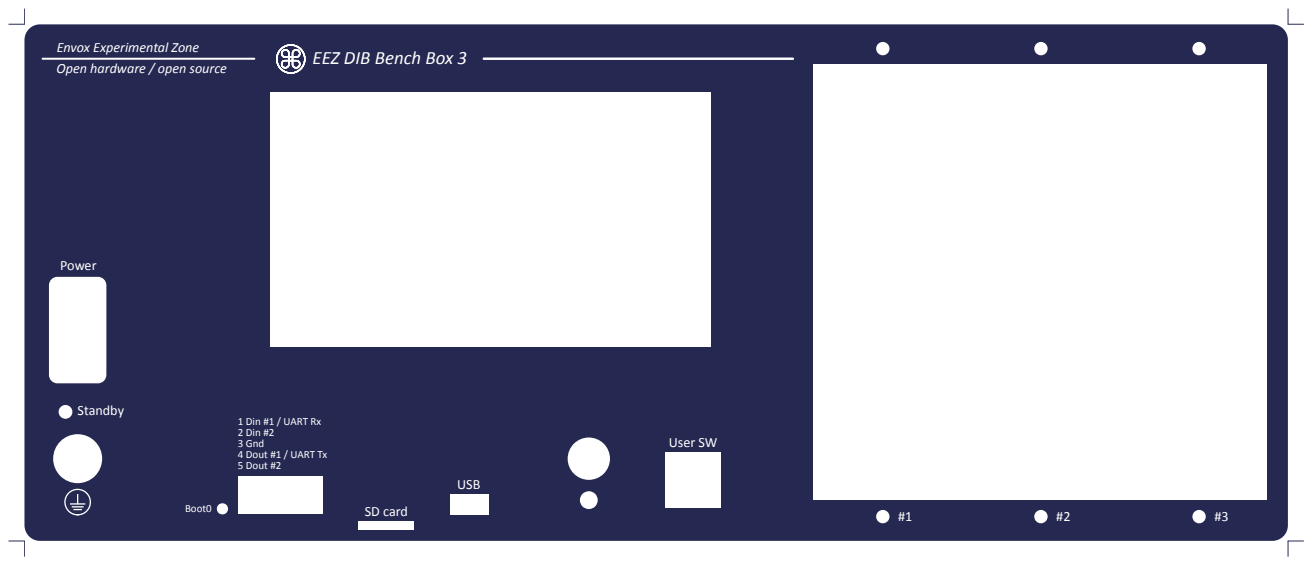
[picture p546: page 1]
#3 SD card; USB; Standby; User SW; Power; Boot0

EEZ DIB Bench Box 3 Envox Experimental Zone
Open hardware / open source

1 Din #1 / UART Rx
2 Din #2
3 Gnd
4 Dout #1 / UART Tx
5 Dout #2
