eez-open/modular-psu/enclosure/Rear panel silkscreen.pdf

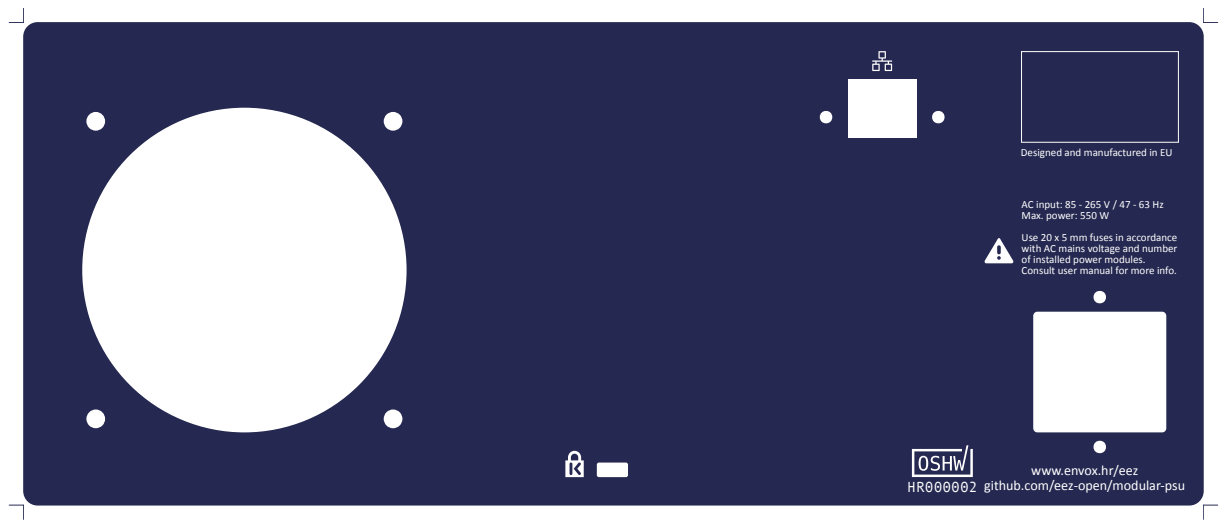
[picture p547: page 1]

Designed and manufactured in EU

AC input: 85 - 265 V / 47 - 63 Hz
Max. power: 550 W

Use 20 x 5 mm fuses in accordance
with AC mains voltage and number
of installed power modules.
Consult user manual for more info.

www.envox.hr/eez

github.com/eez-open/modular-psu
