eez-open/modular-psu/bp3c/EEZ DIB BP3C r2B3.pdf

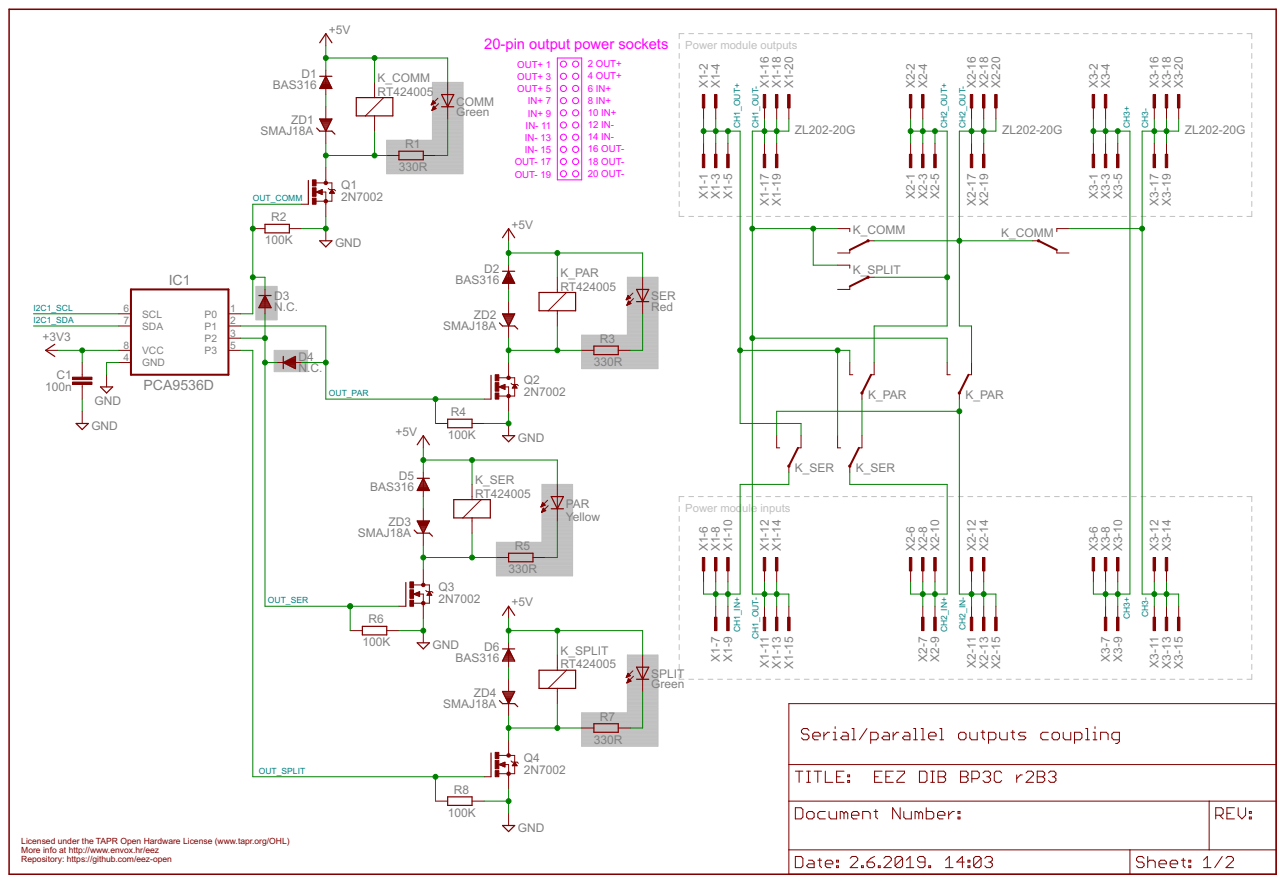
[picture p548: page 1]

6 IN+ 20-pin output power sockets

Licensed under the TAPR Open Hardware License (www.tapr.org/OHL) Repository: https://github.com/eez-open More info at http://www.envox.hr/eez

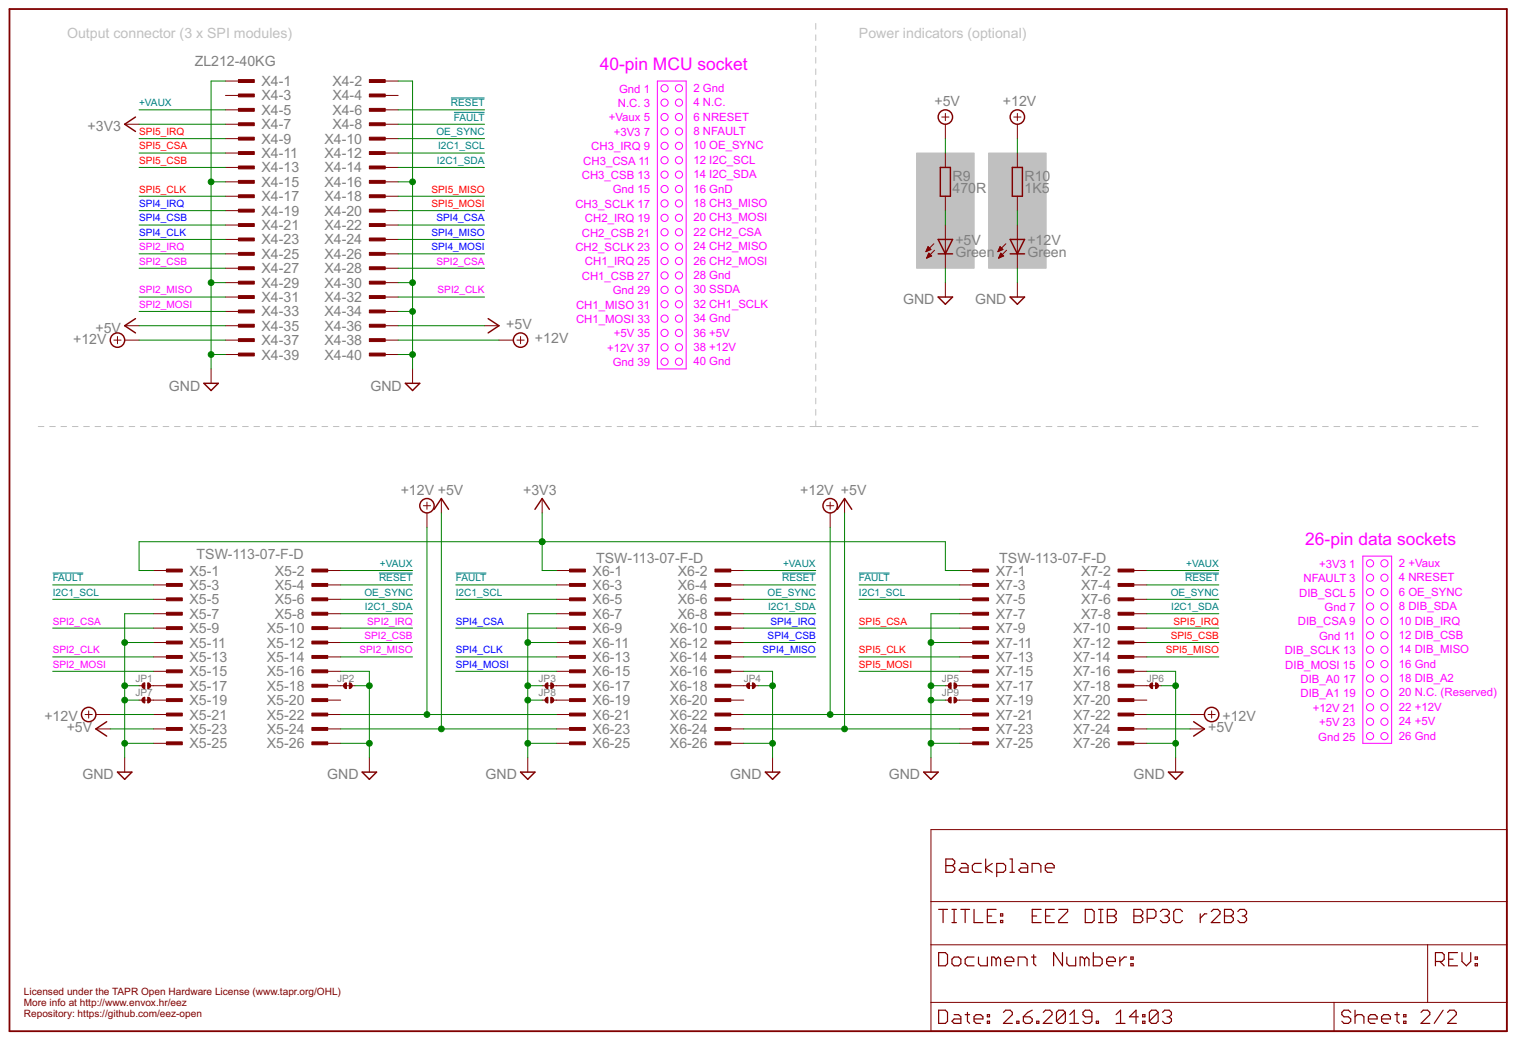
[picture p549: page 2]
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
