eez-open/modular-psu/dcp505/EEZ DIB DCP505 r1B3.pdf

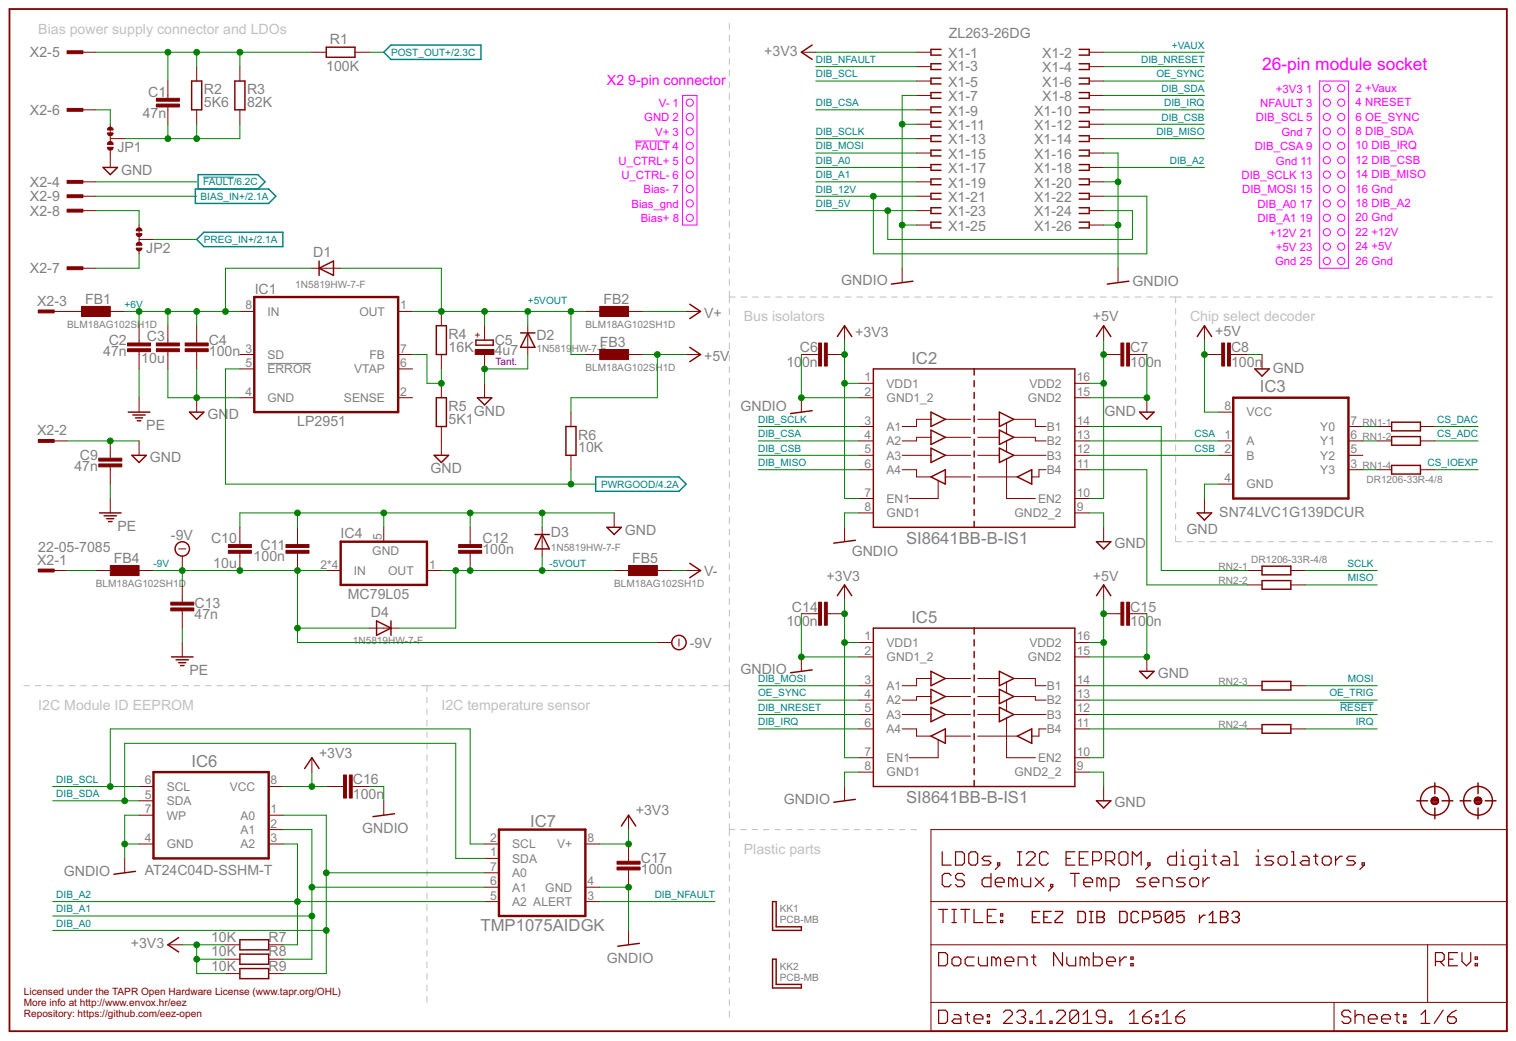
[picture p550: page 1]

Bias power supply connector and LDOs

18 DIB_A2 U_CTRL+ 5 Bias_gnd Bias- 7 FAULT 4 V+ 3 GND 2 V- 1 U_CTRL- 6 Bias+ 8

Licensed under the TAPR Open Hardware License (www.tapr.org/OHL) Repository: https://github.com/eez-open More info at http://www.envox.hr/eez

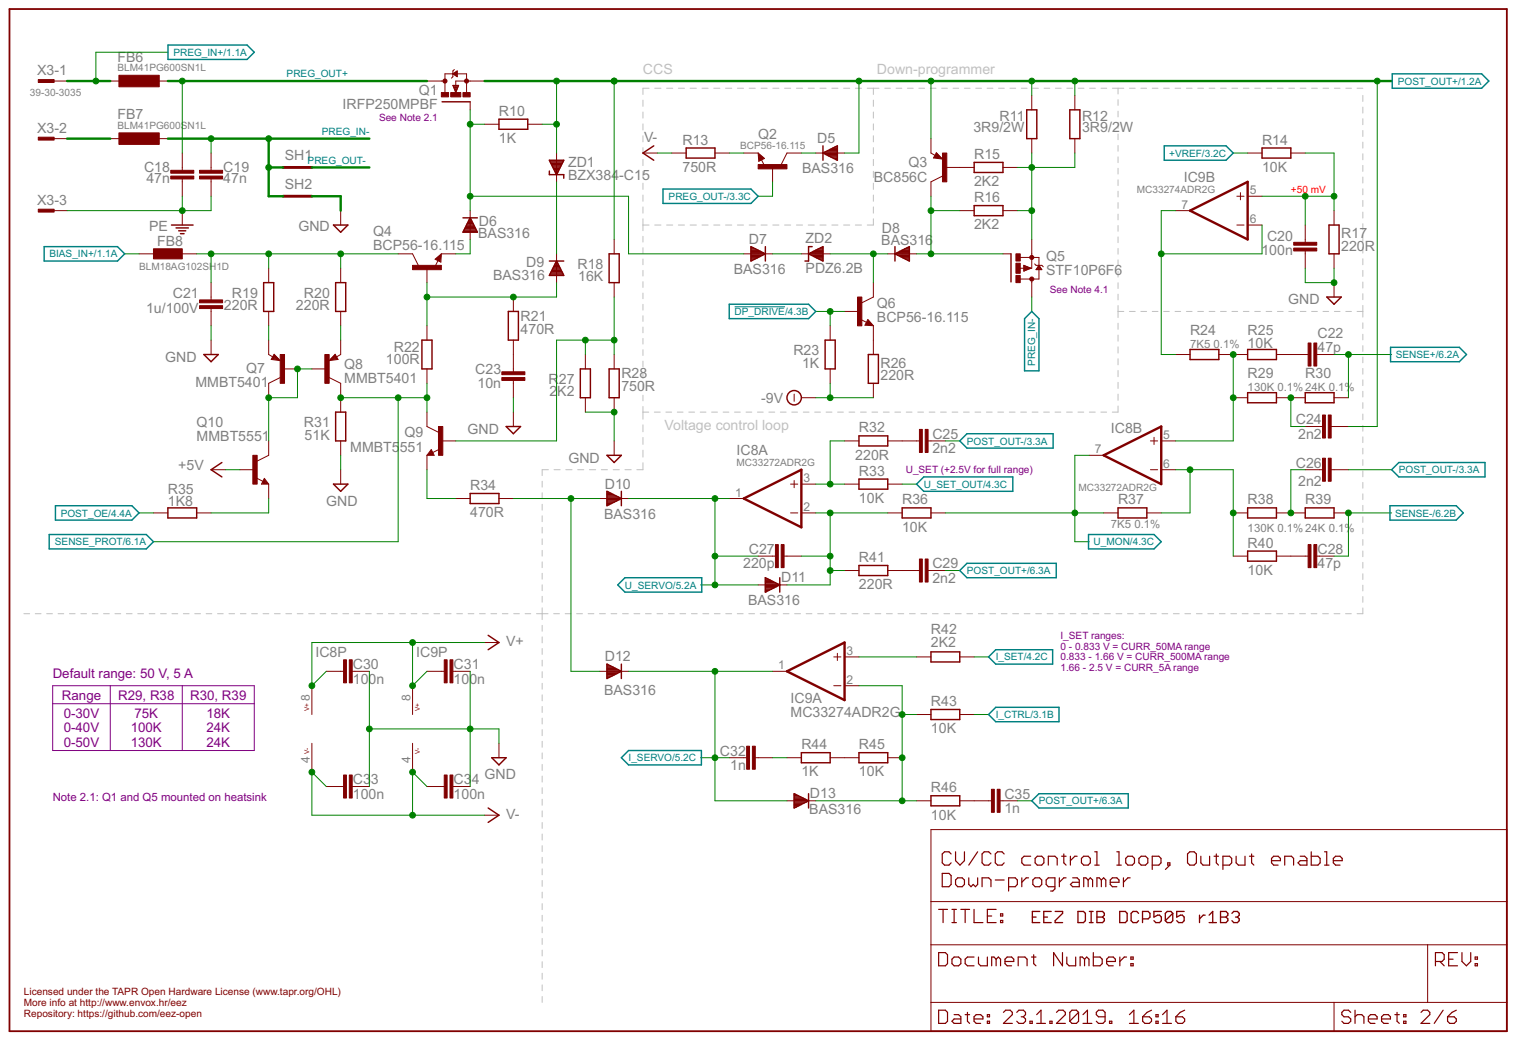
[picture p551: page 2]

Note 2.1: Q1 and Q5 mounted on heatsink

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

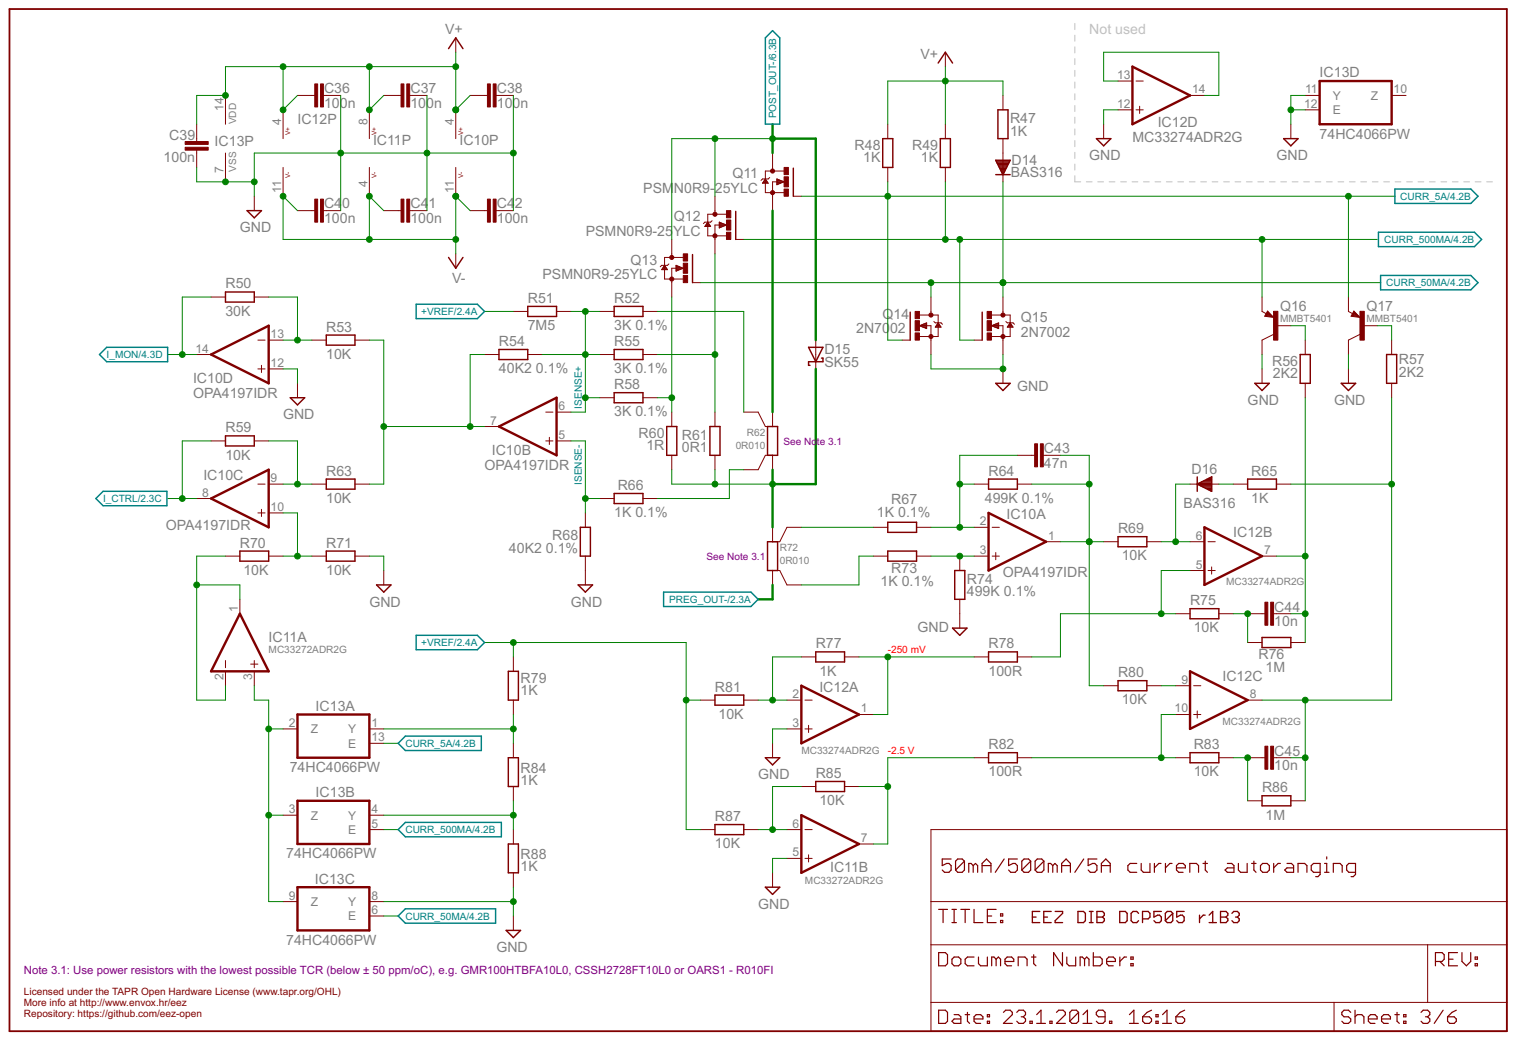
[picture p552: page 3]

Note 3.1: Use power resistors with the lowest possible TCR (below ± 50 ppm/oC), e.g. GMR100HTBFA10L0, CSSH2728FT10L0 or OARS1 - R010FI

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

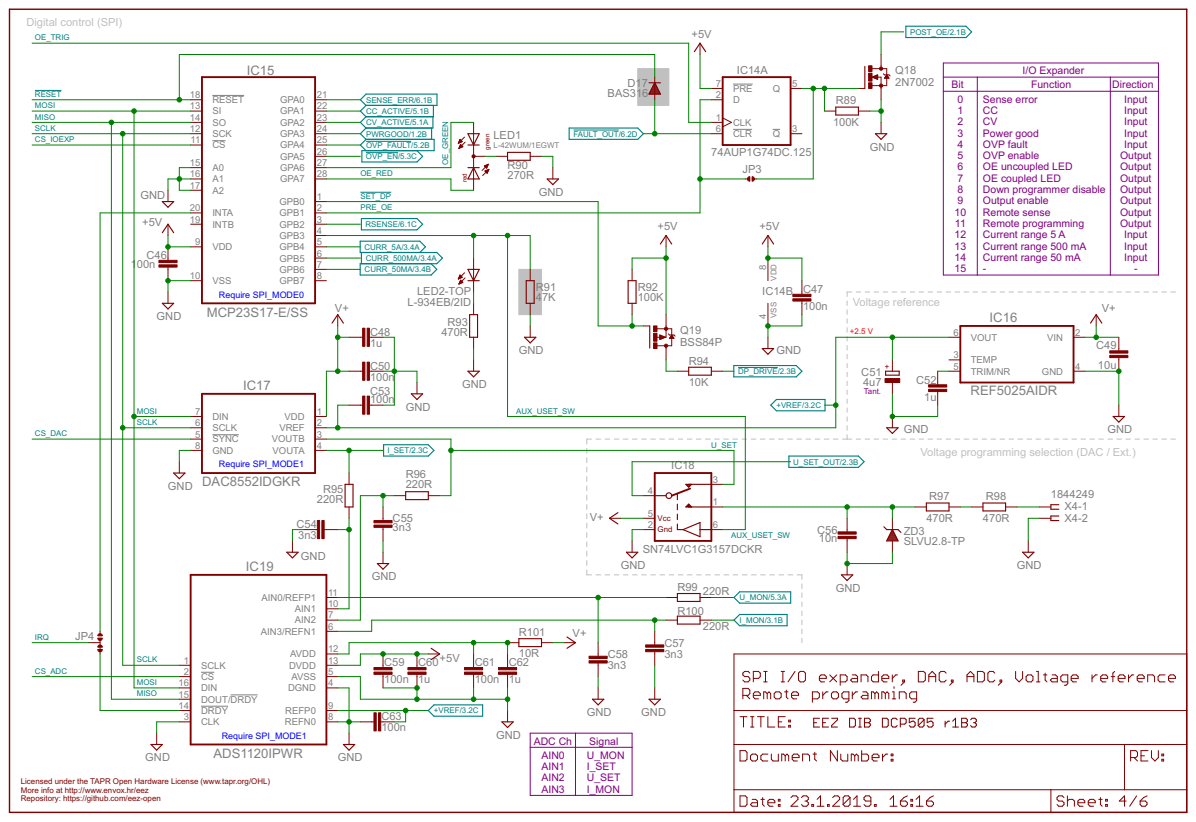
[picture p553: page 4]

GND
Voltage programming selection (DAC / Ext.)

ADC Ch | Signal
AIN0 AIN1 AIN2 AIN3 | U_MON I_SET U_SET I_MON

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

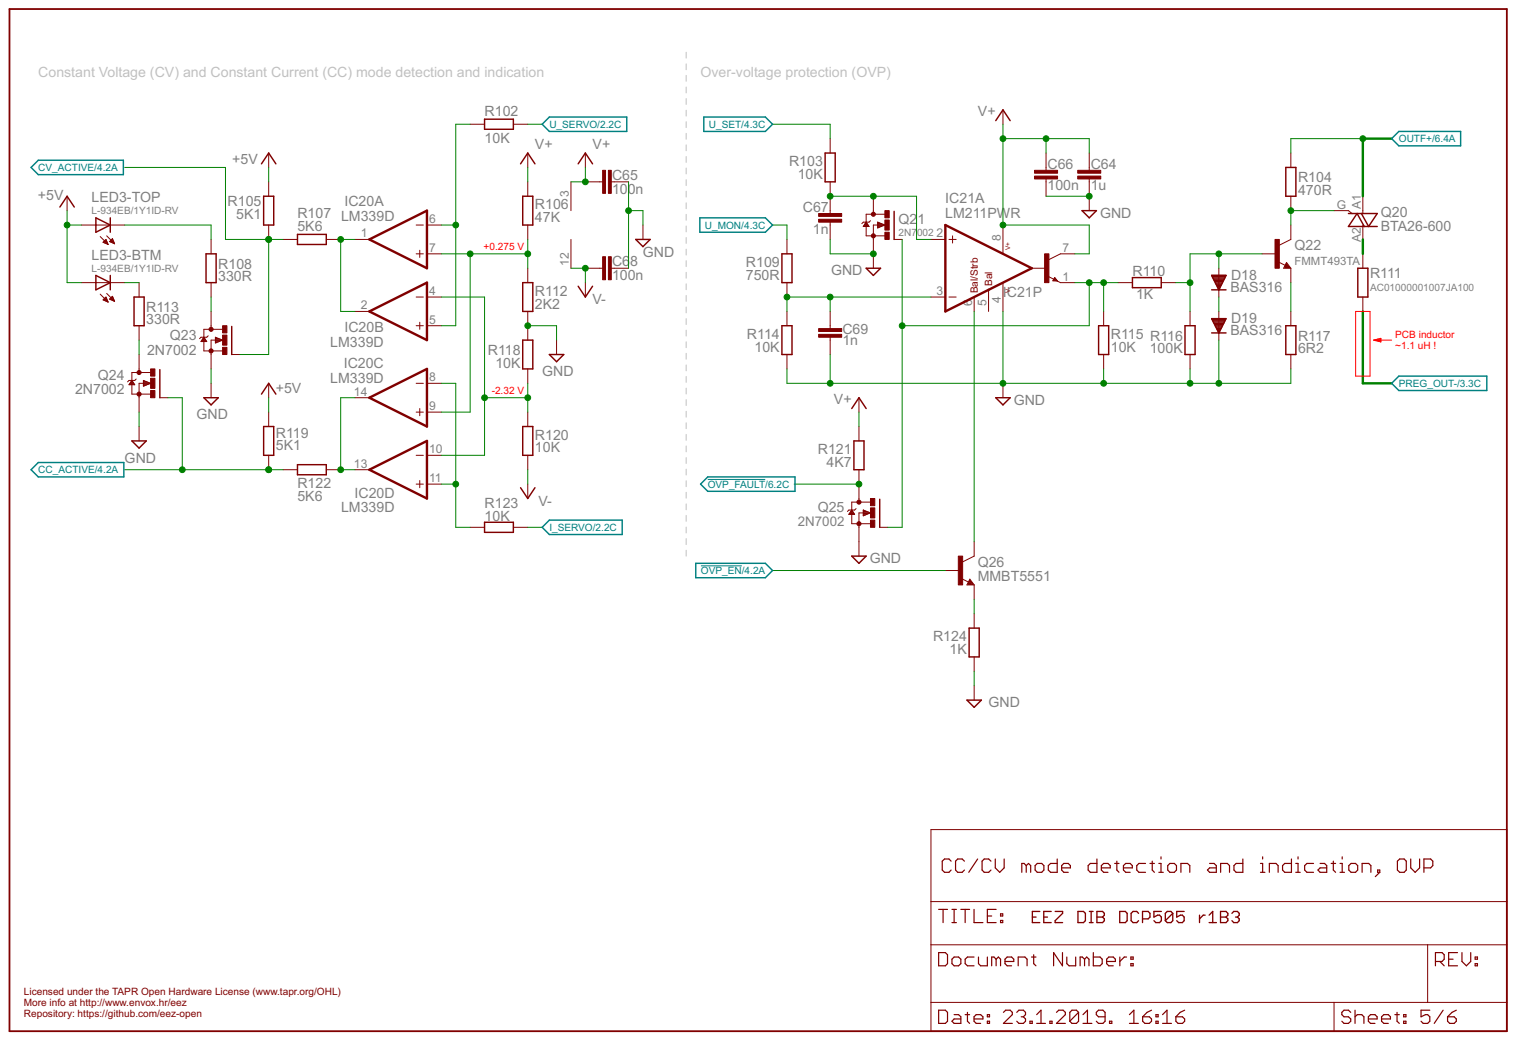
[picture p554: page 5]
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

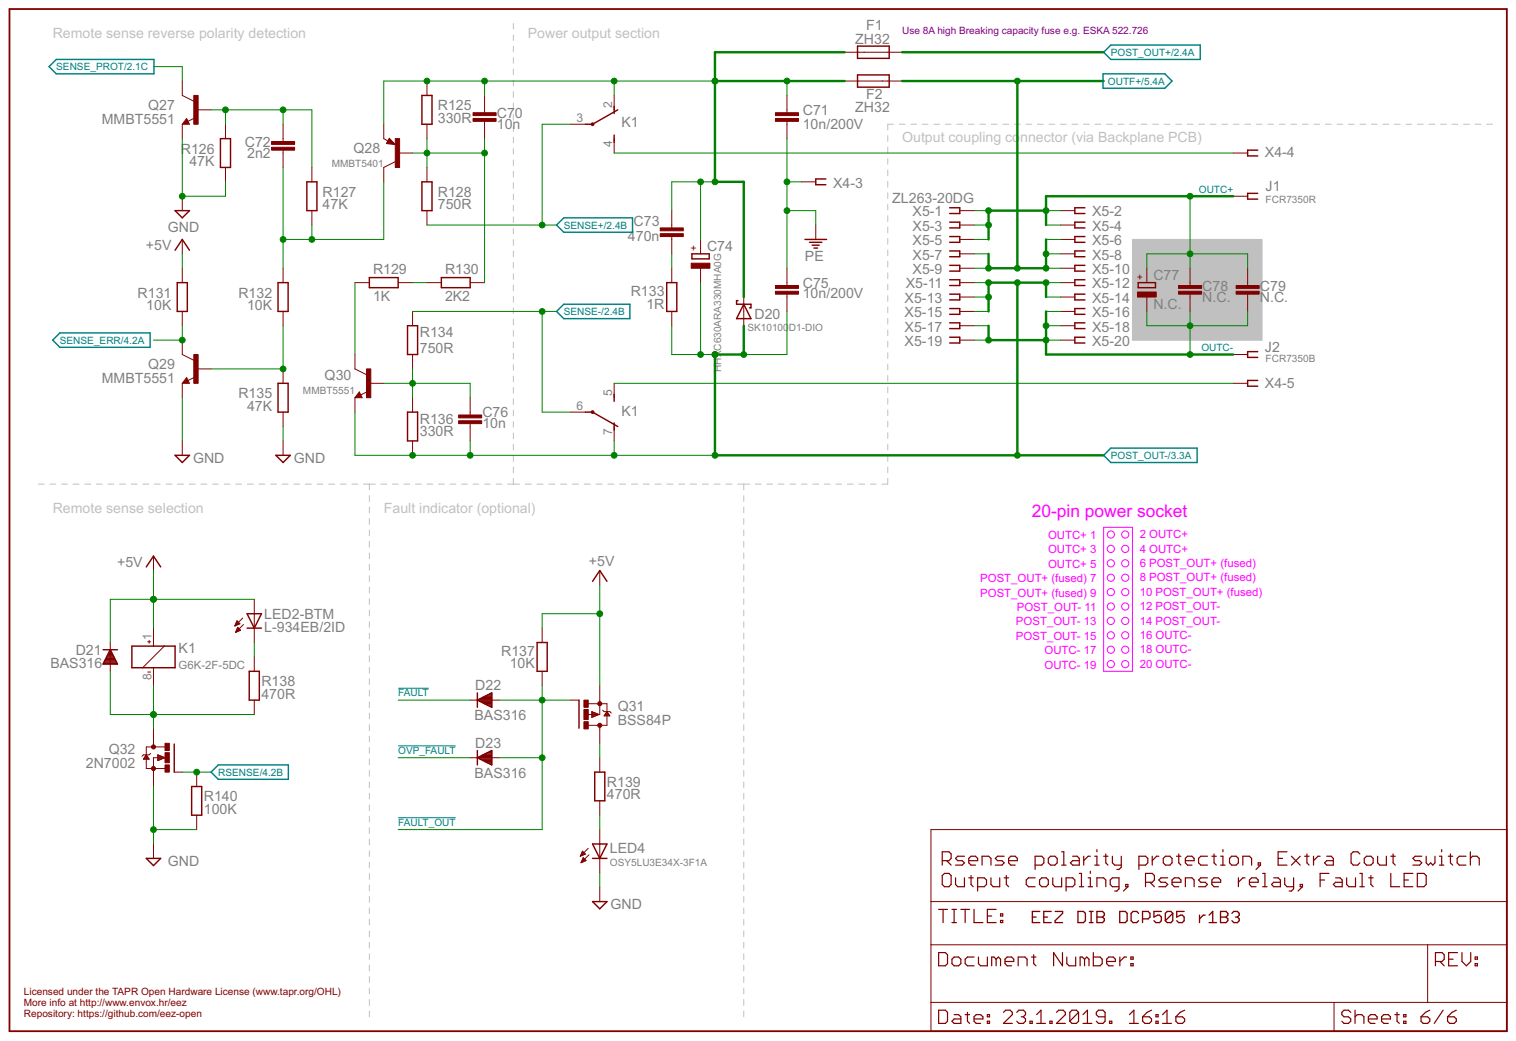
[picture p555: page 6]

Remote sense reverse polarity detection

Use 8A high Breaking capacity fuse e.g. ESKA 522.726

Output coupling connector (via Backplane PCB)

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
