eez-open/modular-psu/PRELIMINARY/DCP405 r4 (with MCU)/EEZ DIB DCP405 r4B2.pdf

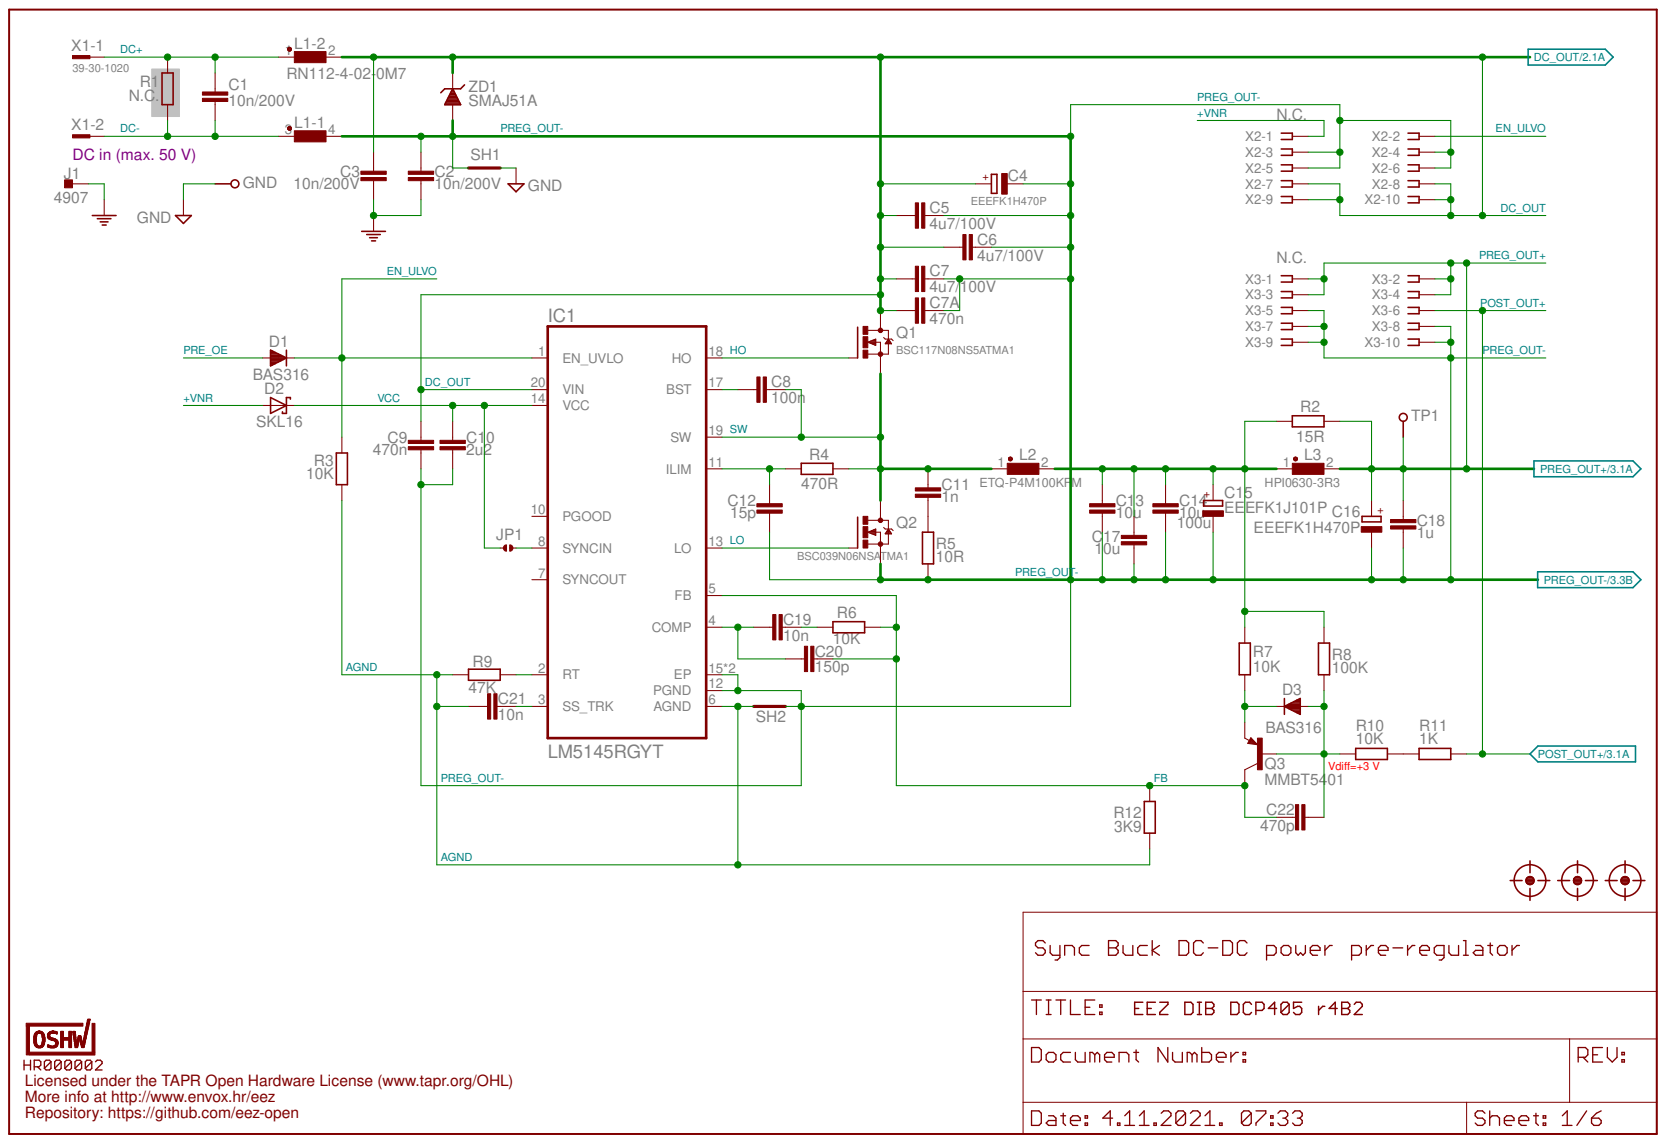
[picture p562: page 1]

Licensed under the TAPR Open Hardware License (www.tapr.org/OHL)
Repository: https://github.com/eez-open More info at http://www.envox.hr/eez

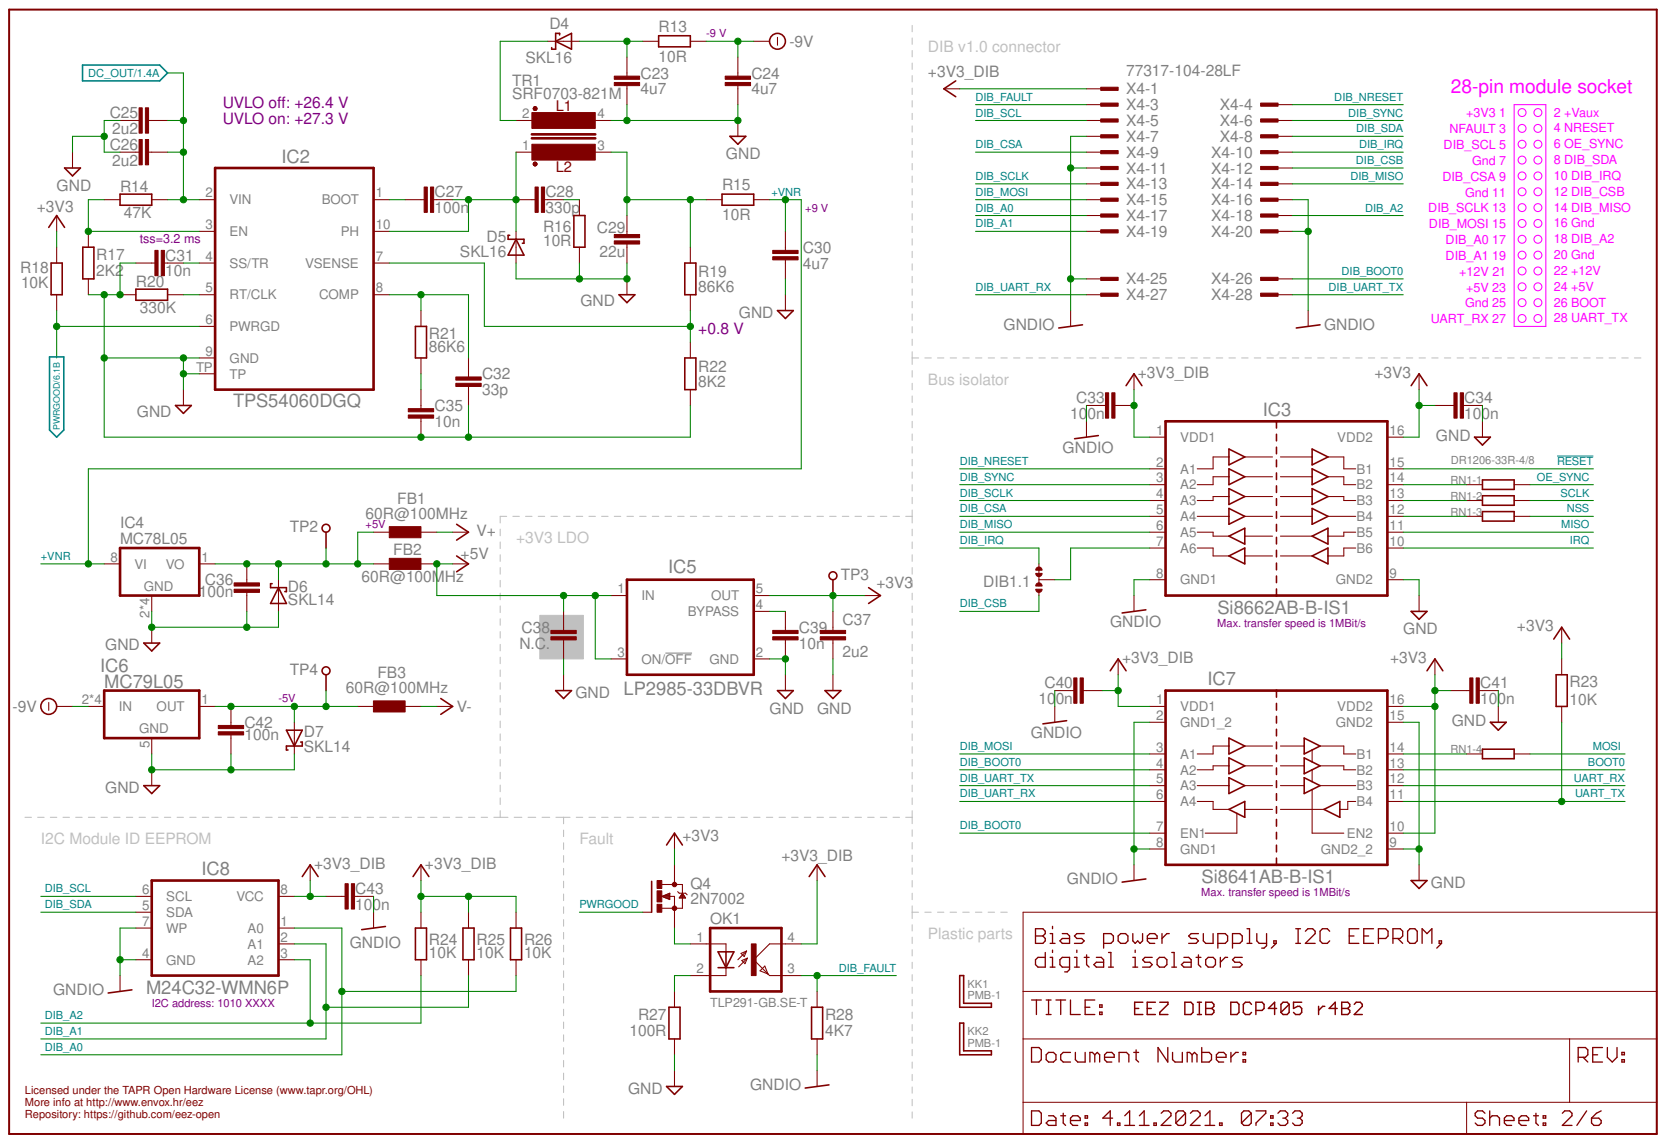
[picture p563: page 2]

TP

Max. transfer speed is 1MBit/s

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

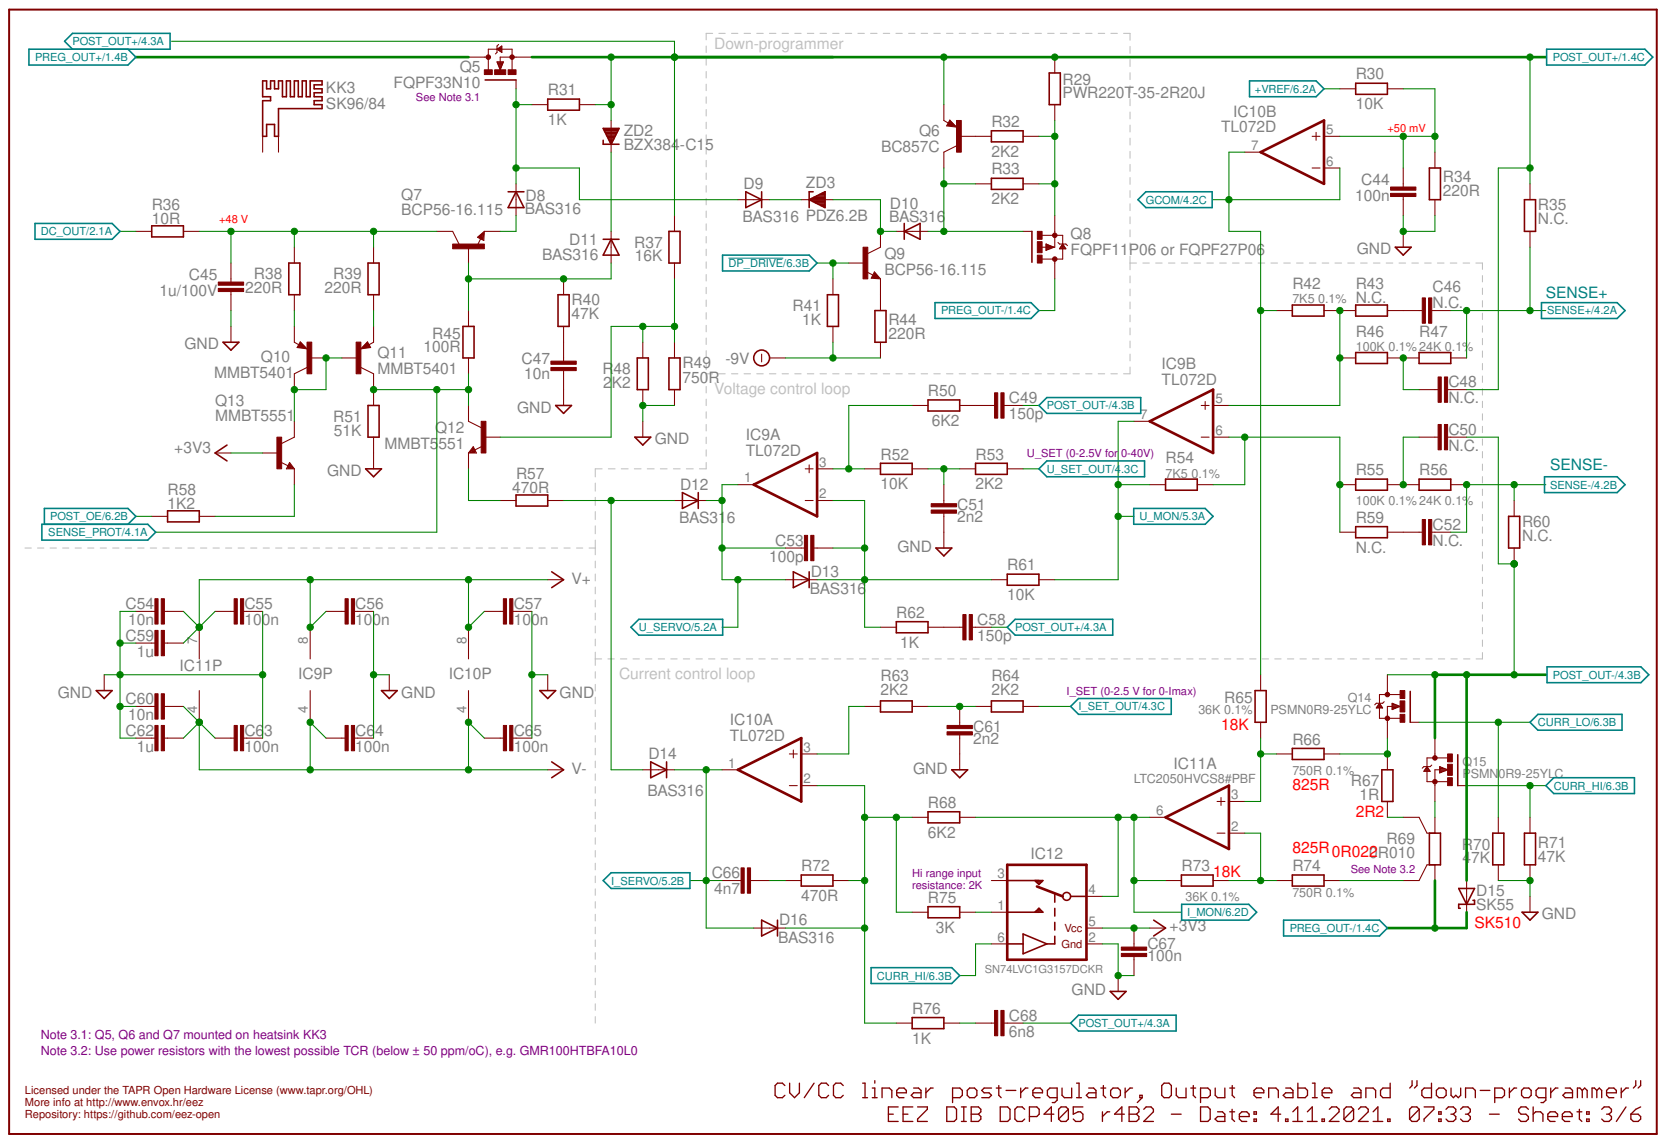
[picture p564: page 3]

Note 3.1: Q5, Q6 and Q7 mounted on heatsink KK3 Note 3.2: Use power resistors with the lowest possible TCR (below ± 50 ppm/oC), e.g. GMR100HTBFA10L0

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

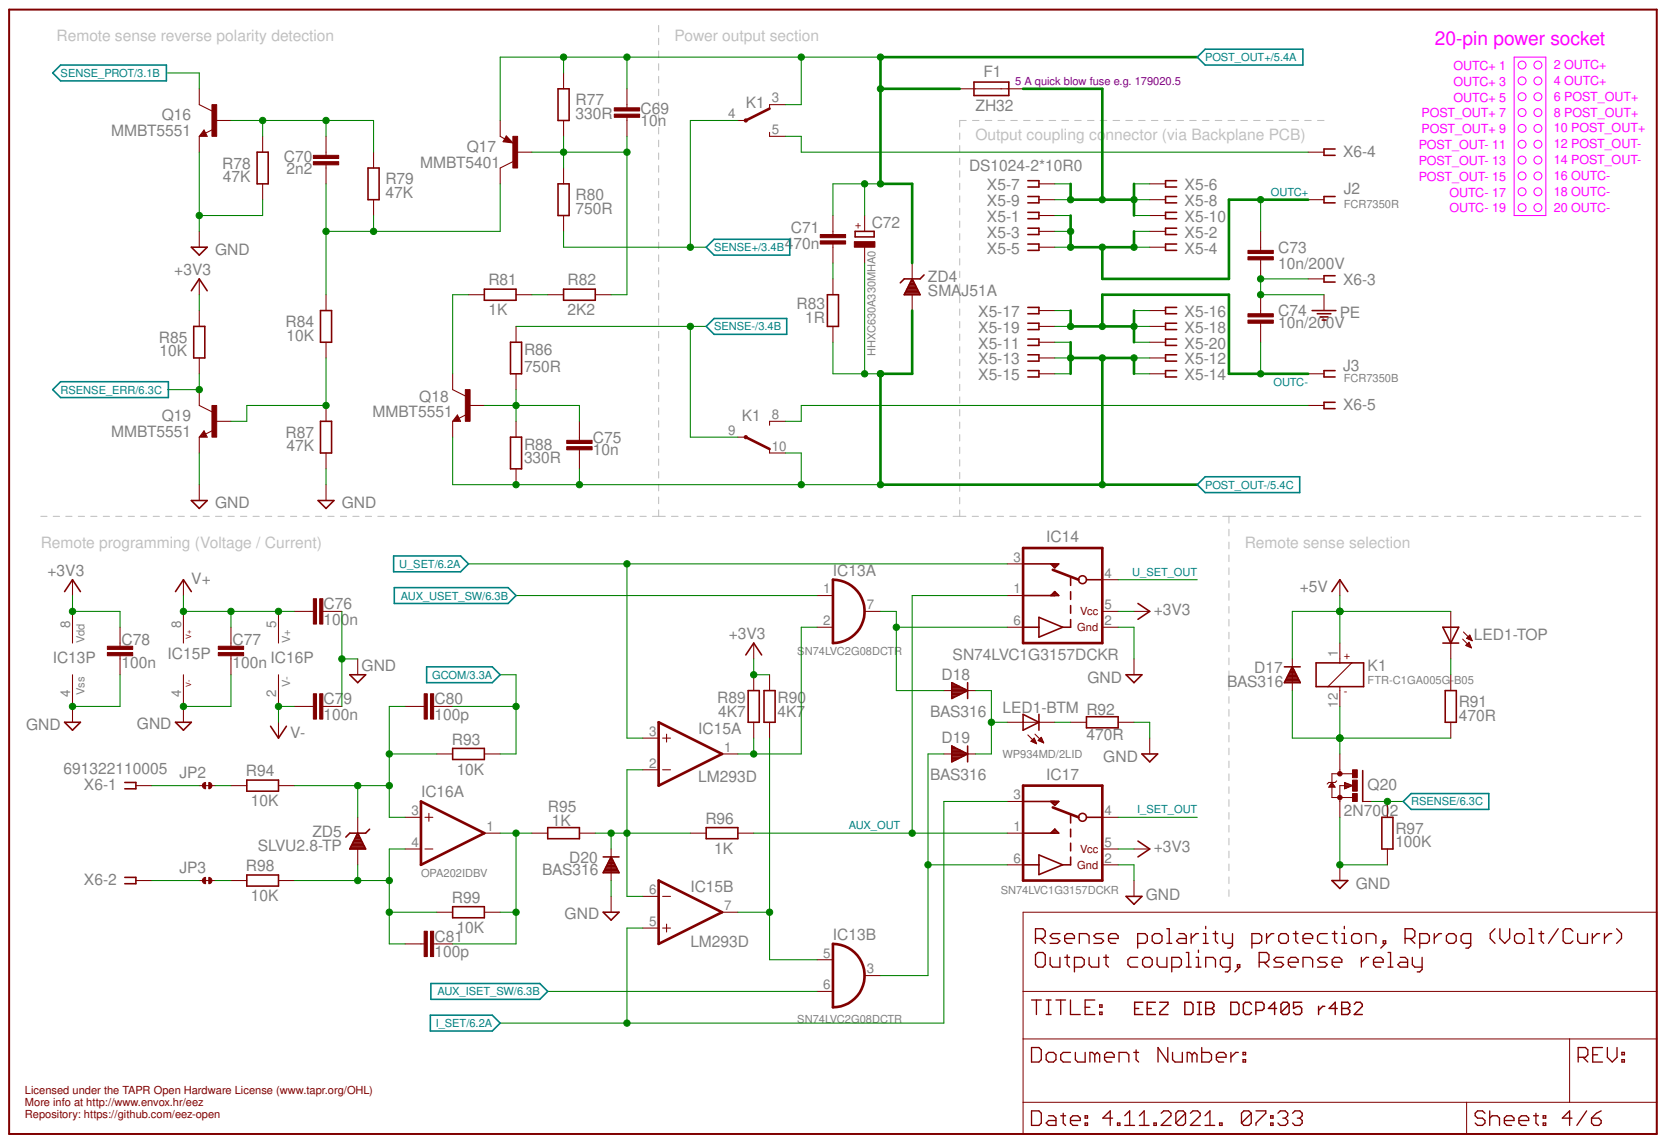
[picture p565: page 4]

Remote sense reverse polarity detection

5 A quick blow fuse e.g. 179020.5
Output coupling connector (via Backplane PCB)

Remote programming (Voltage / Current)

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

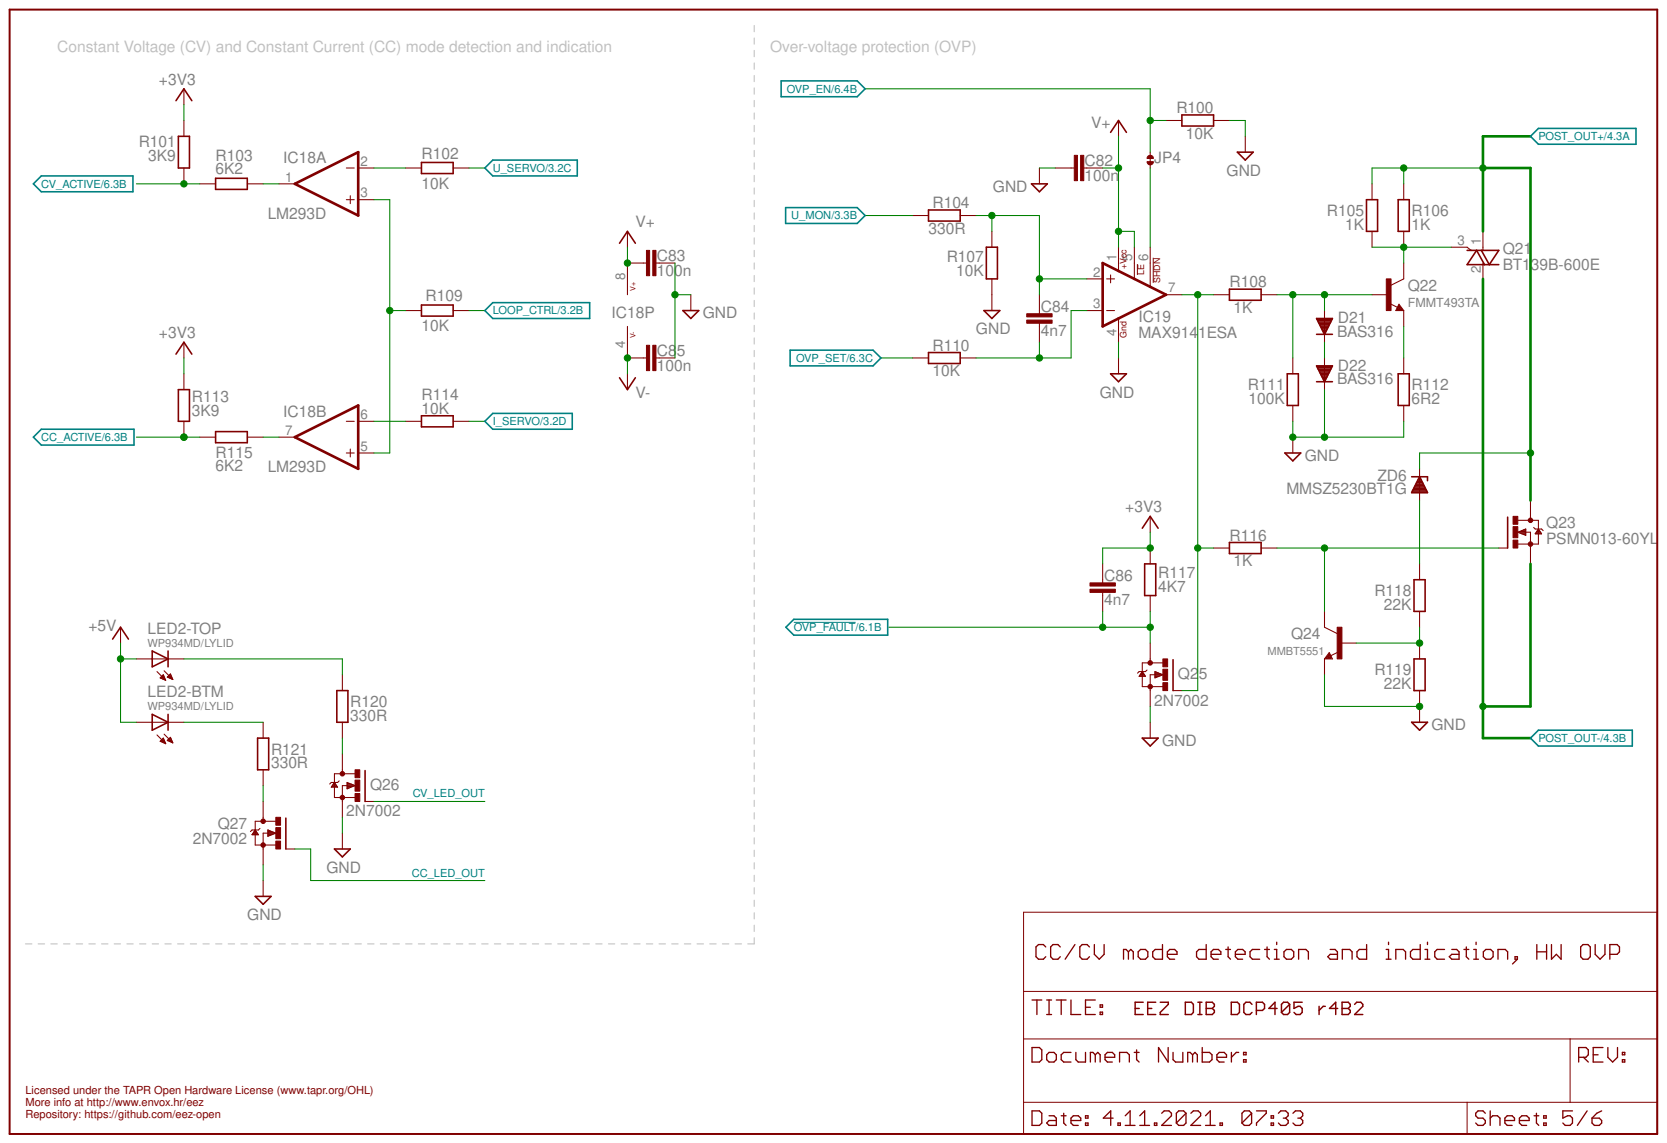
[picture p566: page 5]
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

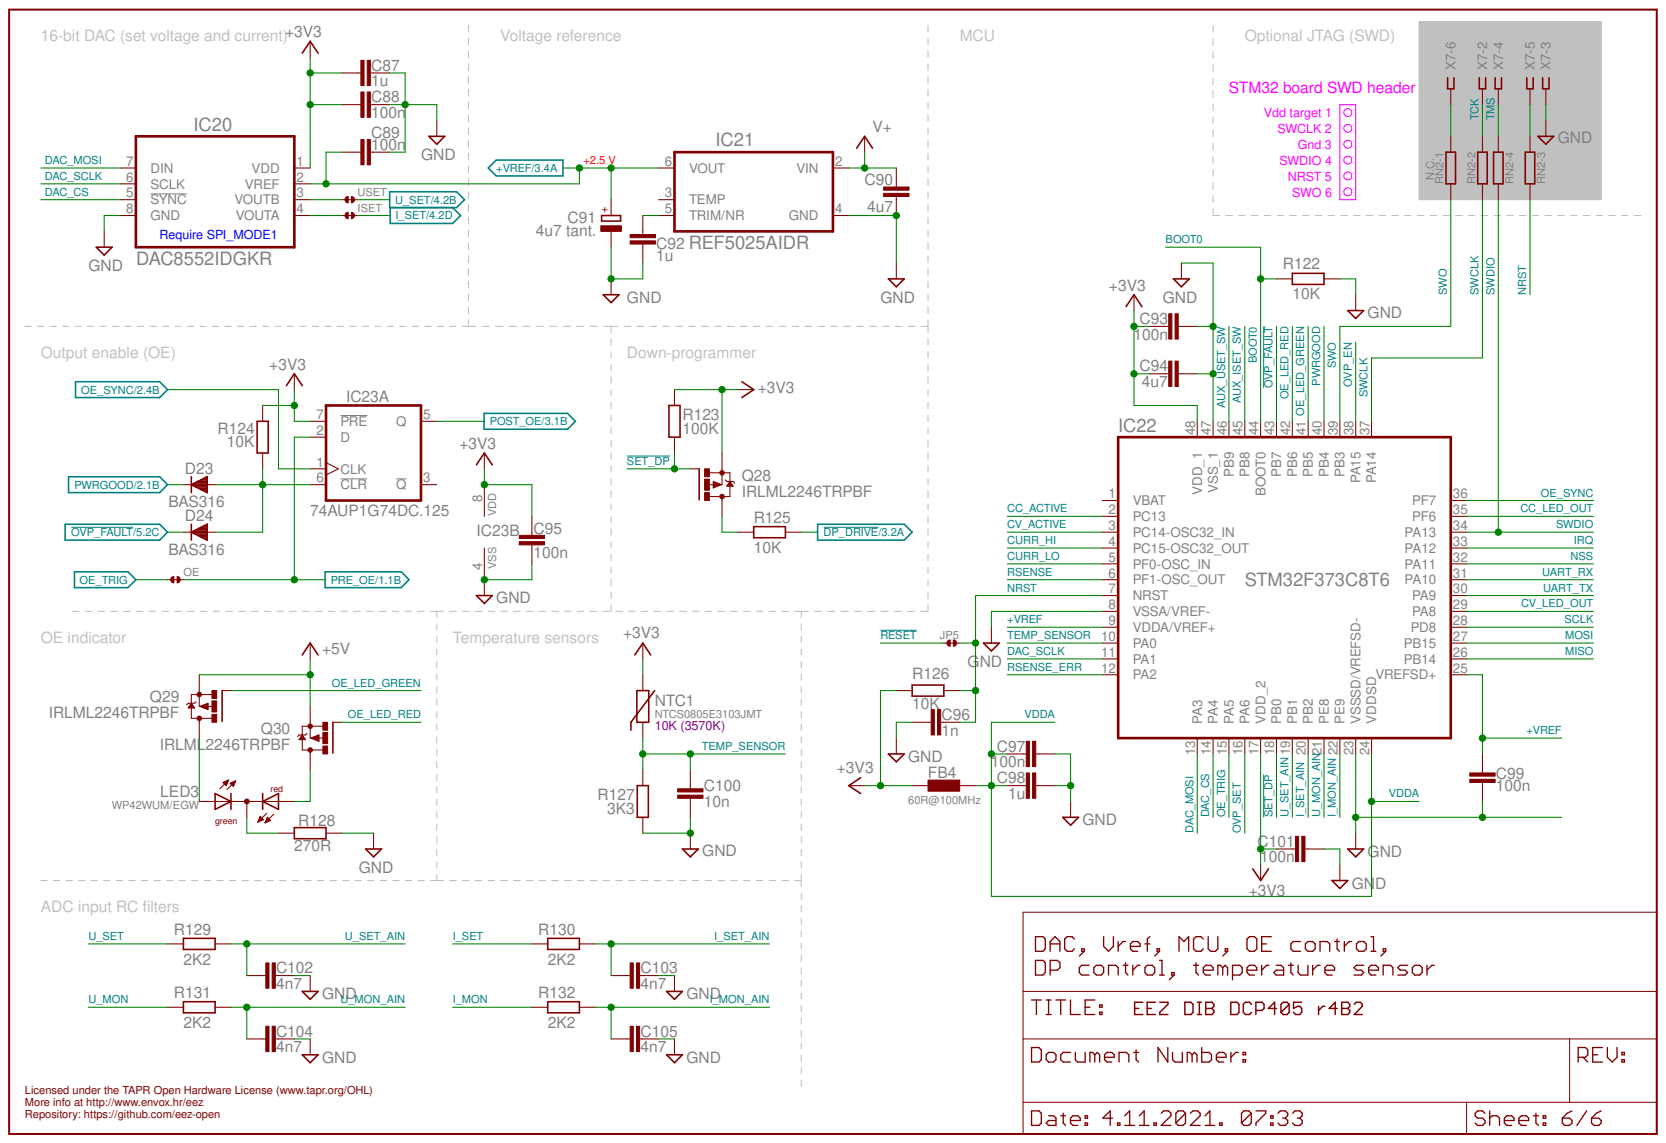
[picture p567: page 6]

ADC input RC filters

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
