eez-open/modular-psu/bp3c/EDA files/KiCad/EEZ DIB B3C.pdf

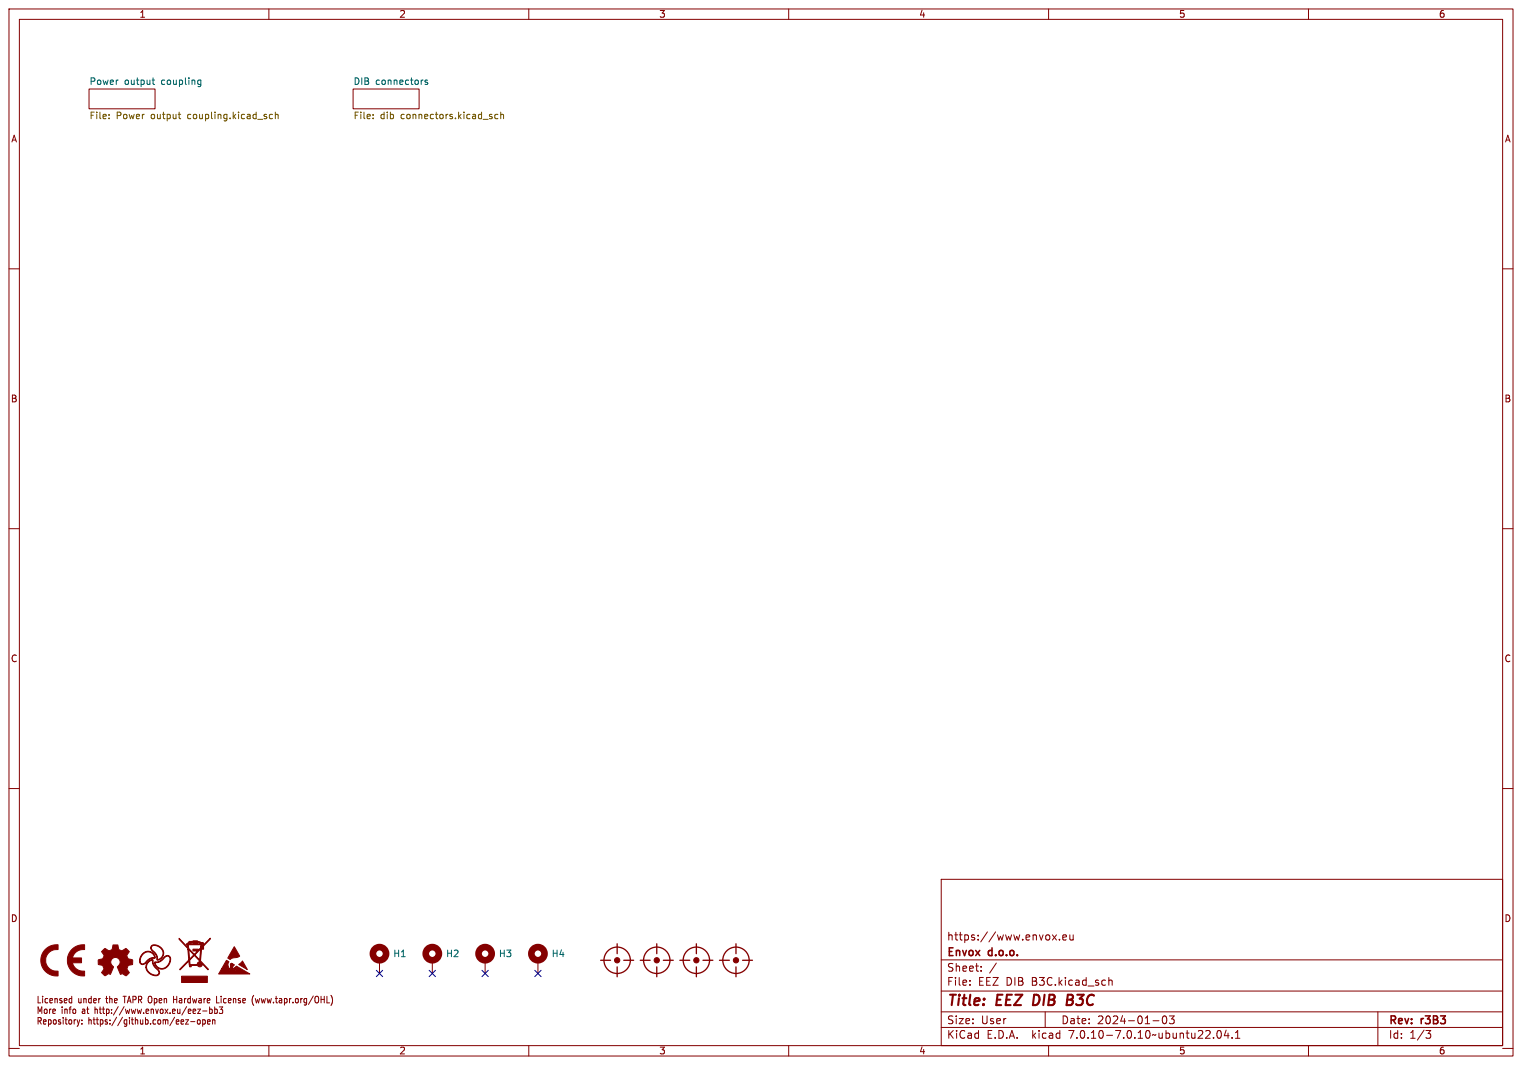
[picture p568: page 1]

DIB connectors File: dib connectors.kicad_sch Power output coupling File: Power output coupling.kicad_sch

Licensed under the TAPR Open Hardware License (www.tapr.org/OHL) More info at http://www.envox.eu/eez-bb3

Id: 1/3 Title: EEZ DIB B3C

Repository: https://github.com/eez-open

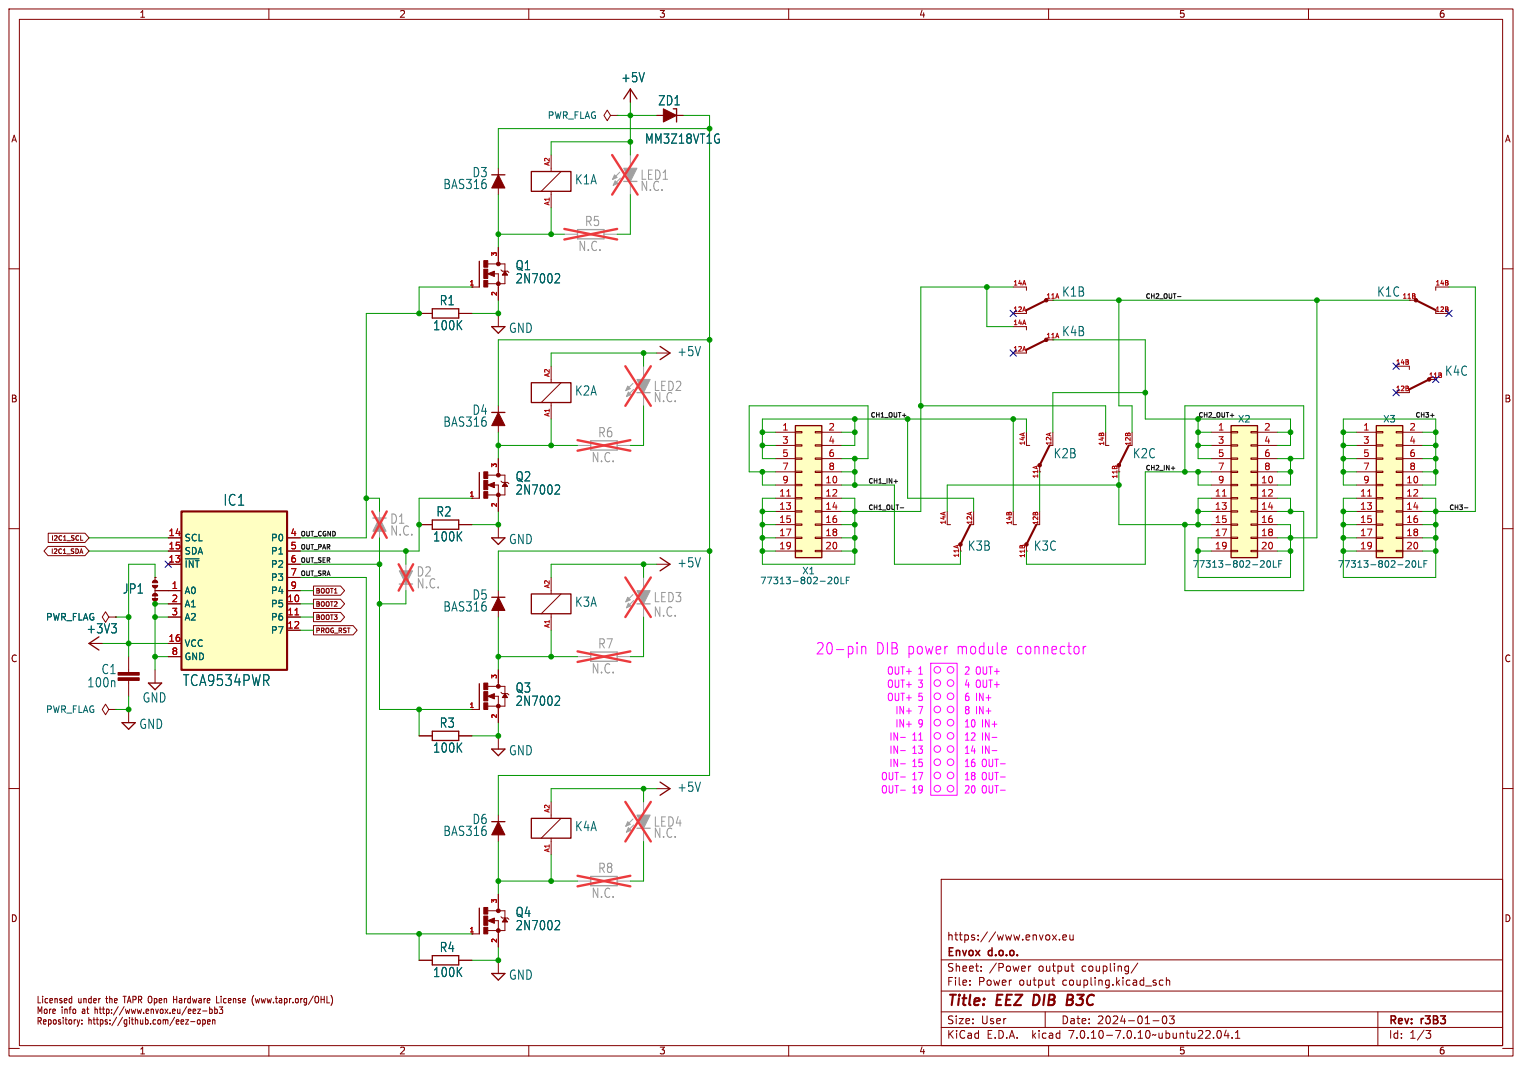
[picture p569: page 2]
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

Id: 1/3 Title: EEZ DIB B3C

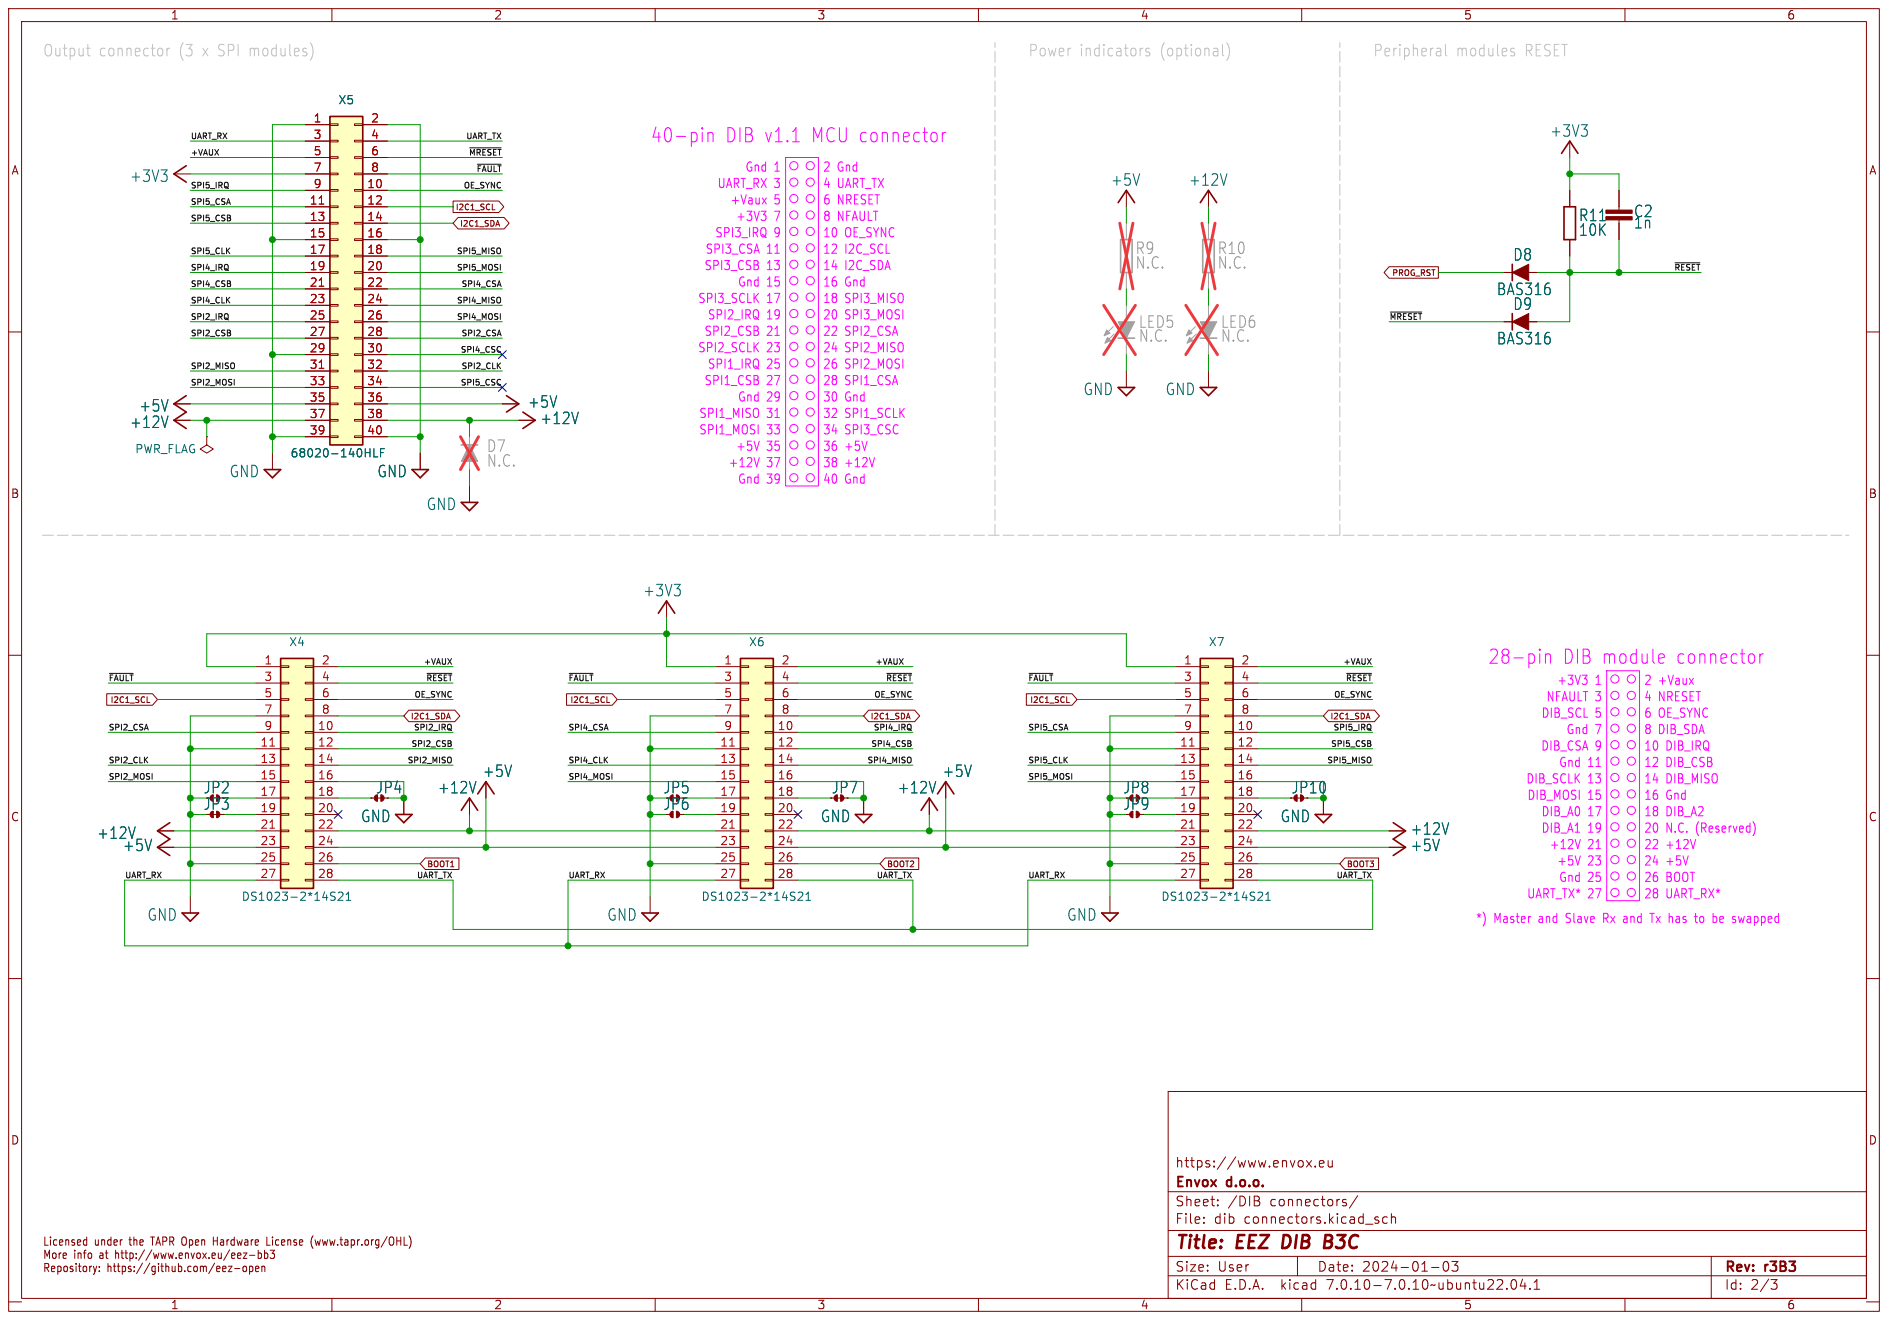
[picture p570: page 3]

*) Master and Slave Rx and Tx has to be swapped

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

Id: 2/3 Title: EEZ DIB B3C
