eez-open/modular-psu/aux-ps/EDA files/KiCad/EEZ DIB AUX-PS.pdf

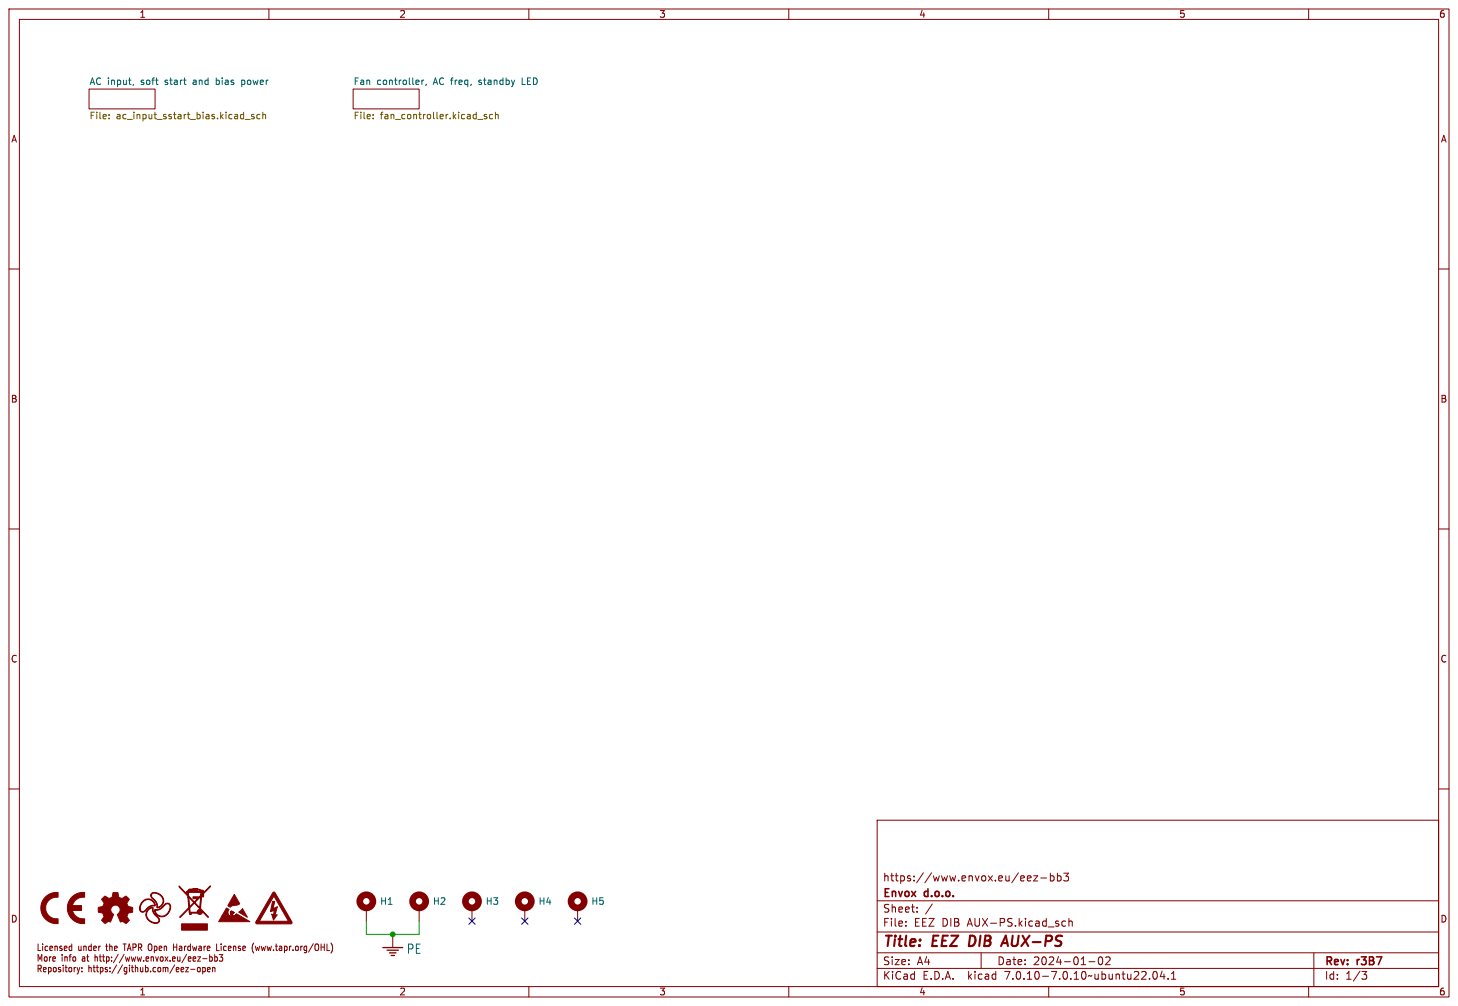
[picture p571: page 1]

File: fan_controller.kicad_sch AC input, soft start and bias power File: ac_input_sstart_bias.kicad_sch

Id: 1/3 Title: EEZ DIB AUX-PS

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

Repository: https://github.com/eez-open

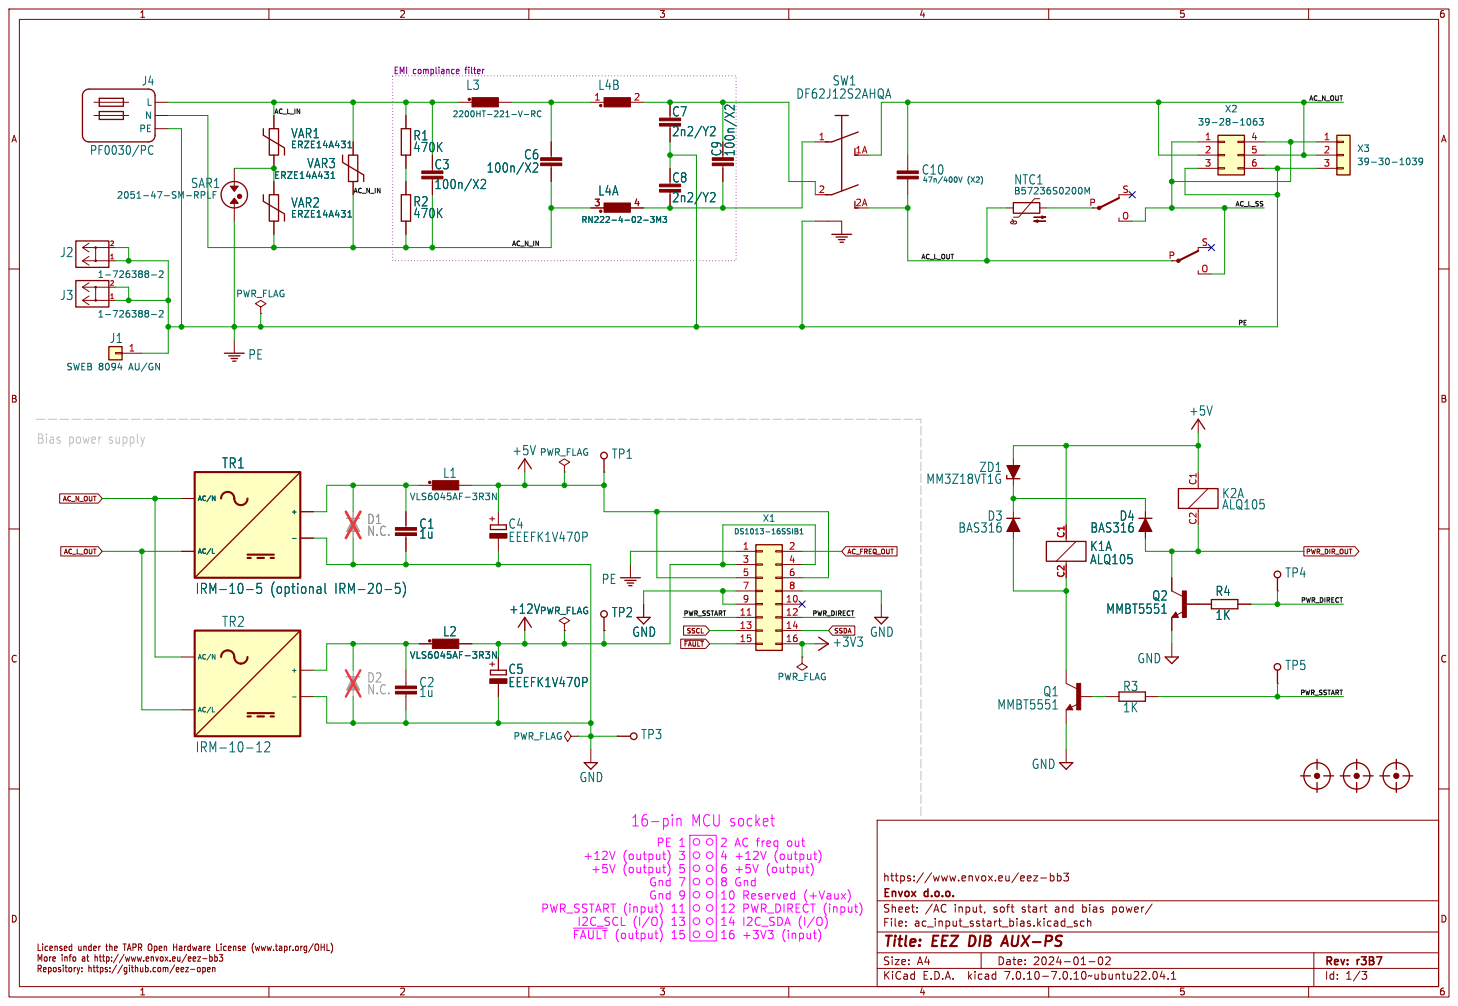
[picture p572: page 2]

PWR_DIRECT PWR_SSTART Licensed under the TAPR Open Hardware License (www.tapr.org/OHL) More info at http://www.envox.eu/eez-bb3

2 AC freq out 4 +12V (output) 6 +5V (output) 8 Gnd

Id: 1/3 Title: EEZ DIB AUX-PS

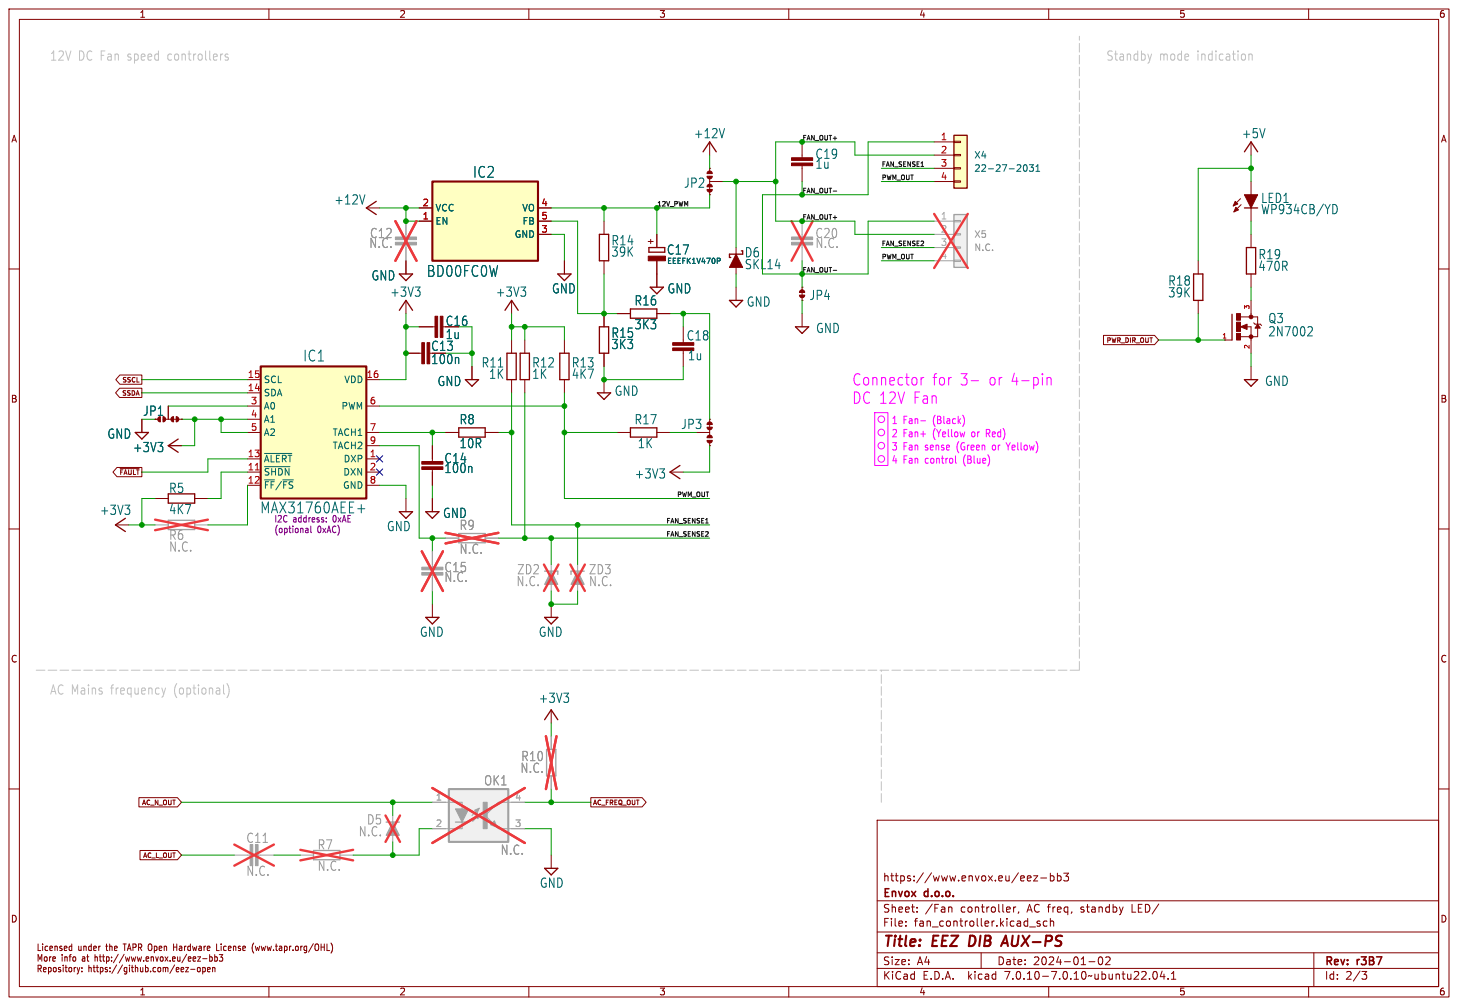
[picture p573: page 3]

1 Fan- (Black) 2 Fan+ (Yellow or Red) Licensed under the TAPR Open Hardware License (www.tapr.org/OHL) More info at http://www.envox.eu/eez-bb3

3 Fan sense (Green or Yellow) 4 Fan control (Blue)

AC Mains frequency (optional)

Id: 2/3 Title: EEZ DIB AUX-PS

Repository: https://github.com/eez-open
