eez-open/modular-psu/DIB/EEZ DIB v1.2 module dimensions.pdf

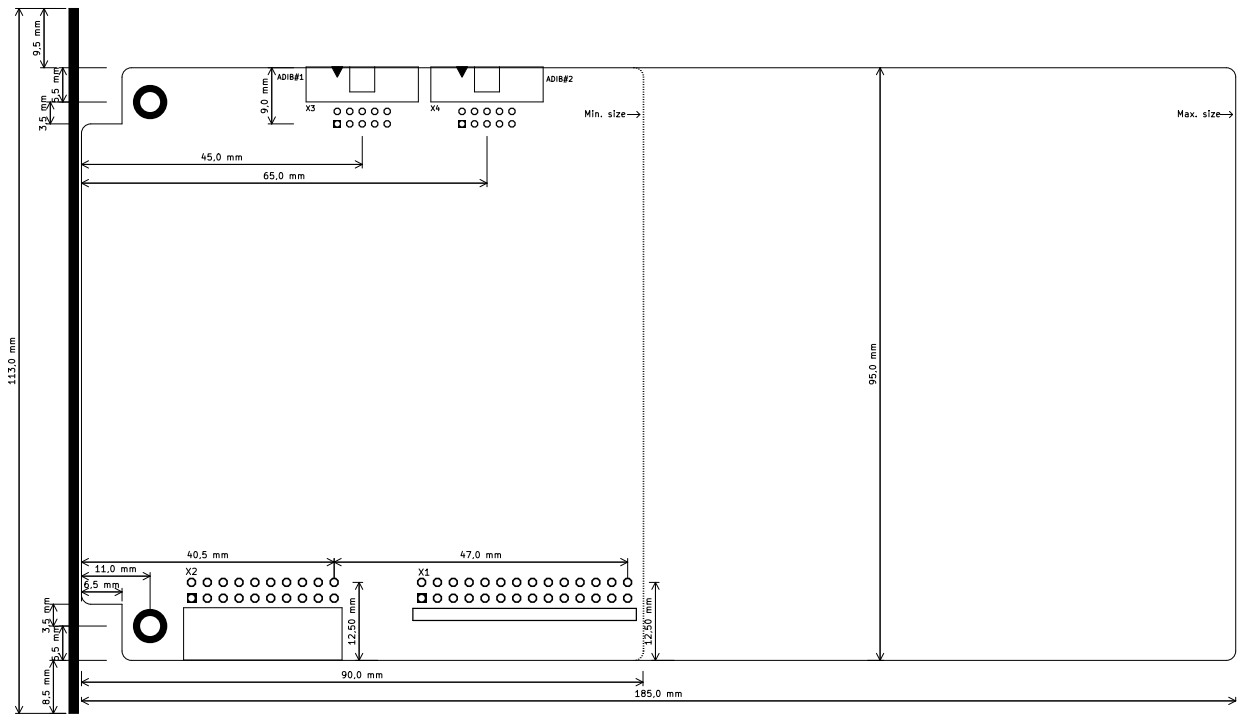
[picture p574: page 1]
