eez-open/modular-psu/dcp405/Images/EEZ DIB DCP405 PCB Bottom.pdf

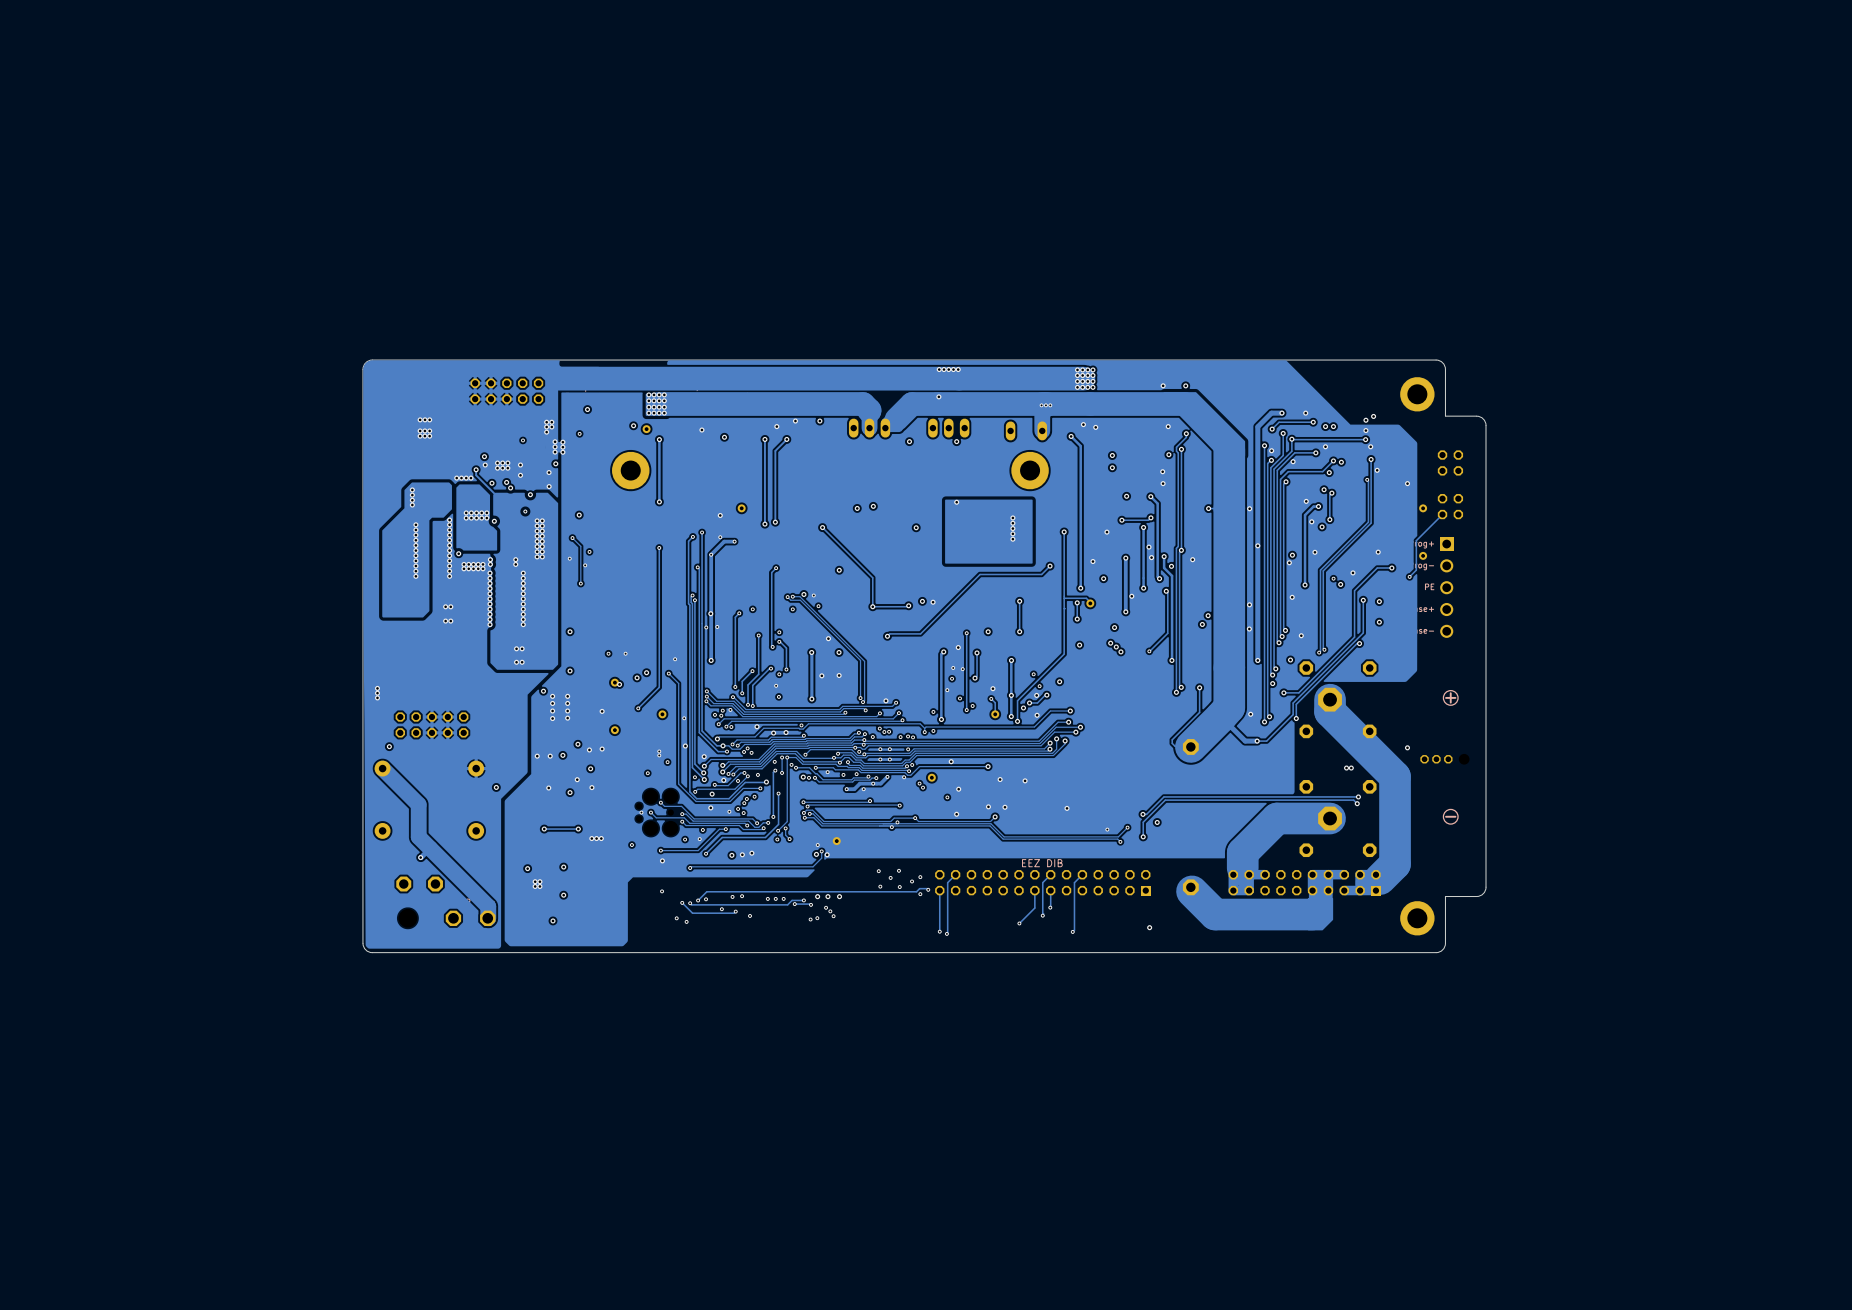
[picture p575: page 1]
