eez-open/modular-psu/dcp405/Images/EEZ DIB DCP405 PCB L2.pdf

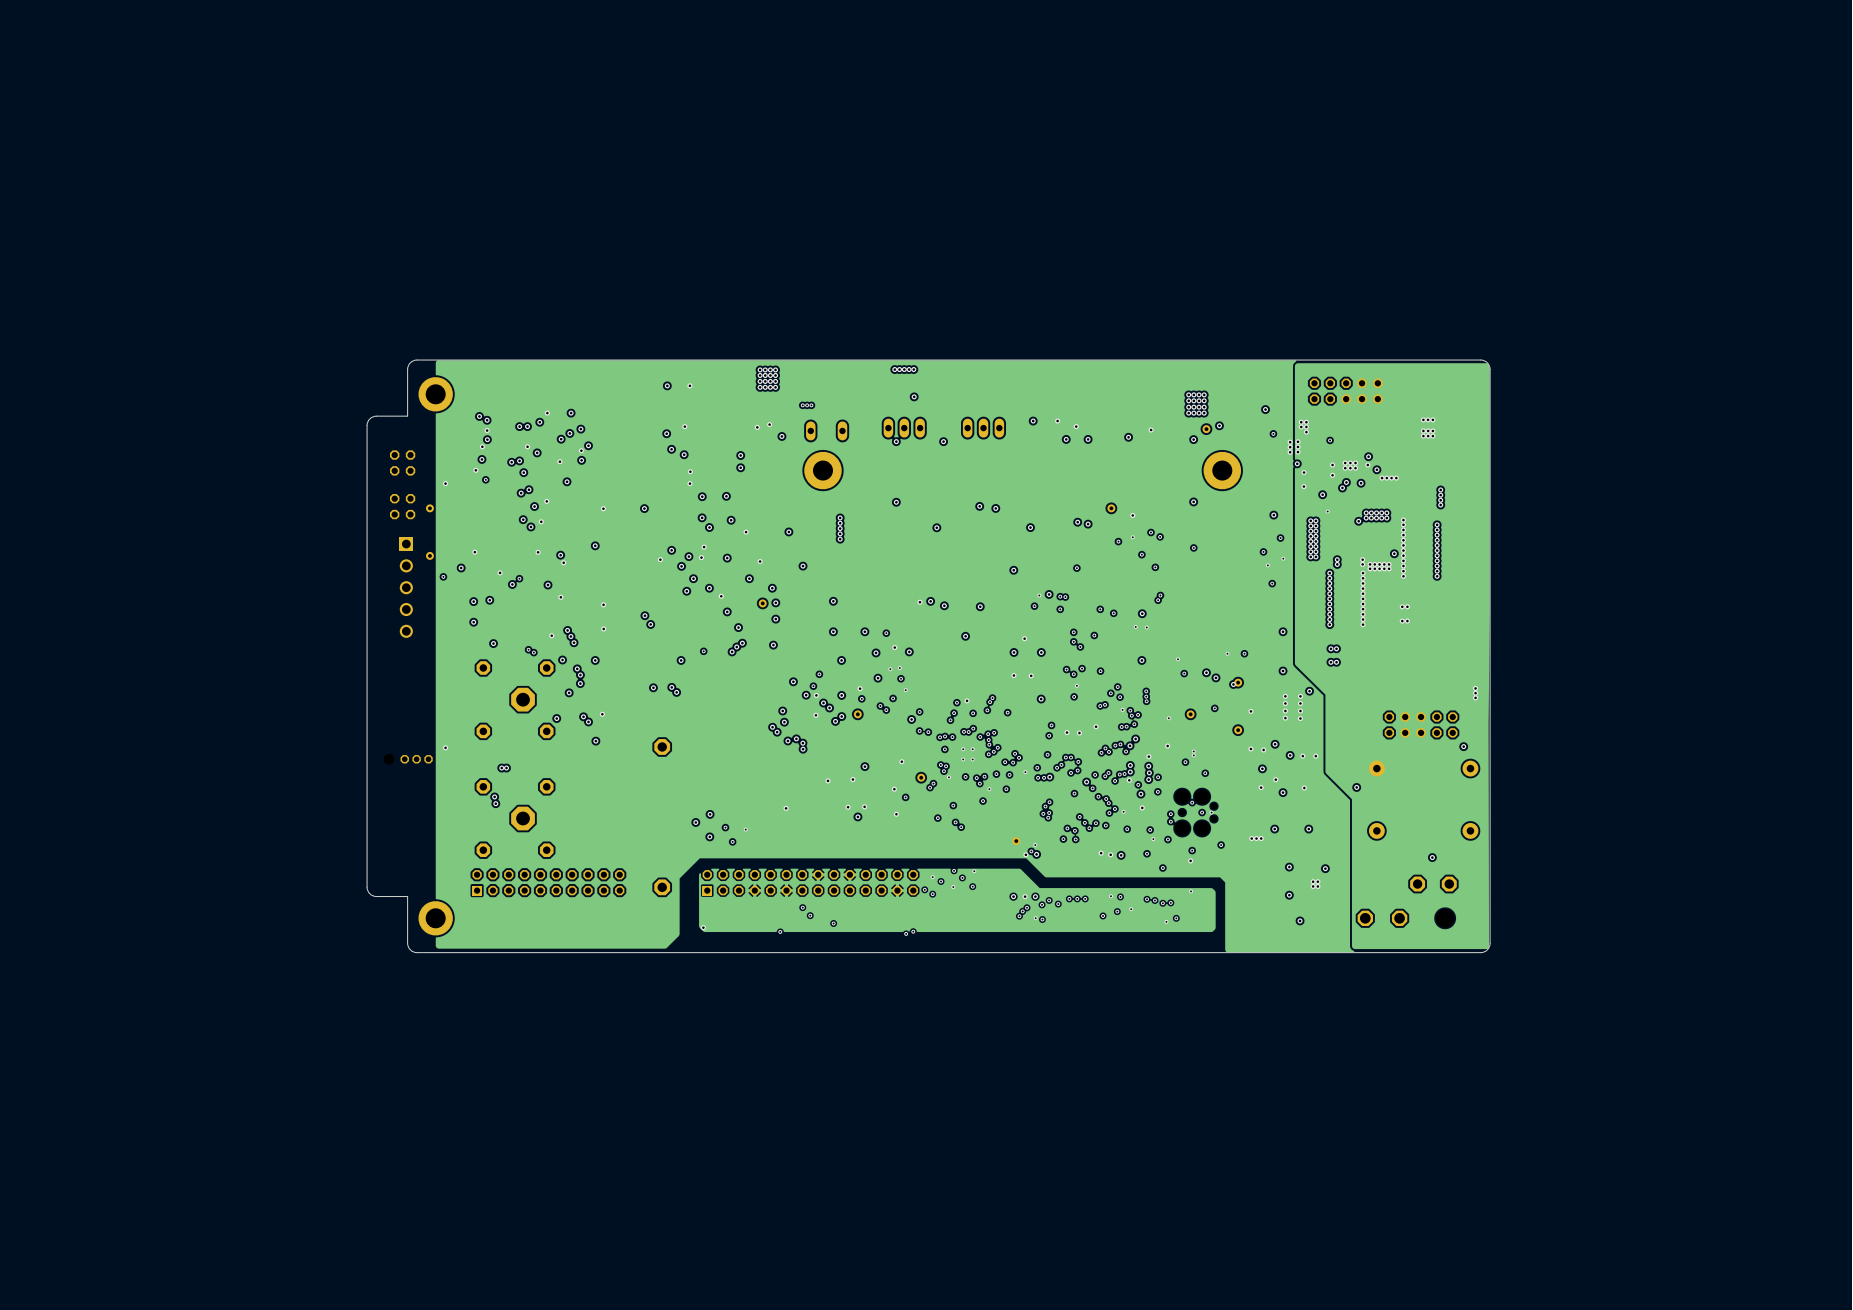
[picture p576: page 1]
