eez-open/modular-psu/dcp405/Images/EEZ DIB DCP405 PCB L3.pdf

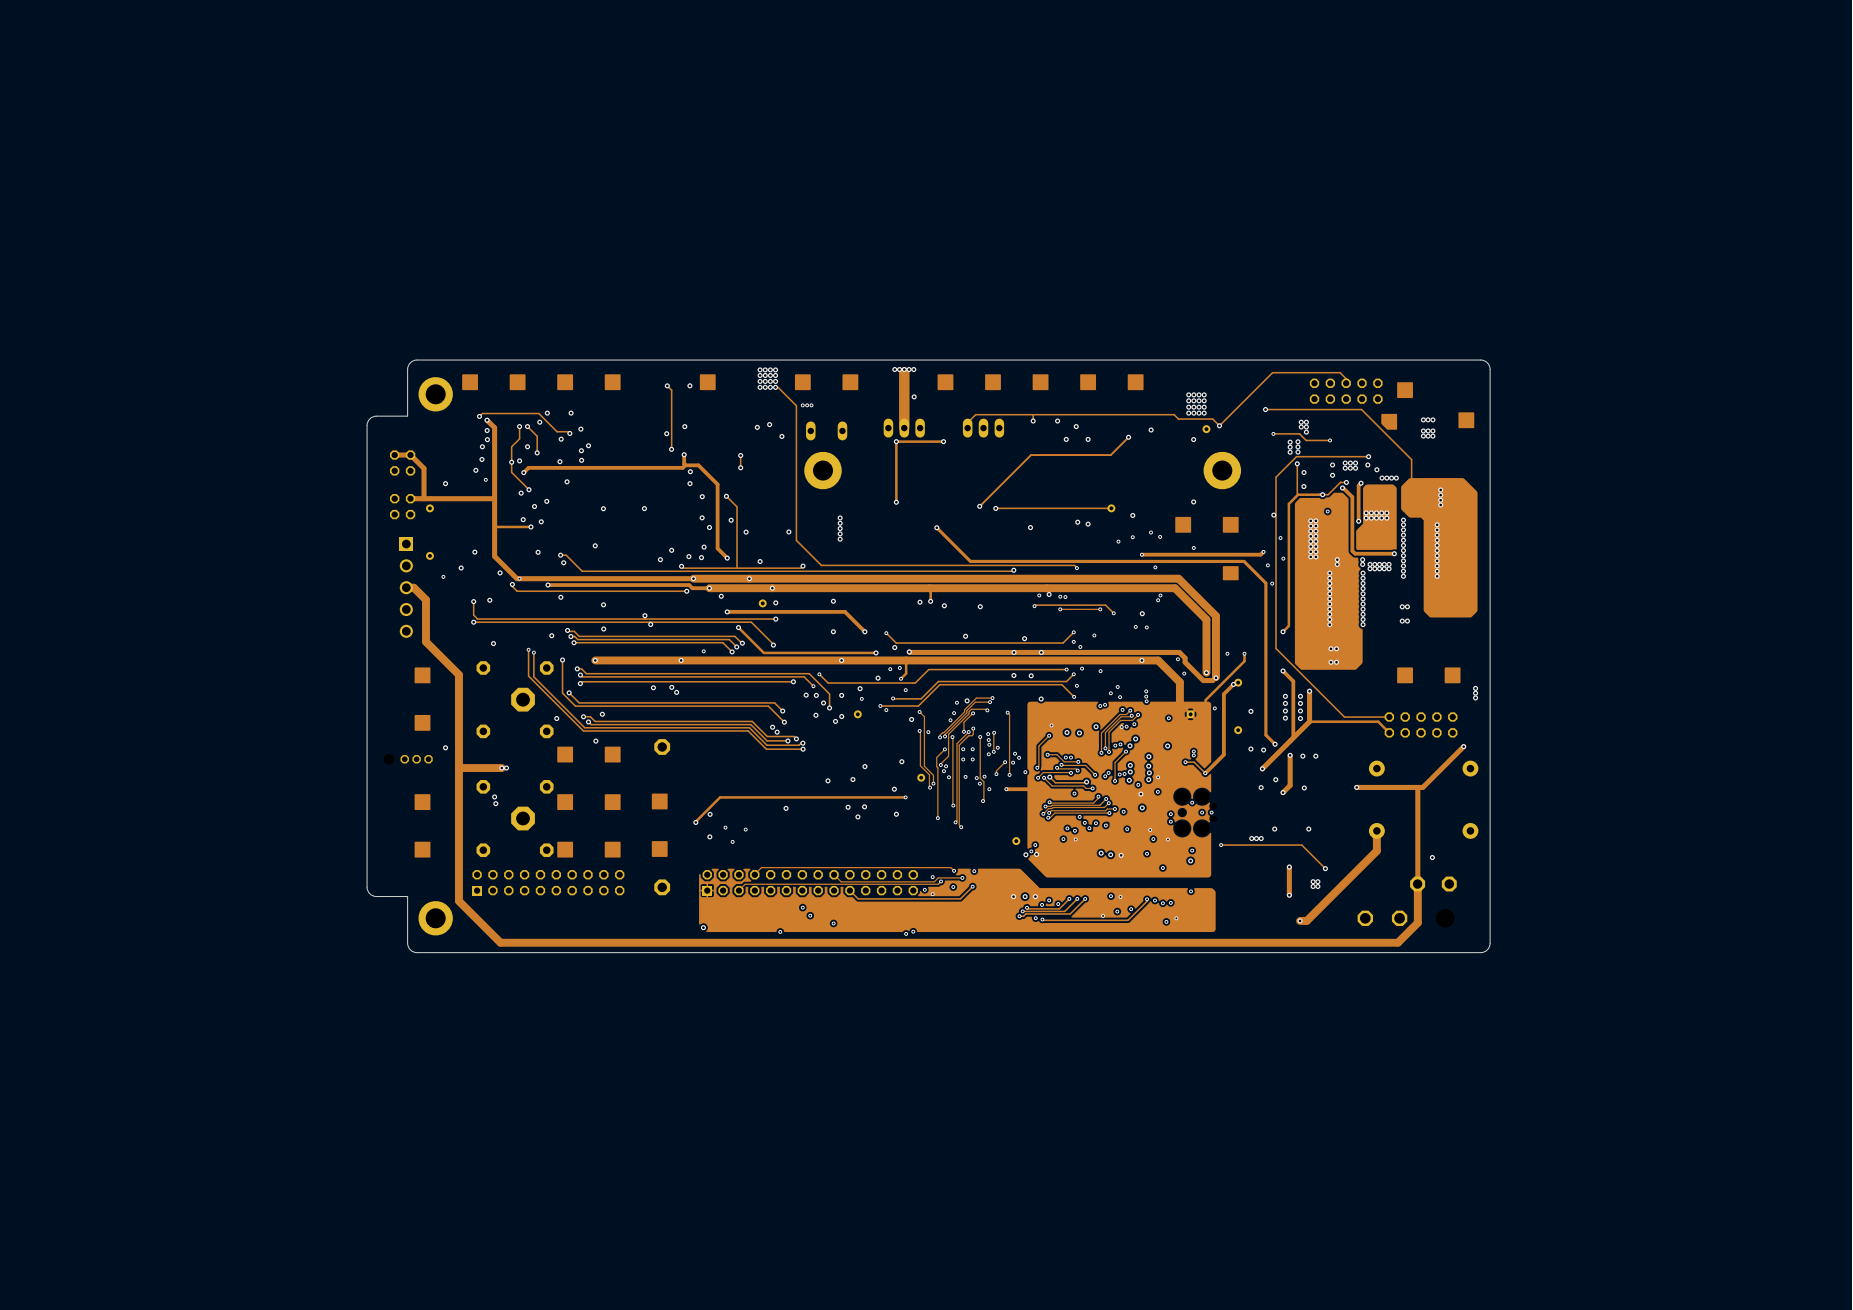
[picture p577: page 1]
