eez-open/modular-psu/dcp405/Images/EEZ DIB DCP405 PCB top.pdf

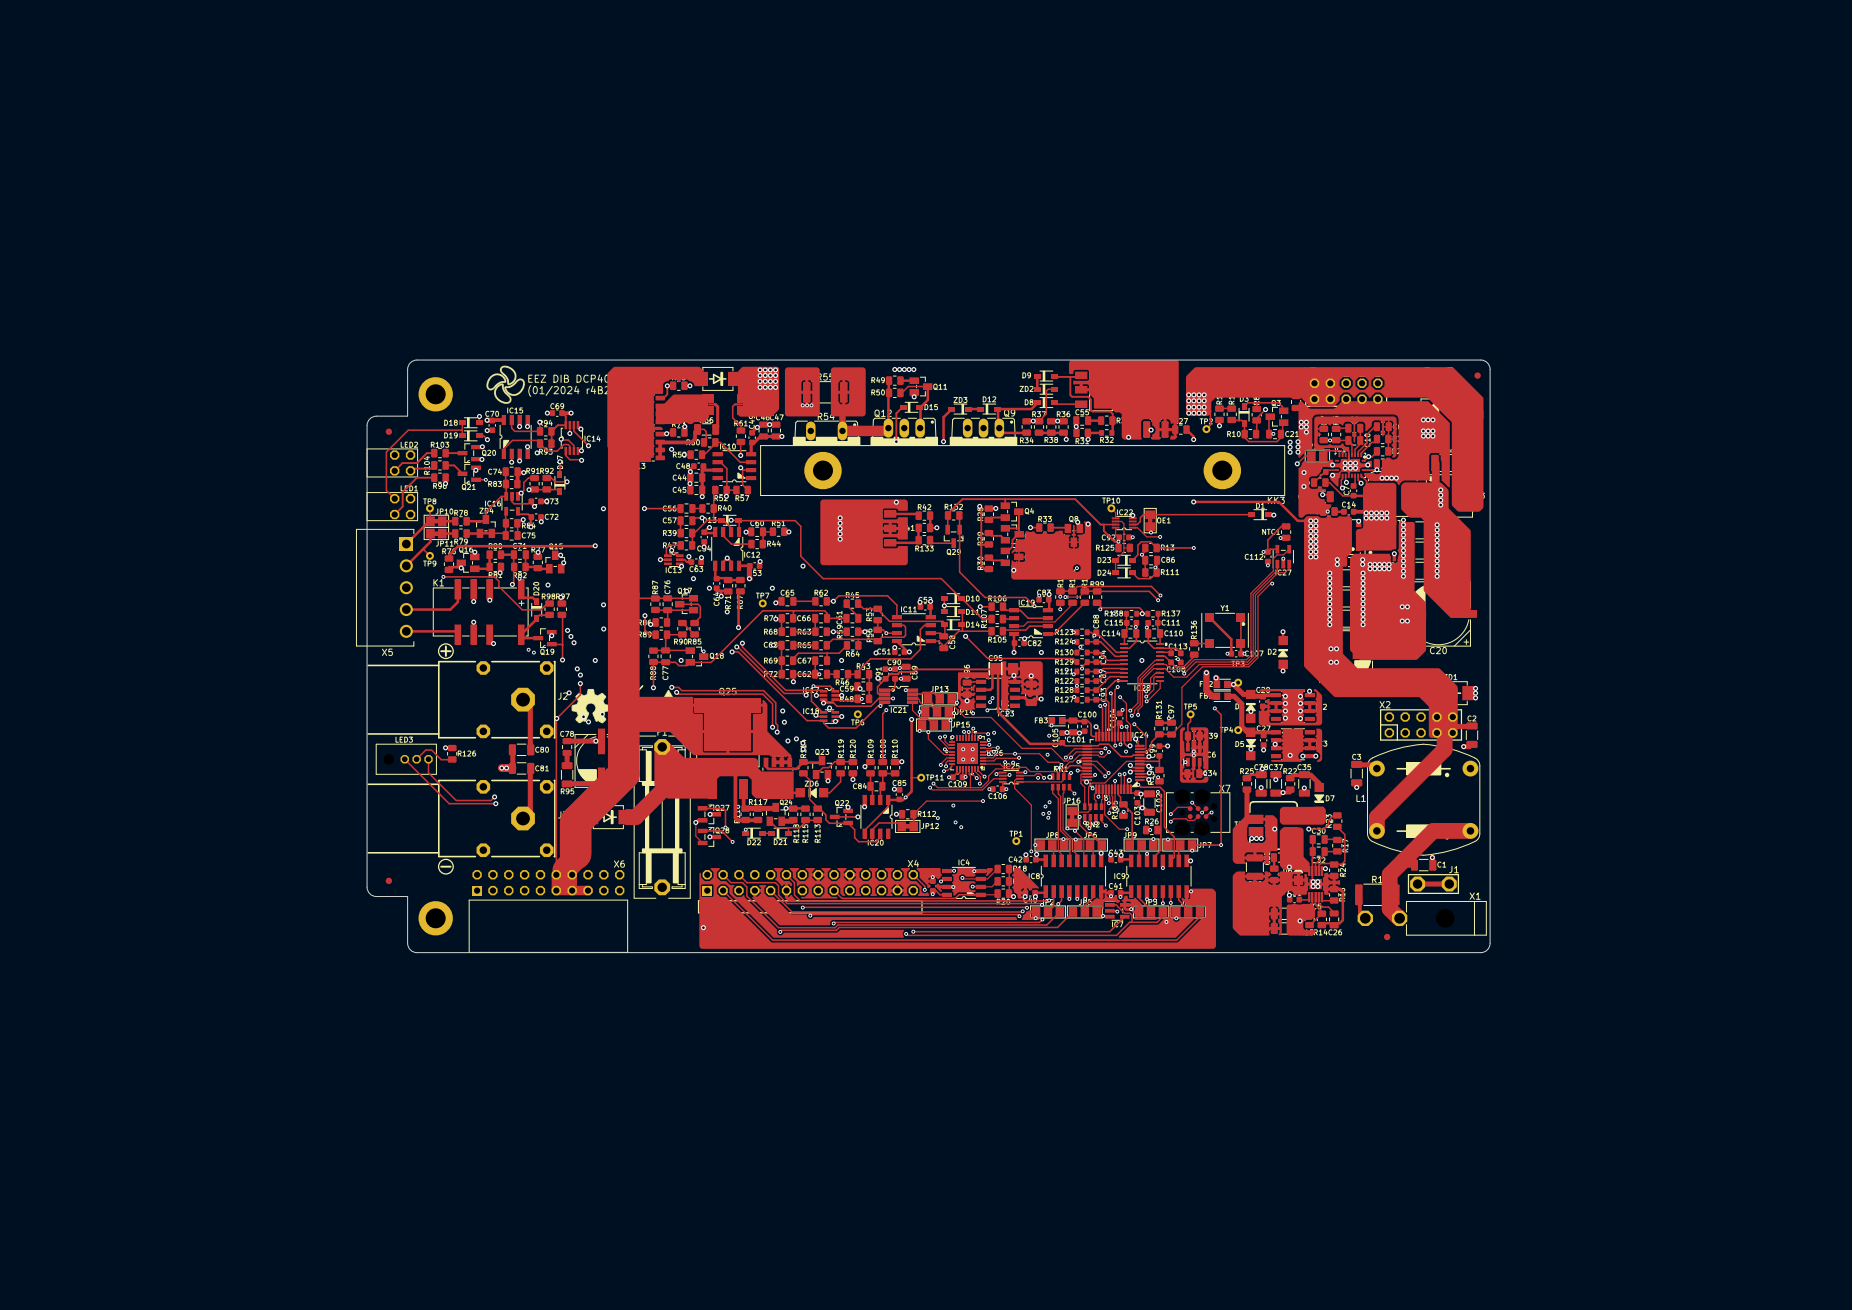
[picture p578: page 1]
