eez-open/modular-psu/bp3c/Images/BP3C r3B3 bottom layer.pdf

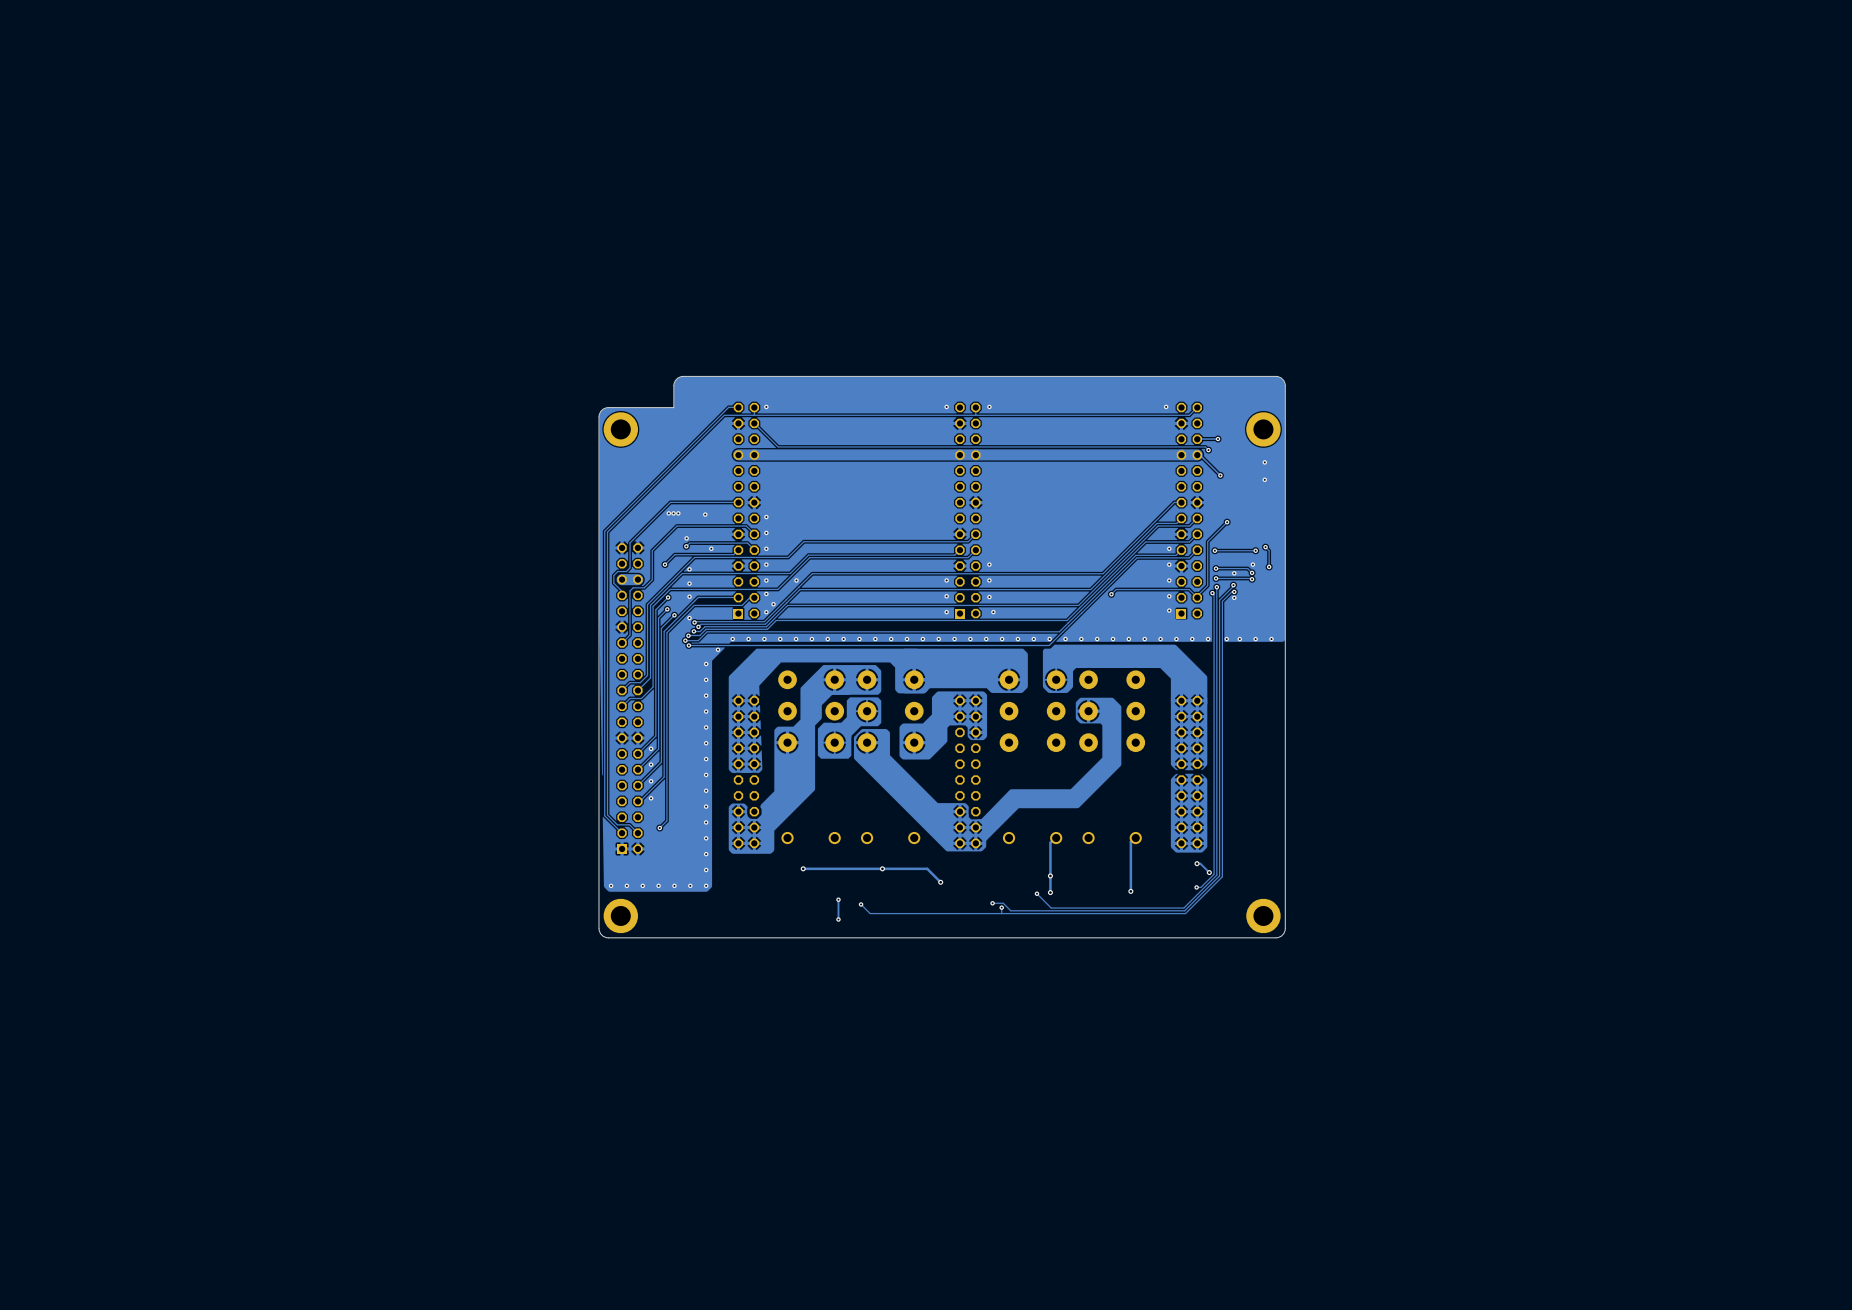
[picture p579: page 1]
