eez-open/modular-psu/bp3c/Images/BP3C r3B3 top layer.pdf

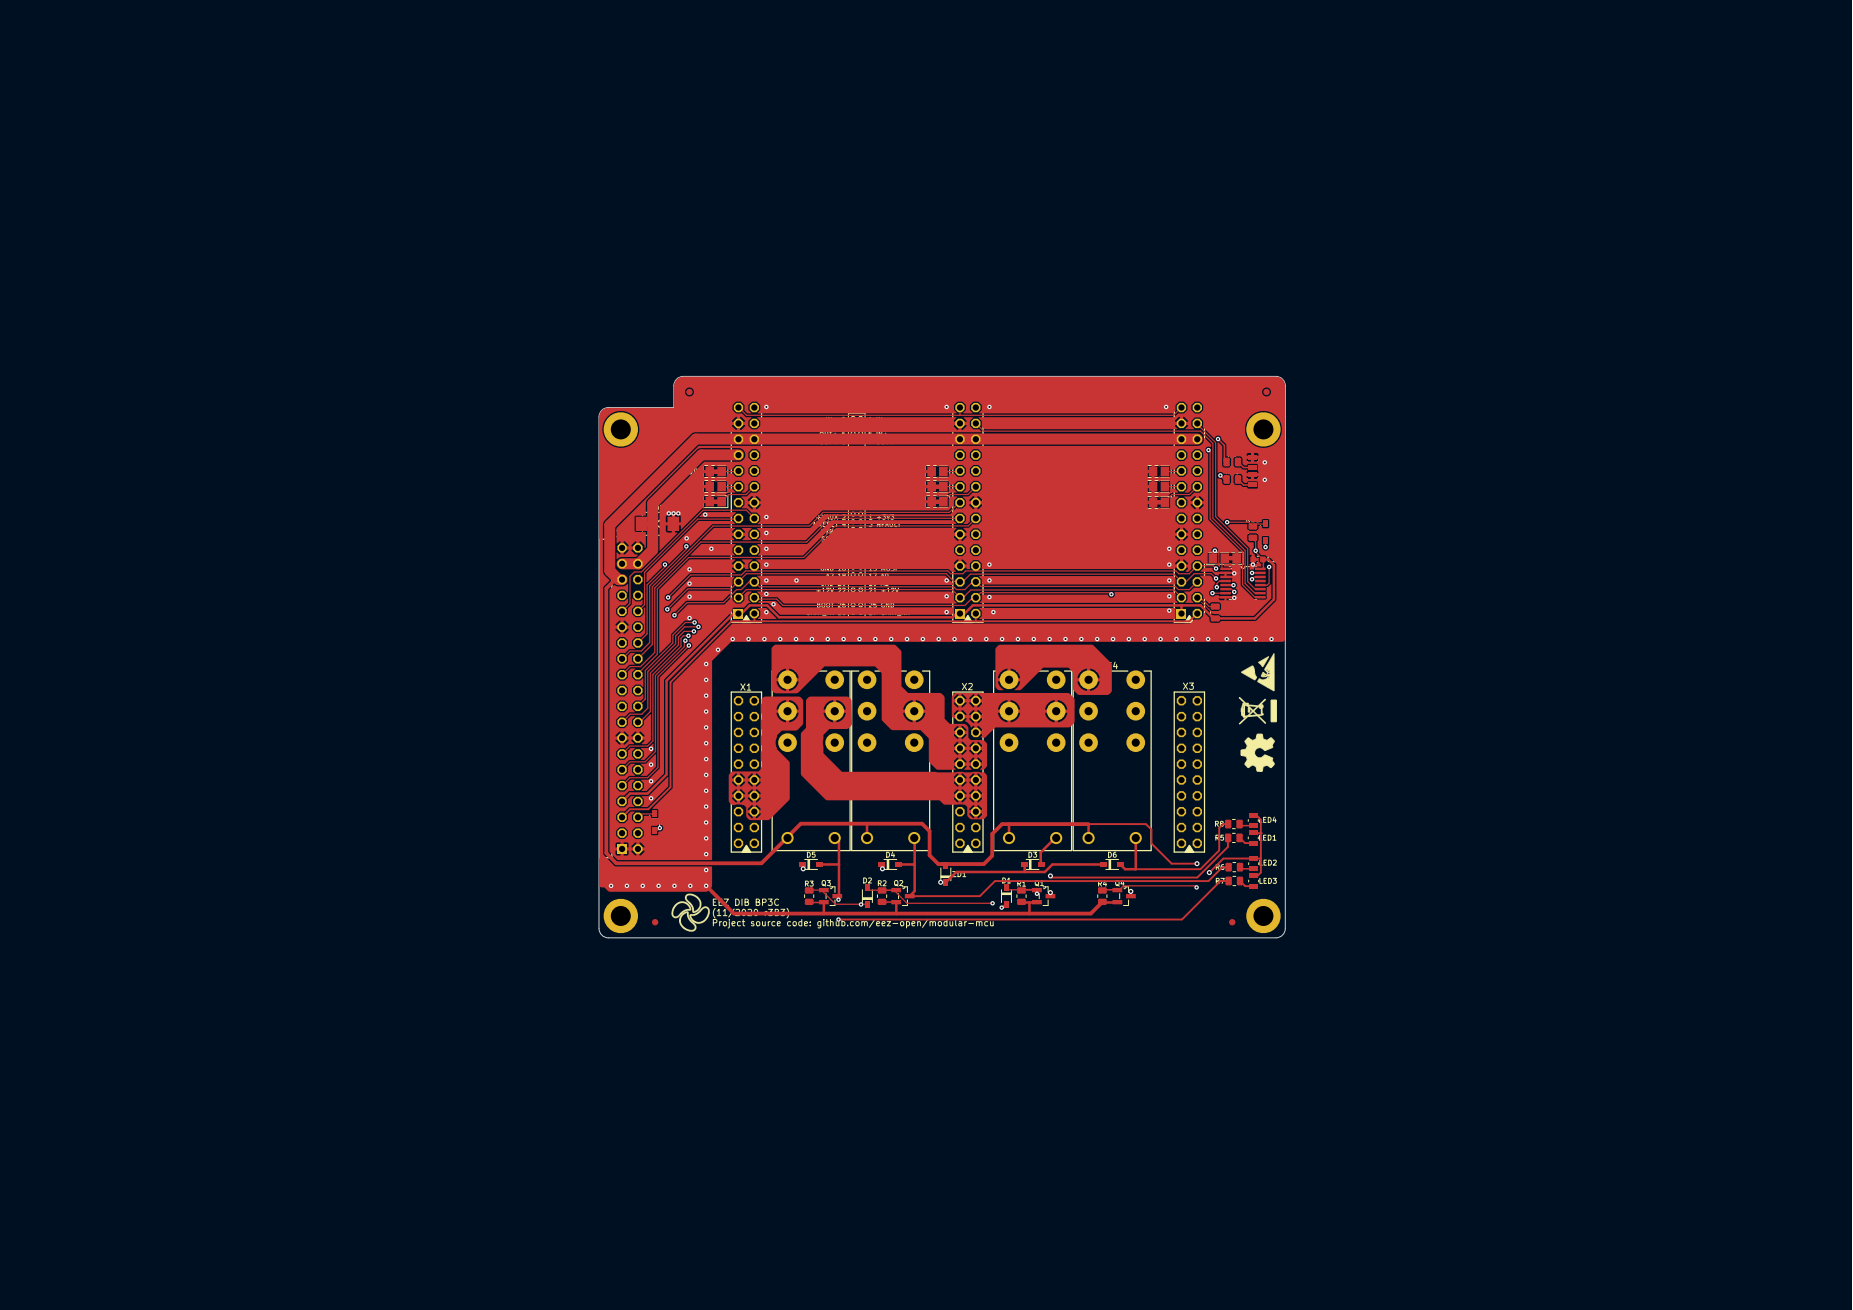
[picture p580: page 1]
