eez-open/modular-psu/aux-ps/Images/AUX PS r3B7 PCB bottom layer.pdf

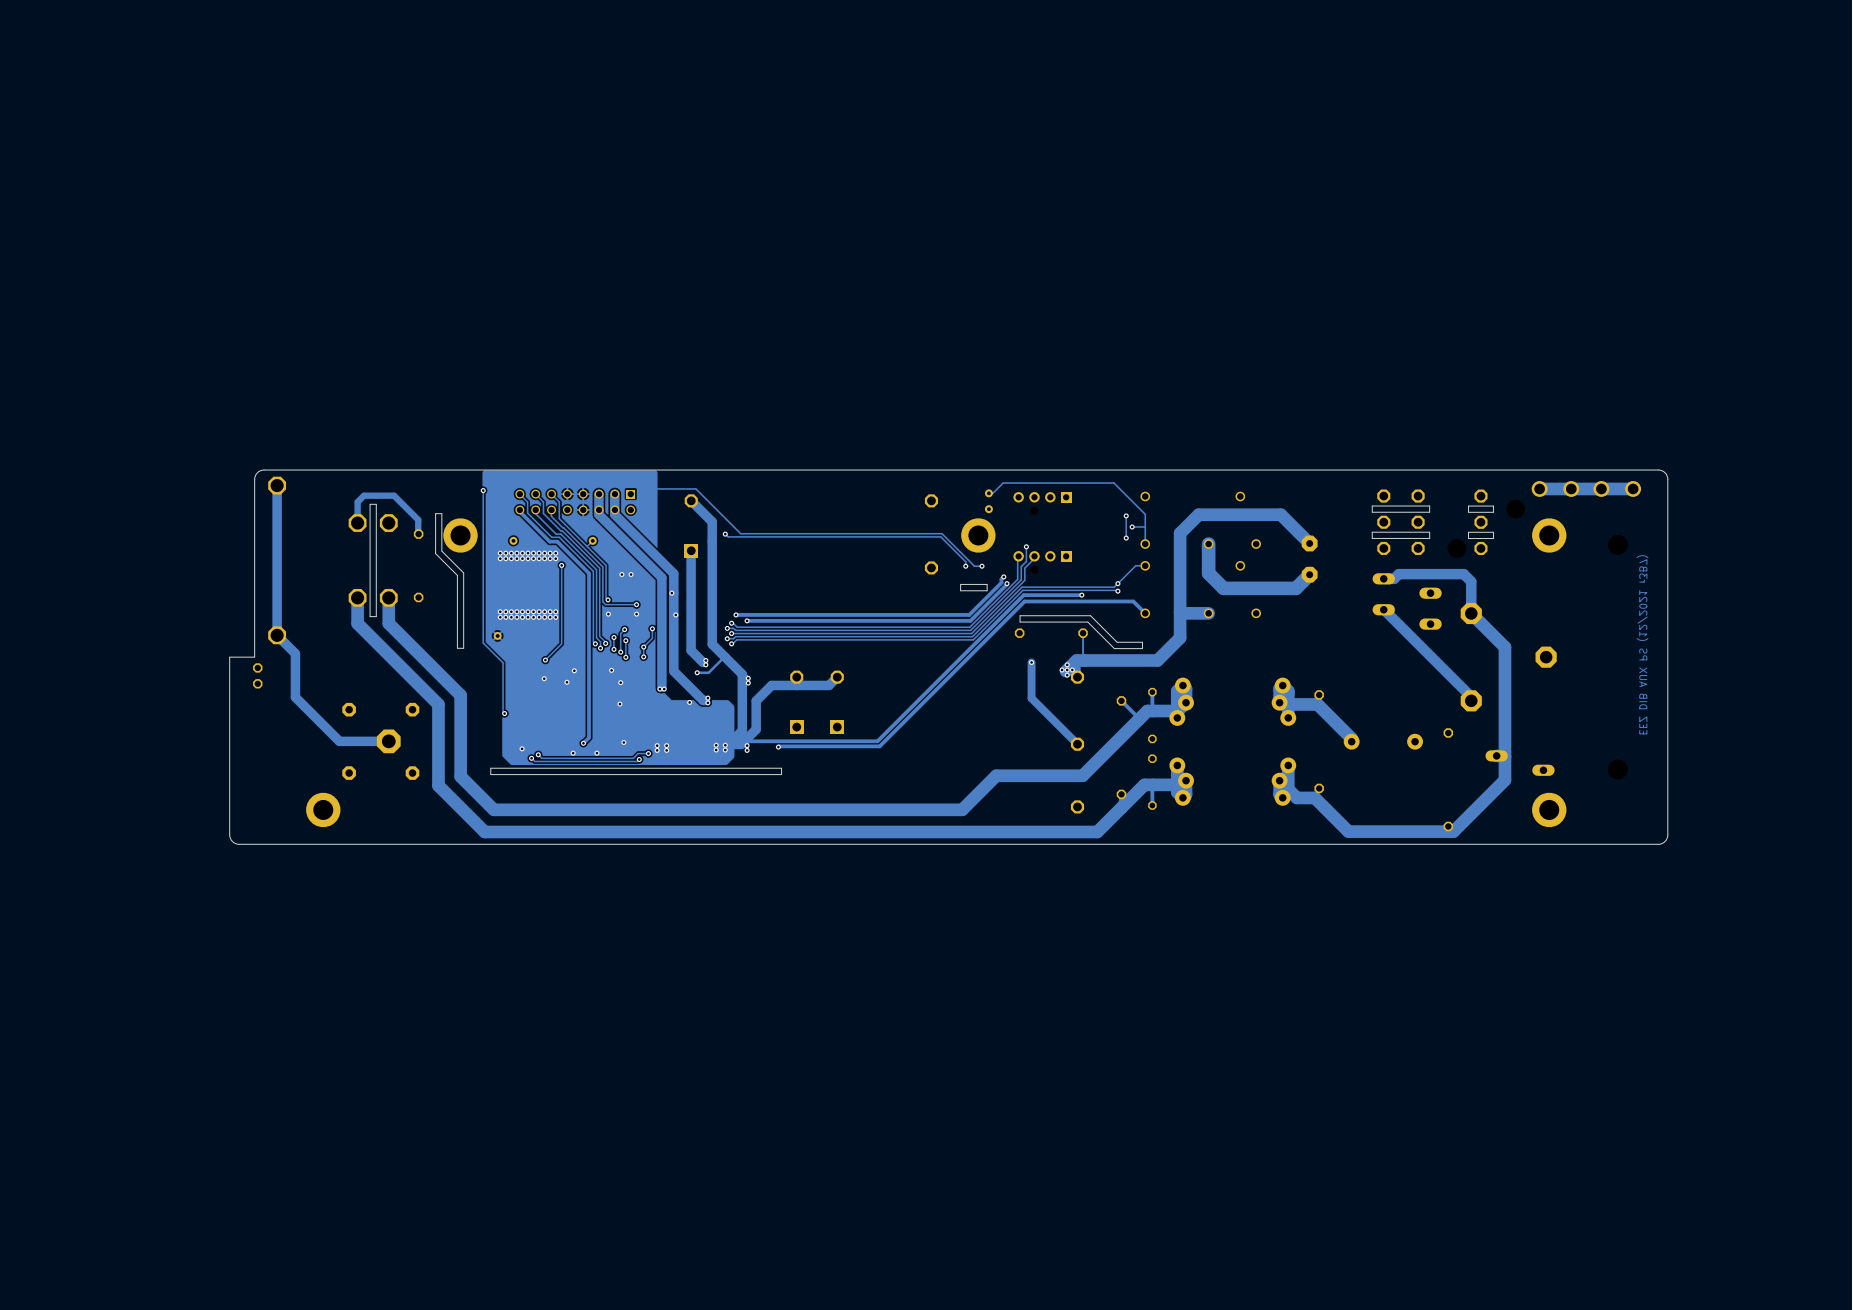
[picture p581: page 1]
