eez-open/modular-psu/aux-ps/Images/AUX PS r3B7 PCB top layer.pdf

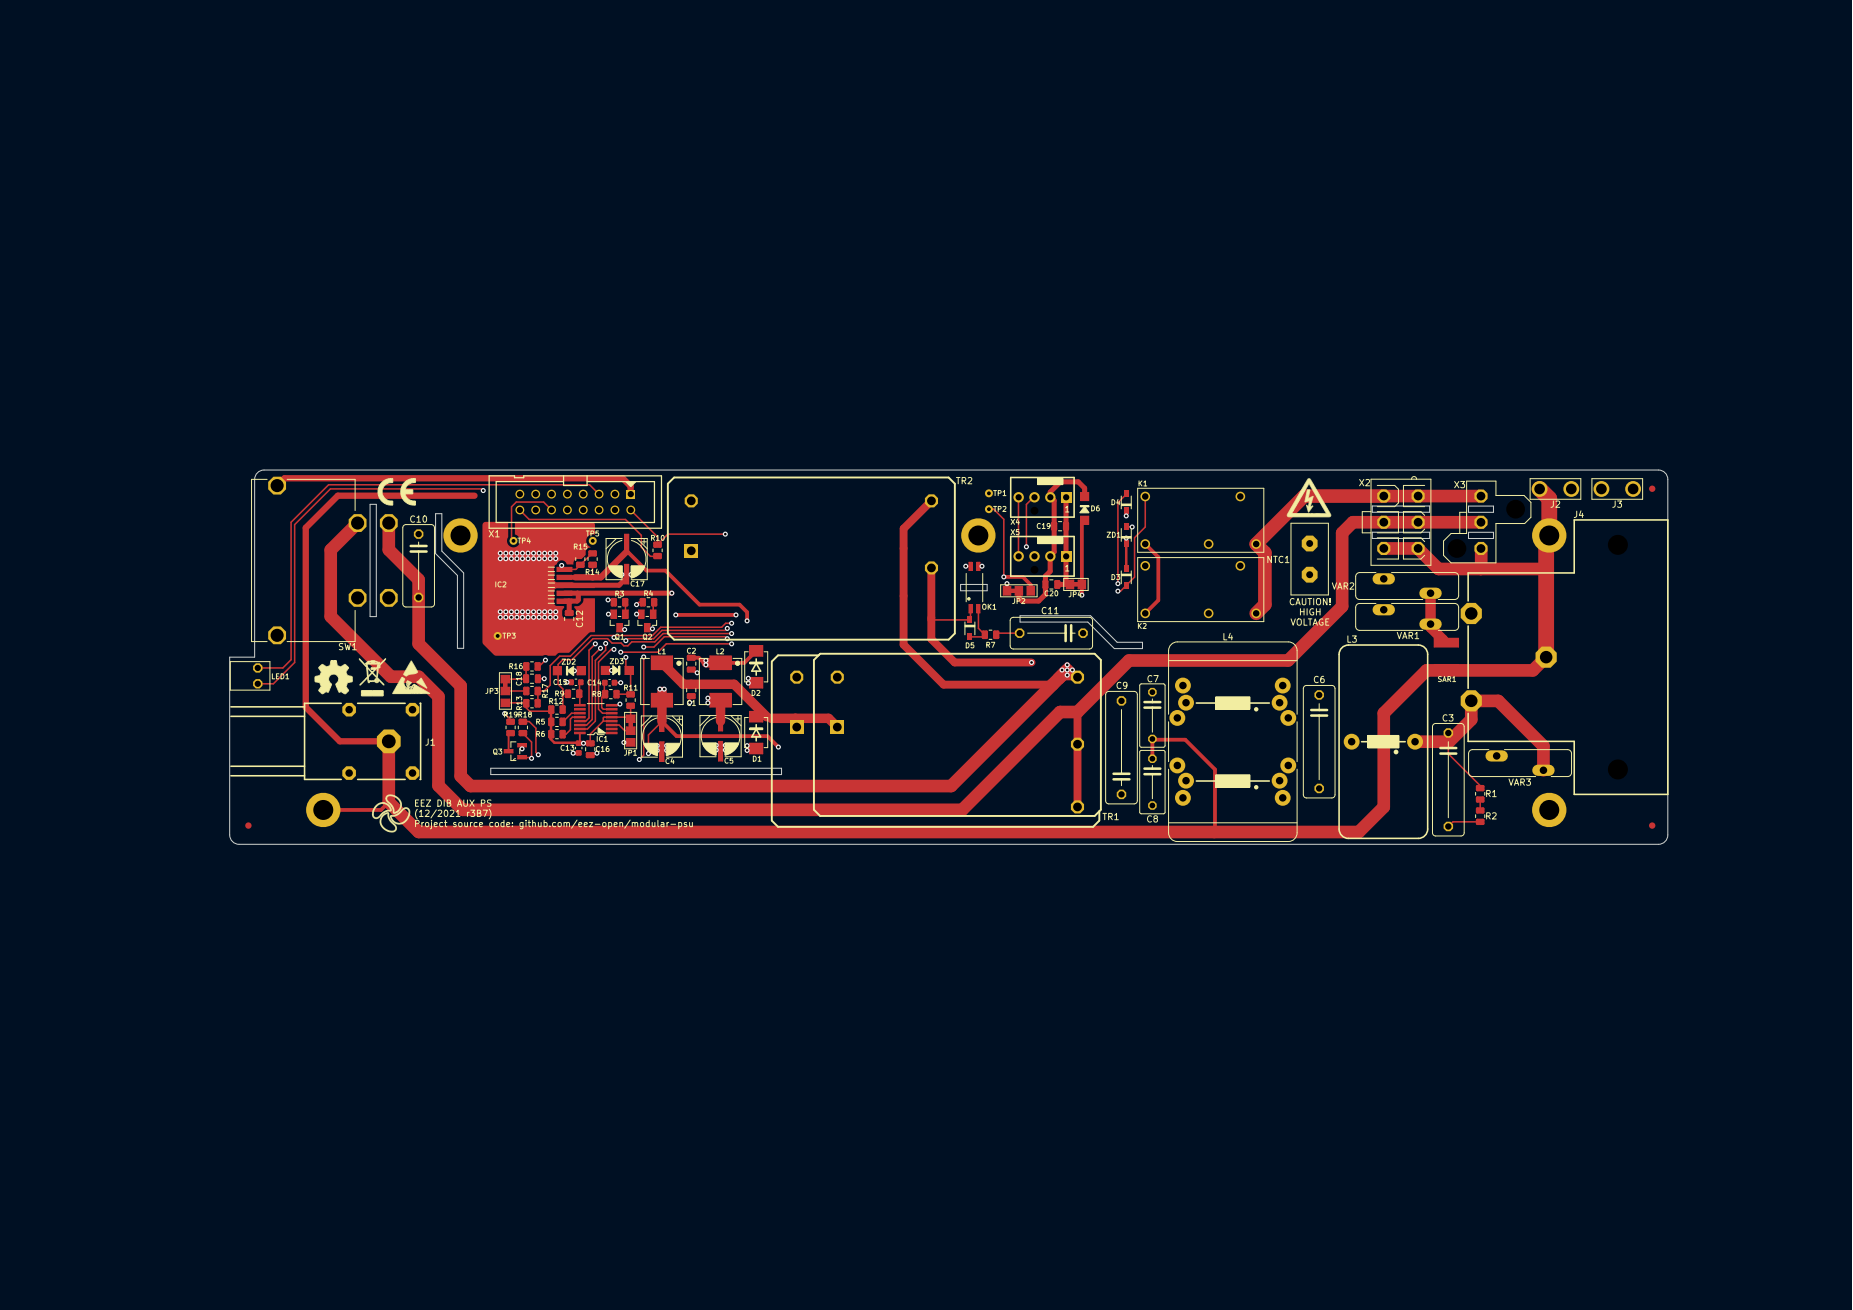
[picture p582: page 1]
