eez-open/modular-psu/previous designs/aux-ps r2B2/EEZ DIB AUX PS r2B2.pdf

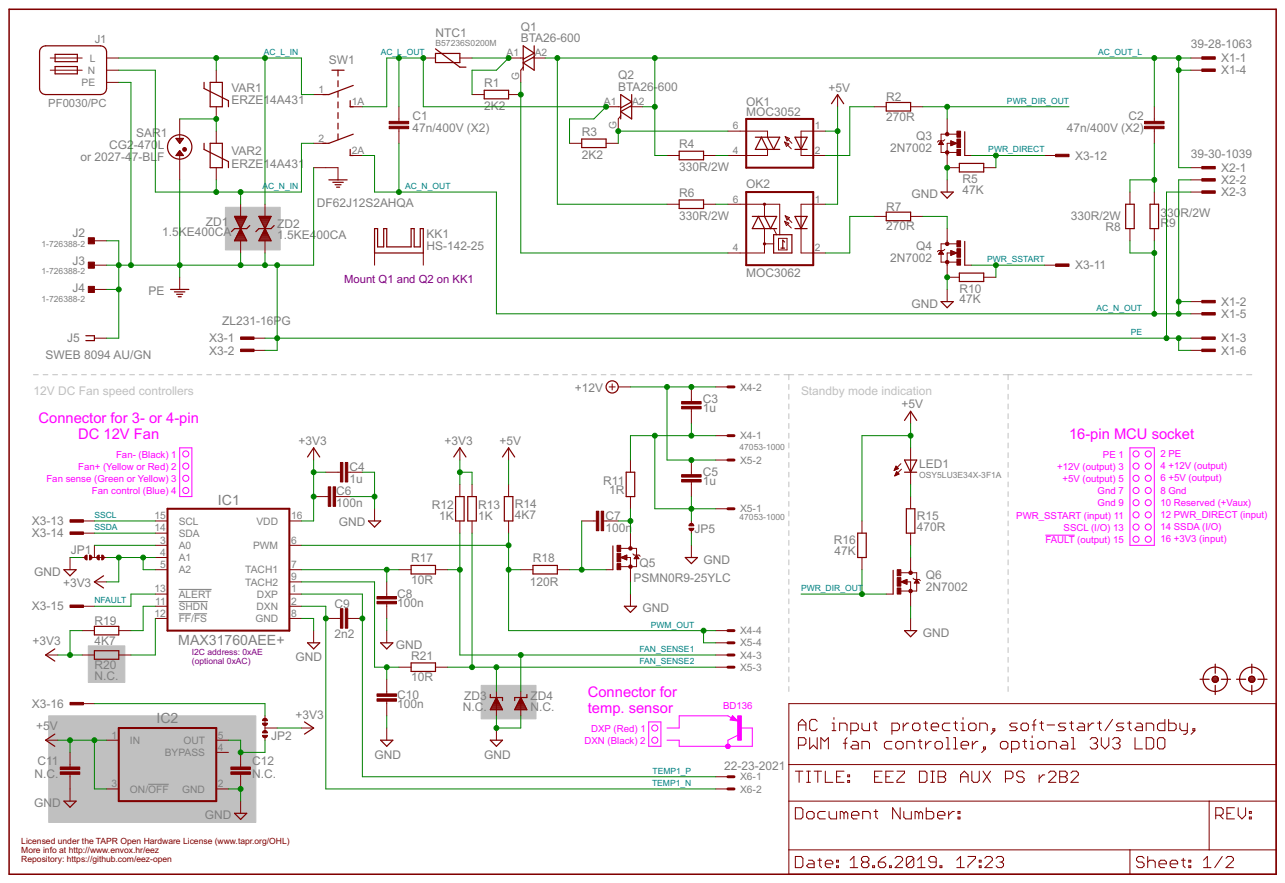
[picture p583: page 1]

Fan+ (Yellow or Red) 2 Fan- (Black) 1 Connector for 3- or 4-pin
DC 12V Fan

Fan sense (Green or Yellow) 3 Fan control (Blue) 4
SSCL SSDA NFAULT

DXN (Black) 2 DXP (Red) 1 Connector for

Licensed under the TAPR Open Hardware License (www.tapr.org/OHL) Repository: https://github.com/eez-open More info at http://www.envox.hr/eez

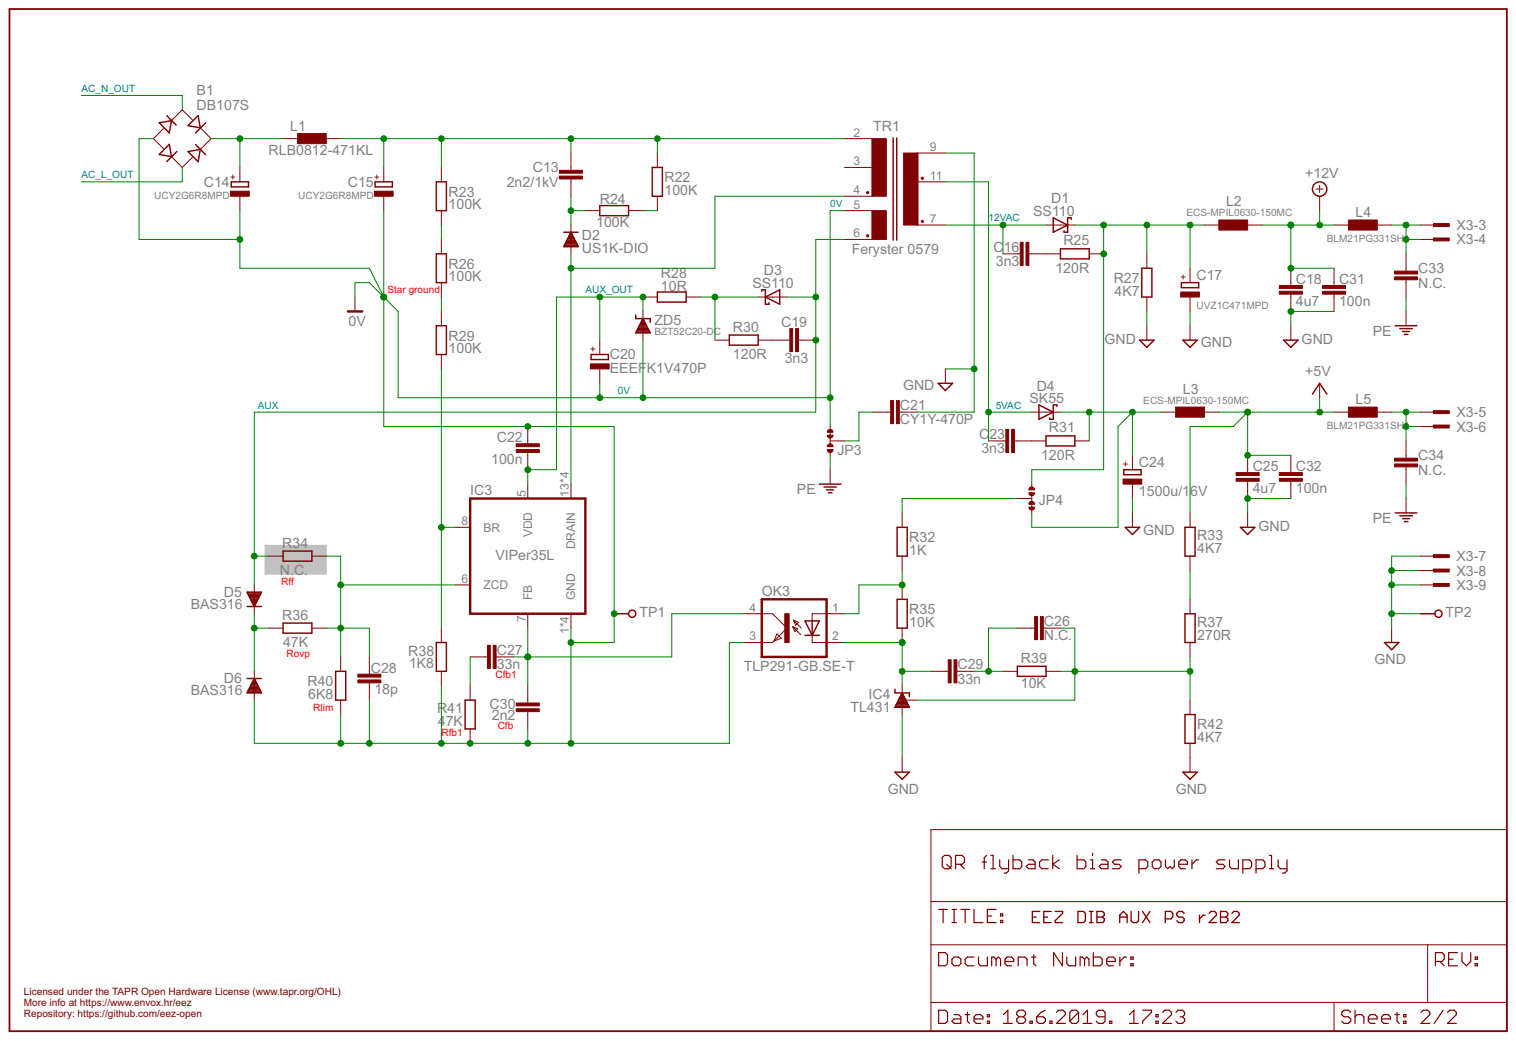
[picture p584: page 2]

Licensed under the TAPR Open Hardware License (www.tapr.org/OHL) Repository: https://github.com/eez-open More info at https://www.envox.hr/eez
