eez-open/modular-psu/aux-ps/EDA files/Eagle (obsolete)/EEZ DIB AUX PS r3B6.pdf

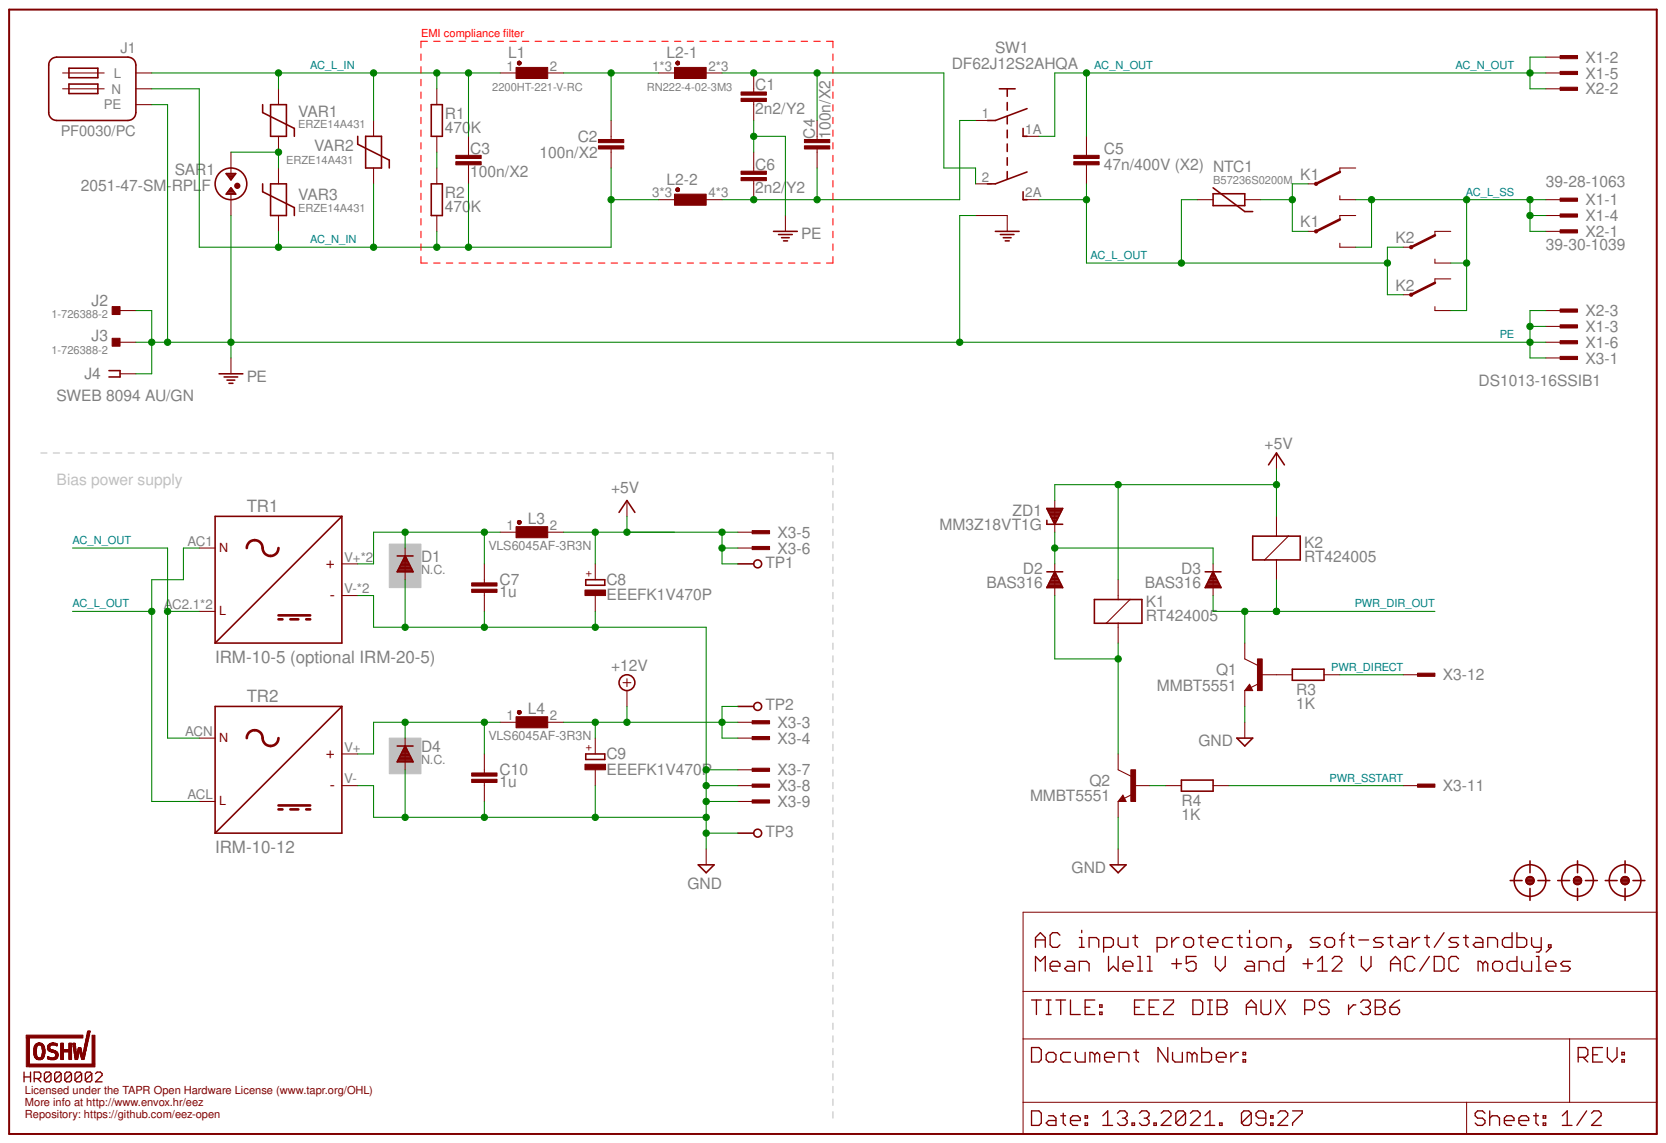
[picture p585: page 1]

Licensed under the TAPR Open Hardware License (www.tapr.org/OHL) Repository: https://github.com/eez-open More info at http://www.envox.hr/eez

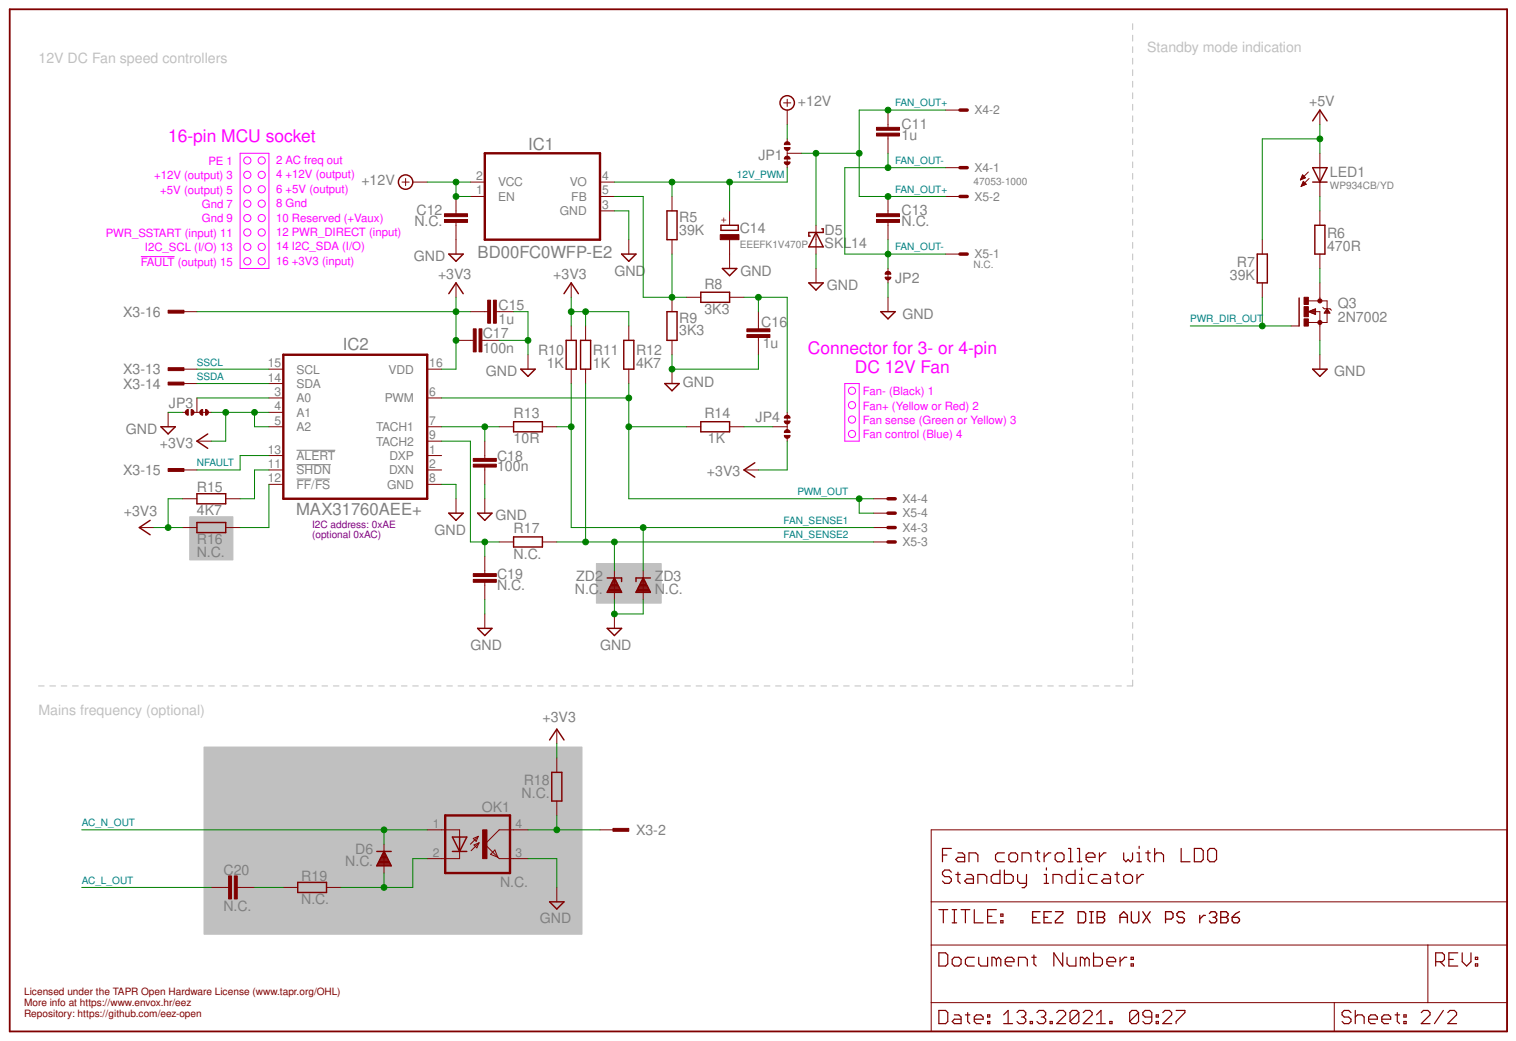
[picture p586: page 2]

12V DC Fan speed controllers

2 AC freq out Gnd 7

Fan+ (Yellow or Red) 2 Fan- (Black) 1 Connector for 3- or 4-pin
DC 12V Fan

Fan sense (Green or Yellow) 3 Fan control (Blue) 4

Licensed under the TAPR Open Hardware License (www.tapr.org/OHL) Repository: https://github.com/eez-open More info at https://www.envox.hr/eez
