eez-open/modular-psu/bp3c/EDA files/Eagle (obsolete)/EEZ DIB BP3C r3B3.pdf

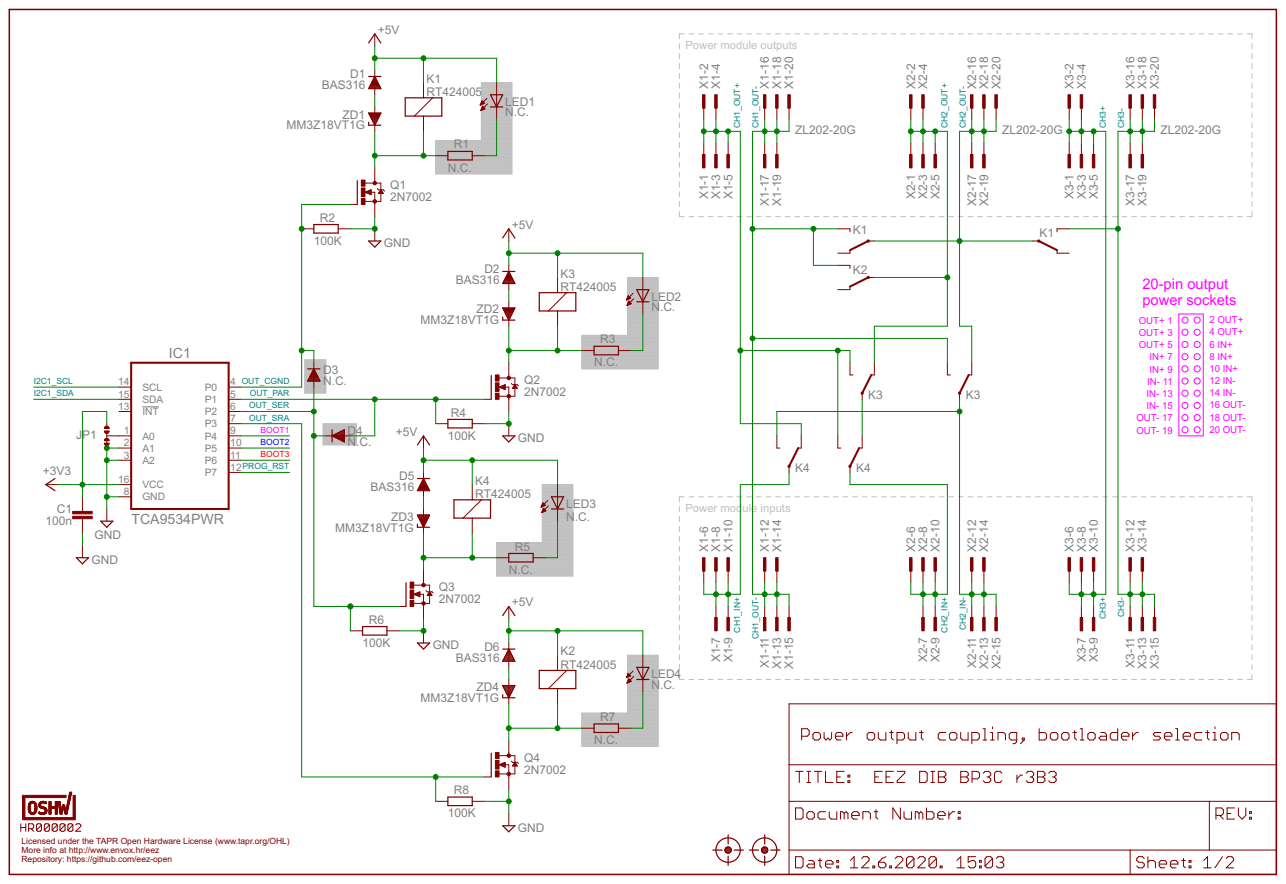
[picture p587: page 1]

Licensed under the TAPR Open Hardware License (www.tapr.org/OHL) Repository: https://github.com/eez-open More info at http://www.envox.hr/eez

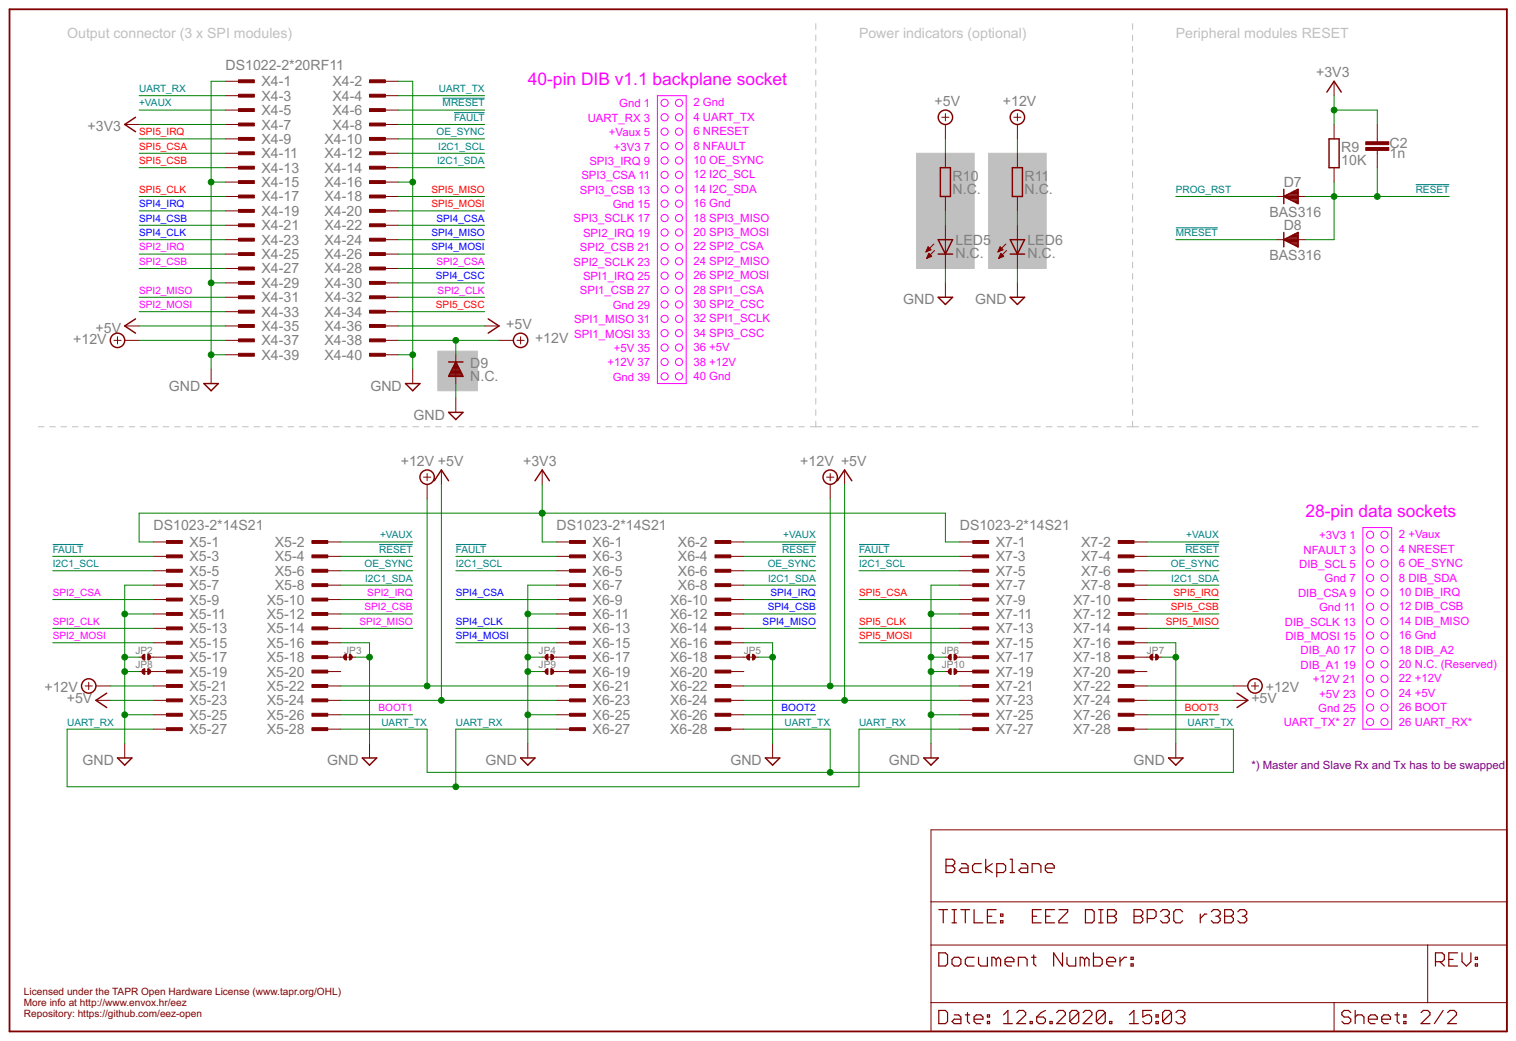
[picture p588: page 2]

*) Master and Slave Rx and Tx has to be swapped

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
