eez-open/modular-psu/dcp405/Spice/EEZ DIB DCP405 r2B6.asc

C1: cap; 330p
C2: cap; 470µ; Rser=.18
C3: cap; 33p
C4: cap; 470n
C10: cap; 6n8
C11: cap; 2n2
C15: cap; 2n2
C17: cap; 1n
D1: diode; 1N4148
D2: schottky; BAT54
D5: zener; BZX84C12L
D7: diode; 1N4148
D20: diode; 1N4148
DP_switch_simulation1: voltage; PULSE(0 5 0 1u 1u 100m 300m 3)
Iset1: voltage; 1
LED1: LED; NSPW500BS
LED2: LED; NSPW500BS
M1: nmos; IRF8910
M2: nmos; 2N7002
M3: pmos; BSS84
M4: nmos; 2N7002
OE_switch_simulation: voltage; 5
Q1: pnp; D45H11
Q2: pnp; D45H11
Q3: pnp; BC856B
Q4: pmos; IRF9640
Q6: npn; QBCP56-16
Q7: xnpndrlngtn
R1: res; 20R
R2: res; 2K2
R3: res; 10k
R4: res; 10k
R5: res; 100k; tol=0.1
R6: res; 100k; tol=0.1
R7: res; 10R
R8: res; 24K; tol=0.1
R9: res; 24K; tol=0.1
R10: res; 7.5k; tol=0.1
R11: res; 7.5k; tol=0.1
R12: res; 1
R13: res; 0R1
R16: res; 0R1
R17: res; 15R
R18: res; 10m
R19: res; 100K
R20: res; 10K
R21: res; 4K7
R22: res; 5R
R23: res; 10R
R24: res; 10K
R25: res; 4K7
R26: res; 300
R27: res; 10K
R28: res; 4K7
R29: res; 300
R30: res; 4K7
R31: res; 4K7
R32: res; 0.001r
R33: res; 22k
R34: res; 5k6
R35: res; 2R2
R36: res; 4K7
R37: res; 4k7
R39: res; 220r
R40: res; 2.2K
R41: res; 1k
R42: res; 820R
R43: res; 10K
R44: res; 10k
R45: res; 820R
R46: res; 1K
R47: res; 39K
R48: res; 39K
R50: res; 2k2
R51: res; 100k
R52: res; 2k2
S1: sw; MYSW
U1: opamp2; MC33274/MC
U2: opamp2; MC33274/MC
U3: XOPAMP
U4: opamp2; MC33274/MC
U5: XOPAMP
U9: LTC2050HV
Uset: voltage; PULSE(0 1 1m 100u 100u 20m 40m)
V1: voltage; PULSE(0 1 1m 100u 100u 20m 40m)
V2: voltage; 5
V3: voltage; 5
Vcc1: voltage; 50m
Vdp: voltage; -9
Vin: voltage; 24
Named nets: 0, U_SET, Vout+, U_MON, CV_out, Vout-, I_SET, CC_out, COM, OE, OE_SW, -Vdp, LOAD_SW, Vcc, Vee, DP, I_MON, CV, Drive, CC, !dp_cmd, dp_action
Set Vout (0-2.5V for 0-40 V)
Voltage error amplifier
Voltage sense amplifier
.tran 0.6
Set max. Iout (0-2.5V for 0-5A)
Current error amplifier
.inc QBCP56-16.lib
.model MYSW SW(Ron=10m Roff=1Meg Vt=.5 Vh=-.4)
Down-programmer
Set to 5V to disable Down-programmer
.include BDX53C.lib
.inc LM339A.5_1_ti.txt
.inc motoramp.lib
EEZ DIB DCP405 power module postregulator simulation 
More info: www.envox.hr/eez or github.com/eez-open/modular-psu
CV / CC detection and indicators
