eez-open/modular-psu/dcp505/Spice/Auto-ranging/EEZ 3-level current auto-ranging v3a.asc

C1: cap; 10n
C2: cap; 10n
C3: cap; 1n
C5: cap; 0
D1: schottky; MBRB2545CT
D2: diode; 1N4148
D3: diode; 1N4148
D4: diode; 1N4148
D5: diode; 1N4148
GCOM: voltage; 0.05
I_SET: voltage; 0.2
Iload: current; PWL(10m 0 20m 50m 30m 500m 40m 5A)
M1: nmos; IRLHM620
M2: nmos; IRLHM620
M3: nmos; IRLHM620
M4: nmos; 2N7002
M5: nmos; 2N7002
Q1: pnp; BC556B
Q2: pnp; BC556B
R1: res; 1R
R2: res; 0.1R
R3: res; 0.01R
R4: res; 3K3
R5: res; 3K3
R6: res; 3K3
R7: res; 158K
R8: res; 1K1
R9: res; 158K
R10: res; 0.02R
R11: res; 1k
R12: res; 1k
R13: res; 1k
R14: res; 1K
R15: res; 249K
R16: res; 10k
R17: res; 10k
R18: res; 1k
R19: res; 100R
R20: res; 10k
R21: res; 10K
R22: res; 100R
R25: res; 2k2
R26: res; 2k2
R29: res; 1K
R30: res; 24K
R31: res; 24K
R32: res; 10k
R33: res; 11k
R34: res; 1K
R35: res; 5k
R38: res; 1k
R39: res; 10k
R40: res; 10k
R41: res; 10k
R42: res; 1K
R43: res; 249K
R44: res; 1Meg
R45: res; 1Meg
U1: opamp2; MC33274/MC
U2: opamp2; MC33274/MC
U3: opamp2; MC33274/MC
U4: opamp2; MC33274/MC
U5: opamp2; MC33274/MC
U7: opamp2; MC33274/MC
U10: opamp2; MC33274/MC
U14: opamp2; MC33274/MC
V1: voltage; 5
V2: voltage; 5
Vref: voltage; 2.5
Named nets: 0, Vcc, Vee, I_CTRL, I_MON, CURR_5A, CURR_500MA, CURR_50MA, Vref, I_LIM
.tran 60m
-2V5
-250mV
EEZ current auto-ranging simulation (50 mA / 500 mA / 5 A)
More info: www.envox.hr/eez or github.com/eez-open/modular-psu
Existing post-regulator circuit
.inc motoramp.lib
To I/O Expander inputs
