eez-open/modular-psu/dcp505/Spice/Auto-ranging/EEZ 3-level current auto-ranging v2.asc

C1: cap; 10n
C2: cap; 10n
C3: cap; 1n
C5: cap; 0
D1: schottky; MBRB2545CT
D2: diode; 1N4148
D3: diode; 1N4148
D4: diode; 1N4148
D5: diode; 1N4148
I_SET: voltage; 1.5
Iload: current; PWL(10m 0 20m 50m 30m 500m 40m 5A)
M1: nmos; IRLHM620
M2: nmos; IRLHM620
M3: nmos; IRLHM620
M4: nmos; 2N7002
M5: nmos; 2N7002
Q1: pnp; BC556B
Q2: pnp; BC556B
R1: res; 1R
R2: res; 0.1R
R3: res; 0.01R
R4: res; 3K
R5: res; 3K
R6: res; 3K
R7: res; 48K2
R8: res; 1K
R9: res; 48K2
R10: res; 0.01R
R11: res; 1k
R12: res; 1k
R13: res; 1k
R14: res; 1K
R15: res; 500k
R16: res; 10k
R17: res; 10k
R18: res; 1k
R19: res; 100R
R20: res; 10k
R21: res; 10K
R22: res; 100R
R23: res; 10k
R24: res; 10k
R25: res; 2k2
R26: res; 2k2
R27: res; 10k
R28: res; 10k
R29: res; 1k
R30: res; 1k
R31: res; 1k
R32: res; 10k
R33: res; 11k
R35: res; 5k
R36: res; 10K
R37: res; 30K
R38: res; 1k
R39: res; 10k
R40: res; 10k
R41: res; 10k
R42: res; 1K
R43: res; 500K
R44: res; 1Meg
R45: res; 1Meg
R47: res; 7.5Meg
U1: opamp2; MC33274/MC
U2: opamp2; MC33274/MC
U3: opamp2; MC33274/MC
U4: opamp2; MC33274/MC
U5: opamp2; MC33274/MC
U6: opamp2; MC33274/MC
U7: opamp2; MC33274/MC
U8: opamp2; MC33274/MC
U10: opamp2; MC33274/MC
U11: CD4066
U12: CD4066
U13: CD4066
U14: opamp2; MC33274/MC
V1: voltage; 5
V2: voltage; 5
V4: voltage; 2.5
Named nets: 0, Vcc, Vee, I_CTRL, I_MON, CURR_5A, CURR_500MA, CURR_50MA, Vref, CC_SHIFT
.tran 60m startup
I SET ranges:
0 - 0.833333 V = CURR_50MA range
0.8333 - 1.6666 V = CURR_500MA range
1.6666 - 2.5 V = CURR_5A range
-2V5
-250mV
.include cd4066.sub
EEZ current auto-ranging simulation (50 mA / 500 mA / 5 A)
More info: www.envox.hr/eez or github.com/eez-open/modular-psu
Existing current control loop circuit
.inc motoramp.lib
