eez-open/modular-psu/dcp505/Spice/OVP/OVP max current simulation.asc

C1: cap; 10000µ
L1: ind; 1.1µH
R1: res; 2R2
R2: res; 0.1R
S1: sw; MYSW
V1: voltage; 50V
V2: voltage; PULSE(0 5 100u 10n)
Named nets: 0
.model MYSW SW(Ron=0.01Roff=100Meg Vt=2Vh=0)
.tran 2m
