eez-open/modular-psu/dcp505/Eagle files/EEZ DIB DCP505 r1B2.sch

## EAGLE design dcp505/Eagle files/EEZ DIB DCP505 r1B2.sch (2019-01-07)

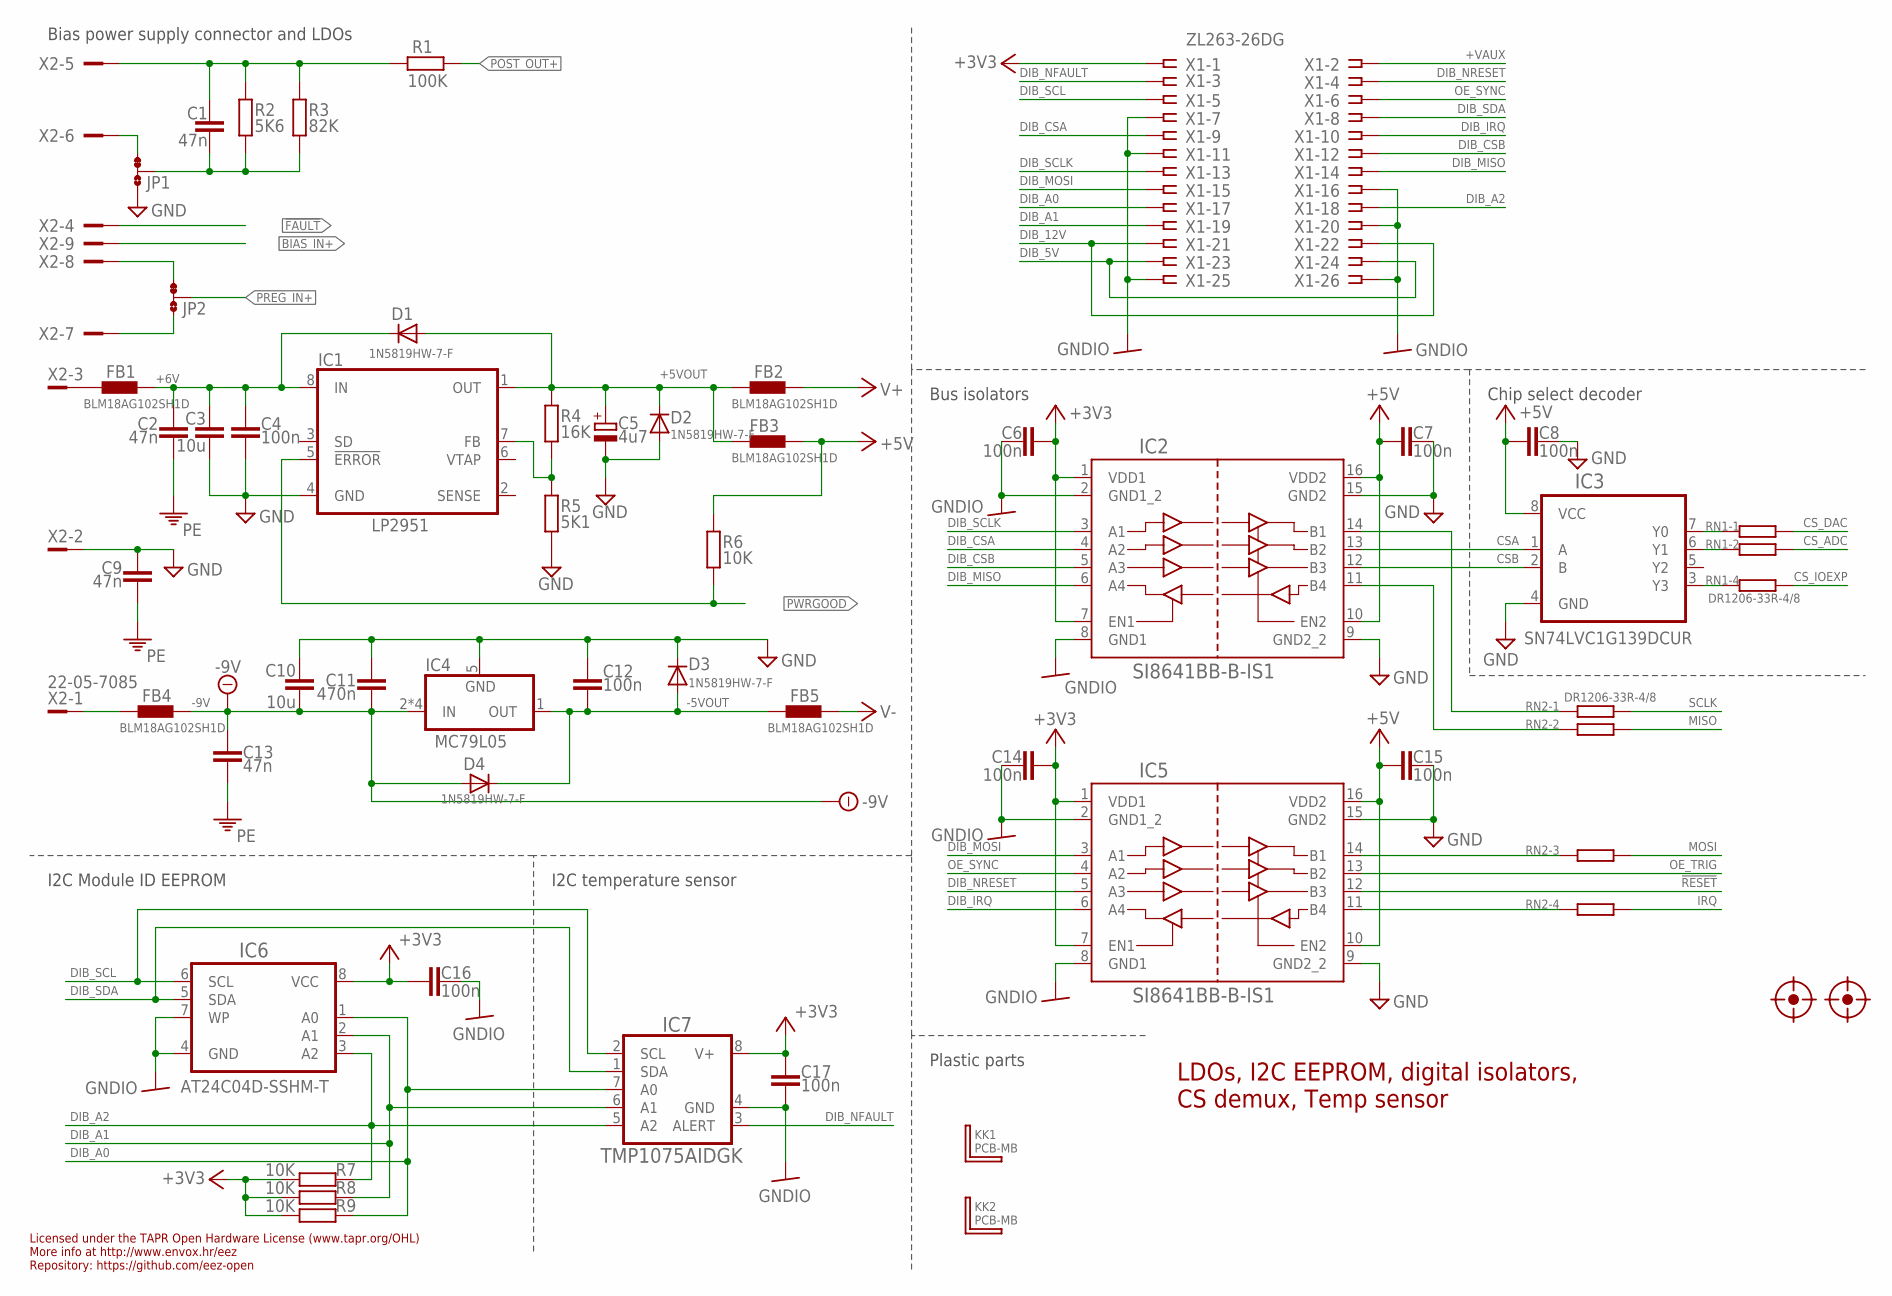
[picture p633: schematic EEZ DIB DCP505 r1B2.sch, sheet 1]

Parts:
C1: 47n; C0805
C2, C9, C13: 47n; C1206
C3, C10: 10u; C1206
C4, C6, C7, C8, C12, C14, C15, C16, C17: 100n; C0603
C5: 4u7; EC1206
C11: 470n; C0805
D1, D2, D3, D4: 1N5819HW-7-F; SOD323-W
FB1, FB2, FB3, FB4, FB5: BLM18AG102SH1D; BEAD0603
FM1, FM2: FIDUCIAL_2; FIDUCIAL_DUAL
IC1: LP2951; SOIC127P600X175-8N
IC2, IC5: SI8641BB-B-IS1; SOIC-16
IC3: SN74LVC1G139DCUR; DCU8
IC4: MC79L05; SOIC127P600X173-8N
IC6: AT24C04D-SSHM-T; SOIC127P600X173-8N
IC7: TMP1075AIDGK; DGK8
JP1, JP2: JP3-CUT
KK1, KK2: PCB-MB
R1: 100K; R0805
R2: 5K6; R0805
R3: 82K; R0805
R4: 16K; R0805
R5: 5K1; R0805
R6, R7, R8, R9: 10K; R0805
RN1, RN2: DR1206-33R-4/8; CAY16
X1: ZL263-26DG; SSW-113-02-T-D-RA
X2: 22-05-7085; SPOX_22-05-7095

Connections:
!FAULT: X2.4
!RESET: IC5.12 (B3)
+3V3: C6.1, C14.1, C16.2, C17.1, IC2.1 (VDD1), IC2.7 (EN1), IC5.1 (VDD1), IC5.7 (EN1), IC6.8 (VCC), IC7.8 (V+), R7.1, R8.1, R9.1, X1.1
+5V: C7.2, C8.1, C15.2, FB3.P$2 (2), IC2.10 (EN2), IC2.16 (VDD2), IC3.8 (VCC), IC5.10 (EN2), IC5.16 (VDD2), R6.1
+5VOUT: C5.+, D1.A, D2.C, FB2.P$1 (1), FB3.P$1 (1), IC1.1 (OUT), R4.1
+6V: C2.1, C3.1, C4.1, D1.C, FB1.P$2 (2), IC1.8 (IN)
+VAUX: X1.2
-5VOUT: C12.2, D3.A, D4.C, FB5.P$1 (1), IC4.1 (OUT)
-9V: C10.2, C11.2, C13.1, D4.A, FB4.P$2 (2), IC4.2 (IN)
BIAS_IN+: X2.9
CSA: IC2.13 (B2), IC3.1 (A)
CSB: IC2.12 (B3), IC3.2 (B)
CS_ADC: RN1.7 (2)
CS_DAC: RN1.8 (2)
CS_IOEXP: RN1.5 (2)
DIB_5V: X1.23, X1.24
DIB_12V: X1.21, X1.22
DIB_A0: IC6.1 (A0), IC7.7 (A0), R9.2, X1.17
DIB_A1: IC6.2 (A1), IC7.6 (A1), R8.2, X1.19
DIB_A2: IC6.3 (A2), IC7.5 (A2), R7.2, X1.18
DIB_CSA: IC2.4 (A2), X1.9
DIB_CSB: IC2.5 (A3), X1.12
DIB_IRQ: IC5.6 (A4), X1.10
DIB_MISO: IC2.6 (A4), X1.14
DIB_MOSI: IC5.3 (A1), X1.15
DIB_NFAULT: IC7.3 (ALERT), X1.3
DIB_NRESET: IC5.5 (A3), X1.4
DIB_SCL: IC6.6 (SCL), IC7.2 (SCL), X1.5
DIB_SCLK: IC2.3 (A1), X1.13
DIB_SDA: IC6.5 (SDA), IC7.1 (SDA), X1.8
GND: C3.2, C4.2, C5.-, C7.1, C8.2, C9.1, C10.1, C11.1, C12.1, C15.1, D2.A, D3.C, IC1.4 (GND), IC2.9 (GND2_2), IC2.15 (GND2), IC3.4 (GND), IC4.5 (GND), IC5.9 (GND2_2), IC5.15 (GND2), JP1.NO, R5.2, X2.2
GNDIO: C6.2, C14.2, C16.1, C17.2, IC2.2 (GND1_2), IC2.8 (GND1), IC5.2 (GND1_2), IC5.8 (GND1), IC6.4 (GND), IC6.7 (WP), IC7.4 (GND), X1.7, X1.11, X1.16, X1.20, X1.25, X1.26
IRQ: RN2.5 (2)
MISO: RN2.7 (2)
MOSI: RN2.6 (2)
unnamed: FB1.P$1 (1), X2.3
unnamed: FB4.P$1 (1), X2.1
unnamed: IC3.7 (Y0), RN1.1
unnamed: IC2.11 (B4), RN2.2 (1)
unnamed: IC5.11 (B4), RN2.4 (1)
unnamed: C1.2, JP1.COM, R2.2, R3.2
unnamed: C1.1, R1.2, R2.1, R3.1, X2.5
unnamed: IC3.6 (Y1), RN1.2 (1)
unnamed: IC3.3 (Y3), RN1.4 (1)
unnamed: JP1.NC, X2.6
unnamed: IC5.14 (B1), RN2.3 (1)
unnamed: JP2.NO, X2.7
unnamed: JP2.NC, X2.8
unnamed: IC1.7 (FB), R4.2, R5.1
unnamed: IC2.14 (B1), RN2.1
OE_SYNC: IC5.4 (A2), X1.6
OE_TRIG: IC5.13 (B2)
PE: C2.2, C9.2, C13.2
POST_OUT+: R1.1
PREG_IN+: JP2.COM
PWRGOOD: IC1.5 (!ERROR), R6.2
SCLK: RN2.8 (2)
V+: FB2.P$2 (2)
V-: FB5.P$2 (2)

Notes on the sheet:
Licensed under the TAPR Open Hardware License (www.tapr.org/OHL)
Repository: https://github.com/eez-open
More info at http://www.envox.hr/eez
I2C Module ID EEPROM
Bus isolators
LDOs, I2C EEPROM, digital isolators,
Plastic parts
Chip select decoder
Bias power supply connector and LDOs
I2C temperature sensor
CS demux, Temp sensor

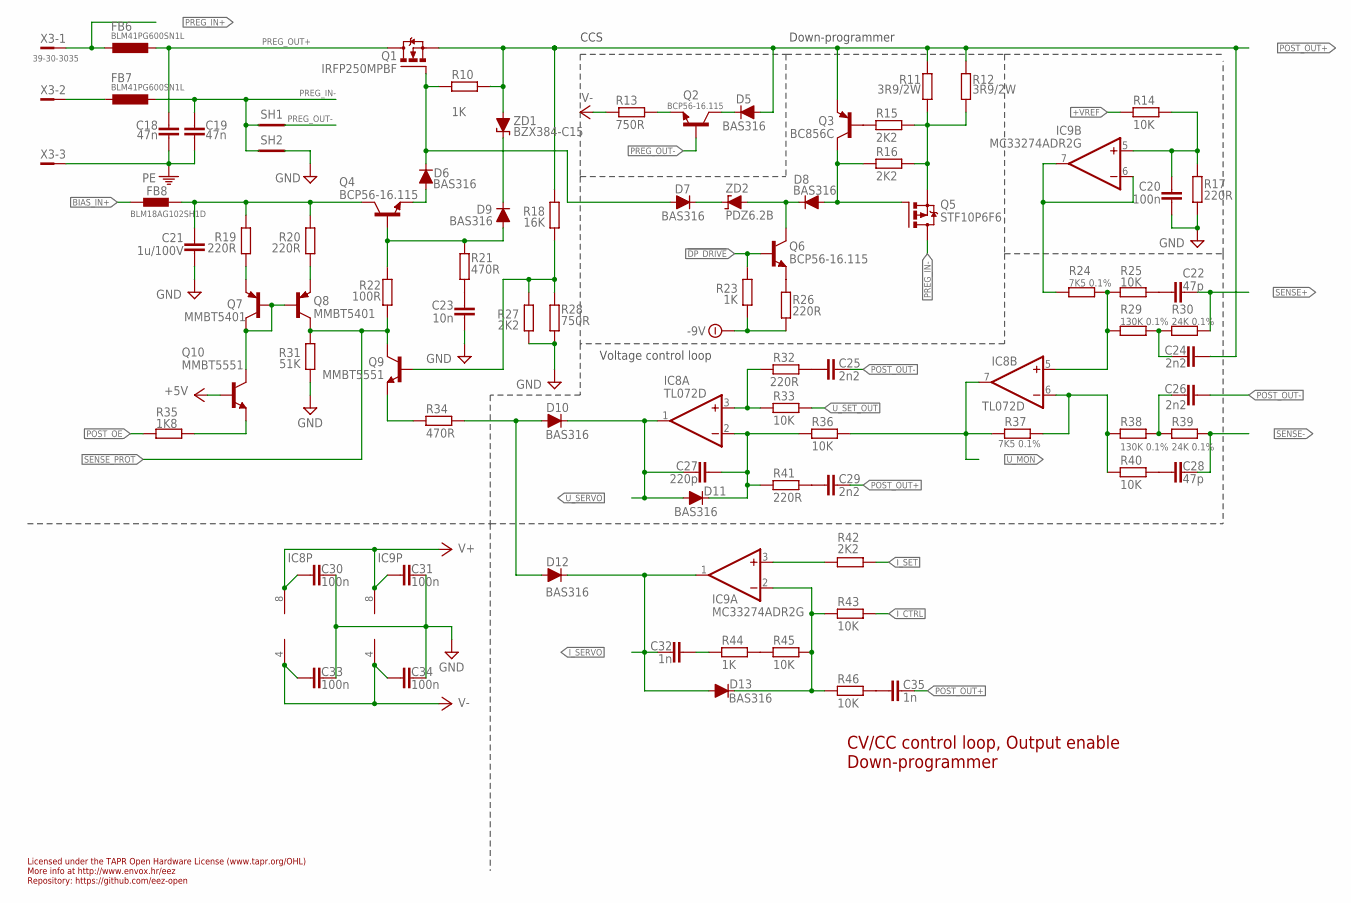
[picture p634: schematic EEZ DIB DCP505 r1B2.sch, sheet 2]

Parts:
C18, C19: 47n; C1206
C20, C30, C31, C33, C34: 100n; C0603
C21: 1u/100V; C1206
C22, C28: 47p; C0805
C23: 10n; C0805
C24, C25, C26, C29: 2n2; C0805
C27: 220p; C0805
C32, C35: 1n; C0805
D5, D6, D7, D8, D9, D10, D11, D12, D13: BAS316; SOD323-R
FB6, FB7: BLM41PG600SN1L; L1812
FB8: BLM18AG102SH1D; BEAD0603
IC8: TL072D; SOIC127P600X173-8N
IC9: MC33274ADR2G; SOIC127P600X173-8N
Q1: IRFP250MPBF; TO247BH-CLR2
Q2, Q4, Q6: BCP56-16.115; SOT230P700X180-4N
Q3: BC856C; SOT23-BEC
Q5: STF10P6F6; TO220H-CLR2
Q7, Q8: MMBT5401; SOT23-BEC
Q9, Q10: MMBT5551; SOT23-BEC
R10, R23, R44: 1K; R0805
R11, R12: 3R9/2W; R2512
R13, R28: 750R; R0805
R14, R25, R33, R36, R40, R43, R45, R46: 10K; R0805
R15, R16, R27, R42: 2K2; R0805
R17, R19, R20, R26, R32, R41: 220R; R0805
R18: 16K; R0805
R21, R34: 470R; R0805
R22: 100R; R0805
R24, R37: 7K5 0.1%; R0805
R29, R38: 130K 0.1%; R0805
R30, R39: 24K 0.1%; R0805
R31: 51K; R0805
R35: 1K8; R0805
SH1, SH2: SHORTNOHOLE; SHORT_NOHOLE
X3: 39-30-3035; MINIFIT_6659-3
ZD1: BZX384-C15; SOD323-W
ZD2: PDZ6.2B; SOD323-W

Connections:
!DP_DRIVE: Q6.1 (B), R23.1
+5V: Q10.B
+VREF: R14.1
-9V: R23.2, R26.2
BIAS_IN+: FB8.P$1 (1)
CCS_HS: D5.C, Q2.2 (C)
DC_BIAS: C21.1, FB8.P$2 (2), Q4.2 (C), R19.2, R20.2
DP_S: Q5.3 (S), R11.1, R12.1, R15.1, R16.1
GCOM: IC9.6 (-IN), IC9.7 (OUT), R24.1
GND: C20.2, C21.2, C23.2, C30.1, C31.1, C33.1, C34.1, R17.2, R27.1, R28.1, R31.1, SH2.P$2 (GND_B)
I_CTRL: R43.1
I_SERVO: C32.2, D12.C, D13.A, IC9.1 (OUT)
I_SET: R42.1
LOOP_CTRL: D10.A, D12.A, R34.1
unnamed: FB7.1, X3.2
unnamed: IC9.3 (+IN), R42.2
unnamed: IC8.3 (+IN), R32.2, R33.2
unnamed: C27.1, D11.C, IC8.2 (-IN), R36.2, R41.2
unnamed: C26.1, R38.2, R39.1
unnamed: C22.2, R25.1
unnamed: C28.2, R40.1
unnamed: C35.2, R46.1
unnamed: D13.C, IC9.2 (-IN), R43.2, R45.2, R46.2
unnamed: C25.2, R32.1
unnamed: C29.2, R41.1
unnamed: D6.C, D7.A, Q1.1 (G), R10.1
unnamed: D6.A, Q4.3 (E)
unnamed: D9.A, Q4.1 (B), R21.2, R22.1
unnamed: C23.1, R21.1
unnamed: Q9.B, R18.1, R27.2, R28.2
unnamed: Q6.3 (E), R26.1
unnamed: Q3.B, R15.2
unnamed: C20.1, IC9.5 (+IN), R14.2, R17.1
unnamed: C24.1, R29.2, R30.1
unnamed: D9.C, ZD1.C
unnamed: D7.C, ZD2.C
unnamed: Q9.E, R34.2
unnamed: D8.A, Q3.C, Q5.1 (G), R16.2
unnamed: IC8.5 (+IN), R24.2, R25.2, R29.1
unnamed: IC8.6 (-IN), R37.2, R38.1, R40.2
unnamed: R44.2, R45.1
unnamed: C32.1, R44.1
unnamed: Q2.3 (E), R13.2
unnamed: Q8.E, R20.1
unnamed: Q7.E, R19.1
unnamed: Q10.E, R35.2
PE: C18.2, C19.2, X3.3
POST_OE: R35.1
POST_OUT+: C24.2, C29.1, C35.1, D5.A, Q1.3 (S), Q3.E, R10.2, R11.2, R12.2, R18.2, ZD1.A
POST_OUT-: C25.1, C26.2
PREG_IN+: FB6.1, X3.1
PREG_IN-: C19.1, FB7.2, Q5.2 (D), SH1.P$1 (GND_A), SH2.P$1 (GND_A)
PREG_OUT+: C18.1, FB6.2, Q1.2 (D)
PREG_OUT-: Q2.1 (B), SH1.P$2 (GND_B)
Q6C: D8.C, Q6.2 (C), ZD2.A
Q7C: Q7.B, Q7.C, Q8.B, Q10.C
SENSE+: C22.1, R30.2
SENSE-: C28.1, R39.2
SENSE_PROT: Q8.C, Q9.C, R22.2, R31.2
U_MON: IC8.7 (OUT), R36.1, R37.1
U_SERVO: C27.2, D10.C, D11.A, IC8.1 (OUT)
U_SET_OUT: R33.1
V+: C30.2, C31.2, IC8.8 (V+), IC9.8 (V+)
V-: C33.2, C34.2, IC8.4 (V-), IC9.4 (V-), R13.1

Notes on the sheet:
Voltage control loop
Down-programmer
Licensed under the TAPR Open Hardware License (www.tapr.org/OHL)
Repository: https://github.com/eez-open
More info at http://www.envox.hr/eez
CCS
CV/CC control loop, Output enable

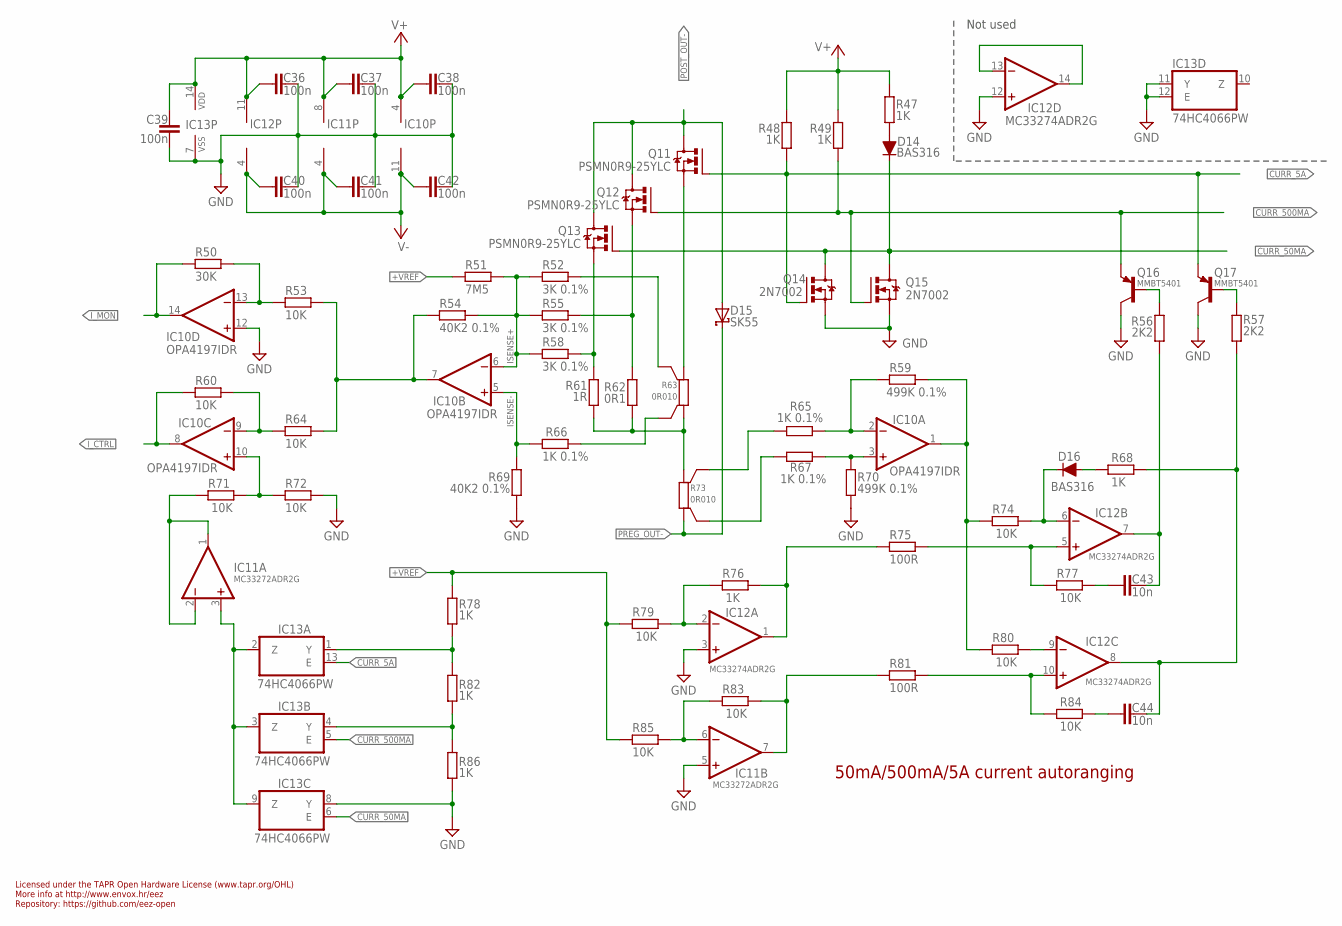
[picture p635: schematic EEZ DIB DCP505 r1B2.sch, sheet 3]

Parts:
C36, C37, C38, C39, C40, C41, C42: 100n; C0603
C43, C44: 10n; C0603
D14, D16: BAS316; SOD323-R
D15: SK55; SMB
IC10: OPA4197IDR; SOIC127P600X175-14N
IC11: MC33272ADR2G; SOIC127P600X173-8N
IC12: MC33274ADR2G; SOIC127P600X175-14N
IC13: 74HC4066PW; SOP65P640X120-14N
Q11, Q12, Q13: PSMN0R9-25YLC; SOT669
Q14, Q15: 2N7002; SOT103P240X110-3N; MPN 2N7002-7-F
Q16, Q17: MMBT5401; SOT23-BEC
R47, R48, R49, R68, R76, R78, R82, R86: 1K; R0805
R50: 30K; R0805
R51: 7M5; R0805
R52, R55, R58: 3K 0.1%; R0603
R53, R60, R64, R71, R72, R74, R77, R79, R80, R83, R84, R85: 10K; R0805
R54, R69: 40K2 0.1%; R0603
R56, R57: 2K2; R0805
R59, R70: 499K 0.1%; R0603
R61: 1R; R0805
R62: 0R1; R1206
R63, R73: 0R010; R_H2728
R65, R66, R67: 1K 0.1%; R0603
R75, R81: 100R; R0805

Connections:
+VREF: R51.1, R78.2, R79.2, R85.2
CURR_5A: IC13.13 (E), Q11.4 (G), Q14.1 (G), Q17.E, R48.2
CURR_50MA: D14.C, IC13.6 (E), Q13.4 (G), Q14.3 (D), Q15.3 (D)
CURR_500MA: IC13.5 (E), Q12.4 (G), Q15.1 (G), Q16.E, R49.2
GND: C36.2, C37.2, C38.2, C39.1, C40.2, C41.2, C42.2, IC10.12 (+IN), IC11.5 (+IN), IC12.3 (+IN), IC12.12 (+IN), IC13.7 (VSS), IC13.8 (Y), IC13.11 (Y), IC13.12 (E), Q14.2 (S), Q15.2 (S), Q16.C, Q17.C, R69.1, R70.2, R72.1, R86.1
ISENSE+: IC10.6 (-IN), R51.2, R52.2, R54.1, R55.2, R58.2
ISENSE-: IC10.5 (+IN), R66.2, R69.2
I_CTRL: IC10.8 (OUT), R60.2
I_MON: IC10.14 (OUT), R50.2
unnamed: R65.2, R73.2S
unnamed: R61.2, R62.1, R63.1, R73.2
unnamed: IC11.1 (OUT), IC11.2 (-IN), R71.2
unnamed: IC11.6 (-IN), R83.2, R85.1
unnamed: IC10.2 (-IN), R59.2, R65.1
unnamed: Q11.1 (S), R63.2
unnamed: D14.A, R47.2
unnamed: IC10.1 (OUT), R59.1, R74.2, R80.2
unnamed: IC11.3 (+IN), IC13.2 (Z), IC13.3 (Z), IC13.9 (Z)
unnamed: C43.2, IC12.7 (OUT), R56.2
unnamed: Q16.B, R56.1
unnamed: Q17.B, R57.1
unnamed: IC10.7 (OUT), R53.1, R54.2, R64.1
unnamed: IC10.9 (-IN), R60.1, R64.2
unnamed: IC13.1 (Y), R78.1, R82.2
unnamed: C44.2, IC12.8 (OUT), R57.2, R68.2
unnamed: IC10.10 (+IN), R71.1, R72.2
unnamed: IC13.4 (Y), R82.1, R86.2
unnamed: IC11.7 (OUT), R81.2, R83.1
unnamed: IC10.13 (-IN), R50.1, R53.2
unnamed: R67.2, R73.1S
unnamed: R63.1S, R66.1
unnamed: IC12.2 (-IN), R76.2, R79.1
unnamed: IC12.1 (OUT), R75.2, R76.1
unnamed: IC10.3 (+IN), R67.1, R70.1
unnamed: IC12.13 (-IN), IC12.14 (OUT)
unnamed: Q12.1 (S), R55.1, R62.2
unnamed: D16.C, IC12.6 (-IN), R74.1
unnamed: IC12.5 (+IN), R75.1, R77.2
unnamed: R52.1, R63.2S
unnamed: IC12.9 (-IN), R80.1
unnamed: IC12.10 (+IN), R81.1, R84.2
unnamed: Q13.1 (S), R58.1, R61.1
unnamed: C43.1, R77.1
unnamed: C44.1, R84.1
unnamed: D16.A, R68.1
POST_OUT-: D15.A, Q11.MB (D), Q12.MB (D), Q13.MB (D)
PREG_OUT-: D15.C, R73.1
V+: C36.1, C37.1, C38.1, C39.2, IC10.4 (V+), IC11.8 (V+), IC12.11 (V-), IC13.14 (VDD), R47.1, R48.1, R49.1
V-: C40.1, C41.1, C42.1, IC10.11 (V-), IC11.4 (V-), IC12.4 (V+)

Notes on the sheet:
Licensed under the TAPR Open Hardware License (www.tapr.org/OHL)
Repository: https://github.com/eez-open
More info at http://www.envox.hr/eez
50mA/500mA/5A current autoranging
Not used

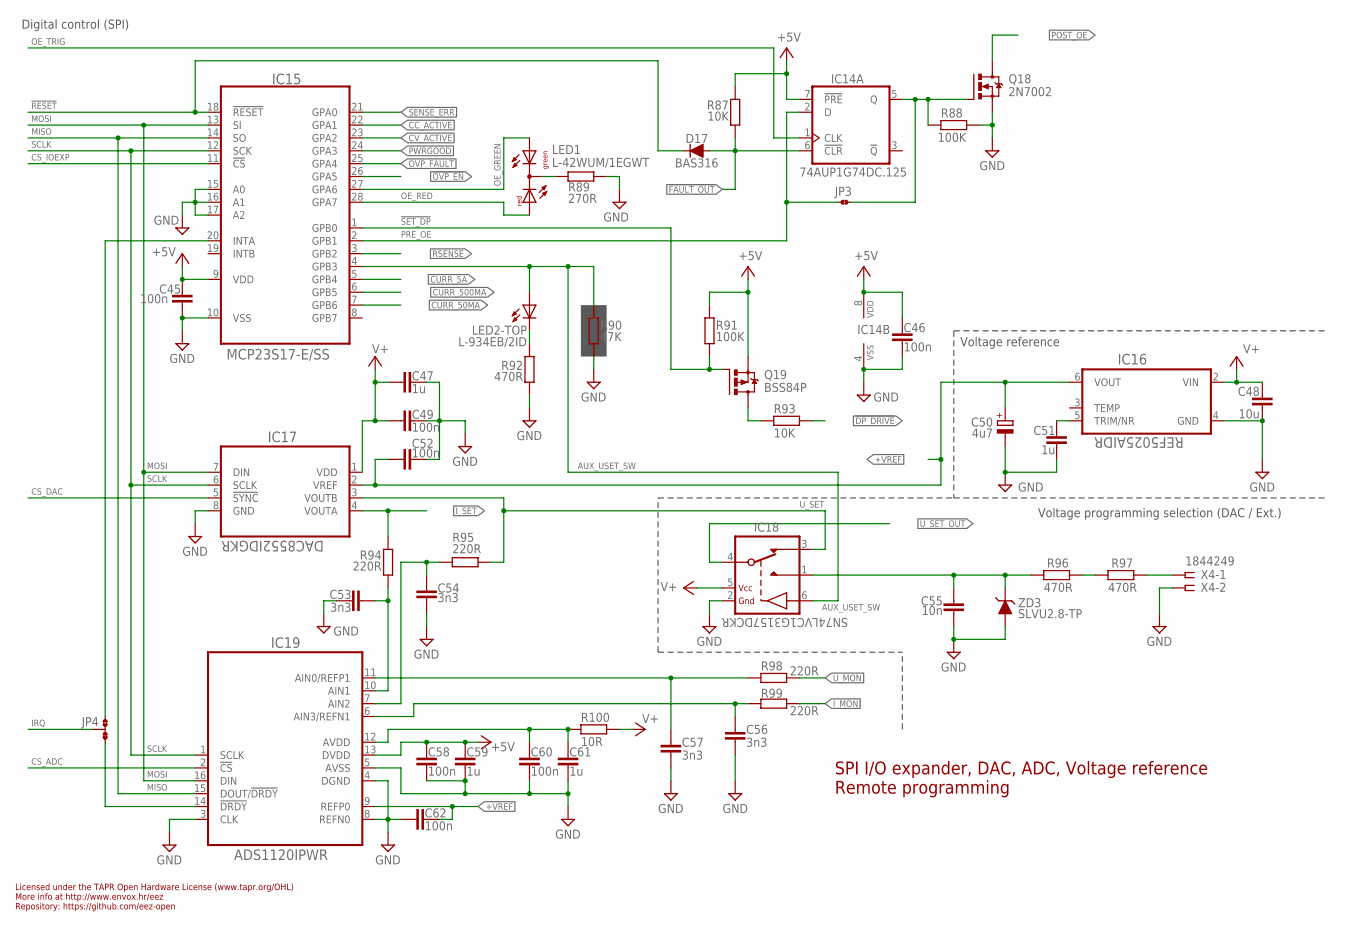
[picture p636: schematic EEZ DIB DCP505 r1B2.sch, sheet 4]

Parts:
C45, C46, C49, C52, C58, C60, C62: 100n; C0603
C47, C51, C59, C61: 1u; C0805
C48: 10u; C1206
C50: 4u7; EC1206
C53, C54, C56, C57: 3n3; C0805
C55: 10n; C0805
D17: BAS316; SOD323-R
IC14: 74AUP1G74DC.125; DCU8
IC15: MCP23S17-E/SS; SOP65P780X200-28N
IC16: REF5025AIDR; SOIC127P600X175-8N
IC17: DAC8552IDGKR; DGK8-M
IC18: SN74LVC1G3157DCKR; SOT65P210X110-6N
IC19: ADS1120IPWR; PW(R-PDSO-G16)
JP3: JP2-CUT
JP4: JP3-CUT
LED1: L-42WUM/1EGWT; L-42WUM-1EGWT
LED2: L-934EB/2ID; L-934EB
Q18: 2N7002; SOT103P240X110-3N; MPN 2N7002-7-F
Q19: BSS84P; SOT95P237X112-3N
R87, R93: 10K; R0805
R88, R91: 100K; R0805
R89: 270R; R0805
R90: 47K; R0805
R92, R96, R97: 470R; R0805
R94, R95, R98, R99: 220R; R0805
R100: 10R; R0805
X4: 1844249; MC1,5/5-G-3,5
ZD3: SLVU2.8-TP; SOT23

Connections:
!DP_DRIVE: R93.1
!DRDY: IC19.14 (!DRDY), JP4.NC
!FAULT_OUT: D17.A, IC14.6 (!CLR), R87.2
!OVP_EN: IC15.26 (GPA5)
!RESET: D17.C, IC15.18 (!RESET)
!SET_DP: IC15.1 (GPB0), Q19.1 (G), R91.2
+5V: C45.1, C46.2, C58.2, C59.2, IC14.7 (!PRE), IC14.8 (VDD), IC15.9 (VDD), IC19.13 (DVDD), Q19.2 (S), R87.1, R91.1
+VREF: C50.+, C52.2, C62.2, IC16.6 (VOUT), IC17.2 (VREF), IC19.9 (REFP0)
AUX_IN: C55.2, IC18.1 (NO), R96.1, ZD3.3 (C)
AUX_USET_SW: IC15.4 (GPB3), IC18.6 (CTRL), LED2.TA (A), R90.2
CC_ACTIVE: IC15.22 (GPA1)
CS_ADC: IC19.2 (!CS)
CS_DAC: IC17.5 (!SYNC)
CS_IOEXP: IC15.11 (!CS)
CURR_5A: IC15.5 (GPB4)
CURR_50MA: IC15.7 (GPB6)
CURR_500MA: IC15.6 (GPB5)
CV_ACTIVE: IC15.23 (GPA2)
DP_LED: Q19.3 (D), R93.2
GND: C45.2, C46.1, C47.2, C48.2, C49.1, C50.-, C51.2, C52.1, C53.1, C54.1, C55.1, C56.2, C57.1, C58.1, C59.1, C60.1, C61.1, C62.1, IC14.4 (VSS), IC15.10 (VSS), IC15.15 (A0), IC15.16 (A1), IC15.17 (A2), IC16.4 (GND), IC17.8 (GND), IC18.2 (GND), IC19.3 (CLK), IC19.4 (DGND), IC19.5 (AVSS), IC19.8 (REFN0), Q18.2 (S), R88.1, R89.2, R90.1, R92.1, X4.2, ZD3.1 (A)
IRQ: JP4.COM
I_MON: R99.1
I_SET: IC17.4 (VOUTA), R94.1
MISO: IC15.14 (SO), IC19.15 (DOUT/!DRDY)
MOSI: IC15.13 (SI), IC17.7 (DIN), IC19.16 (DIN)
unnamed: IC15.20 (INTA), JP4.NO
unnamed: LED1.CC (C), R89.1
unnamed: R96.2, R97.1
unnamed: R97.2, X4.1
unnamed: IC14.5 (Q), JP3.2, Q18.1 (G), R88.2
unnamed: C60.2, C61.2, IC19.12 (AVDD), R100.2
unnamed: C51.1, IC16.5 (TRIM/NR)
unnamed: C53.2, IC19.10 (AIN1), R94.2
unnamed: C57.2, IC19.11 (AIN0/REFP1), R98.2
unnamed: C54.2, IC19.7 (AIN2), R95.2
unnamed: C56.1, IC19.6 (AIN3/REFN1), R99.2
unnamed: LED2.TC (C), R92.2
OE_GREEN: IC15.27 (GPA6), LED1.GREEN (AG)
OE_RED: IC15.28 (GPA7), LED1.RED (AR)
OE_TRIG: IC14.1 (CLK)
OVP_FAULT: IC15.25 (GPA4)
POST_OE: Q18.3 (D)
PRE_OE: IC14.2 (D), IC15.2 (GPB1), JP3.1
PWRGOOD: IC15.24 (GPA3)
RSENSE: IC15.3 (GPB2)
SCLK: IC15.12 (SCK), IC17.6 (SCLK), IC19.1 (SCLK)
SENSE_ERR: IC15.21 (GPA0)
U_MON: R98.1
U_SET: IC17.3 (VOUTB), IC18.3 (NC), R95.1
U_SET_OUT: IC18.4 (COM)
V+: C47.1, C48.1, C49.2, IC16.2 (VIN), IC17.1 (VDD), IC18.5 (VDD), R100.1

Notes on the sheet:
SPI I/O expander, DAC, ADC, Voltage reference
Digital control (SPI)
Voltage reference
Licensed under the TAPR Open Hardware License (www.tapr.org/OHL)
Repository: https://github.com/eez-open
More info at http://www.envox.hr/eez
Remote programming
Voltage programming selection (DAC / Ext.)

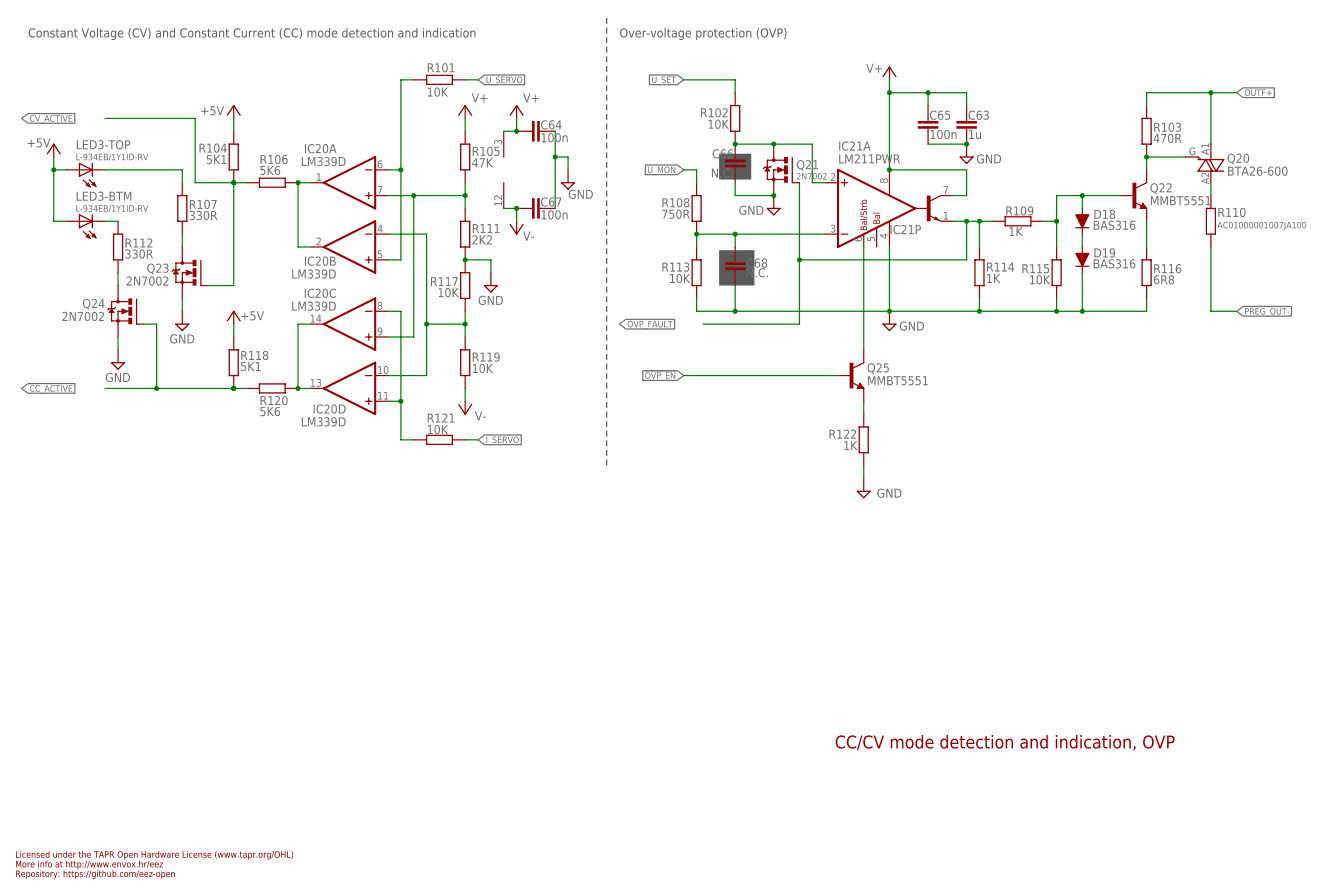
[picture p637: schematic EEZ DIB DCP505 r1B2.sch, sheet 5]

Parts:
C63: 1u; C0805
C64, C65, C67: 100n; C0603
C66, C68: N.C.; C0805
D18, D19: BAS316; SOD323-R
IC20: LM339D; SOIC127P600X175-14N
IC21: LM211PWR; PW8_TSSOP8
LED3: L-934EB/1Y1ID-RV; L-934EB
Q20: BTA26-600; TOP3_TRIAC_NOHOLE
Q21: 2N7002; SOT103P240X110-3N; MPN 2N7002-7-F
Q22, Q25: MMBT5551; SOT23-BEC
Q23, Q24: 2N7002; SOT103P240X110-3N
R101, R102, R113, R115, R117, R119, R121: 10K; R0805
R103: 470R; R0805
R104, R118: 5K1; R0805
R105: 47K; R0805
R106, R120: 5K6; R0805
R107, R112: 330R; R0805
R108: 750R; R0805
R109, R114, R122: 1K; R0805
R110: AC01000001007JA100; 0411/15
R111: 2K2; R0805
R116: 6R8; R0805

Connections:
!OVP_EN: Q25.B
+5V: LED3.BA (A), LED3.TA (A), R104.2, R118.2
CC_ACTIVE: Q24.1 (G), R118.1, R120.2
CC_LED: LED3.BC (C), R112.2
CV_ACTIVE: Q23.1 (G), R104.1, R106.2
CV_LED: LED3.TC (C), R107.1
GND: C63.2, C64.1, C65.1, C66.1, C67.1, C68.1, D19.C, IC21.4 (V-), Q21.2 (S), Q23.2 (S), Q24.2 (S), R111.1, R113.2, R114.2, R115.1, R116.1, R117.2, R122.2
I_SERVO: R121.1
unnamed: Q20.A2, R110.2
unnamed: Q20.G, Q22.C, R103.1
unnamed: Q22.E, R116.2
unnamed: D18.C, D19.A
unnamed: D18.A, Q22.B, R109.1, R115.2
unnamed: IC21.6 (BAL/STRB), Q25.C
unnamed: Q25.E, R122.1
unnamed: C66.2, IC21.2 (+IN), Q21.3 (D), R102.2
unnamed: C68.2, IC21.3 (-IN), R108.2, R113.1
unnamed: Q24.3 (D), R112.1
unnamed: IC20.1 (OUT), IC20.2 (OUT), R106.1
unnamed: IC20.13 (OUT), IC20.14 (OUT), R120.1
unnamed: Q23.3 (D), R107.2
unnamed: IC20.5 (+IN), IC20.6 (-IN), R101.2
unnamed: IC20.8 (-IN), IC20.11 (+IN), R121.2
unnamed: IC20.7 (+IN), IC20.9 (+IN), R105.1, R111.2
unnamed: IC20.4 (-IN), IC20.10 (-IN), R117.1, R119.2
OUTF+: Q20.A1, R103.2
OVP_FAULT: IC21.1 (E), Q21.1 (G), R109.2, R114.1
PREG_OUT-: R110.1
U_MON: R108.1
U_SERVO: R101.1
U_SET: R102.1
V+: C63.1, C64.2, C65.2, IC20.3 (V+), IC21.7 (C), IC21.8 (V+), R105.2
V-: C67.2, IC20.12 (GND), R119.1

Notes on the sheet:
Licensed under the TAPR Open Hardware License (www.tapr.org/OHL)
Repository: https://github.com/eez-open
More info at http://www.envox.hr/eez
CC/CV mode detection and indication, OVP
Constant Voltage (CV) and Constant Current (CC) mode detection and indication
Over-voltage protection (OVP)

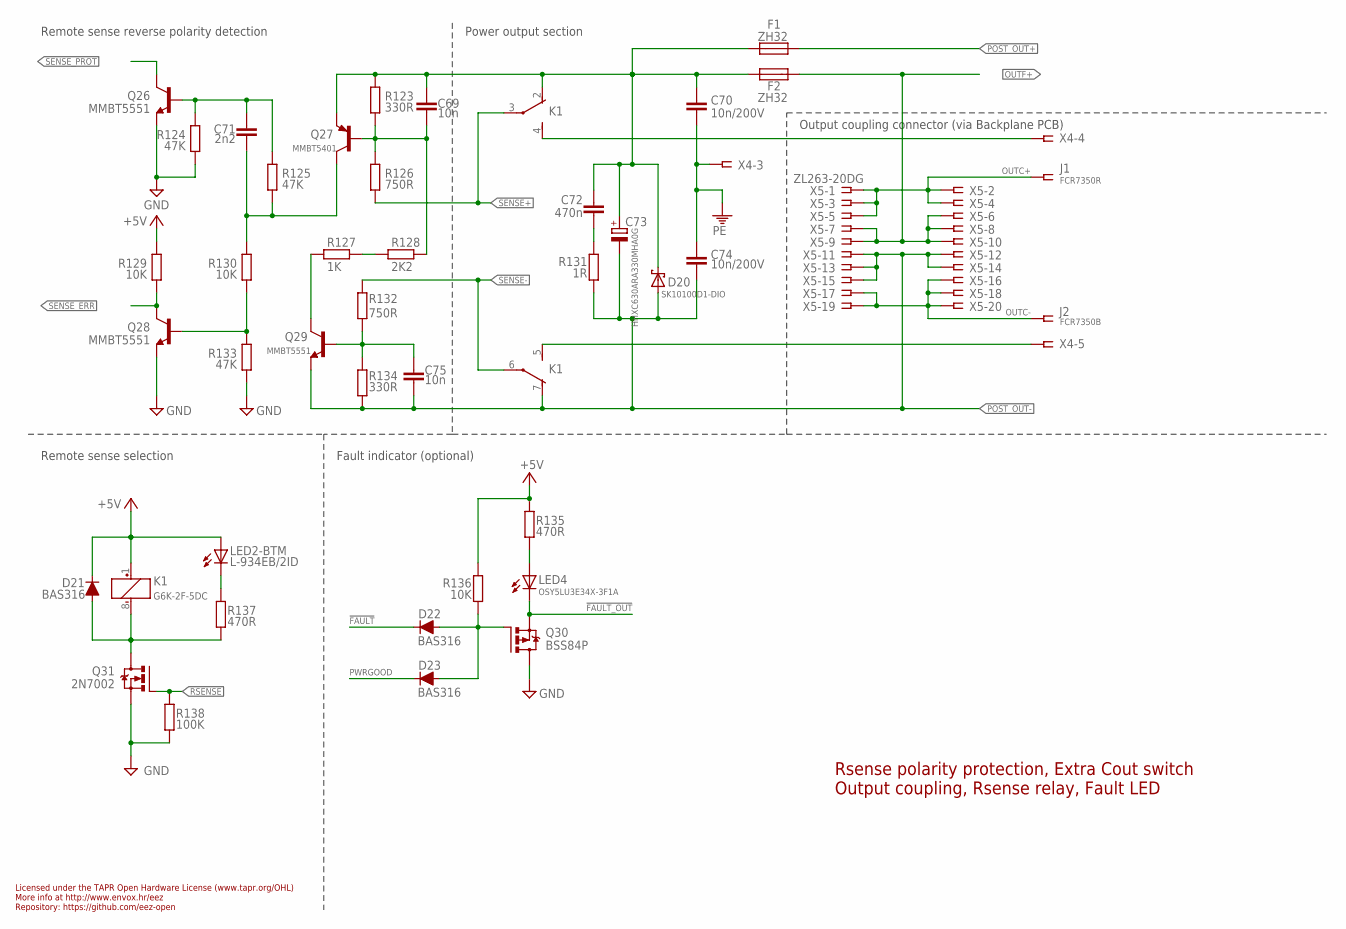
[picture p638: schematic EEZ DIB DCP505 r1B2.sch, sheet 6]

Parts:
C69, C75: 10n; C0805
C70, C74: 10n/200V; C1206
C71: 2n2; C0805
C72: 470n; C1206
C73: HHXC630ARA330MHA0G; CAPAE830X1050N
D20: SK10100D1-DIO; TO252-L
D21, D22, D23: BAS316; SOD323-R
F1, F2: ZH32
J1: FCR7350R; S16N-PC
J2: FCR7350B; S16N-PC
K1: G6K-2F-5DC; G6K-2F; MPN G6K-2F DC24
LED2: L-934EB/2ID; L-934EB
LED4: OSY5LU3E34X-3F1A; OSG8
Q26, Q28, Q29: MMBT5551; SOT23-BEC
Q27: MMBT5401; SOT23-BEC
Q30: BSS84P; SOT95P237X112-3N
Q31: 2N7002; SOT103P240X110-3N; MPN 2N7002-7-F
R123, R134: 330R; R0805
R124, R125, R133: 47K; R0805
R126, R132: 750R; R0805
R127: 1K; R0805
R128: 2K2; R0805
R129, R130, R136: 10K; R0805
R131: 1R; R0805
R135, R137: 470R; R0805
R138: 100K; R0805
X4: 1844249; MC1,5/5-G-3,5
X5: ZL263-20DG; SSW-110-02-T-D-RA

Connections:
!FAULT: D22.C
!FAULT_OUT: LED4.C, Q30.2 (S)
+5V: D21.C, K1.1 (+), LED2.BA (A), R129.2, R135.2, R136.1
GND: Q26.E, Q28.E, Q30.3 (D), Q31.2 (S), R124.1, R133.1, R138.1
unnamed: C69.1, C70.1, C72.1, C73.+, D20.3 (C), F1.2, F2.1, K1.2 (O), Q27.E, R123.2
unnamed: D22.A, D23.A, Q30.1 (G), R136.2
unnamed: LED4.A, R135.1
unnamed: C69.2, Q27.B, R123.1, R126.2, R128.2
unnamed: C71.2, Q27.C, R125.1, R130.2
unnamed: Q29.C, R127.1
unnamed: C75.1, Q29.B, R132.1, R134.2
unnamed: C71.1, Q26.B, R124.2, R125.2
unnamed: Q28.B, R130.1, R133.2
unnamed: C72.2, R131.2
unnamed: D21.A, K1.8 (-), Q31.3 (D), R137.1
unnamed: K1.4 (S), X4.4
unnamed: K1.5 (S), X4.5
unnamed: LED2.BC (C), R137.2
unnamed: R127.2, R128.1
OUTC+: J1.1, X5.1, X5.2, X5.3, X5.4, X5.5
OUTC-: J2.1, X5.16, X5.17, X5.18, X5.19, X5.20
OUTF+: F2.2, X5.6, X5.7, X5.8, X5.9, X5.10
PE: C70.2, C74.1, X4.3
POST_OUT+: F1.1
POST_OUT-: C73.-, C74.2, C75.2, D20.1 (A), K1.7 (O), Q29.E, R131.1, R134.1, X5.11, X5.12, X5.13, X5.14, X5.15
PWRGOOD: D23.C
RSENSE: Q31.1 (G), R138.2
SENSE+: K1.3, R126.1
SENSE-: K1.6, R132.2
SENSE_ERR: Q28.C, R129.1
SENSE_PROT: Q26.C

Notes on the sheet:
Rsense polarity protection, Extra Cout switch
Licensed under the TAPR Open Hardware License (www.tapr.org/OHL)
Repository: https://github.com/eez-open
More info at http://www.envox.hr/eez
Remote sense reverse polarity detection
Remote sense selection
Output coupling, Rsense relay, Fault LED
Fault indicator (optional)
Output coupling connector (via Backplane PCB)
Power output section
