eez-open/modular-psu/dcp505/Eagle files/EEZ DIB DCP505 r1B3.sch

## EAGLE design dcp505/Eagle files/EEZ DIB DCP505 r1B3.sch (2019-01-23)

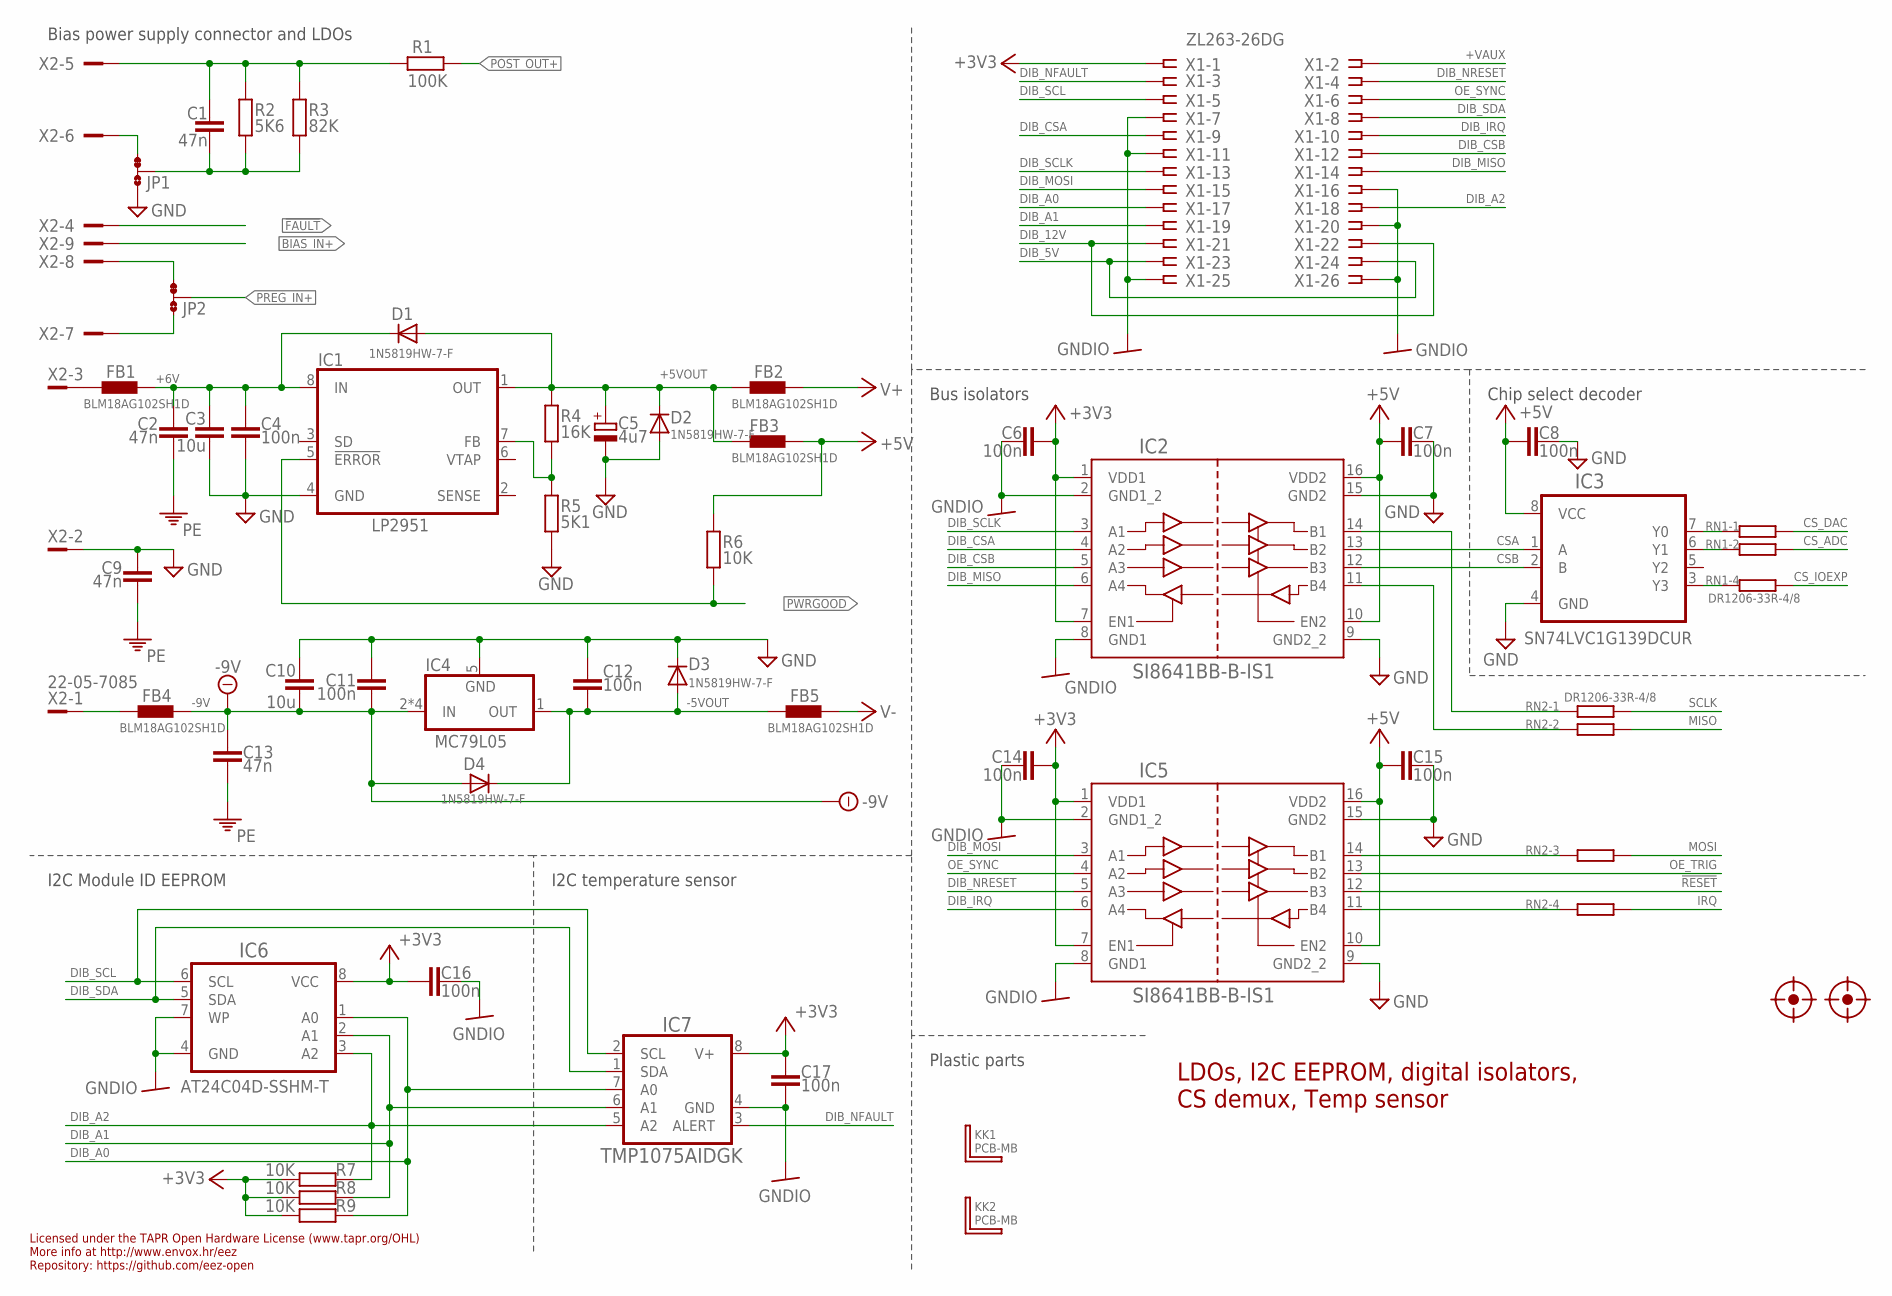
[picture p639: schematic EEZ DIB DCP505 r1B3.sch, sheet 1]

Parts:
C1: 47n; C0805
C2, C9, C13: 47n; C1206
C3, C10: 10u; C1206
C4, C6, C7, C8, C11, C12, C14, C15, C16, C17: 100n; C0603
C5: 4u7; EC1206
D1, D2, D3, D4: 1N5819HW-7-F; SOD323-W
FB1, FB2, FB3, FB4, FB5: BLM18AG102SH1D; BEAD0603
FM1, FM2: FIDUCIAL_2; FIDUCIAL_DUAL
IC1: LP2951; SOIC127P600X175-8N
IC2, IC5: SI8641BB-B-IS1; SOIC-16
IC3: SN74LVC1G139DCUR; DCU8
IC4: MC79L05; SOIC127P600X173-8N
IC6: AT24C04D-SSHM-T; SOIC127P600X173-8N
IC7: TMP1075AIDGK; DGK8
JP1, JP2: JP3-CUT
KK1, KK2: PCB-MB
R1: 100K; R0805
R2: 5K6; R0805
R3: 82K; R0805
R4: 16K; R0805
R5: 5K1; R0805
R6, R7, R8, R9: 10K; R0805
RN1, RN2: DR1206-33R-4/8; CAY16
X1: ZL263-26DG; SSW-113-02-T-D-RA
X2: 22-05-7085; SPOX_22-05-7095

Connections:
!FAULT: X2.4
!RESET: IC5.12 (B3)
+3V3: C6.1, C14.1, C16.2, C17.1, IC2.1 (VDD1), IC2.7 (EN1), IC5.1 (VDD1), IC5.7 (EN1), IC6.8 (VCC), IC7.8 (V+), R7.1, R8.1, R9.1, X1.1
+5V: C7.2, C8.1, C15.2, FB3.P$2 (2), IC2.10 (EN2), IC2.16 (VDD2), IC3.8 (VCC), IC5.10 (EN2), IC5.16 (VDD2), R6.1
+5VOUT: C5.+, D1.A, D2.C, FB2.P$1 (1), FB3.P$1 (1), IC1.1 (OUT), R4.1
+6V: C2.1, C3.1, C4.1, D1.C, FB1.P$2 (2), IC1.8 (IN)
+VAUX: X1.2
-5VOUT: C12.2, D3.A, D4.C, FB5.P$1 (1), IC4.1 (OUT)
-9V: C10.2, C11.2, C13.1, D4.A, FB4.P$2 (2), IC4.2 (IN)
BIAS_IN+: X2.9
CSA: IC2.13 (B2), IC3.1 (A)
CSB: IC2.12 (B3), IC3.2 (B)
CS_ADC: RN1.7 (2)
CS_DAC: RN1.8 (2)
CS_IOEXP: RN1.5 (2)
DIB_5V: X1.23, X1.24
DIB_12V: X1.21, X1.22
DIB_A0: IC6.1 (A0), IC7.7 (A0), R9.2, X1.17
DIB_A1: IC6.2 (A1), IC7.6 (A1), R8.2, X1.19
DIB_A2: IC6.3 (A2), IC7.5 (A2), R7.2, X1.18
DIB_CSA: IC2.4 (A2), X1.9
DIB_CSB: IC2.5 (A3), X1.12
DIB_IRQ: IC5.6 (A4), X1.10
DIB_MISO: IC2.6 (A4), X1.14
DIB_MOSI: IC5.3 (A1), X1.15
DIB_NFAULT: IC7.3 (ALERT), X1.3
DIB_NRESET: IC5.5 (A3), X1.4
DIB_SCL: IC6.6 (SCL), IC7.2 (SCL), X1.5
DIB_SCLK: IC2.3 (A1), X1.13
DIB_SDA: IC6.5 (SDA), IC7.1 (SDA), X1.8
GND: C3.2, C4.2, C5.-, C7.1, C8.2, C9.1, C10.1, C11.1, C12.1, C15.1, D2.A, D3.C, IC1.4 (GND), IC2.9 (GND2_2), IC2.15 (GND2), IC3.4 (GND), IC4.5 (GND), IC5.9 (GND2_2), IC5.15 (GND2), JP1.NO, R5.2, X2.2
GNDIO: C6.2, C14.2, C16.1, C17.2, IC2.2 (GND1_2), IC2.8 (GND1), IC5.2 (GND1_2), IC5.8 (GND1), IC6.4 (GND), IC6.7 (WP), IC7.4 (GND), X1.7, X1.11, X1.16, X1.20, X1.25, X1.26
IRQ: RN2.5 (2)
MISO: RN2.7 (2)
MOSI: RN2.6 (2)
unnamed: FB1.P$1 (1), X2.3
unnamed: FB4.P$1 (1), X2.1
unnamed: IC3.7 (Y0), RN1.1
unnamed: IC2.11 (B4), RN2.2 (1)
unnamed: IC5.11 (B4), RN2.4 (1)
unnamed: C1.2, JP1.COM, R2.2, R3.2
unnamed: IC3.6 (Y1), RN1.2 (1)
unnamed: IC3.3 (Y3), RN1.4 (1)
unnamed: IC5.14 (B1), RN2.3 (1)
unnamed: JP2.NO, X2.7
unnamed: JP2.NC, X2.8
unnamed: IC1.7 (FB), R4.2, R5.1
unnamed: IC2.14 (B1), RN2.1
OE_SYNC: IC5.4 (A2), X1.6
OE_TRIG: IC5.13 (B2)
PE: C2.2, C9.2, C13.2
POST_OUT+: R1.1
PREG_IN+: JP2.COM
PWRGOOD: IC1.5 (!ERROR), R6.2
SCLK: RN2.8 (2)
U_CTRL+: C1.1, R1.2, R2.1, R3.1, X2.5
U_CTRL-: JP1.NC, X2.6
V+: FB2.P$2 (2)
V-: FB5.P$2 (2)

Notes on the sheet:
Licensed under the TAPR Open Hardware License (www.tapr.org/OHL)
Repository: https://github.com/eez-open
More info at http://www.envox.hr/eez
I2C Module ID EEPROM
Bus isolators
LDOs, I2C EEPROM, digital isolators,
Plastic parts
Chip select decoder
Bias power supply connector and LDOs
I2C temperature sensor
CS demux, Temp sensor
