eez-open/modular-psu/dcp505/Eagle files/EEZ DIB DCP505 r1B3.sch

## EAGLE design dcp505/Eagle files/EEZ DIB DCP505 r1B3.sch (continued)

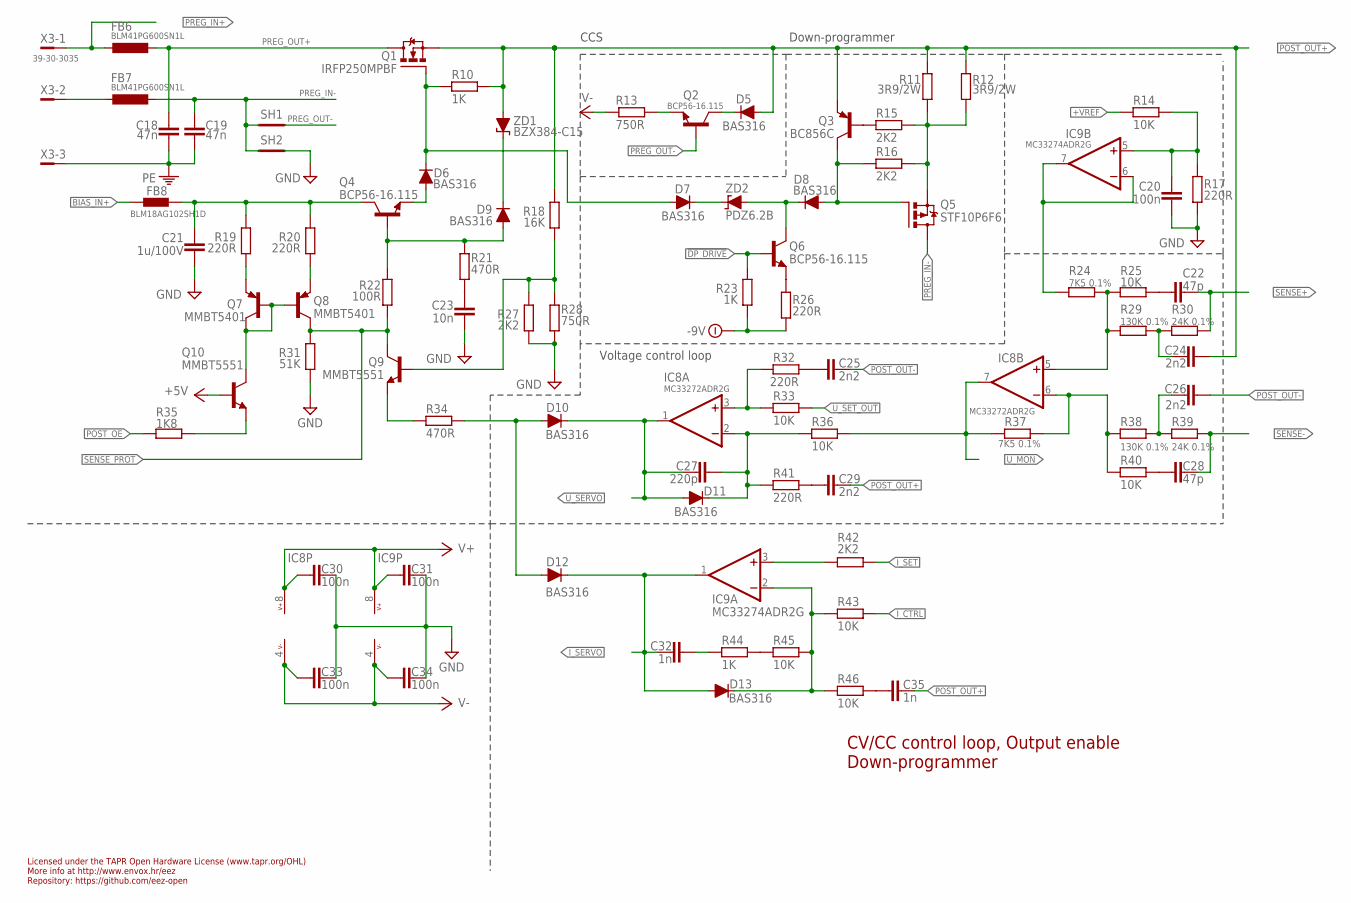
[picture p640: schematic EEZ DIB DCP505 r1B3.sch, sheet 2]

Parts:
C18, C19: 47n; C1206
C20, C30, C31, C33, C34: 100n; C0603
C21: 1u/100V; C1206
C22, C28: 47p; C0805
C23: 10n; C0805
C24, C25, C26, C29: 2n2; C0805
C27: 220p; C0805
C32, C35: 1n; C0805
D5, D6, D7, D8, D9, D10, D11, D12, D13: BAS316; SOD323-R
FB6, FB7: BLM41PG600SN1L; L1812
FB8: BLM18AG102SH1D; BEAD0603
IC8: MC33272ADR2G; SOIC127P600X173-8N
IC9: MC33274ADR2G; SOIC127P600X173-8N
Q1: IRFP250MPBF; TO247BH-CLR2
Q2, Q4, Q6: BCP56-16.115; SOT230P700X180-4N
Q3: BC856C; SOT23-BEC
Q5: STF10P6F6; TO220H-CLR2
Q7, Q8: MMBT5401; SOT23-BEC
Q9, Q10: MMBT5551; SOT23-BEC
R10, R23, R44: 1K; R0805
R11, R12: 3R9/2W; R2512
R13, R28: 750R; R0805
R14, R25, R33, R36, R40, R43, R45, R46: 10K; R0805
R15, R16, R27, R42: 2K2; R0805
R17, R19, R20, R26, R32, R41: 220R; R0805
R18: 16K; R0805
R21, R34: 470R; R0805
R22: 100R; R0805
R24, R37: 7K5 0.1%; R0805
R29, R38: 130K 0.1%; R0805
R30, R39: 24K 0.1%; R0805
R31: 51K; R0805
R35: 1K8; R0805
SH1, SH2: SHORTNOHOLE; SHORT_NOHOLE
X3: 39-30-3035; MINIFIT_6659-3
ZD1: BZX384-C15; SOD323-W
ZD2: PDZ6.2B; SOD323-W

Connections:
!DP_DRIVE: Q6.1 (B), R23.1
+5V: Q10.B
+VREF: R14.1
-9V: R23.2, R26.2
BIAS_IN+: FB8.P$1 (1)
CCS_HS: D5.C, Q2.2 (C)
DC_BIAS: C21.1, FB8.P$2 (2), Q4.2 (C), R19.2, R20.2
DP_S: Q5.3 (S), R11.1, R12.1, R15.1, R16.1
GCOM: IC9.6 (-IN), IC9.7 (OUT), R24.1
GND: C20.2, C21.2, C23.2, C30.1, C31.1, C33.1, C34.1, R17.2, R27.1, R28.1, R31.1, SH2.P$2 (GND_B)
I_CTRL: R43.1
I_SERVO: C32.2, D12.C, D13.A, IC9.1 (OUT)
I_SET: R42.1
LOOP_CTRL: D10.A, D12.A, R34.1
unnamed: FB7.1, X3.2
unnamed: IC9.3 (+IN), R42.2
unnamed: IC8.3 (+IN), R32.2, R33.2
unnamed: C27.1, D11.C, IC8.2 (-IN), R36.2, R41.2
unnamed: C26.1, R38.2, R39.1
unnamed: C22.2, R25.1
unnamed: C28.2, R40.1
unnamed: C35.2, R46.1
unnamed: D13.C, IC9.2 (-IN), R43.2, R45.2, R46.2
unnamed: C25.2, R32.1
unnamed: C29.2, R41.1
unnamed: D6.C, D7.A, Q1.1 (G), R10.1
unnamed: D6.A, Q4.3 (E)
unnamed: D9.A, Q4.1 (B), R21.2, R22.1
unnamed: C23.1, R21.1
unnamed: Q9.B, R18.1, R27.2, R28.2
unnamed: Q6.3 (E), R26.1
unnamed: Q3.B, R15.2
unnamed: C20.1, IC9.5 (+IN), R14.2, R17.1
unnamed: C24.1, R29.2, R30.1
unnamed: D9.C, ZD1.C
unnamed: D7.C, ZD2.C
unnamed: Q9.E, R34.2
unnamed: D8.A, Q3.C, Q5.1 (G), R16.2
unnamed: IC8.5 (+IN), R24.2, R25.2, R29.1
unnamed: IC8.6 (-IN), R37.2, R38.1, R40.2
unnamed: R44.2, R45.1
unnamed: C32.1, R44.1
unnamed: Q2.3 (E), R13.2
unnamed: Q8.E, R20.1
unnamed: Q7.E, R19.1
unnamed: Q10.E, R35.2
PE: C18.2, C19.2, X3.3
POST_OE: R35.1
POST_OUT+: C24.2, C29.1, C35.1, D5.A, Q1.3 (S), Q3.E, R10.2, R11.2, R12.2, R18.2, ZD1.A
POST_OUT-: C25.1, C26.2
PREG_IN+: FB6.1, X3.1
PREG_IN-: C19.1, FB7.2, Q5.2 (D), SH1.P$1 (GND_A), SH2.P$1 (GND_A)
PREG_OUT+: C18.1, FB6.2, Q1.2 (D)
PREG_OUT-: Q2.1 (B), SH1.P$2 (GND_B)
Q6C: D8.C, Q6.2 (C), ZD2.A
Q7C: Q7.B, Q7.C, Q8.B, Q10.C
SENSE+: C22.1, R30.2
SENSE-: C28.1, R39.2
SENSE_PROT: Q8.C, Q9.C, R22.2, R31.2
U_MON: IC8.7 (OUT), R36.1, R37.1
U_SERVO: C27.2, D10.C, D11.A, IC8.1 (OUT)
U_SET_OUT: R33.1
V+: C30.2, C31.2, IC8.8 (V+), IC9.8 (V+)
V-: C33.2, C34.2, IC8.4 (V-), IC9.4 (V-), R13.1

Notes on the sheet:
Voltage control loop
Down-programmer
Licensed under the TAPR Open Hardware License (www.tapr.org/OHL)
Repository: https://github.com/eez-open
More info at http://www.envox.hr/eez
CCS
CV/CC control loop, Output enable

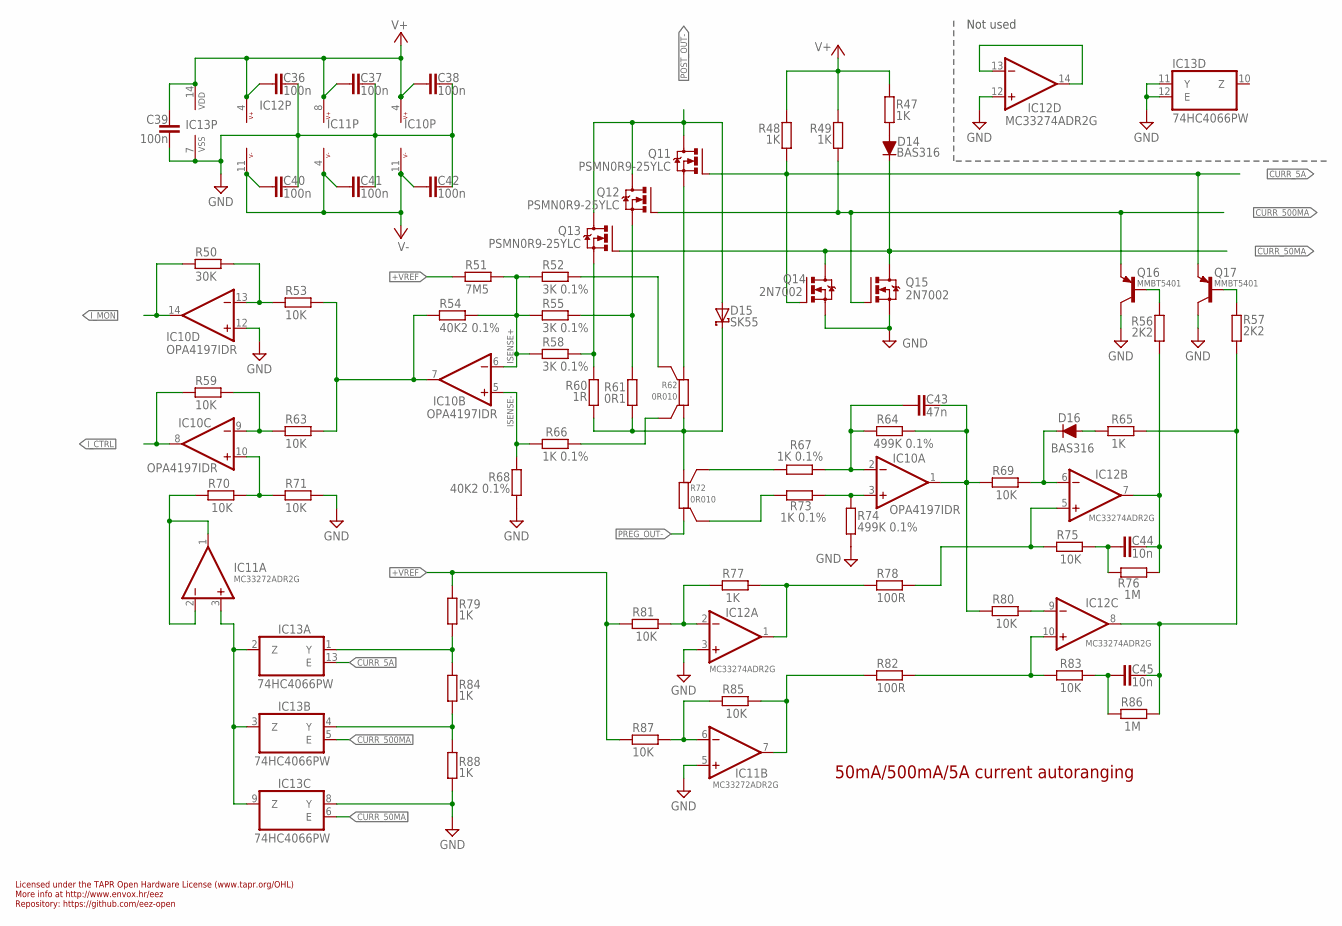
[picture p641: schematic EEZ DIB DCP505 r1B3.sch, sheet 3]

Parts:
C36, C37, C38, C39, C40, C41, C42: 100n; C0603
C43: 47n; C0805
C44, C45: 10n; C0805
D14, D16: BAS316; SOD323-R
D15: SK55; SMB
IC10: OPA4197IDR; SOIC127P600X175-14N
IC11: MC33272ADR2G; SOIC127P600X173-8N
IC12: MC33274ADR2G; SOIC127P600X175-14N
IC13: 74HC4066PW; SOP65P640X120-14N
Q11, Q12, Q13: PSMN0R9-25YLC; SOT669
Q14, Q15: 2N7002; SOT103P240X110-3N; MPN 2N7002-7-F
Q16, Q17: MMBT5401; SOT23-BEC
R47, R48, R49, R65, R77, R79, R84, R88: 1K; R0805
R50: 30K; R0805
R51: 7M5; R0603
R52, R55, R58: 3K 0.1%; R0603
R53, R59, R63, R69, R70, R71, R75, R80, R81, R83, R85, R87: 10K; R0805
R54, R68: 40K2 0.1%; R0603
R56, R57: 2K2; R0805
R60: 1R; R0805
R61: 0R1; R1206
R62, R72: 0R010; R_H2728
R64, R74: 499K 0.1%; R0603
R66, R67, R73: 1K 0.1%; R0603
R76, R86: 1M; R0805
R78, R82: 100R; R0805

Connections:
+VREF: R51.1, R79.2, R81.2, R87.2
CURR_5A: IC13.13 (E), Q11.4 (G), Q14.1 (G), Q17.E, R48.2
CURR_50MA: D14.C, IC13.6 (E), Q13.4 (G), Q14.3 (D), Q15.3 (D)
CURR_500MA: IC13.5 (E), Q12.4 (G), Q15.1 (G), Q16.E, R49.2
GND: C36.2, C37.2, C38.2, C39.1, C40.2, C41.2, C42.2, IC10.12 (+IN), IC11.5 (+IN), IC12.3 (+IN), IC12.12 (+IN), IC13.7 (VSS), IC13.8 (Y), IC13.11 (Y), IC13.12 (E), Q14.2 (S), Q15.2 (S), Q16.C, Q17.C, R68.1, R71.1, R74.2, R88.1
ISENSE+: IC10.6 (-IN), R51.2, R52.2, R54.1, R55.2, R58.2
ISENSE-: IC10.5 (+IN), R66.2, R68.2
I_CTRL: IC10.8 (OUT), R59.2
I_MON: IC10.14 (OUT), R50.2
unnamed: R67.2, R72.2S
unnamed: D15.C, R60.2, R61.1, R62.1, R72.2
unnamed: IC11.1 (OUT), IC11.2 (-IN), R70.2
unnamed: IC11.6 (-IN), R85.2, R87.1
unnamed: C43.1, IC10.2 (-IN), R64.2, R67.1
unnamed: Q11.1 (S), R62.2
unnamed: D14.A, R47.2
unnamed: C43.2, IC10.1 (OUT), R64.1, R69.2, R80.2
unnamed: IC11.3 (+IN), IC13.2 (Z), IC13.3 (Z), IC13.9 (Z)
unnamed: C44.2, IC12.7 (OUT), R56.2, R76.1
unnamed: Q16.B, R56.1
unnamed: Q17.B, R57.1
unnamed: IC10.7 (OUT), R53.1, R54.2, R63.1
unnamed: IC10.9 (-IN), R59.1, R63.2
unnamed: IC13.1 (Y), R79.1, R84.2
unnamed: C45.2, IC12.8 (OUT), R57.2, R65.2, R86.1
unnamed: IC10.10 (+IN), R70.1, R71.2
unnamed: IC13.4 (Y), R84.1, R88.2
unnamed: IC11.7 (OUT), R82.2, R85.1
unnamed: IC10.13 (-IN), R50.1, R53.2
unnamed: R72.1S, R73.2
unnamed: R62.1S, R66.1
unnamed: IC12.2 (-IN), R77.2, R81.1
unnamed: IC12.1 (OUT), R77.1, R78.2
unnamed: IC10.3 (+IN), R73.1, R74.1
unnamed: IC12.13 (-IN), IC12.14 (OUT)
unnamed: Q12.1 (S), R55.1, R61.2
unnamed: D16.C, IC12.6 (-IN), R69.1
unnamed: IC12.5 (+IN), R75.2, R78.1
unnamed: R52.1, R62.2S
unnamed: IC12.9 (-IN), R80.1
unnamed: IC12.10 (+IN), R82.1, R83.2
unnamed: Q13.1 (S), R58.1, R60.1
unnamed: C44.1, R75.1, R76.2
unnamed: C45.1, R83.1, R86.2
unnamed: D16.A, R65.1
POST_OUT-: D15.A, Q11.MB (D), Q12.MB (D), Q13.MB (D)
PREG_OUT-: R72.1
V+: C36.1, C37.1, C38.1, C39.2, IC10.4 (V+), IC11.8 (V+), IC12.4 (V+), IC13.14 (VDD), R47.1, R48.1, R49.1
V-: C40.1, C41.1, C42.1, IC10.11 (V-), IC11.4 (V-), IC12.11 (V-)

Notes on the sheet:
Licensed under the TAPR Open Hardware License (www.tapr.org/OHL)
Repository: https://github.com/eez-open
More info at http://www.envox.hr/eez
50mA/500mA/5A current autoranging
Not used

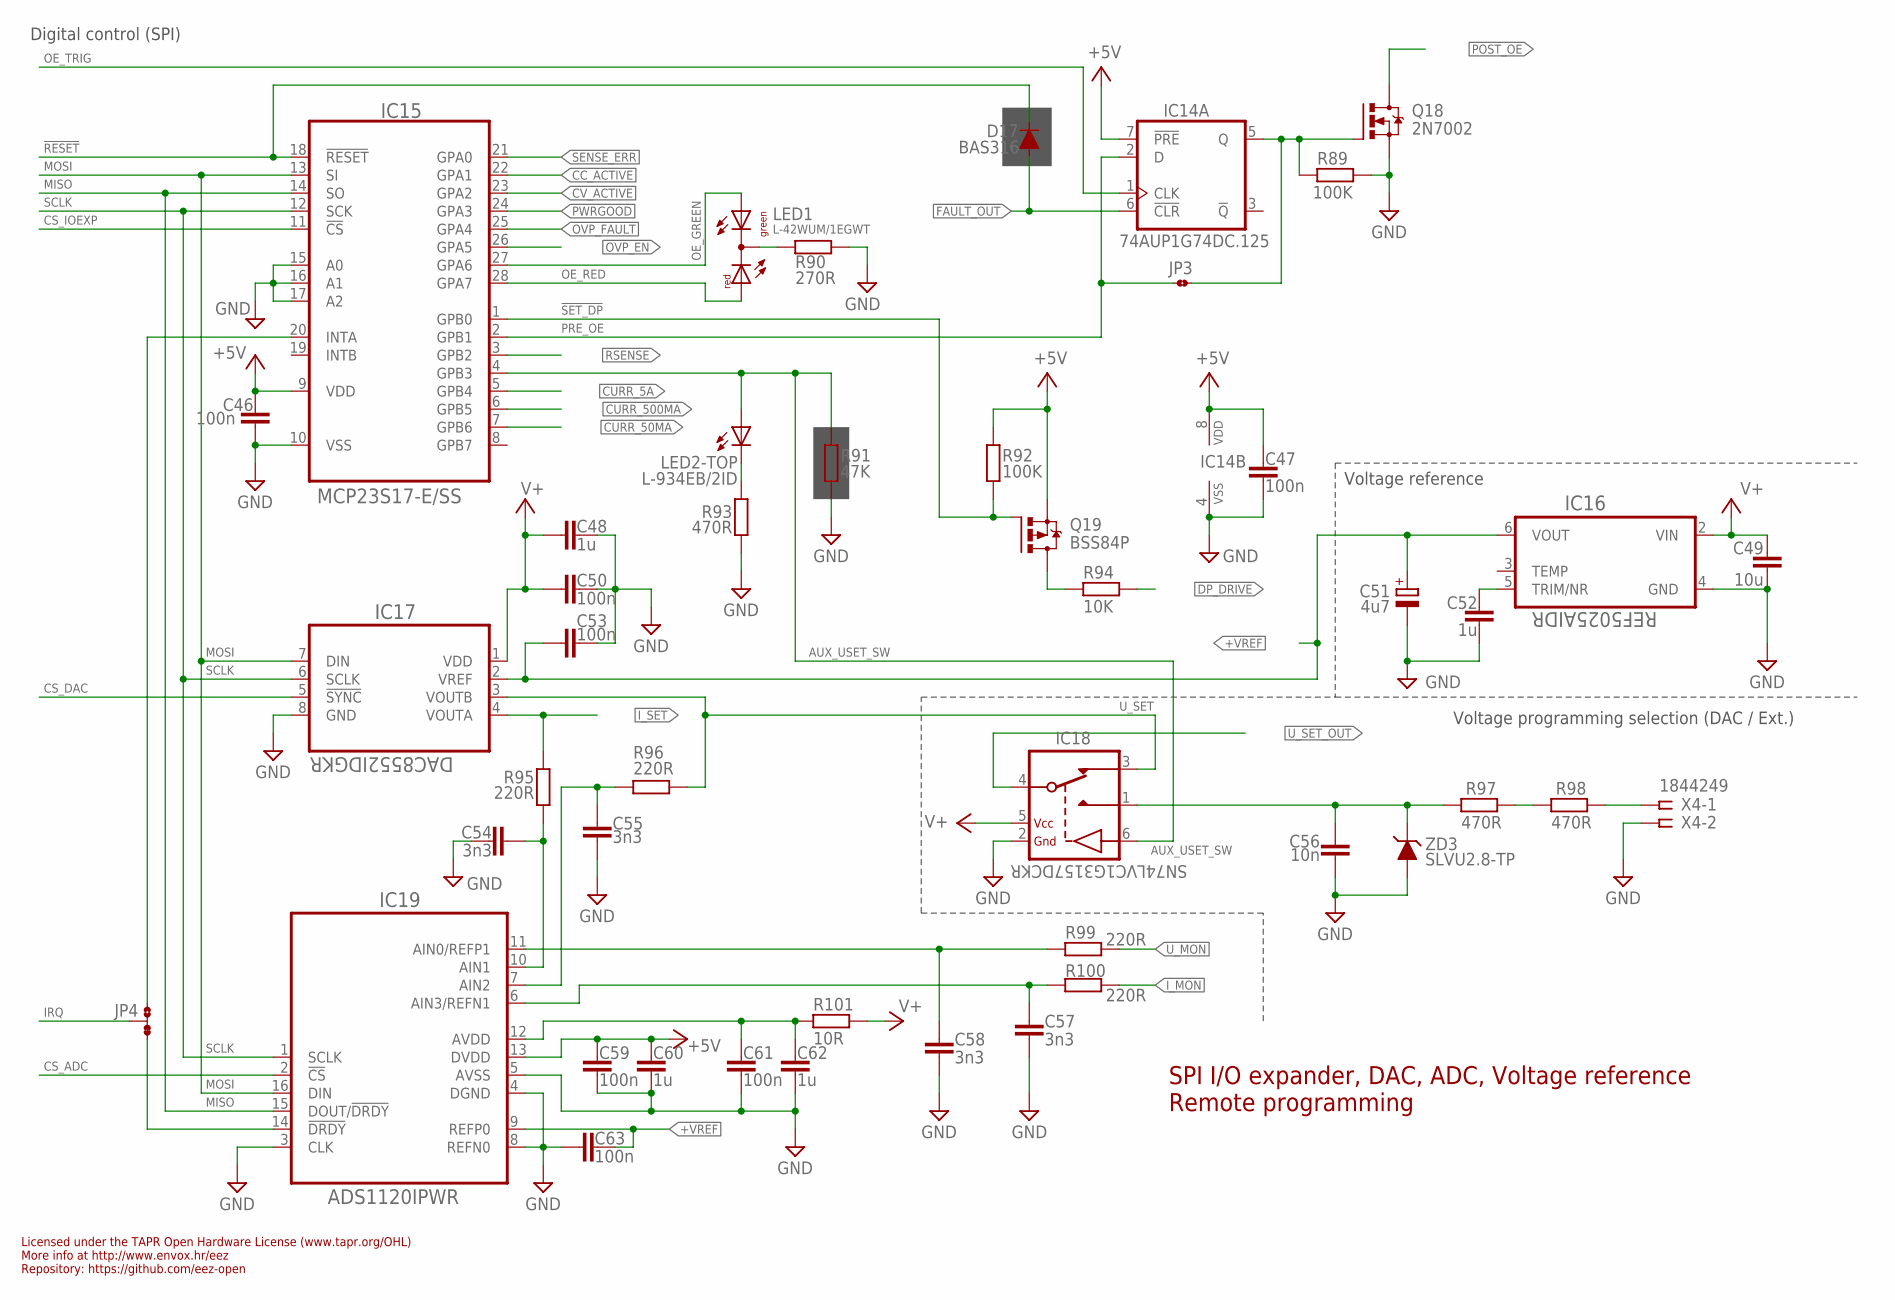
[picture p642: schematic EEZ DIB DCP505 r1B3.sch, sheet 4]

Parts:
C46, C47, C50, C53, C59, C61, C63: 100n; C0603
C48, C52, C60, C62: 1u; C0805
C49: 10u; C1206
C51: 4u7; EC1206
C54, C55, C57, C58: 3n3; C0805
C56: 10n; C0805
D17: BAS316; SOD323-R
IC14: 74AUP1G74DC.125; DCU8
IC15: MCP23S17-E/SS; SOP65P780X200-28N
IC16: REF5025AIDR; SOIC127P600X175-8N
IC17: DAC8552IDGKR; DGK8-M
IC18: SN74LVC1G3157DCKR; SOT65P210X110-6N
IC19: ADS1120IPWR; PW(R-PDSO-G16)
JP3: JP2-CUT
JP4: JP3-CUT
LED1: L-42WUM/1EGWT; L-42WUM-1EGWT
LED2: L-934EB/2ID; L-934EB
Q18: 2N7002; SOT103P240X110-3N; MPN 2N7002-7-F
Q19: BSS84P; SOT95P237X112-3N
R89, R92: 100K; R0805
R90: 270R; R0805
R91: 47K; R0805
R93, R97, R98: 470R; R0805
R94: 10K; R0805
R95, R96, R99, R100: 220R; R0805
R101: 10R; R0805
X4: 1844249; MC1,5/5-G-3,5
ZD3: SLVU2.8-TP; SOT23

Connections:
!DP_DRIVE: R94.1
!DRDY: IC19.14 (!DRDY), JP4.NC
!FAULT_OUT: D17.A, IC14.6 (!CLR)
!OVP_EN: IC15.26 (GPA5)
!OVP_FAULT: IC15.25 (GPA4)
!RESET: D17.C, IC15.18 (!RESET)
!SET_DP: IC15.1 (GPB0), Q19.1 (G), R92.2
+5V: C46.1, C47.2, C59.2, C60.2, IC14.7 (!PRE), IC14.8 (VDD), IC15.9 (VDD), IC19.13 (DVDD), Q19.2 (S), R92.1
+VREF: C51.+, C53.2, C63.2, IC16.6 (VOUT), IC17.2 (VREF), IC19.9 (REFP0)
AUX_IN: C56.2, IC18.1 (NO), R97.1, ZD3.3 (C)
AUX_USET_SW: IC15.4 (GPB3), IC18.6 (CTRL), LED2.TA (A), R91.2
CC_ACTIVE: IC15.22 (GPA1)
CS_ADC: IC19.2 (!CS)
CS_DAC: IC17.5 (!SYNC)
CS_IOEXP: IC15.11 (!CS)
CURR_5A: IC15.5 (GPB4)
CURR_50MA: IC15.7 (GPB6)
CURR_500MA: IC15.6 (GPB5)
CV_ACTIVE: IC15.23 (GPA2)
DP_LED: Q19.3 (D), R94.2
GND: C46.2, C47.1, C48.2, C49.2, C50.1, C51.-, C52.2, C53.1, C54.1, C55.1, C56.1, C57.2, C58.1, C59.1, C60.1, C61.1, C62.1, C63.1, IC14.4 (VSS), IC15.10 (VSS), IC15.15 (A0), IC15.16 (A1), IC15.17 (A2), IC16.4 (GND), IC17.8 (GND), IC18.2 (GND), IC19.3 (CLK), IC19.4 (DGND), IC19.5 (AVSS), IC19.8 (REFN0), Q18.2 (S), R89.1, R90.2, R91.1, R93.1, X4.2, ZD3.1 (A)
IRQ: JP4.COM
I_MON: R100.1
I_SET: IC17.4 (VOUTA), R95.1
MISO: IC15.14 (SO), IC19.15 (DOUT/!DRDY)
MOSI: IC15.13 (SI), IC17.7 (DIN), IC19.16 (DIN)
unnamed: IC15.20 (INTA), JP4.NO
unnamed: LED1.CC (C), R90.1
unnamed: R97.2, R98.1
unnamed: R98.2, X4.1
unnamed: IC14.5 (Q), JP3.2, Q18.1 (G), R89.2
unnamed: C61.2, C62.2, IC19.12 (AVDD), R101.2
unnamed: C52.1, IC16.5 (TRIM/NR)
unnamed: C54.2, IC19.10 (AIN1), R95.2
unnamed: C58.2, IC19.11 (AIN0/REFP1), R99.2
unnamed: C55.2, IC19.7 (AIN2), R96.2
unnamed: C57.1, IC19.6 (AIN3/REFN1), R100.2
unnamed: LED2.TC (C), R93.2
OE_GREEN: IC15.27 (GPA6), LED1.GREEN (AG)
OE_RED: IC15.28 (GPA7), LED1.RED (AR)
OE_TRIG: IC14.1 (CLK)
POST_OE: Q18.3 (D)
PRE_OE: IC14.2 (D), IC15.2 (GPB1), JP3.1
PWRGOOD: IC15.24 (GPA3)
RSENSE: IC15.3 (GPB2)
SCLK: IC15.12 (SCK), IC17.6 (SCLK), IC19.1 (SCLK)
SENSE_ERR: IC15.21 (GPA0)
U_MON: R99.1
U_SET: IC17.3 (VOUTB), IC18.3 (NC), R96.1
U_SET_OUT: IC18.4 (COM)
V+: C48.1, C49.1, C50.2, IC16.2 (VIN), IC17.1 (VDD), IC18.5 (VDD), R101.1

Notes on the sheet:
SPI I/O expander, DAC, ADC, Voltage reference
Digital control (SPI)
Voltage reference
Licensed under the TAPR Open Hardware License (www.tapr.org/OHL)
Repository: https://github.com/eez-open
More info at http://www.envox.hr/eez
Remote programming
Voltage programming selection (DAC / Ext.)

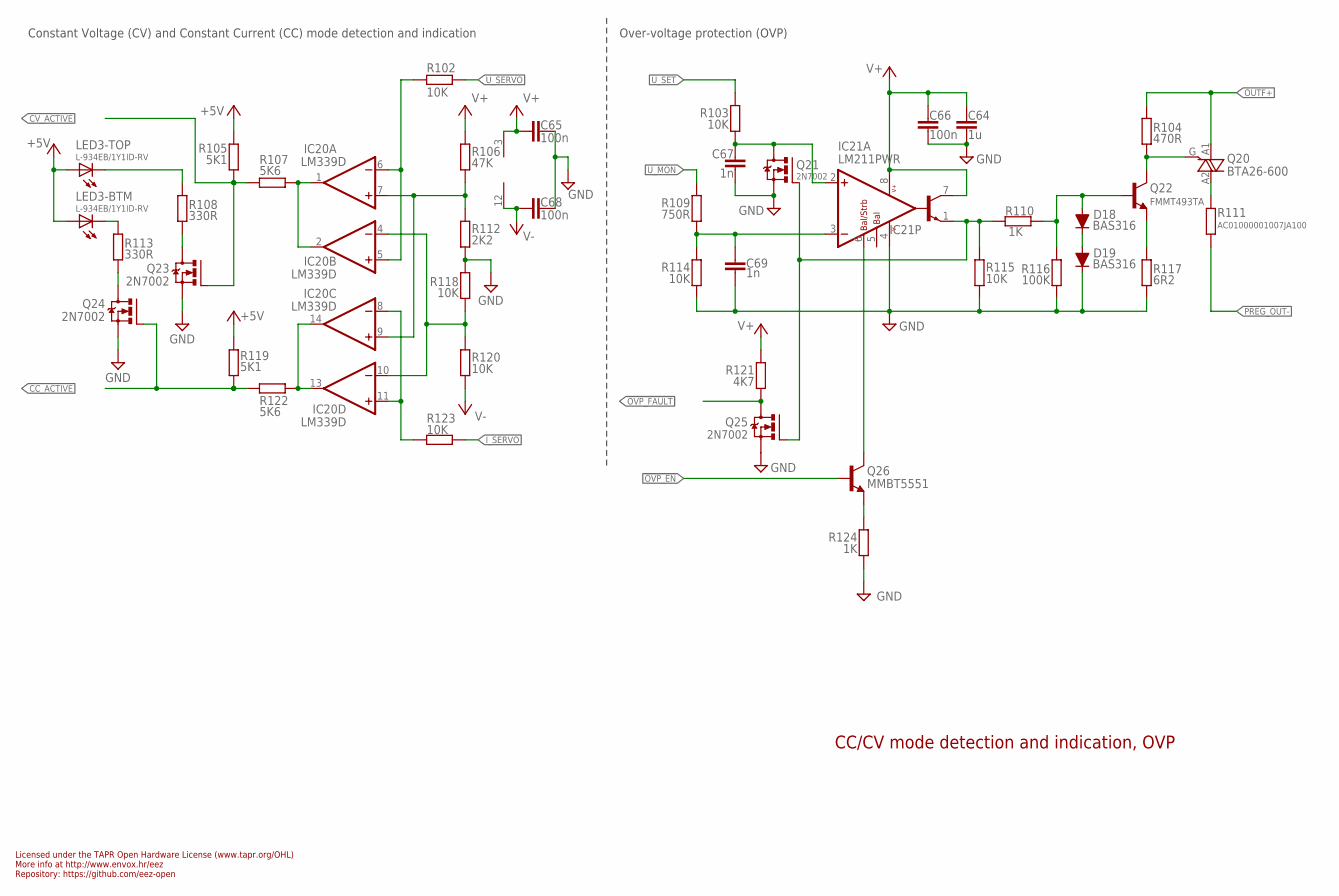
[picture p643: schematic EEZ DIB DCP505 r1B3.sch, sheet 5]

Parts:
C64: 1u; C0805
C65, C66, C68: 100n; C0603
C67, C69: 1n; C0805
D18, D19: BAS316; SOD323-R
IC20: LM339D; SOIC127P600X175-14N
IC21: LM211PWR; PW8_TSSOP8
LED3: L-934EB/1Y1ID-RV; L-934EB
Q20: BTA26-600; TOP3_TRIAC_NOHOLE
Q21: 2N7002; SOT103P240X110-3N; MPN 2N7002-7-F
Q22: FMMT493TA; SOT23-BEC
Q23, Q24, Q25: 2N7002; SOT103P240X110-3N
Q26: MMBT5551; SOT23-BEC
R102, R103, R114, R115, R118, R120, R123: 10K; R0805
R104: 470R; R0805
R105, R119: 5K1; R0805
R106: 47K; R0805
R107, R122: 5K6; R0805
R108, R113: 330R; R0805
R109: 750R; R0805
R110, R124: 1K; R0805
R111: AC01000001007JA100; 0411/15
R112: 2K2; R0805
R116: 100K; R0805
R117: 6R2; R0805
R121: 4K7; R0805

Connections:
!OVP_EN: Q26.B
!OVP_FAULT: Q25.3 (D), R121.2
+5V: LED3.BA (A), LED3.TA (A), R105.2, R119.2
CC_ACTIVE: Q24.1 (G), R119.1, R122.2
CC_LED: LED3.BC (C), R113.2
CV_ACTIVE: Q23.1 (G), R105.1, R107.2
CV_LED: LED3.TC (C), R108.1
GND: C64.2, C65.1, C66.1, C67.1, C68.1, C69.1, D19.C, IC21.4 (V-), Q21.2 (S), Q23.2 (S), Q24.2 (S), Q25.2 (S), R112.1, R114.2, R115.2, R116.1, R117.1, R118.2, R124.2
I_SERVO: R123.1
unnamed: Q20.A2, R111.2
unnamed: Q20.G, Q22.C, R104.1
unnamed: Q22.E, R117.2
unnamed: D18.C, D19.A
unnamed: D18.A, Q22.B, R110.1, R116.2
unnamed: IC21.6 (BAL/STRB), Q26.C
unnamed: Q26.E, R124.1
unnamed: C67.2, IC21.2 (+IN), Q21.3 (D), R103.2
unnamed: C69.2, IC21.3 (-IN), R109.2, R114.1
unnamed: Q24.3 (D), R113.1
unnamed: IC20.1 (OUT), IC20.2 (OUT), R107.1
unnamed: IC20.13 (OUT), IC20.14 (OUT), R122.1
unnamed: Q23.3 (D), R108.2
unnamed: IC20.5 (+IN), IC20.6 (-IN), R102.2
unnamed: IC20.8 (-IN), IC20.11 (+IN), R123.2
unnamed: IC20.7 (+IN), IC20.9 (+IN), R106.1, R112.2
unnamed: IC20.4 (-IN), IC20.10 (-IN), R118.1, R120.2
OUTF+: Q20.A1, R104.2
OVP_FAULT: IC21.1 (E), Q21.1 (G), Q25.1 (G), R110.2, R115.1
PREG_OUT-: R111.1
U_MON: R109.1
U_SERVO: R102.1
U_SET: R103.1
V+: C64.1, C65.2, C66.2, IC20.3 (V+), IC21.7 (C), IC21.8 (V+), R106.2, R121.1
V-: C68.2, IC20.12 (GND), R120.1

Notes on the sheet:
Licensed under the TAPR Open Hardware License (www.tapr.org/OHL)
Repository: https://github.com/eez-open
More info at http://www.envox.hr/eez
CC/CV mode detection and indication, OVP
Constant Voltage (CV) and Constant Current (CC) mode detection and indication
Over-voltage protection (OVP)

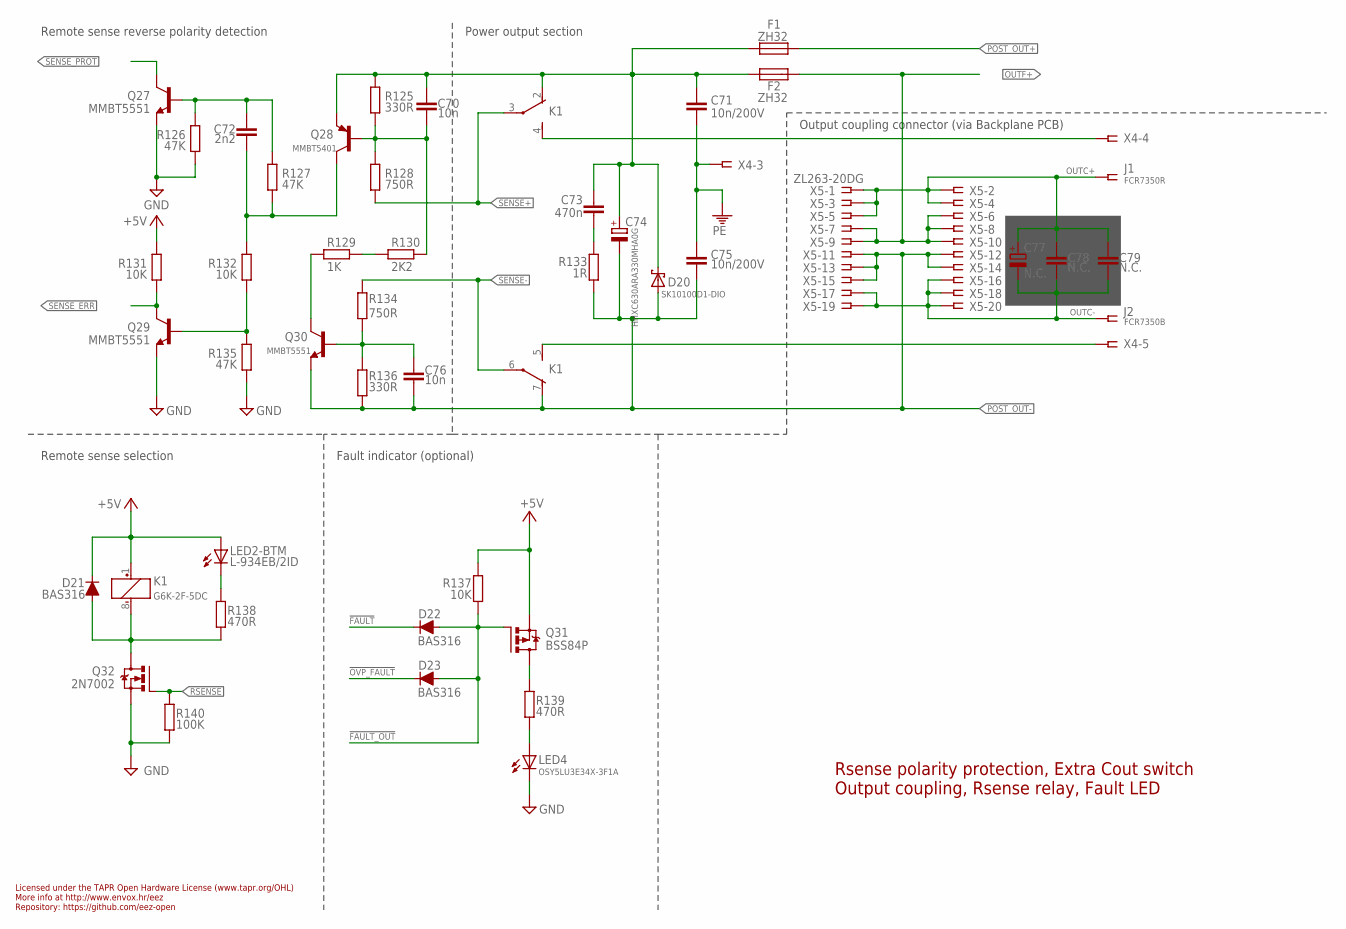
[picture p644: schematic EEZ DIB DCP505 r1B3.sch, sheet 6]

Parts:
C70, C76: 10n; C0805
C71, C75: 10n/200V; C1206
C72: 2n2; C0805
C73: 470n; C1206
C74: HHXC630ARA330MHA0G; CAPAE830X1050N
C77: N.C.; ECAP2/5
C78, C79: N.C.; C0805
D20: SK10100D1-DIO; TO252-L
D21, D22, D23: BAS316; SOD323-R
F1, F2: ZH32
J1: FCR7350R; S16N-PC
J2: FCR7350B; S16N-PC
K1: G6K-2F-5DC; G6K-2F; MPN G6K-2F DC24
LED2: L-934EB/2ID; L-934EB
LED4: OSY5LU3E34X-3F1A; OSG8
Q27, Q29, Q30: MMBT5551; SOT23-BEC
Q28: MMBT5401; SOT23-BEC
Q31: BSS84P; SOT95P237X112-3N
Q32: 2N7002; SOT103P240X110-3N; MPN 2N7002-7-F
R125, R136: 330R; R0805
R126, R127, R135: 47K; R0805
R128, R134: 750R; R0805
R129: 1K; R0805
R130: 2K2; R0805
R131, R132, R137: 10K; R0805
R133: 1R; R0805
R138, R139: 470R; R0805
R140: 100K; R0805
X4: 1844249; MC1,5/5-G-3,5
X5: ZL263-20DG; SSW-110-02-T-D-RA

Connections:
!FAULT: D22.C
!FAULT_OUT: D22.A, D23.A, Q31.1 (G), R137.2
!OVP_FAULT: D23.C
+5V: D21.C, K1.1 (+), LED2.BA (A), Q31.2 (S), R131.2, R137.1
GND: LED4.C, Q27.E, Q29.E, Q32.2 (S), R126.1, R135.1, R140.1
unnamed: C70.1, C71.1, C73.1, C74.+, D20.3 (C), F1.2, F2.1, K1.2 (O), Q28.E, R125.2
unnamed: LED4.A, R139.1
unnamed: Q31.3 (D), R139.2
unnamed: C70.2, Q28.B, R125.1, R128.2, R130.2
unnamed: C72.2, Q28.C, R127.1, R132.2
unnamed: Q30.C, R129.1
unnamed: C76.1, Q30.B, R134.1, R136.2
unnamed: C72.1, Q27.B, R126.2, R127.2
unnamed: Q29.B, R132.1, R135.2
unnamed: C73.2, R133.2
unnamed: D21.A, K1.8 (-), Q32.3 (D), R138.1
unnamed: K1.4 (S), X4.4
unnamed: K1.5 (S), X4.5
unnamed: LED2.BC (C), R138.2
unnamed: R129.2, R130.1
OUTC+: C77.+, C78.1, C79.1, J1.1, X5.1, X5.2, X5.3, X5.4, X5.5
OUTC-: C77.-, C78.2, C79.2, J2.1, X5.16, X5.17, X5.18, X5.19, X5.20
OUTF+: F2.2, X5.6, X5.7, X5.8, X5.9, X5.10
PE: C71.2, C75.1, X4.3
POST_OUT+: F1.1
POST_OUT-: C74.-, C75.2, C76.2, D20.1 (A), K1.7 (O), Q30.E, R133.1, R136.1, X5.11, X5.12, X5.13, X5.14, X5.15
RSENSE: Q32.1 (G), R140.2
SENSE+: K1.3, R128.1
SENSE-: K1.6, R134.2
SENSE_ERR: Q29.C, R131.1
SENSE_PROT: Q27.C

Notes on the sheet:
Rsense polarity protection, Extra Cout switch
Licensed under the TAPR Open Hardware License (www.tapr.org/OHL)
Repository: https://github.com/eez-open
More info at http://www.envox.hr/eez
Remote sense reverse polarity detection
Remote sense selection
Output coupling, Rsense relay, Fault LED
Fault indicator (optional)
Output coupling connector (via Backplane PCB)
Power output section
